donatukas/Volf-TRX/Schematic/Wolf/Addons/AD8307_Add_on_v3/AD8307_Add_on_v3.PcbDoc.htm

Altium Reporting Options

# File in Newer Format

Date | : | 04-Dec-20
Time | : | 18:56:06
Filename | : | C:\Tisho\MyProjects\SDR_Transciever\UA3REO-DDC\Tisho_Files\Boards\AD8307_Add_on_v2\AD8307_Add_on_v2.PcbDoc

Version | Warning
Release 10 | CAUTION - New Custom Grids and Guides were introduced. Be aware that your design might contain Custom Grids and Guides that cannot be read in previous versions.
Release 10 | CAUTION - New Structured Clusters were introduced. Be aware that your design might contain Structured Clusters that cannot be read in previous versions.
Release 10 | CAUTION - New PCB 3D Movie Manager was introduced. Be aware that your design might contain 3D PCB movie that cannot be read in previous versions.
Release 10 update 1 | CAUTION - New Clearance Rule subscopes targeting differential pairs were introduced. Be aware that your design might contain Clearance Rules using those subscopes that cannot be read in previous versions.
Release 10 update 15 | CAUTION - Support of Solder Mask and Paste Mask expansions for Tracks, Arcs, Fills and Regions was introduced. Be aware that your design might contain Solder Mask and Paste Mask expansions for these types of primitives that cannot be read in the version of Altium Designer you are currently using.
Release 12 | CAUTION - Air Gap Width previously controlled by Clearance rule is now controlled by Polygon Connect Style rule's newly introduced Air Gap Width (set to default value). Suggest reviewing each Polygon Connect Style rule's Air Gap Width attribute for correctness.
Release 13 | CAUTION - Silk To Solder Mask Clearance Rules are converted to Silkscreen Over Component Pads Rules.
Release 14 | CAUTION - The Differential Pairs Routing rule added support for control of the width. Be aware that these widths must be manually entered as Width rules in this version.
Release 15 | CAUTION - Support of separate solder masks for top & bottom of pads added.
Release 15.1 | CAUTION - Support Multi-line PCB Text added.
Release 16.0 | CAUTION - Pad/Via hole size tolerance value added.
Release 17.0 | CAUTION - Component parameters added.
Release 17.0 | CAUTION - Support of backdrilling
Release 17.1 | CAUTION - Support of waived violations
Release 17.1 | CAUTION - Support of object specific keepouts

This file was generated by a later version of the software
