donatukas/Volf-TRX/Schematic/Wolf/Altium_Designer/RF-UNIT-QRP_20W/!AdditionalInfo/Heatsink_QRP++.pptx

Used 2 heatsinks:
SK 81/100/SA (https://www.reichelt.de/kuehlkoerper-100-mm-alu-2-2-k-w-sk-81-100-sa-p227984.html?trstct=pos_0&nbc=1) – 100 x 100 mm, Alu, 2,2 K/W
SK 81/75/SA (https://www.reichelt.de/kuehlkoerper-75-mm-alu-2-5-k-w-sk-81-75-sa-p227987.html?&trstct=pos_0&nbc=1) – 100 x 75 mm, Alu, 2,5 K/W

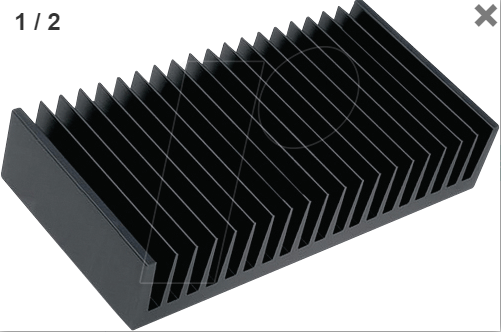
[picture p3: figure]
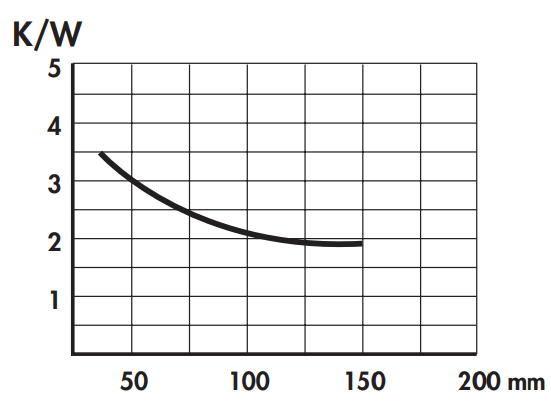
[picture p4: figure]

SK 81/100/SA drill dimensions

100

100

7x M3

9,5

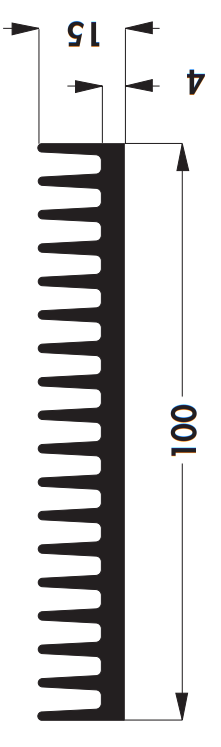
[picture p5: figure]

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
26,5

Dimensions 1

Dimensions 2

## Slide 2

SK 81/75/SA drill dimensions

75

9,5

10

10

100

9,5

## Slide 3

Bottom cover
(Dimensions 1)

11,1

17,6

17,6

103,2

11,1

97,6

117,6

190,2

## Slide 4

Bottom cover
(Dimensions 2)

115

103,2

9,5

62

190,2

## Slide 5

Copper block 1 (TIM)
- Size 39x30x10

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
2 x Ф 3,5

15,4

35

6,1

12

7

## Slide 6

Copper block 1 (TIM)
- Size 39x20x8

8

39

15,4

2 x Ф 3,5

35

6,1

20

12

7
