donatukas/Volf-TRX/Schematic/Wolf-2/Altium_Designer/W2-FRONT/FRONT LABEL.png

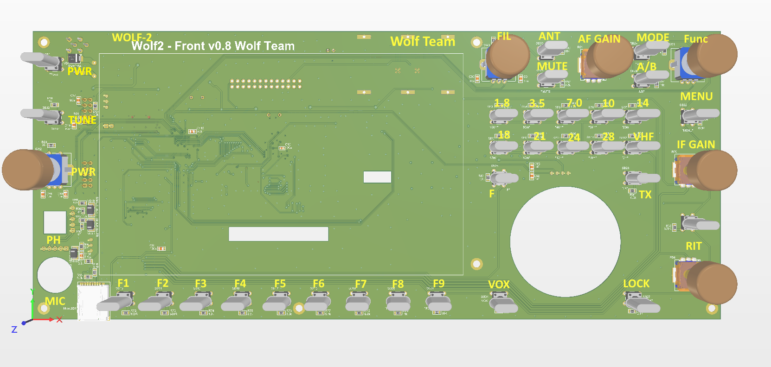
Schematic/Wolf-2/Altium_Designer/W2-FRONT/FRONT LABEL.png
