donatukas/Volf-TRX/Schematic/Wolf-2/Altium_Designer/W2-HF_AMP/HFAmp_DN_v01.png

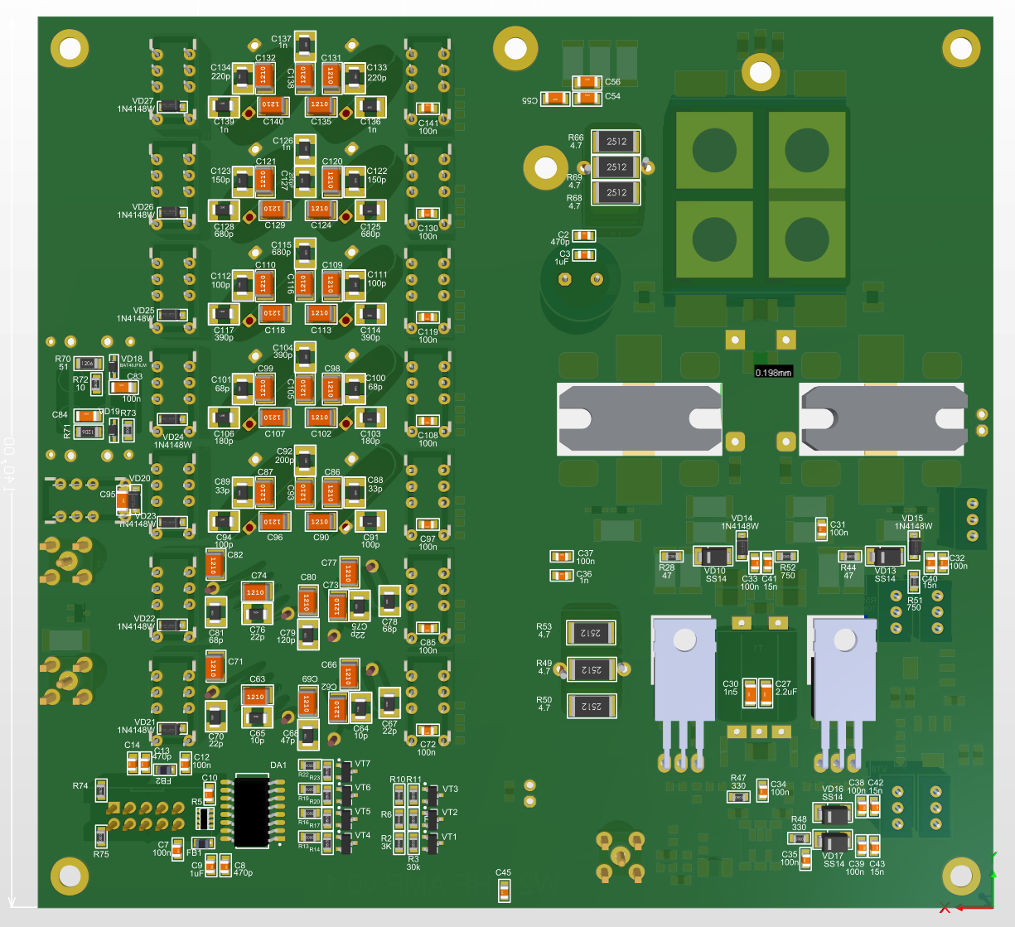
Schematic/Wolf-2/Altium_Designer/W2-HF_AMP/HFAmp_DN_v01.png
