donatukas/Volf-TRX/Schematic/Wolf-2/Altium_Designer/W2-Tuner_7x7/Tuner_DN_v01.png

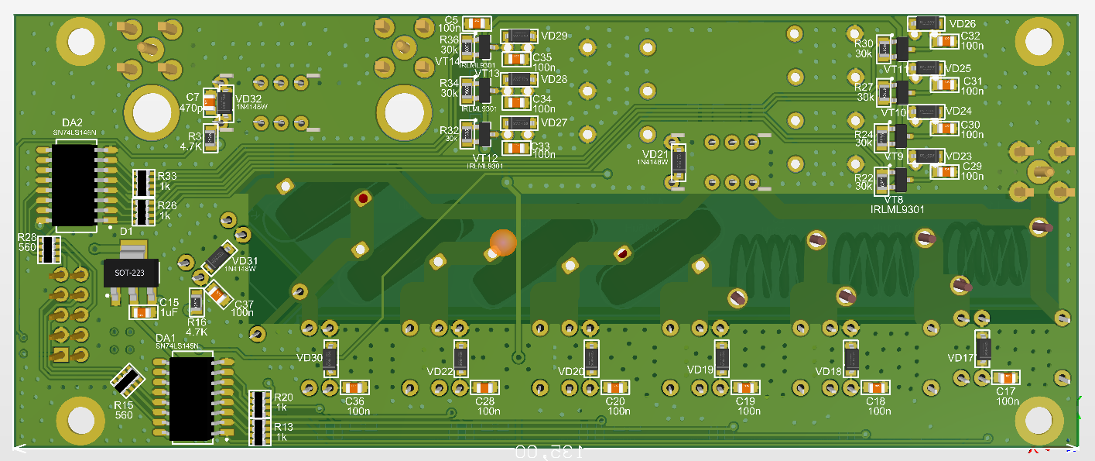
Schematic/Wolf-2/Altium_Designer/W2-Tuner_7x7/Tuner_DN_v01.png
