donatukas/Volf-TRX/Schematic/Wolf-X1/Addons/20mm_Sec_Encoder.stl

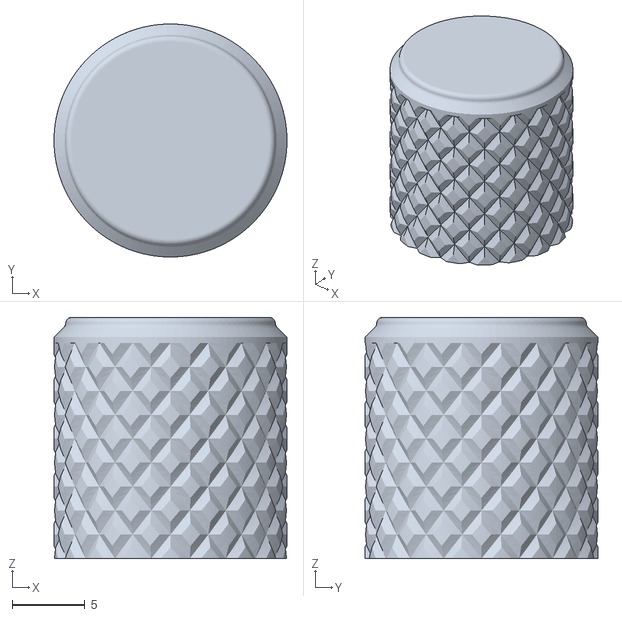
[picture p29: CAD file, 2024-02-05]
Schematic/Wolf-X1/Addons/20mm_Sec_Encoder.stl
16.0 x 16.0 x 16.6
