donatukas/Volf-TRX/Schematic/Wolf/CASE/3'2/3DPrinter/RotaryPotencimetr.SLDPRT

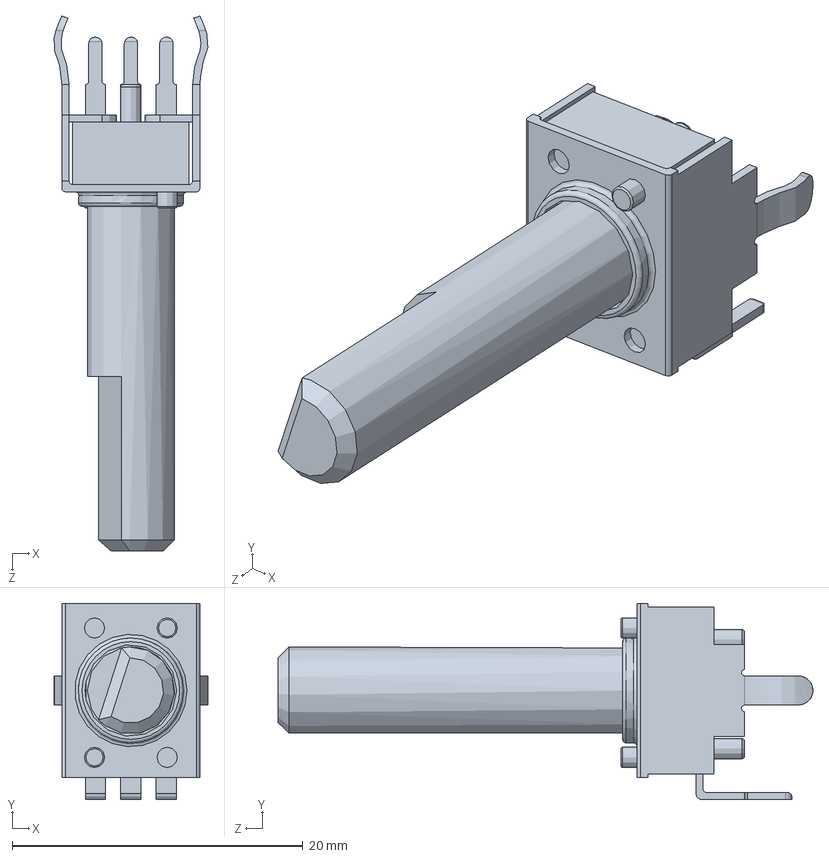
[picture p30: CAD file, 2024-02-05]
Schematic/Wolf/CASE/3'2/3DPrinter/RotaryPotencimetr.SLDPRT
10.6 x 13.5 x 36.8 mm
