donatukas/Volf-TRX/Schematic/Wolf/CASE/VFO/ExtEncoder.stl

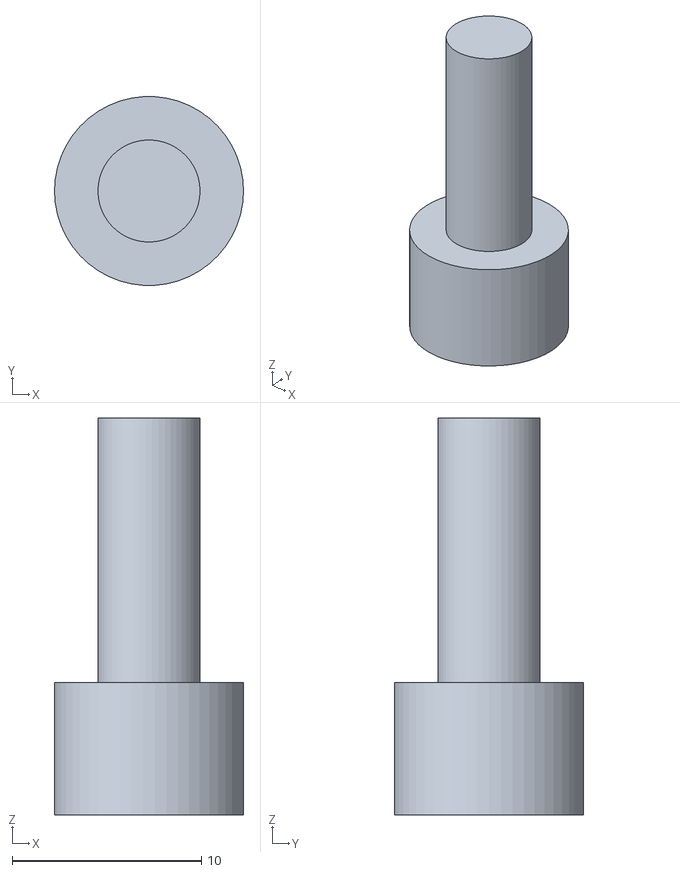
[picture p32: CAD file, 2024-02-05]
Schematic/Wolf/CASE/VFO/ExtEncoder.stl
10.0 x 9.98 x 21.0
