donatukas/Volf-TRX/Schematic/Wolf/CASE/3'2/3DPrinter/case/encoder_mount_front.SLDPRT

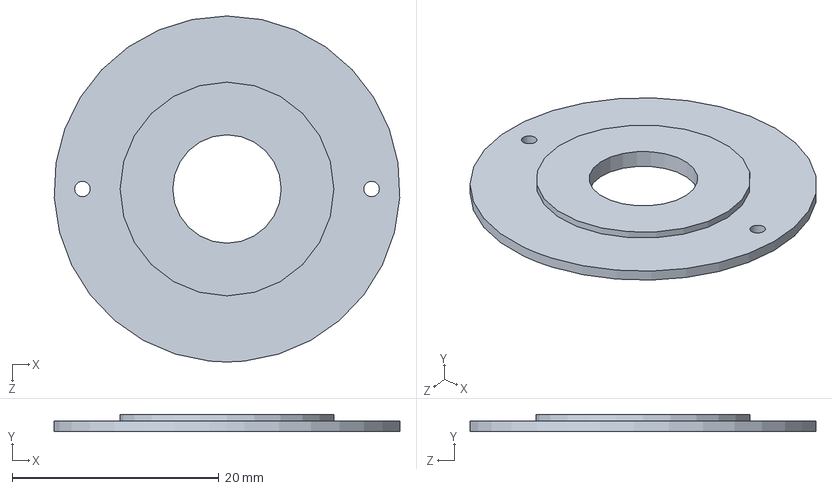
[picture p33: CAD file, 2024-02-05]
Schematic/Wolf/CASE/3'2/3DPrinter/case/encoder_mount_front.SLDPRT
33.5 x 1.65 x 33.5 mm
