donatukas/Volf-TRX/Schematic/Wolf/CASE/3'2/3DPrinter/Rotary Encoder.SLDPRT

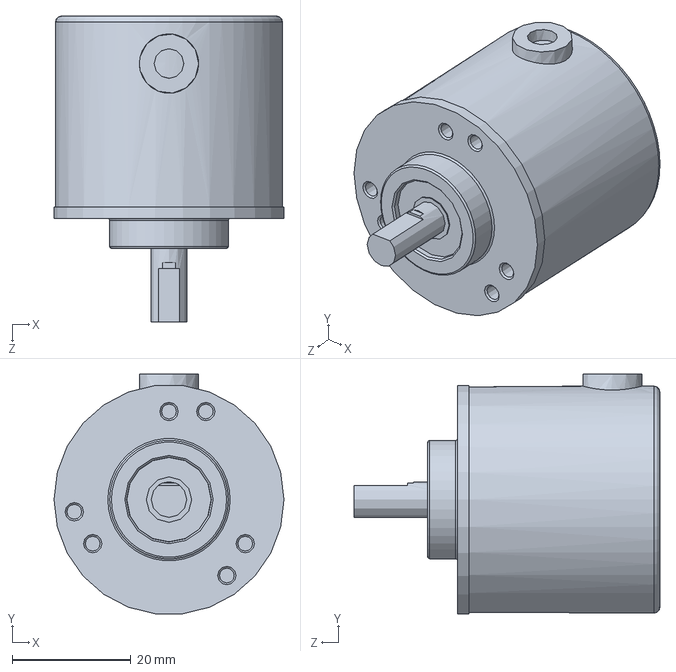
[picture p34: CAD file, 2024-02-05]
Schematic/Wolf/CASE/3'2/3DPrinter/Rotary Encoder.SLDPRT
38.7 x 40.3 x 51.5 mm
