donatukas/Volf-TRX/Schematic/Wolf/CASE/3'2/3DPrinter/case/shuttle_knob_cap.SLDPRT

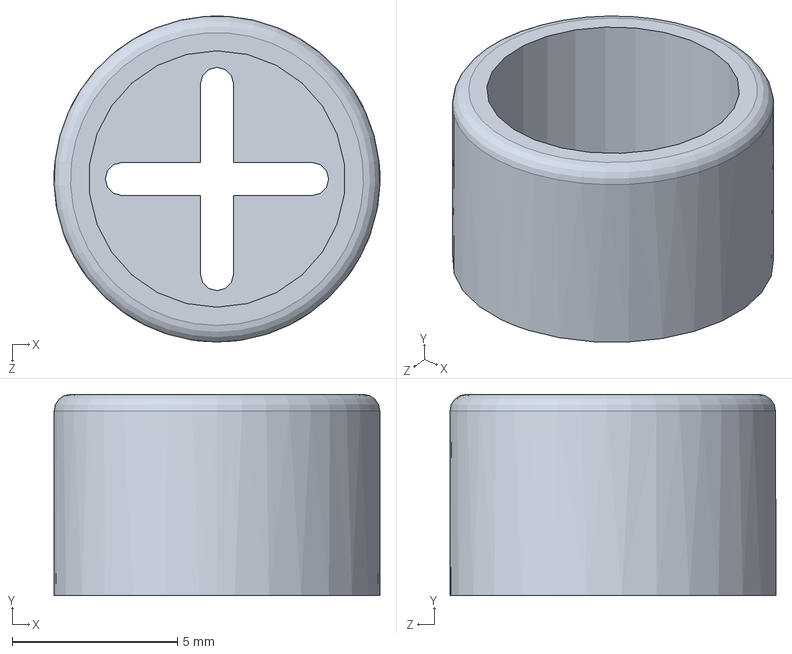
[picture p36: CAD file, 2024-02-05]
Schematic/Wolf/CASE/3'2/3DPrinter/case/shuttle_knob_cap.SLDPRT
9.84 x 6.08 x 9.85 mm
