donatukas/Volf-TRX/Schematic/Wolf/CASE/7/Panel/кнопка_power_7.stl

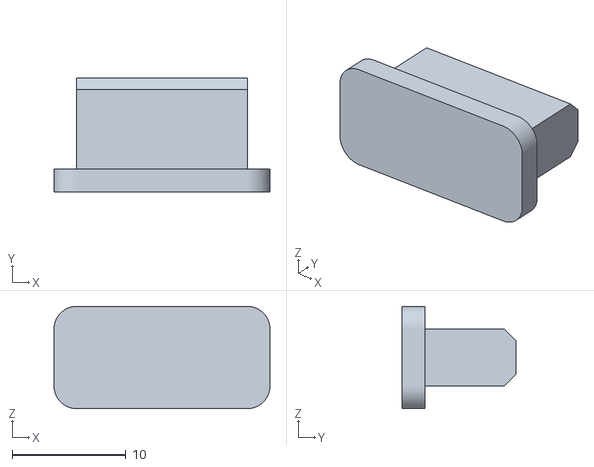
[picture p41: CAD file, 2024-02-05]
Schematic/Wolf/CASE/7/Panel/кнопка_power_7.stl
19.0 x 10.0 x 9.00
