donatukas/Volf-TRX/Schematic/Wolf/CASE/7/Panel/кнопка_низ_7_новая.stl

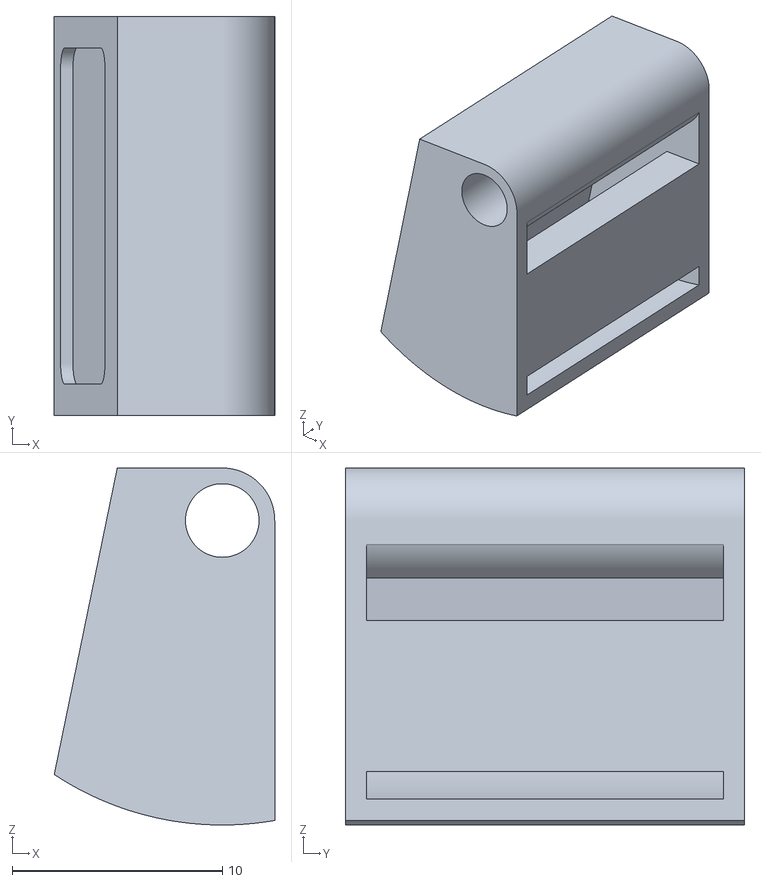
[picture p42: CAD file, 2024-02-05]
Schematic/Wolf/CASE/7/Panel/кнопка_низ_7_новая.stl
10.5 x 19.0 x 17.0
