donatukas/Volf-TRX/Schematic/Wolf/CASE/3'2/3DPrinter/case/case_back.SLDPRT

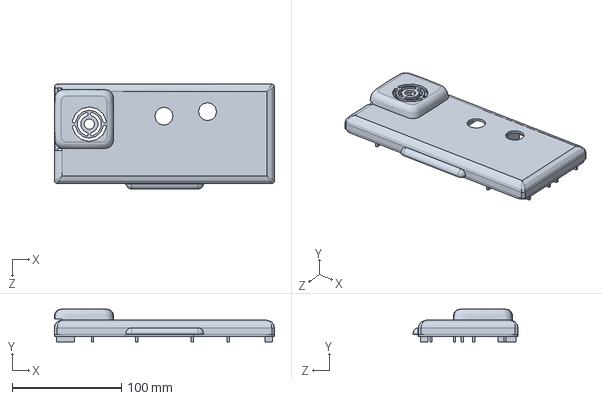
[picture p44: CAD file, 2024-02-05]
Schematic/Wolf/CASE/3'2/3DPrinter/case/case_back.SLDPRT
201.0 x 29.7 x 95.9 mm
