donatukas/Volf-TRX/Schematic/Wolf/CASE/7/Panel/кнопка верх_7.stl

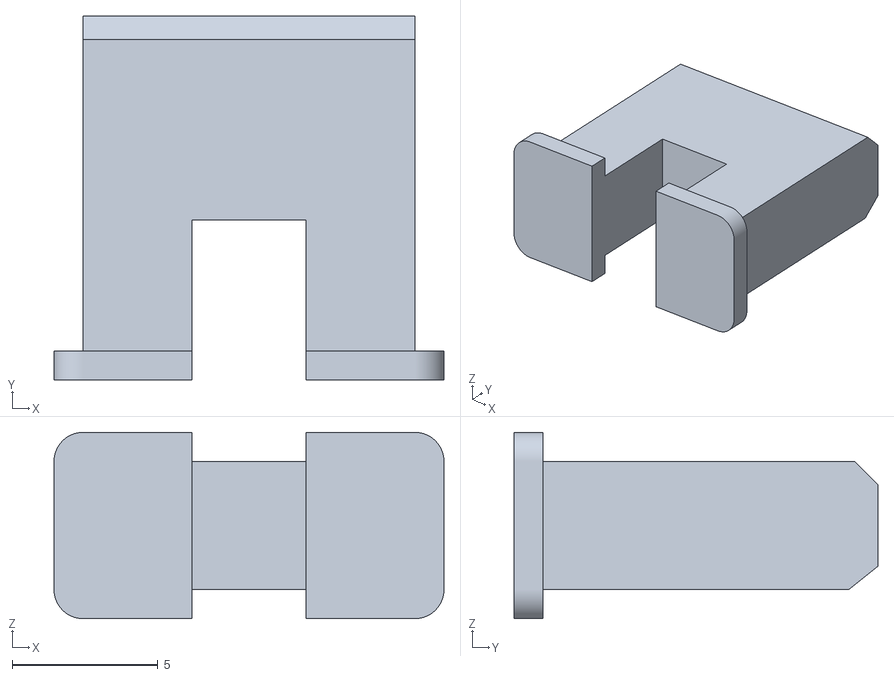
[picture p46: CAD file, 2024-02-05]
Schematic/Wolf/CASE/7/Panel/кнопка верх_7.stl
13.4 x 12.5 x 6.40
