donatukas/Volf-TRX/Schematic/Wolf/CASE/3'2/3DPrinter/case/case_connector_cap.SLDPRT

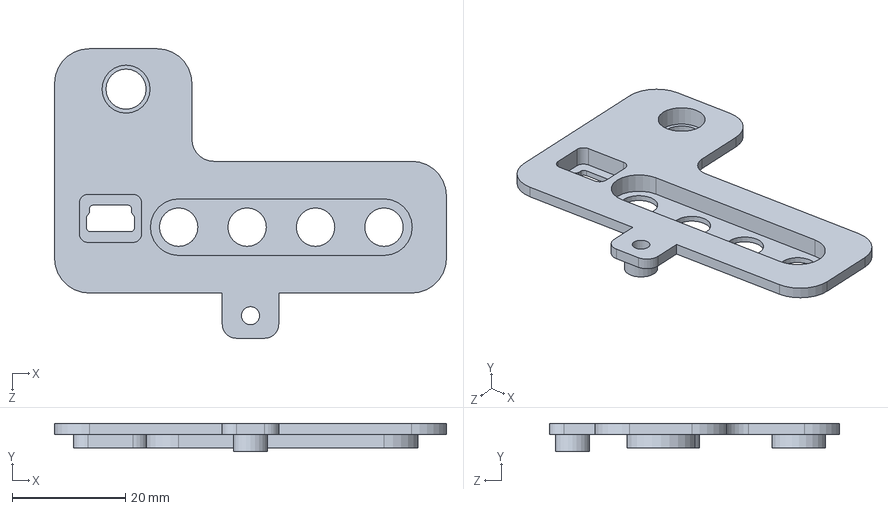
[picture p47: CAD file, 2024-02-05]
Schematic/Wolf/CASE/3'2/3DPrinter/case/case_connector_cap.SLDPRT
69.3 x 5.00 x 51.2 mm
