donatukas/Volf-TRX/Schematic/Wolf/CASE/7/Panel/кнопка_низ_7.stl

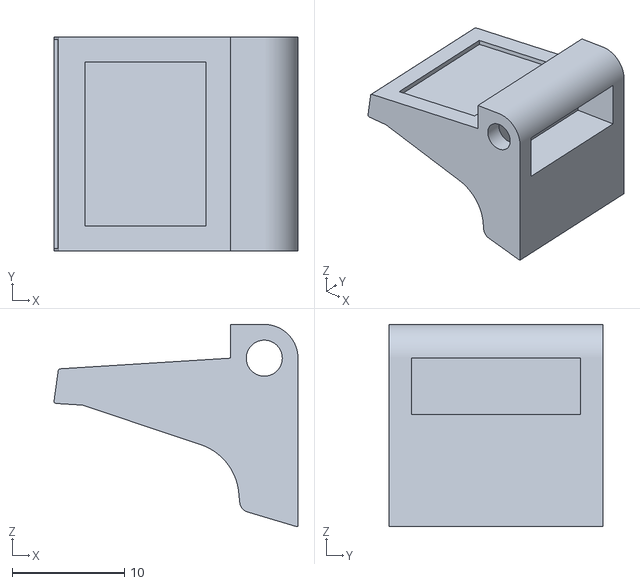
[picture p48: CAD file, 2024-02-05]
Schematic/Wolf/CASE/7/Panel/кнопка_низ_7.stl
21.7 x 19.0 x 18.0
