donatukas/Volf-TRX/Schematic/Wolf/CASE/3'2/3DPrinter/GX12-6P v2.step

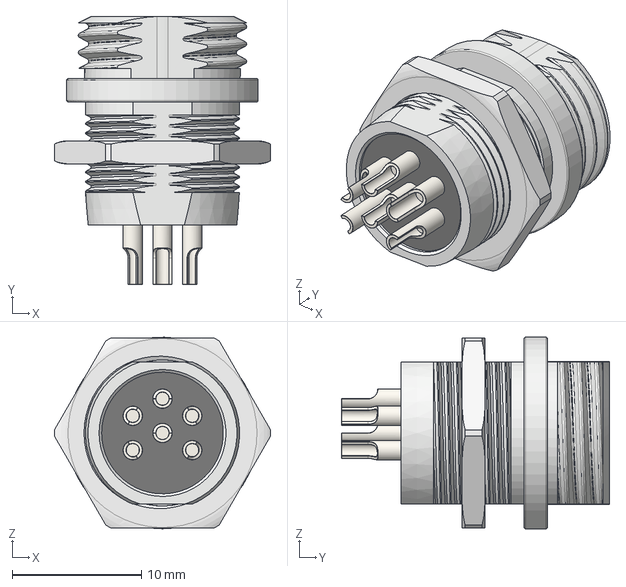
[picture p50: CAD file, 2024-02-05]
Schematic/Wolf/CASE/3'2/3DPrinter/GX12-6P v2.step
16.7 x 20.7 x 14.8 mm
