donatukas/Volf-TRX/Schematic/Wolf/CASE/3'2/3DPrinter/case/case_speaker_cap.SLDPRT

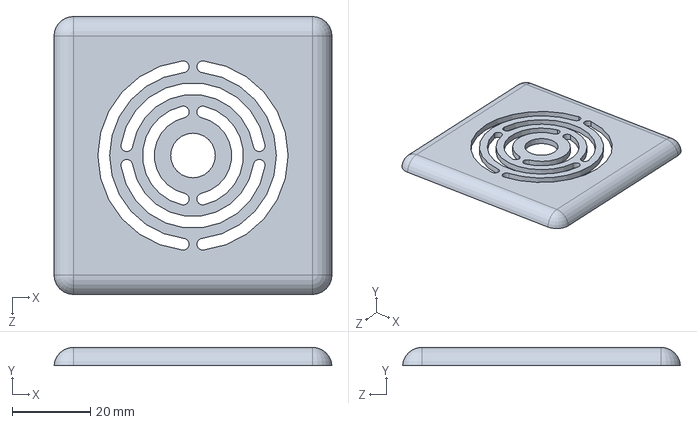
[picture p51: CAD file, 2024-02-05]
Schematic/Wolf/CASE/3'2/3DPrinter/case/case_speaker_cap.SLDPRT
71.0 x 4.70 x 71.0 mm
