donatukas/Volf-TRX/Schematic/Wolf/CASE/3'2/3DPrinter/encoder_knob.SLDPRT

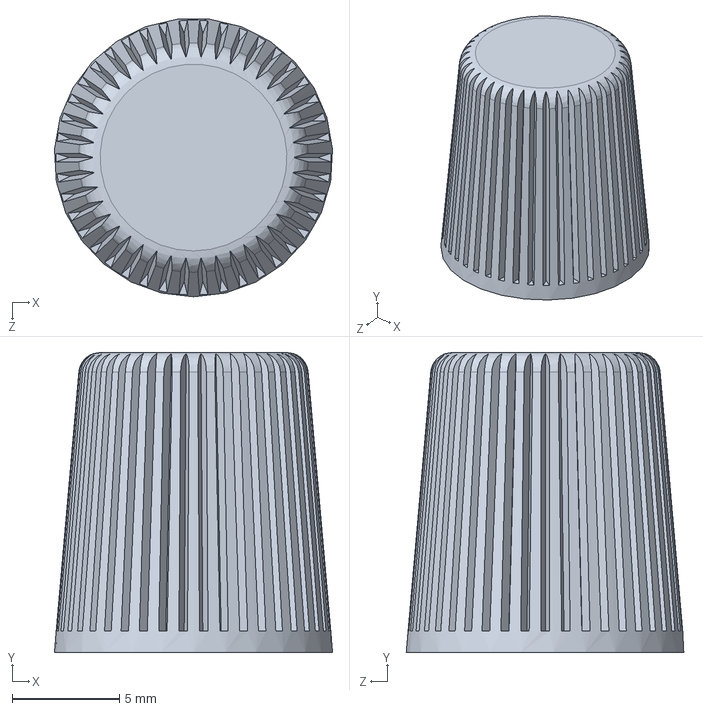
[picture p58: CAD file, 2024-02-05]
Schematic/Wolf/CASE/3'2/3DPrinter/encoder_knob.SLDPRT
13.0 x 14.0 x 13.0 mm
