donatukas/Volf-TRX/Schematic/Wolf/CASE/3'2/3DPrinter/pl-259_jack.stp

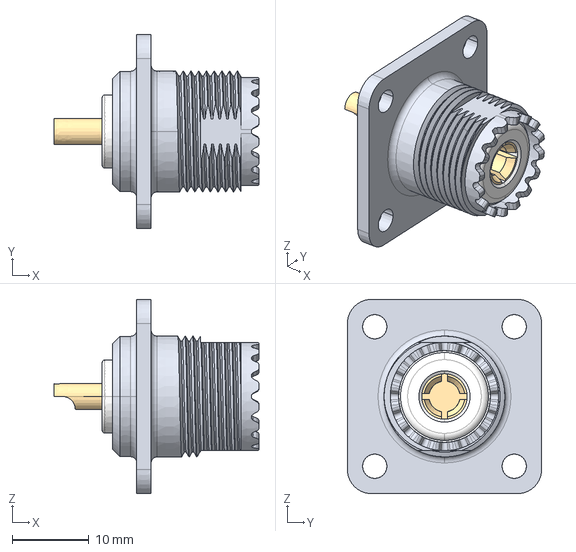
[picture p59: CAD file, 2024-02-05]
Schematic/Wolf/CASE/3'2/3DPrinter/pl-259_jack.stp
26.8 x 25.4 x 25.4 mm
