donatukas/Volf-TRX/Schematic/Wolf/CASE/3'2/3DPrinter/Mini USB.SLDPRT

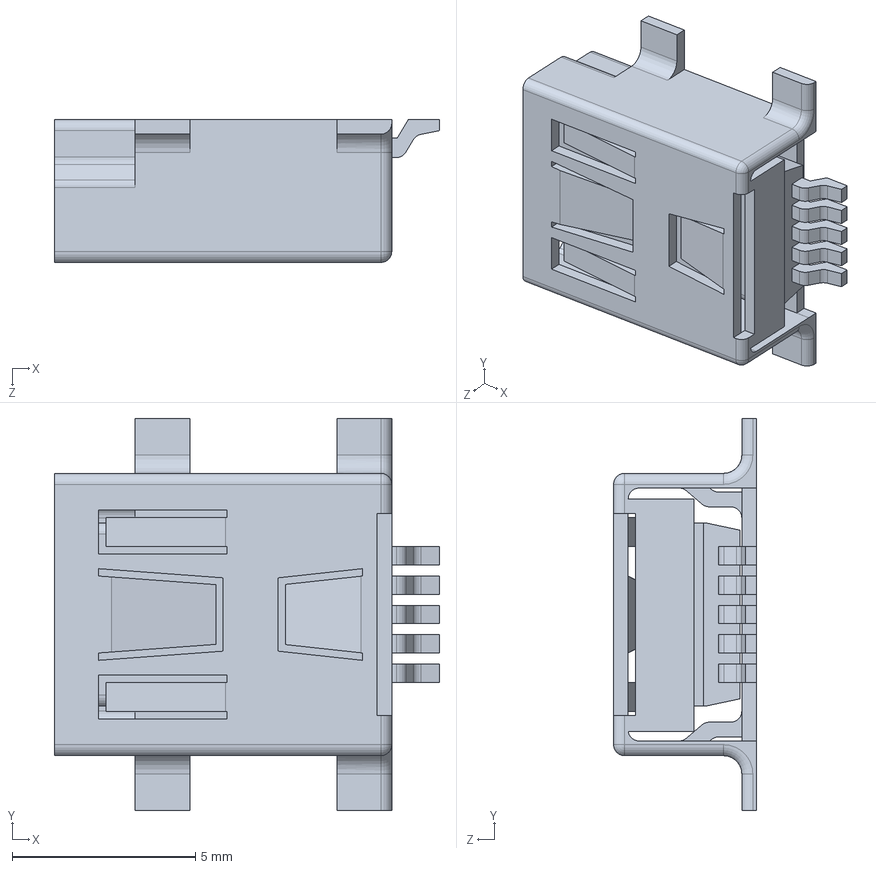
[picture p60: CAD file, 2024-02-05]
Schematic/Wolf/CASE/3'2/3DPrinter/Mini USB.SLDPRT
10.5 x 10.7 x 3.90 mm
