donatukas/Volf-TRX/Schematic/Wolf/CASE/3'2/3DPrinter/Encoder_Axis.SLDPRT

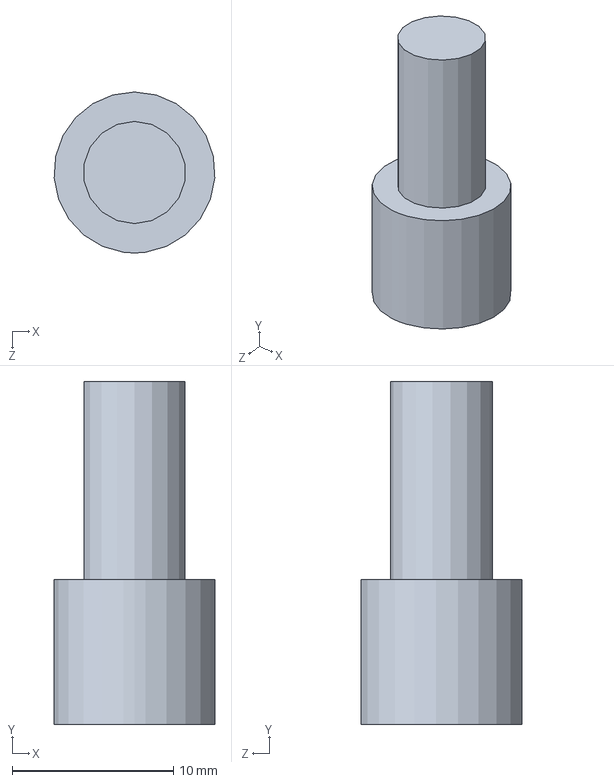
[picture p62: CAD file, 2024-02-05]
Schematic/Wolf/CASE/3'2/3DPrinter/Encoder_Axis.SLDPRT
9.98 x 21.3 x 10.0 mm
