donatukas/Volf-TRX/Schematic/Wolf/Scheme/SCHEMATIC-MOTHERBOARD-rev34.pdf

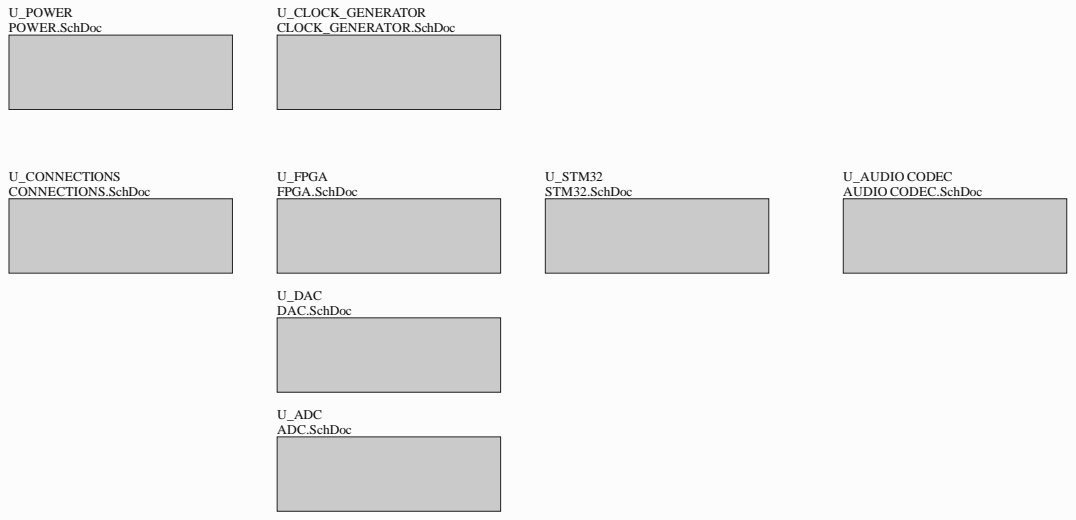
[picture p171: page 1]

C:\Dropbox\Develop\Projects\WOLF\Schematic\Wolf\Altium_Designer\MOTHERBOARD\MOTHERBOARD.SCHDOC

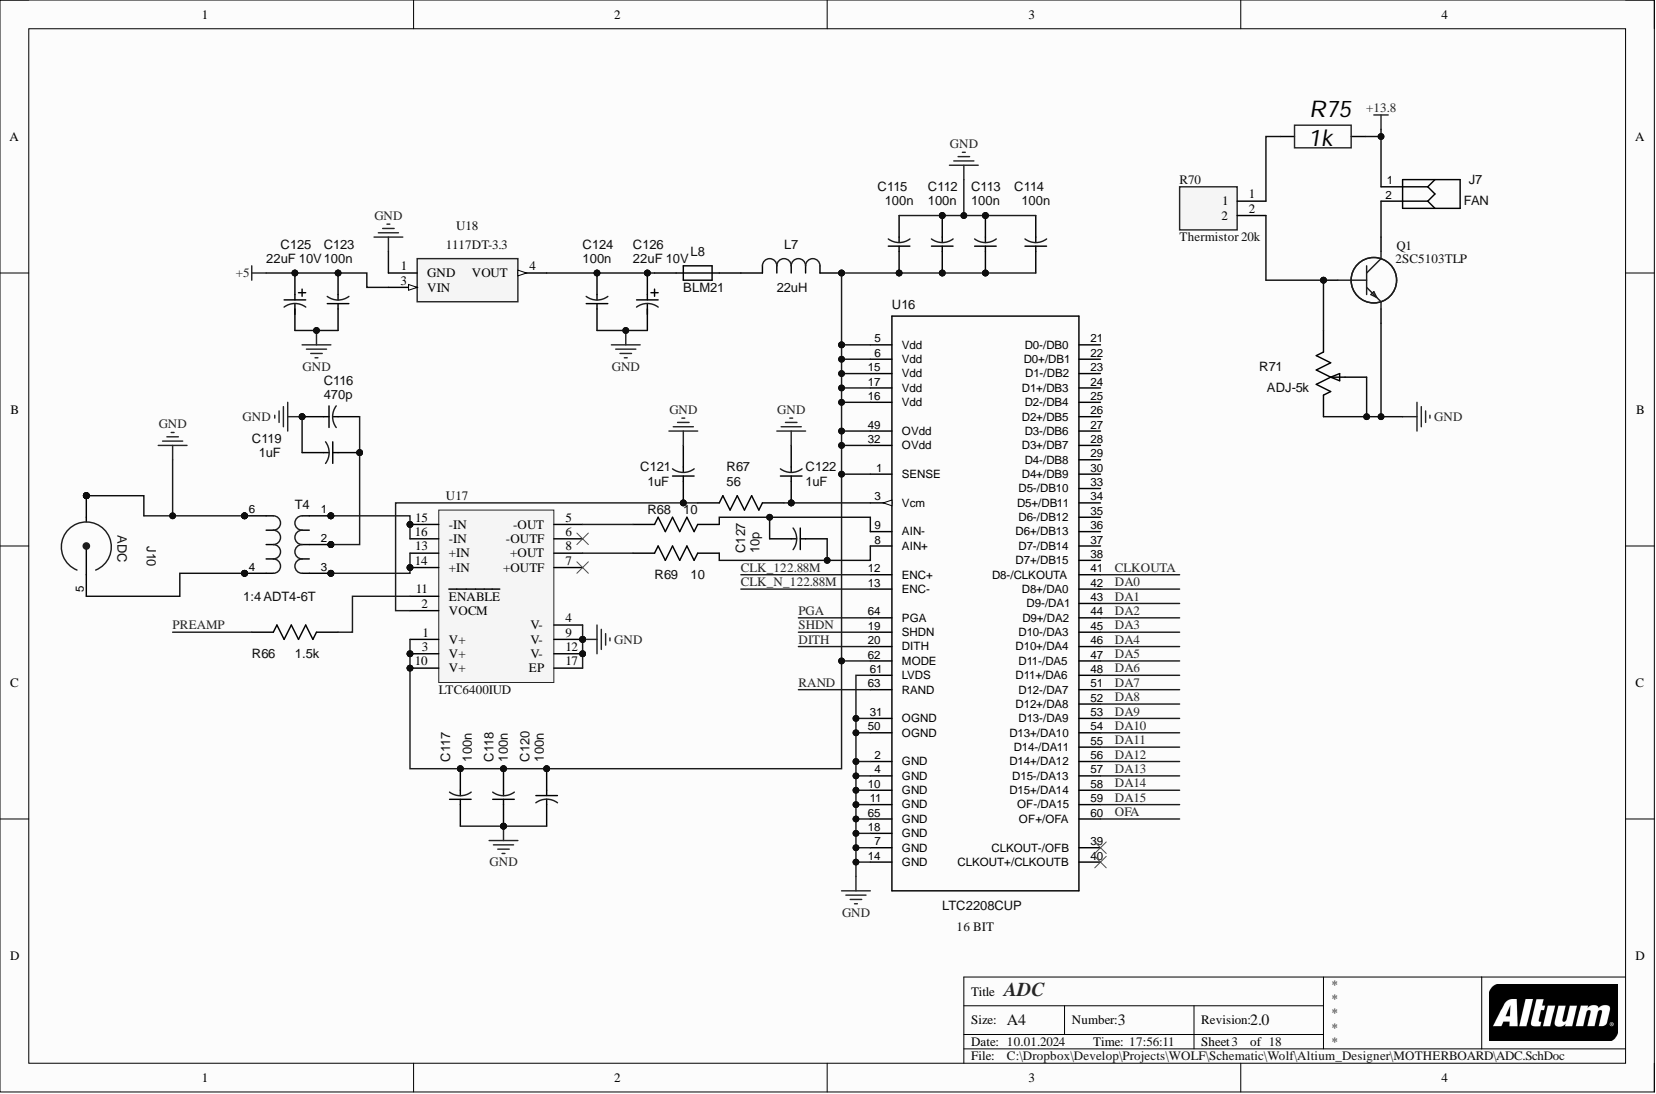
[picture p172: page 2]

V-V + V + V-V + E P | 4

3 | 1 2
1 0 | 1 7

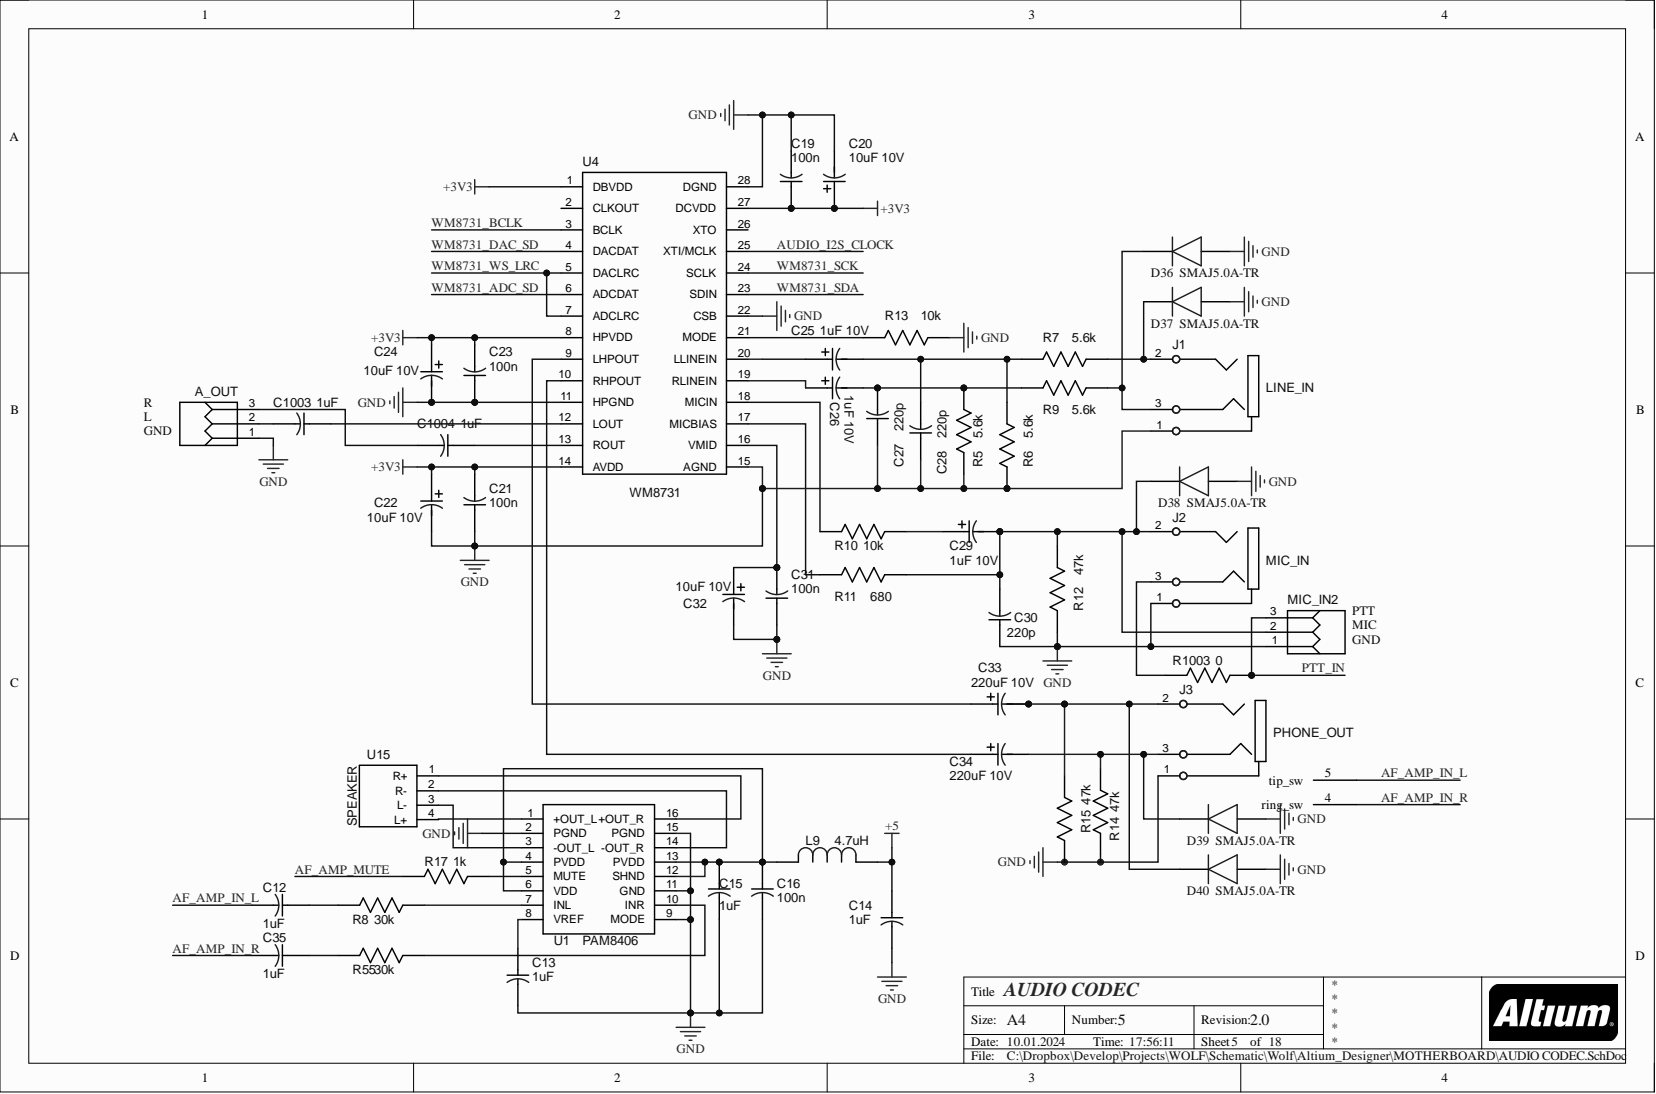
[picture p173: page 3]

ADCLRC 7

LHPOUT 9

RHPOUT 10

HPGND 11 MICBIAS VMID AGND | 15 AVDD 14

LOUT 12 | 17

ROUT 13 | 16

MODE PGND -OUT_R | 9 VREF 8 15

INL 7 VDD 6 MUTE 5 PVDD 4 -OUT_L 3 PGND 2 +OUT_L 1 | 14

PVDD SHND | 13 12

C:\Dropbox\Develop\Projects\WOLF\Schematic\Wolf\Altium_Designer\MOTHERBOARD\AUDIO CODEC.SchDoc

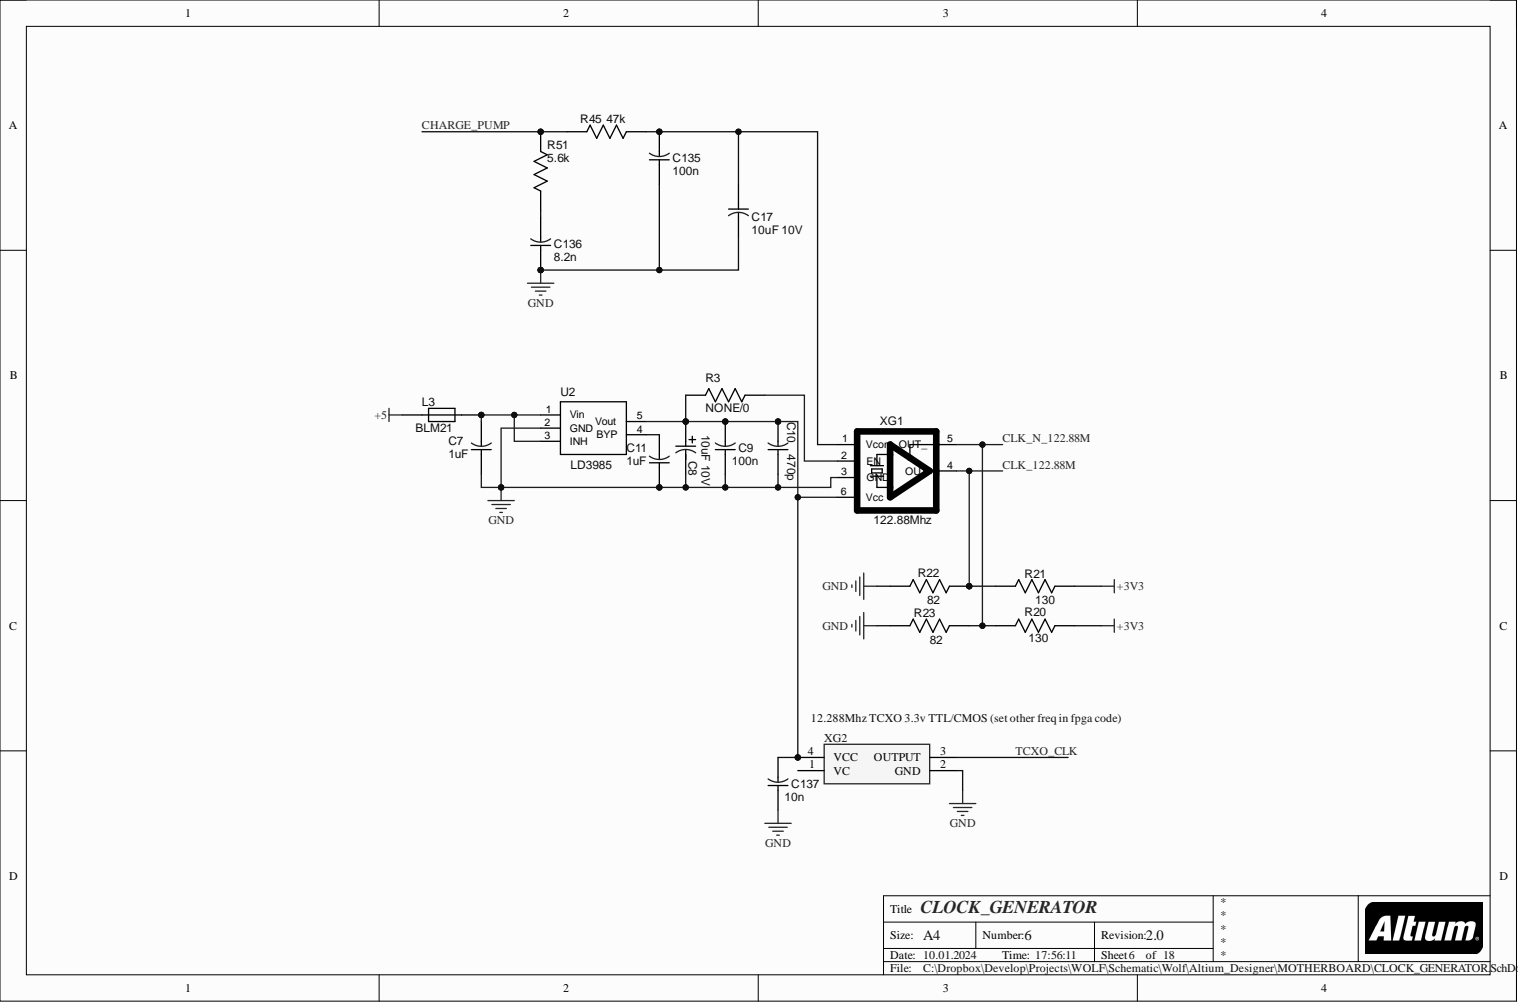
[picture p174: page 4]

Vcont 1
GND 3 EN 2

12.288Mhz TCXO 3.3v TTL/CMOS (set other freq in fpga code)

C:\Dropbox\Develop\Projects\WOLF\Schematic\Wolf\Altium_Designer\MOTHERBOARD\CLOCK_GENERATOR.SchDoc

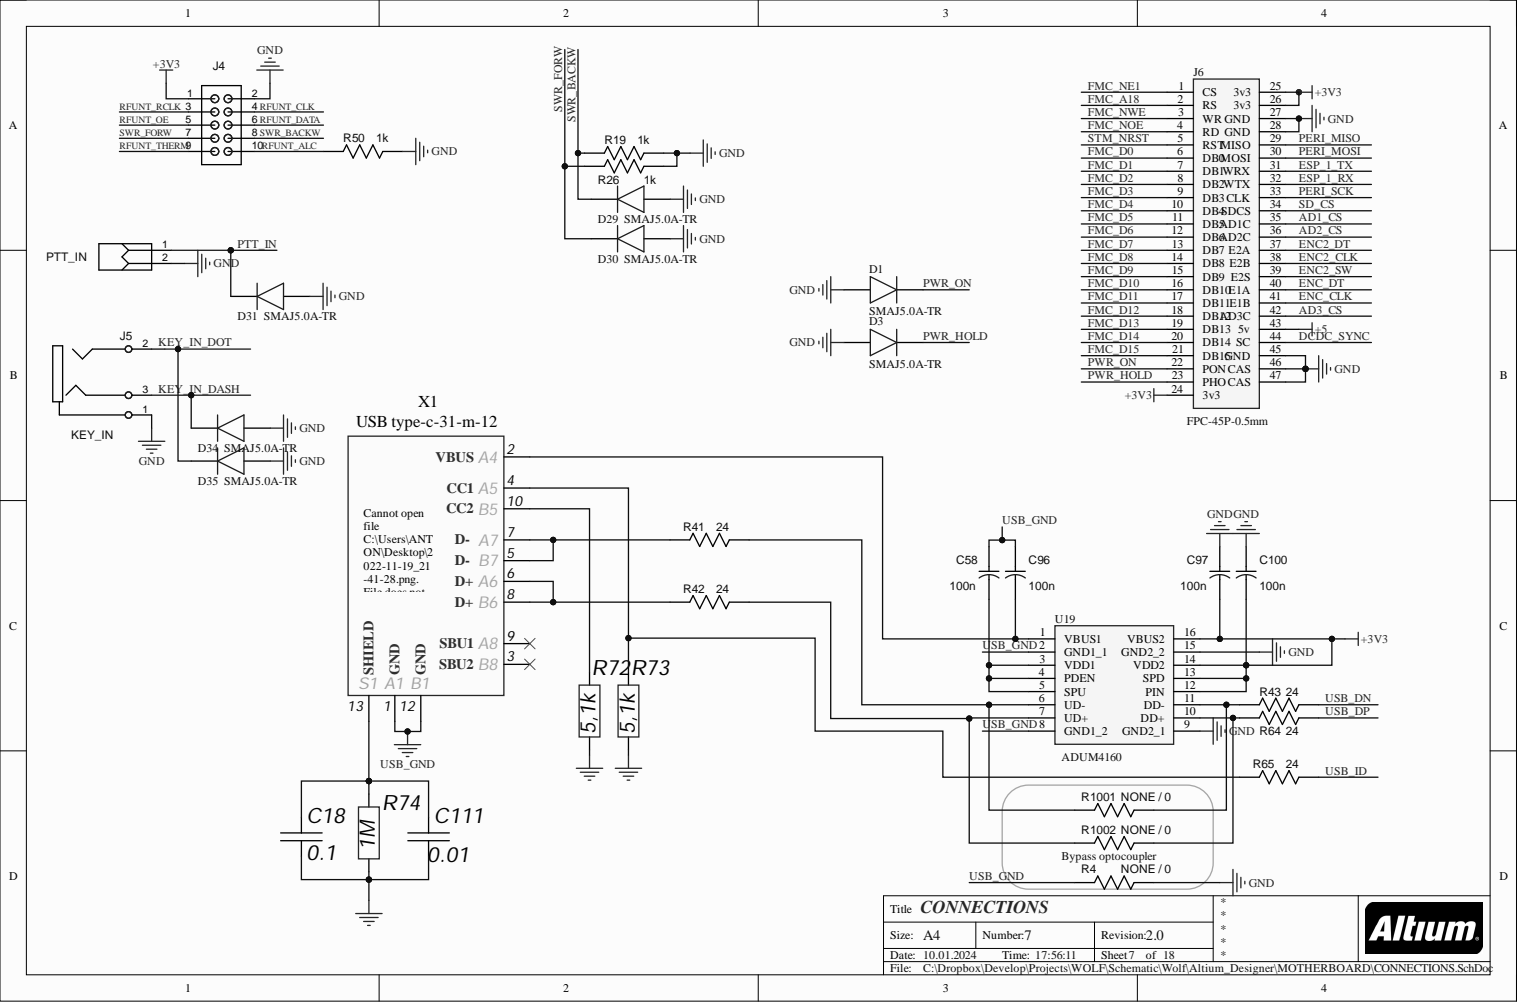
[picture p175: page 5]

C:\Dropbox\Develop\Projects\WOLF\Schematic\Wolf\Altium_Designer\MOTHERBOARD\CONNECTIONS.SchDoc

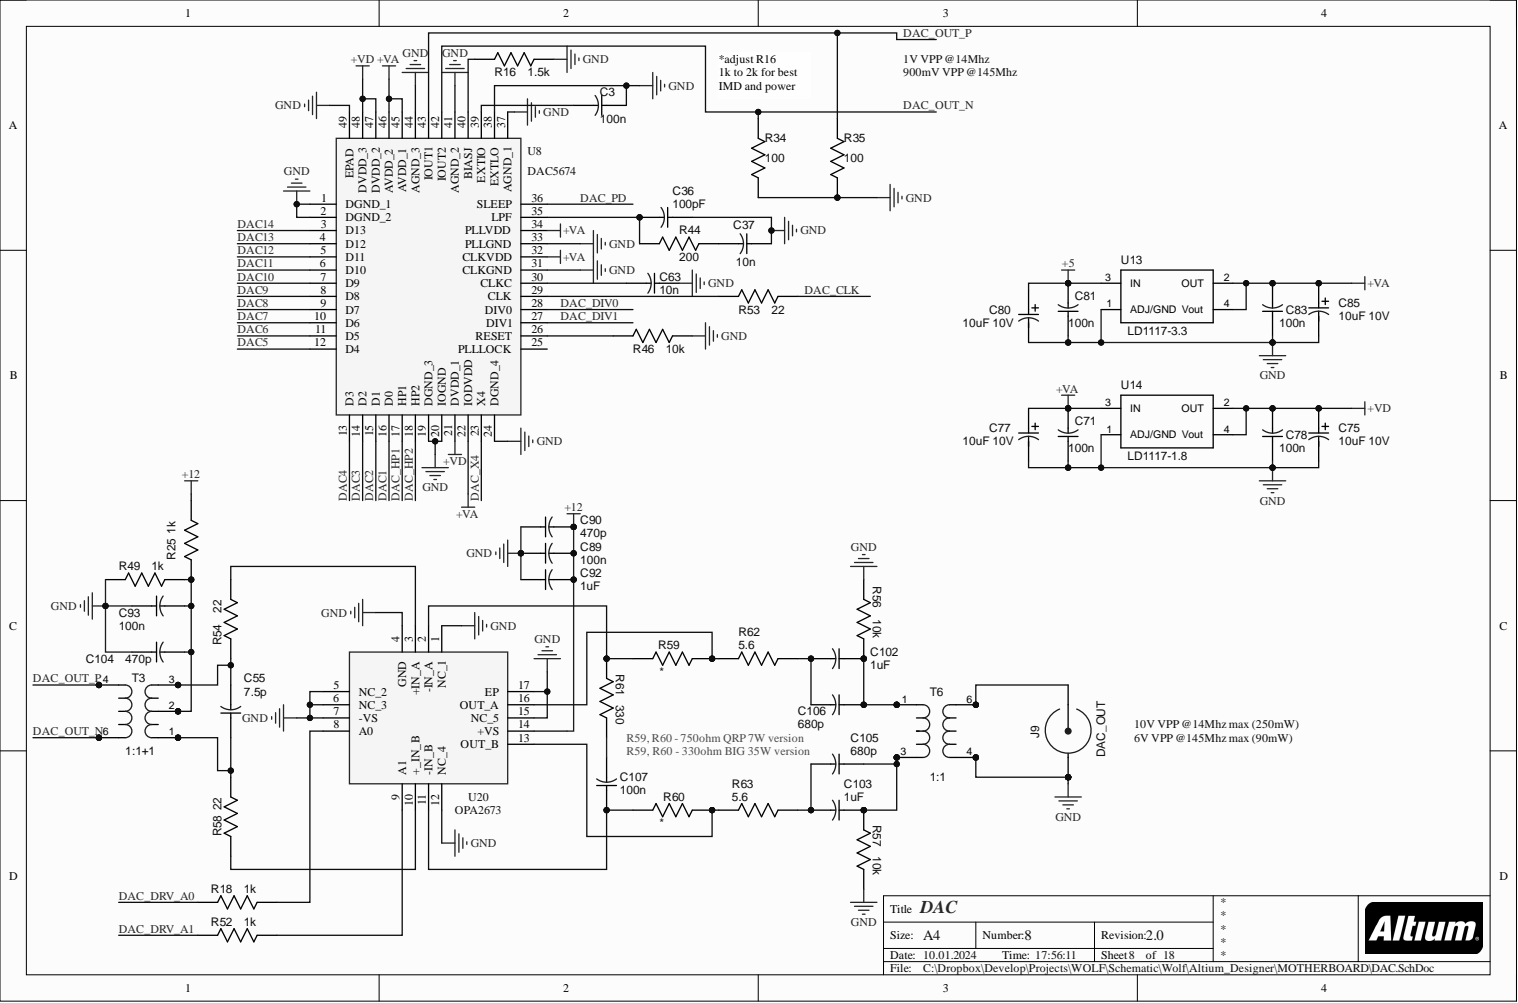
[picture p176: page 6]

C:\Dropbox\Develop\Projects\WOLF\Schematic\Wolf\Altium_Designer\MOTHERBOARD\DAC.SchDoc

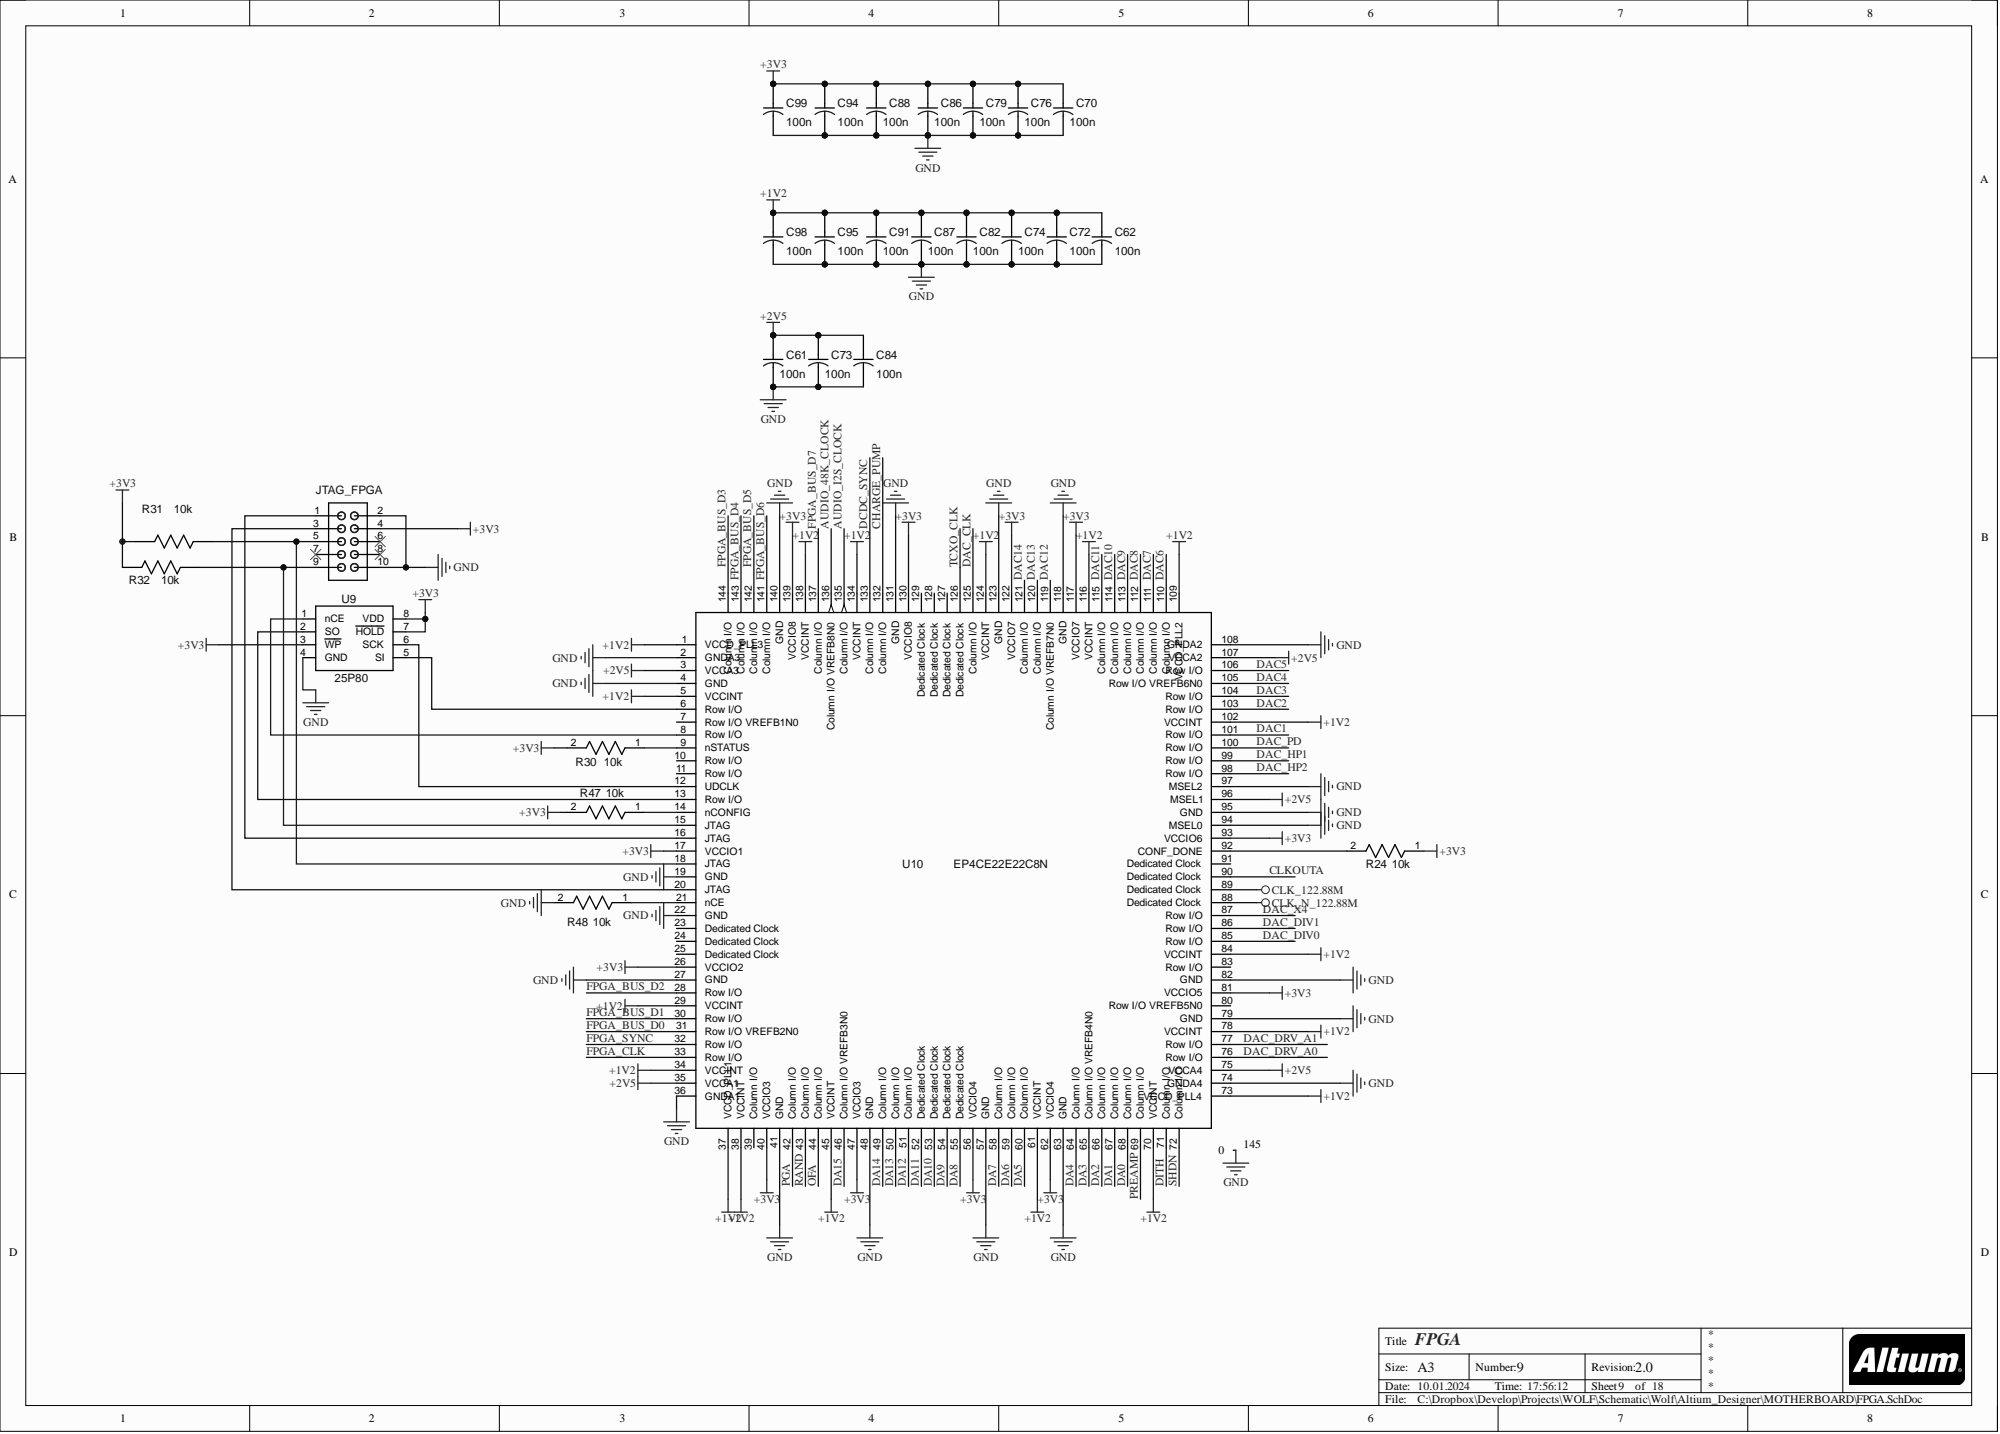
[picture p177: page 7]

Column I/O 72 Column I/O 71 VCCINT 70 Column I/O 69 Column I/O 68 Column I/O 67 Column I/O 66 Column I/O VREFB4N0 65 Column I/O 64 GND 63 VCCIO4 62 VCCINT 61 Column I/O 60 Column I/O 59 Column I/O 58 GND 57 VCCIO4 56 Dedicated Clock 55 Dedicated Clock 54 Dedicated Clock 53 Dedicated Clock 52 Column I/O 51 Column I/O 50 Column I/O 49 GND 48 VCCIO3 47 Column I/O VREFB3N0 46 VCCINT 45 Column I/O 44 Column I/O 43 Column I/O 42 GND 41 VCCIO3 40 Column I/O 39 VCCINT 38 VCCD_PLL1 37

C:\Dropbox\Develop\Projects\WOLF\Schematic\Wolf\Altium_Designer\MOTHERBOARD\FPGA.SchDoc

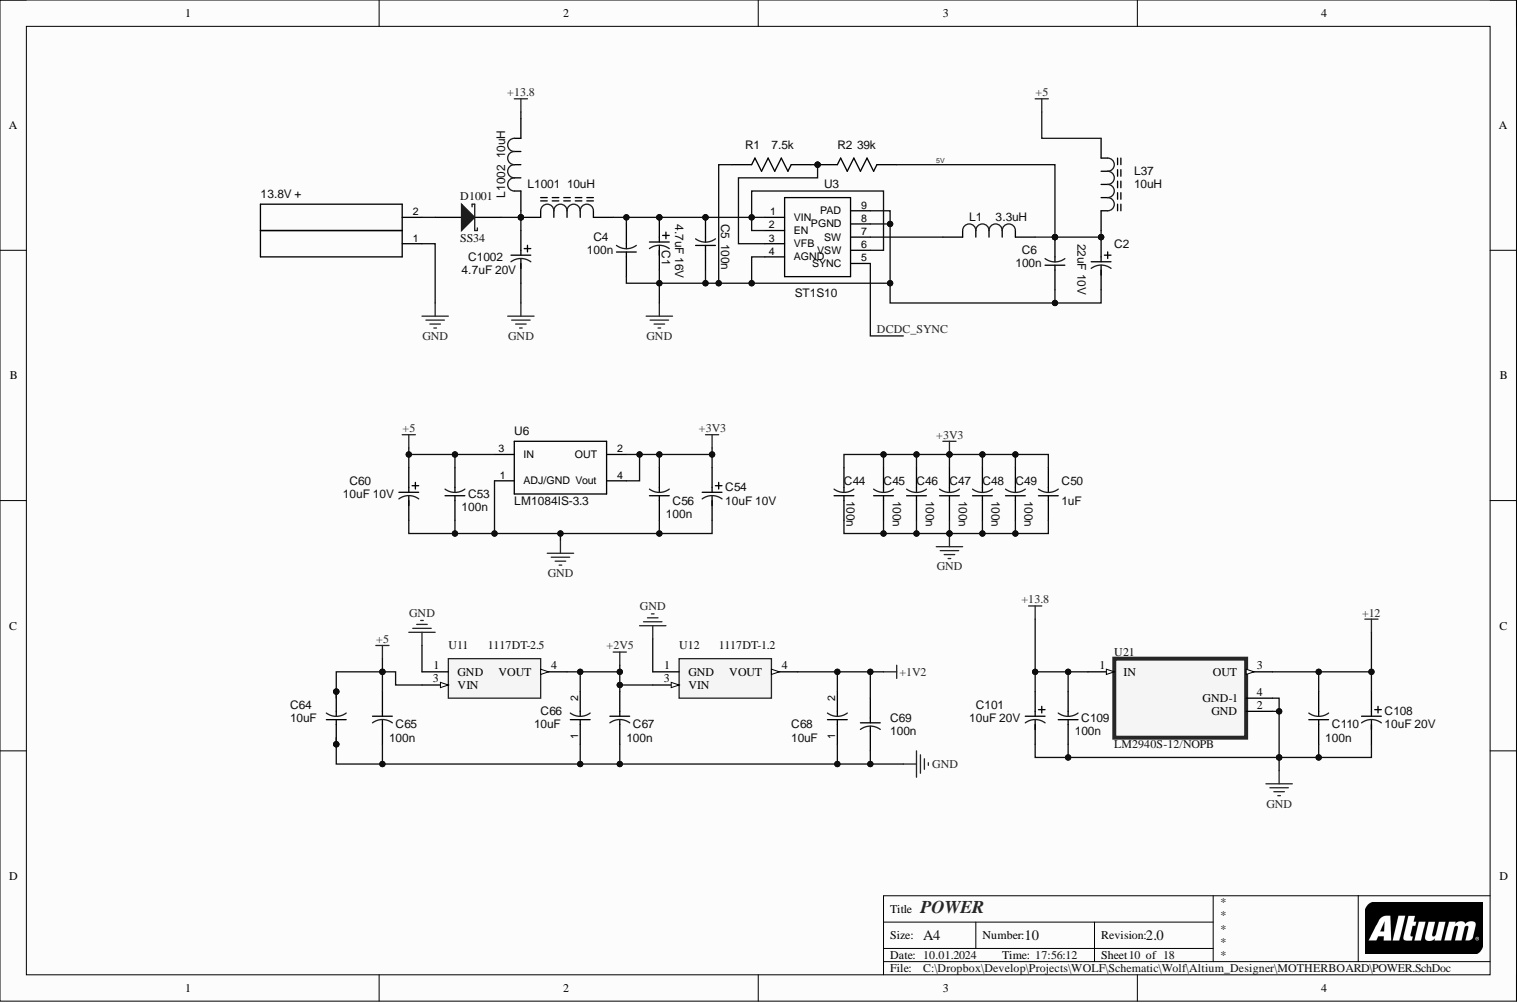
[picture p178: page 8]

C:\Dropbox\Develop\Projects\WOLF\Schematic\Wolf\Altium_Designer\MOTHERBOARD\POWER.SchDoc

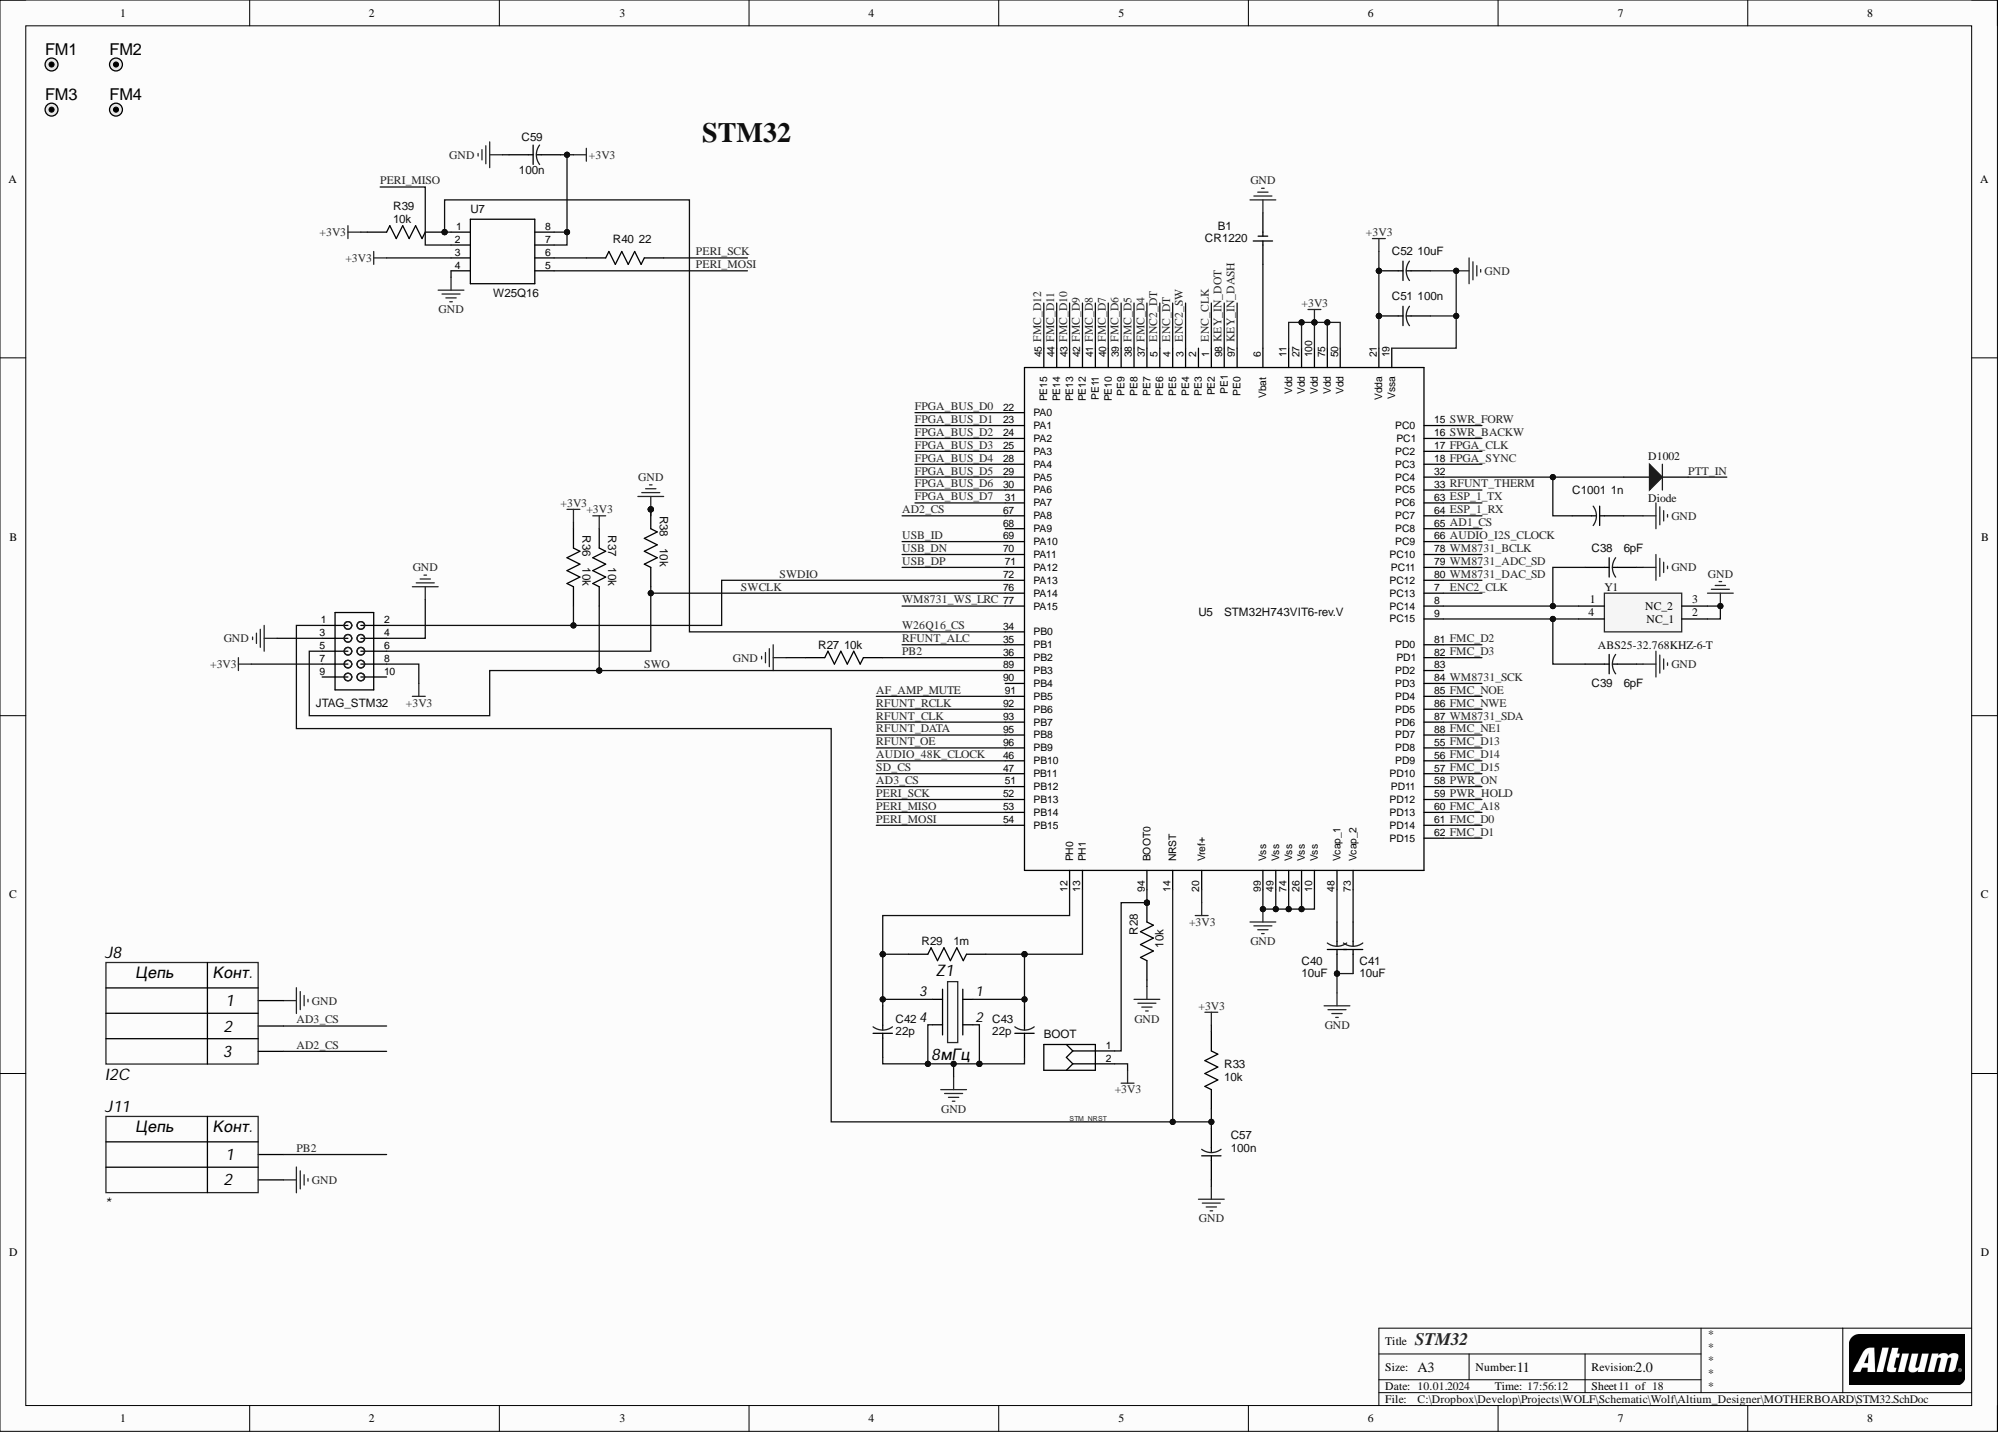
[picture p179: page 9]

Цепь | Конт.

C:\Dropbox\Develop\Projects\WOLF\Schematic\Wolf\Altium_Designer\MOTHERBOARD\STM32.SchDoc
