donatukas/Volf-TRX/Schematic/Wolf/Scheme/SCHEMATIC-RF-UNIT-QRP-rev22.pdf

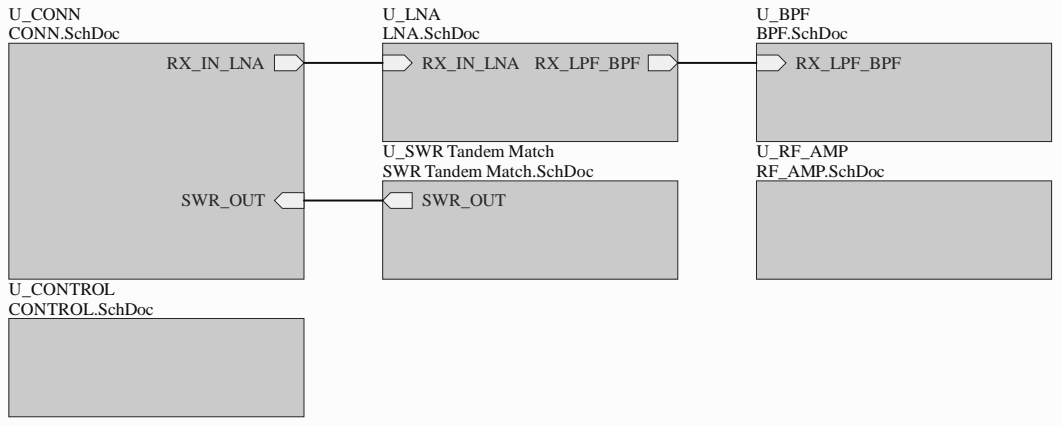
[picture p180: page 1]

U_SWR Tandem Match
SWR Tandem Match.SchDoc
SWR_OUT

C:\Dropbox\Develop\Projects\WOLF\Schematic\Wolf\Altium_Designer\RF-UNIT-QRP\RF-UNIT-QRP.SCHDOC

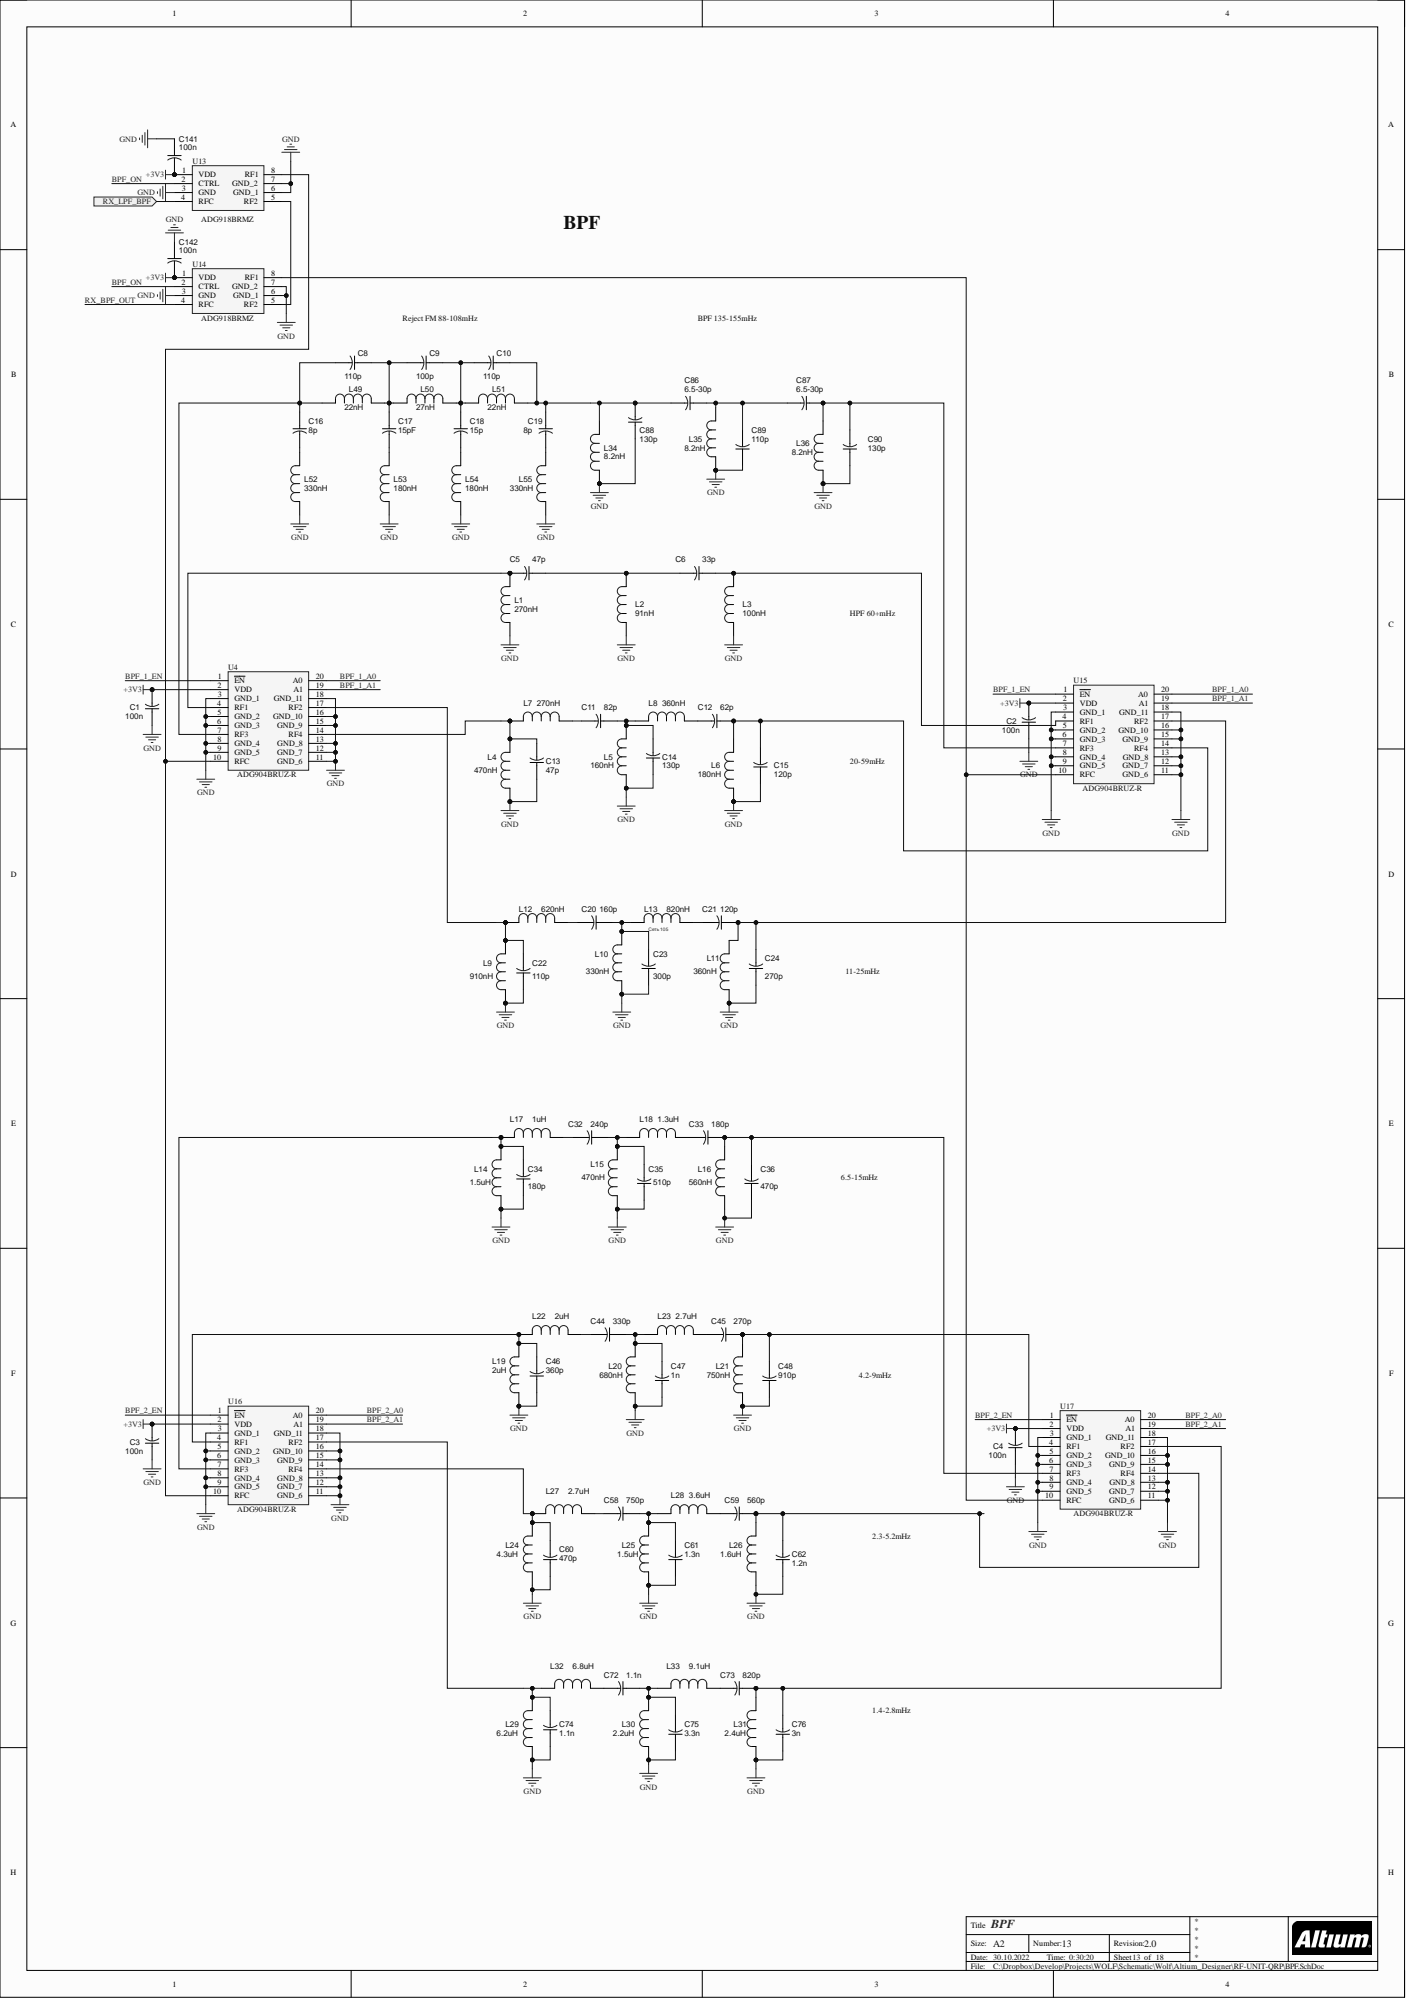
[picture p181: page 2]

EN 1 VDD 2 | RF2

GND_1 3
RF1 4 | 17
GND_2 5 GND_10 GND_9 | 16
GND_3 6 | 15

C15 | | GND_2 5 GND_10 GND_9 RF4 GND_8 GND_7 | 16

RF3 7 | 14
GND_4 8 | 13
GND_5 9 | 12

GND_4 8 GND_8 GND_7 | 13

GND | C20 160p L18 1.3uH C33 180p

C:\Dropbox\Develop\Projects\WOLF\Schematic\Wolf\Altium_Designer\RF-UNIT-QRP\BPF.SchDoc

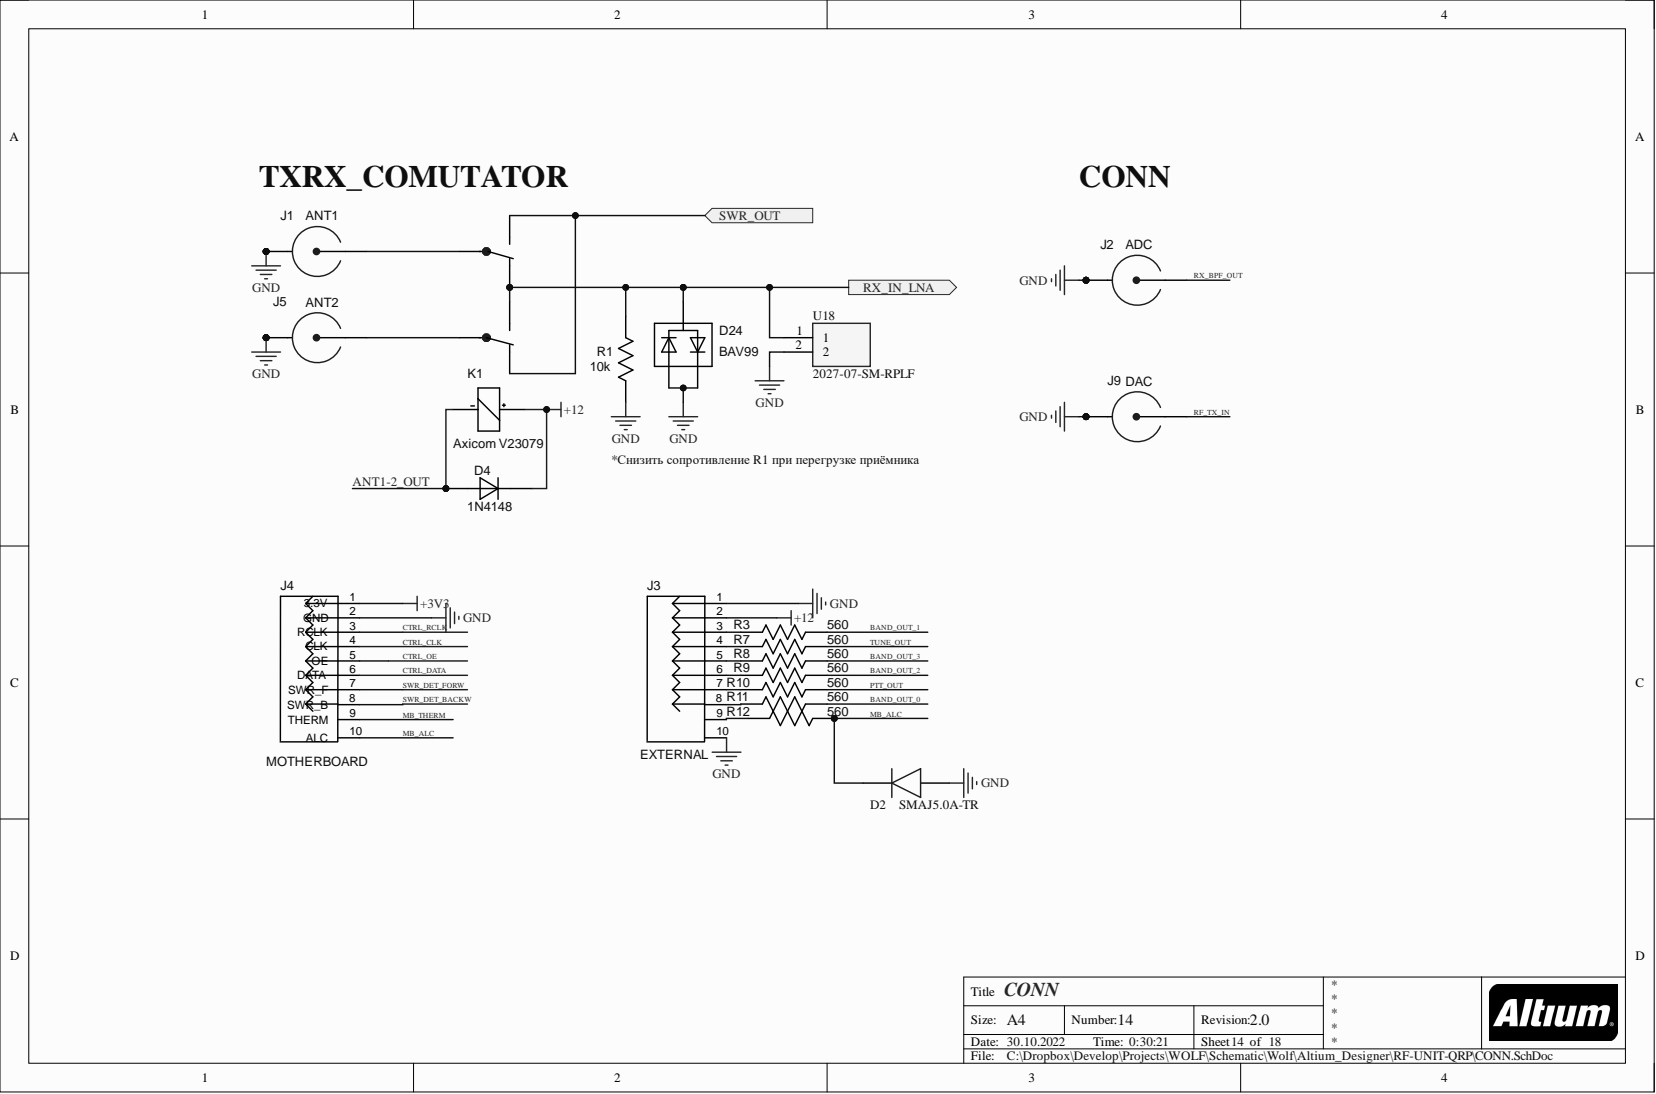
[picture p182: page 3]

GND
*Снизить сопротивление R1 при перегрузке приёмника

C:\Dropbox\Develop\Projects\WOLF\Schematic\Wolf\Altium_Designer\RF-UNIT-QRP\CONN.SchDoc

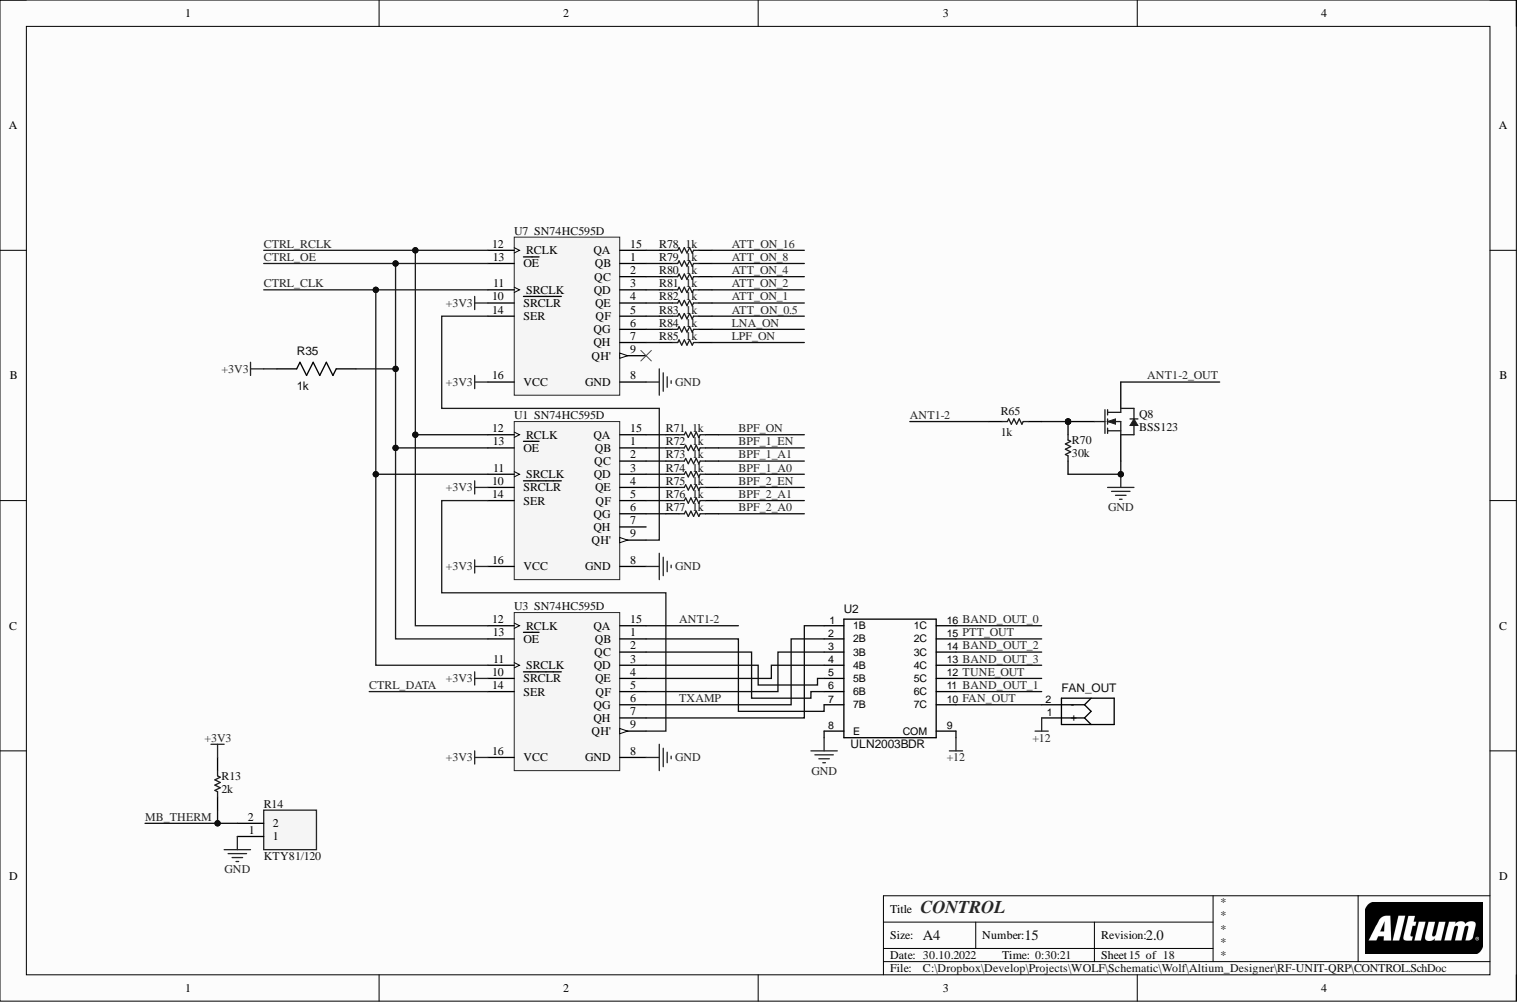
[picture p183: page 4]

1 3 | 1 | | 2
1 1 | 2 | | 3

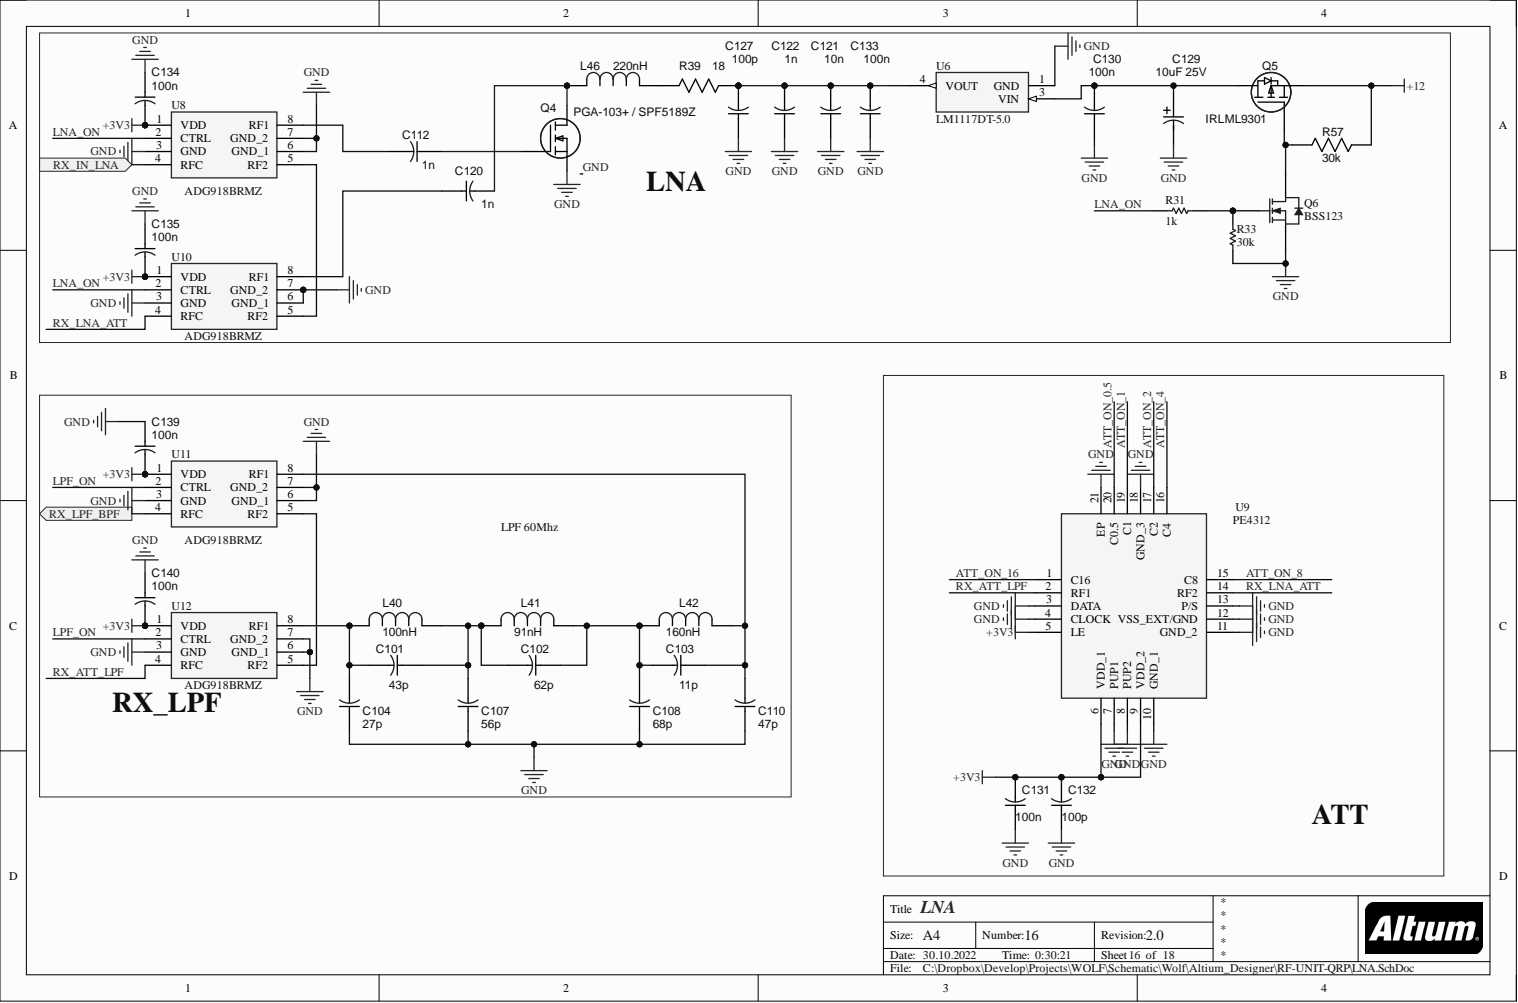
[picture p184: page 5]

C:\Dropbox\Develop\Projects\WOLF\Schematic\Wolf\Altium_Designer\RF-UNIT-QRP\LNA.SchDoc

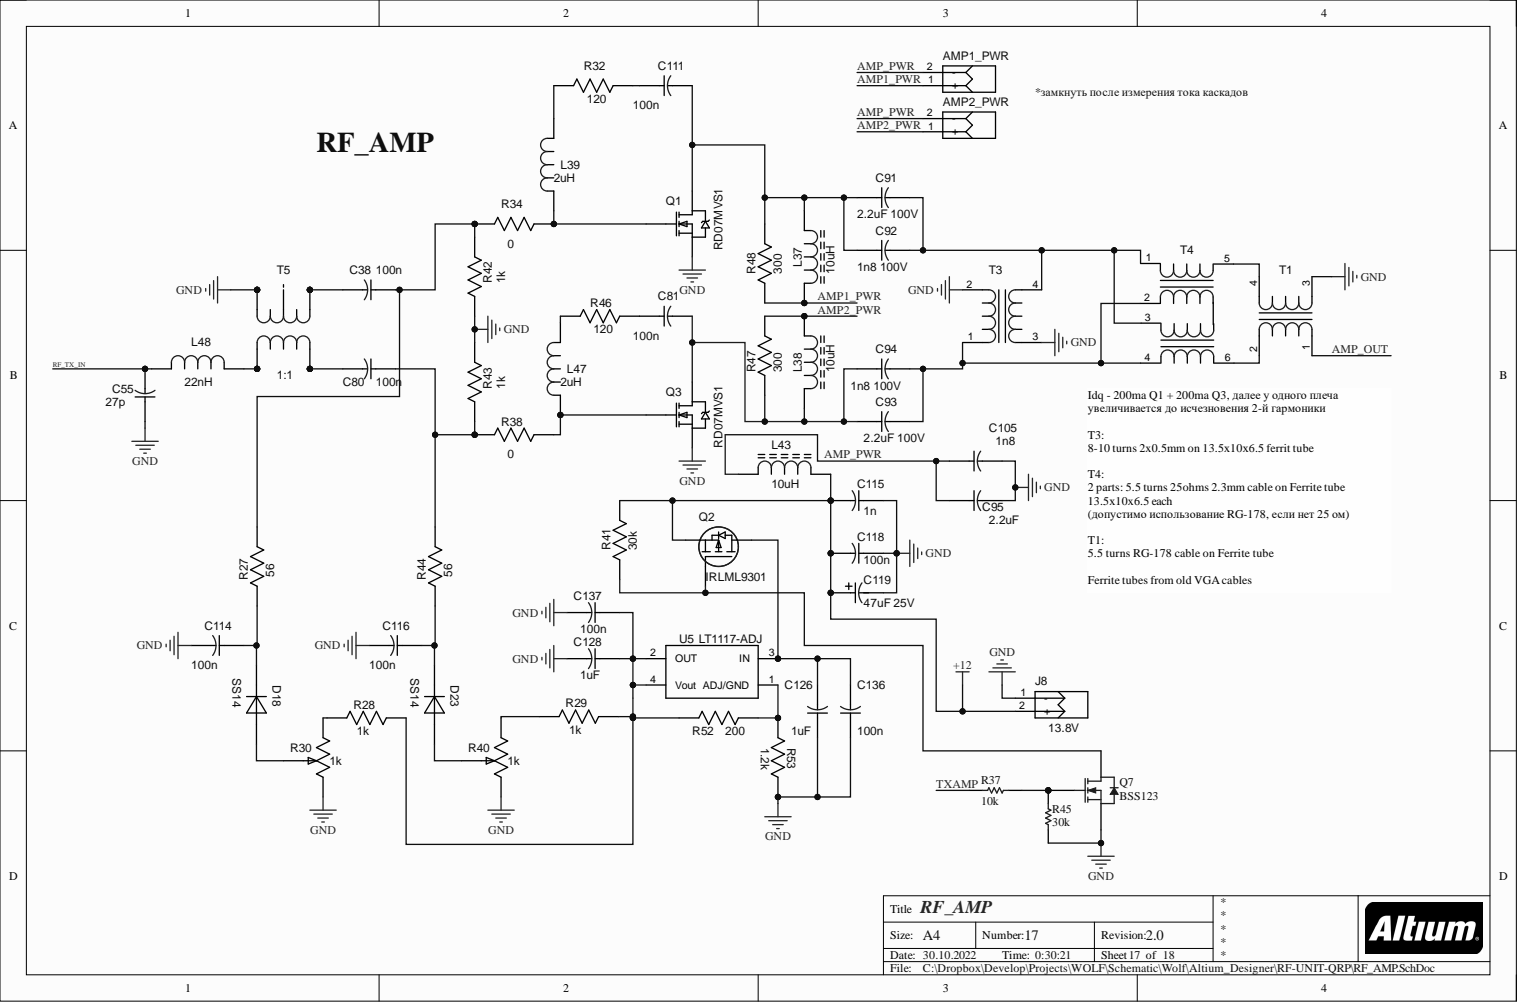
[picture p185: page 6]

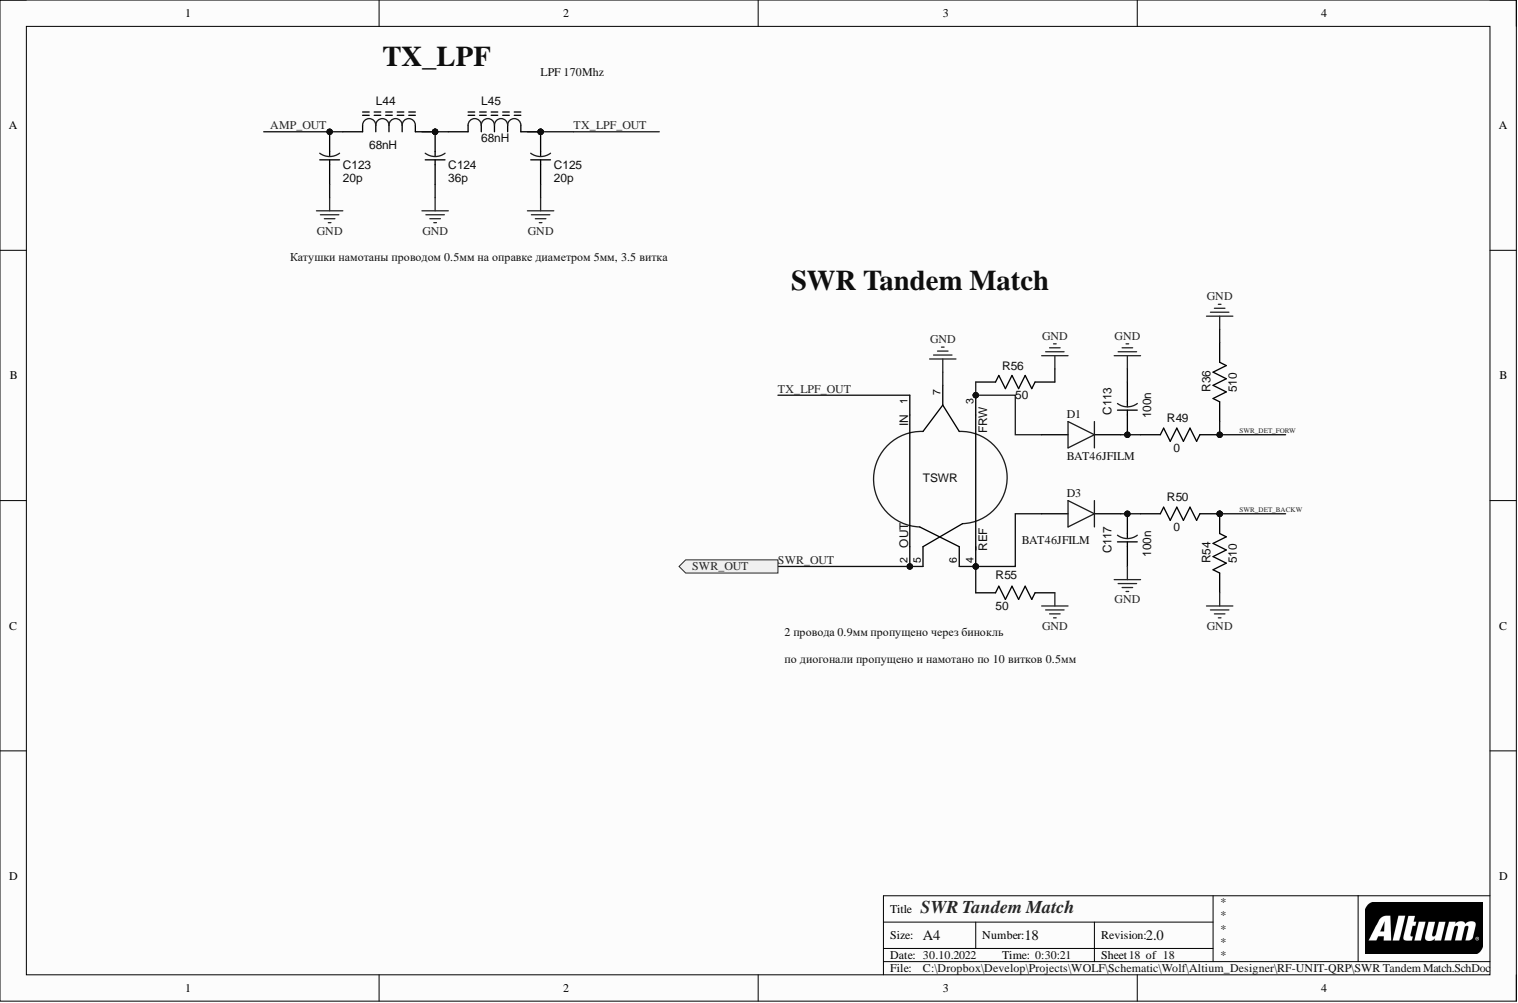
[picture p186: page 7]

Катушки намотаны проводом 0.5мм на оправке диаметром 5мм, 3.5 витка

2 провода 0.9мм пропущено через бинокль

по диогонали пропущено и намотано по 10 витков 0.5мм

C:\Dropbox\Develop\Projects\WOLF\Schematic\Wolf\Altium_Designer\RF-UNIT-QRP\SWR Tandem Match.SchDoc
