donatukas/Volf-TRX/Schematic/Wolf/Addons/PLL_DL2FW/Schematic_WOLF_PLL.pdf

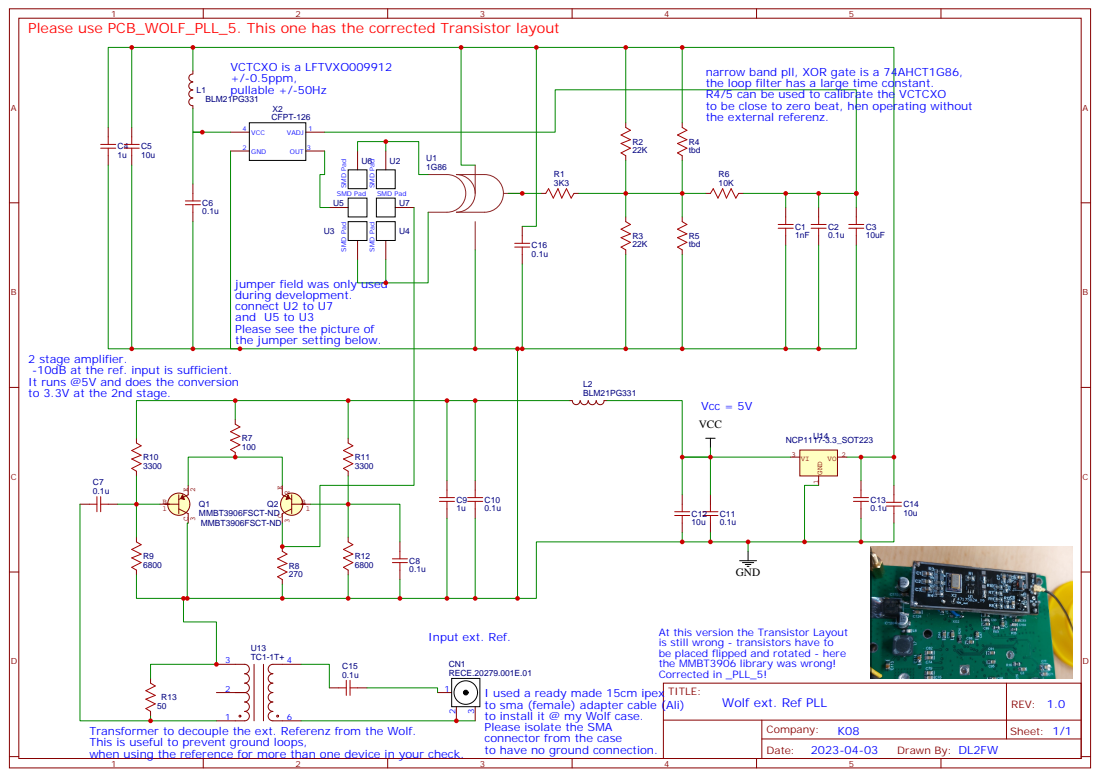
[picture p193: page 1]

Please use PCB_WOLF_PLL_5. This one has the corrected Transistor layout

narrow band pll, XOR gate is a 74AHCT1G86,
the loop filter has a large time constant.
R4/5 can be used to calibrate the VCTCXO
to be close to zero beat, hen operating without
the external referenz.

jumper field was only used
during development.
connect U2 to U7
and U5 to U3
Please see the picture of
the jumper setting below.

2 stage amplifier.
-10dB at the ref. input is sufficient.
It runs @5V and does the conversion
to 3.3V at the 2nd stage.

At this version the Transistor Layout
is still wrong - transistors have to
be placed flipped and rotated - here
the MMBT3906 library was wrong!
Corrected in _PLL_5!
TITLE:

RECE.20279.001E.01
I used a ready made 15cm ipex
to sma (female) adapter cable (Ali)
to install it @ my Wolf case.
Please isolate the SMA
connector from the case
to have no ground connection.

Transformer to decouple the ext. Referenz from the Wolf.
This is useful to prevent ground loops,
when using the reference for more than one device in your check.
