donatukas/Volf-TRX/Schematic/Wolf/Altium_Designer/RF-UNIT-QRP_20W/!AdditionalInfo/Heatsink_QRP++.pdf

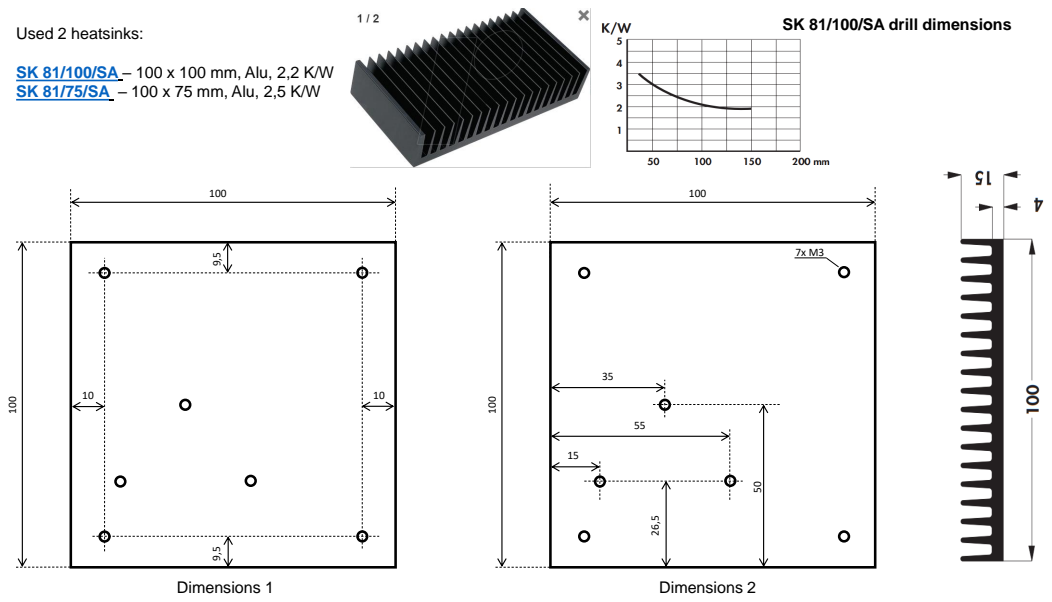
[picture p196: page 1]
Used 2 heatsinks:; Dimensions 1; Dimensions 2

SK 81/100/SA drill dimensions

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

SK 81/75/SA drill dimensions

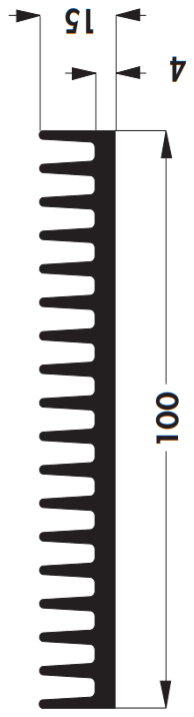
[picture p197: figure]
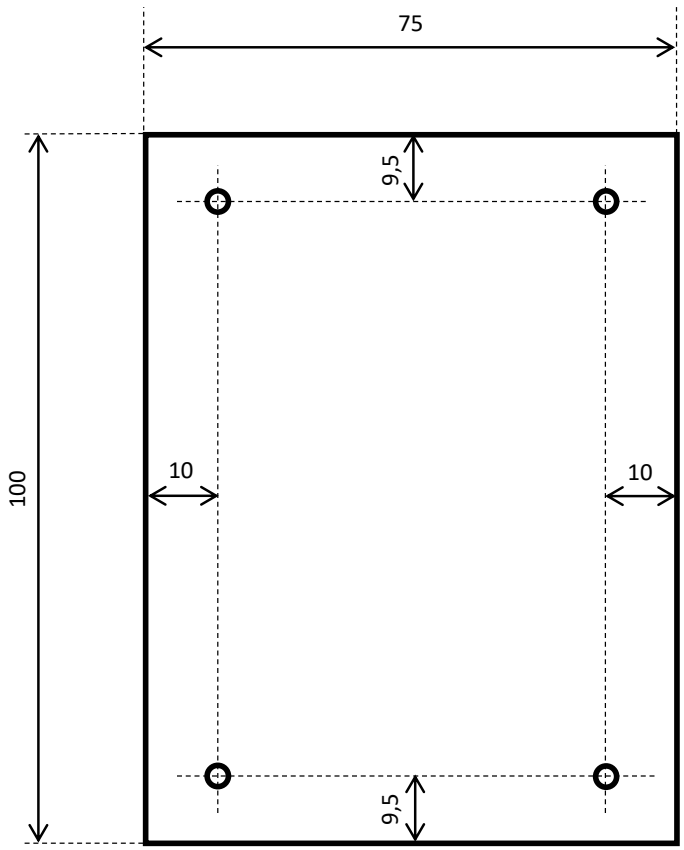
[picture p198: figure]
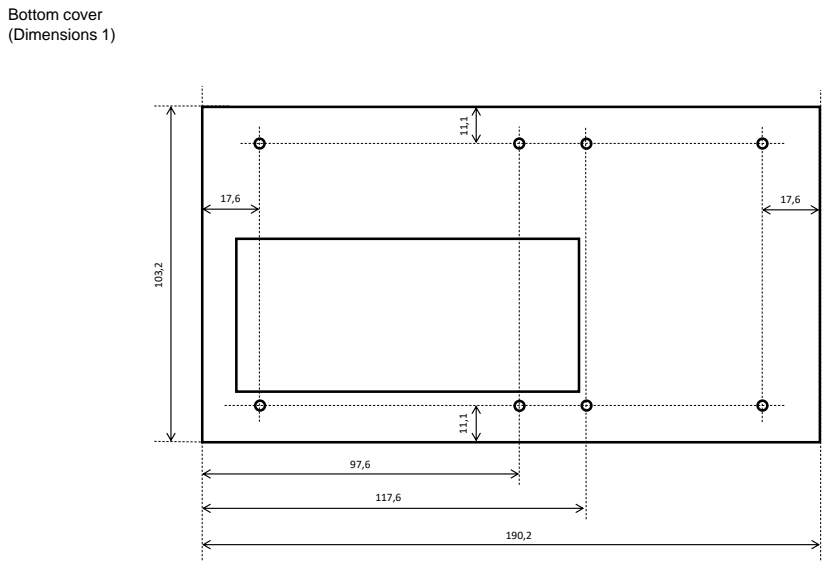
[picture p199: page 3]
Bottom cover (Dimensions 1)

Bottom cover
(Dimensions 2)

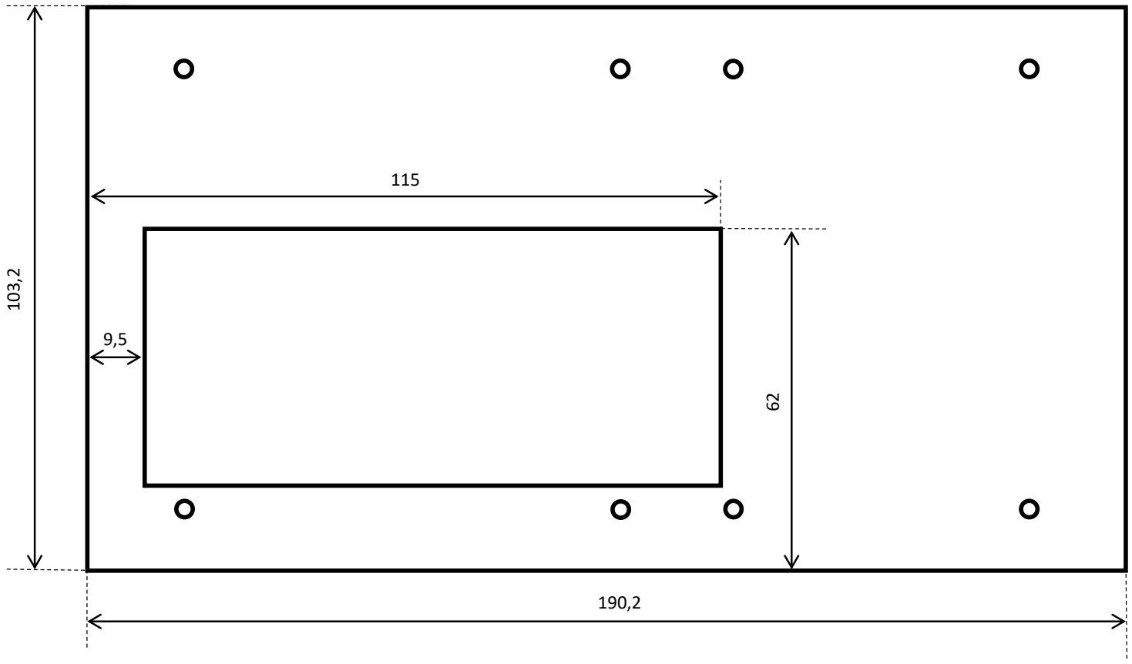
[picture p200: figure]
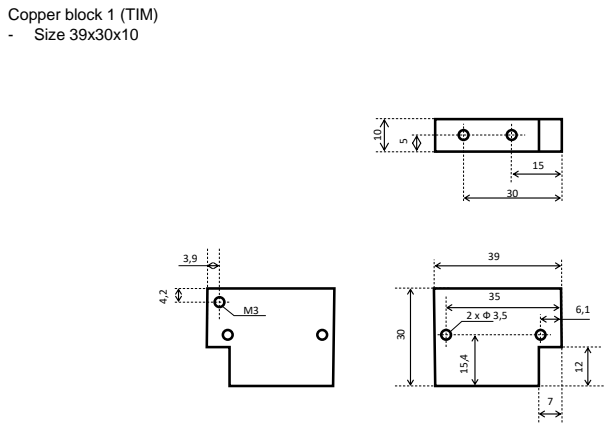
[picture p201: page 5]

Copper block 1 (TIM)
- Size 39x30x10

Copper block 1 (TIM)
- Size 39x20x8

8

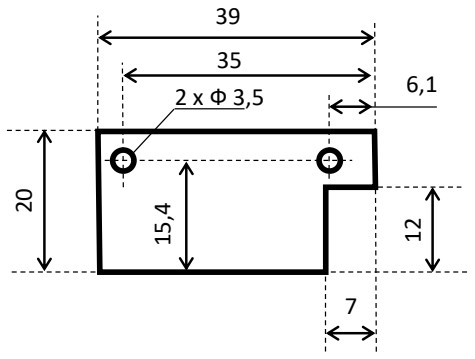
[picture p202: figure]
