donatukas/Volf-TRX/Schematic/Wolf-Lite/Scheme/Main-Unit-v2.pdf

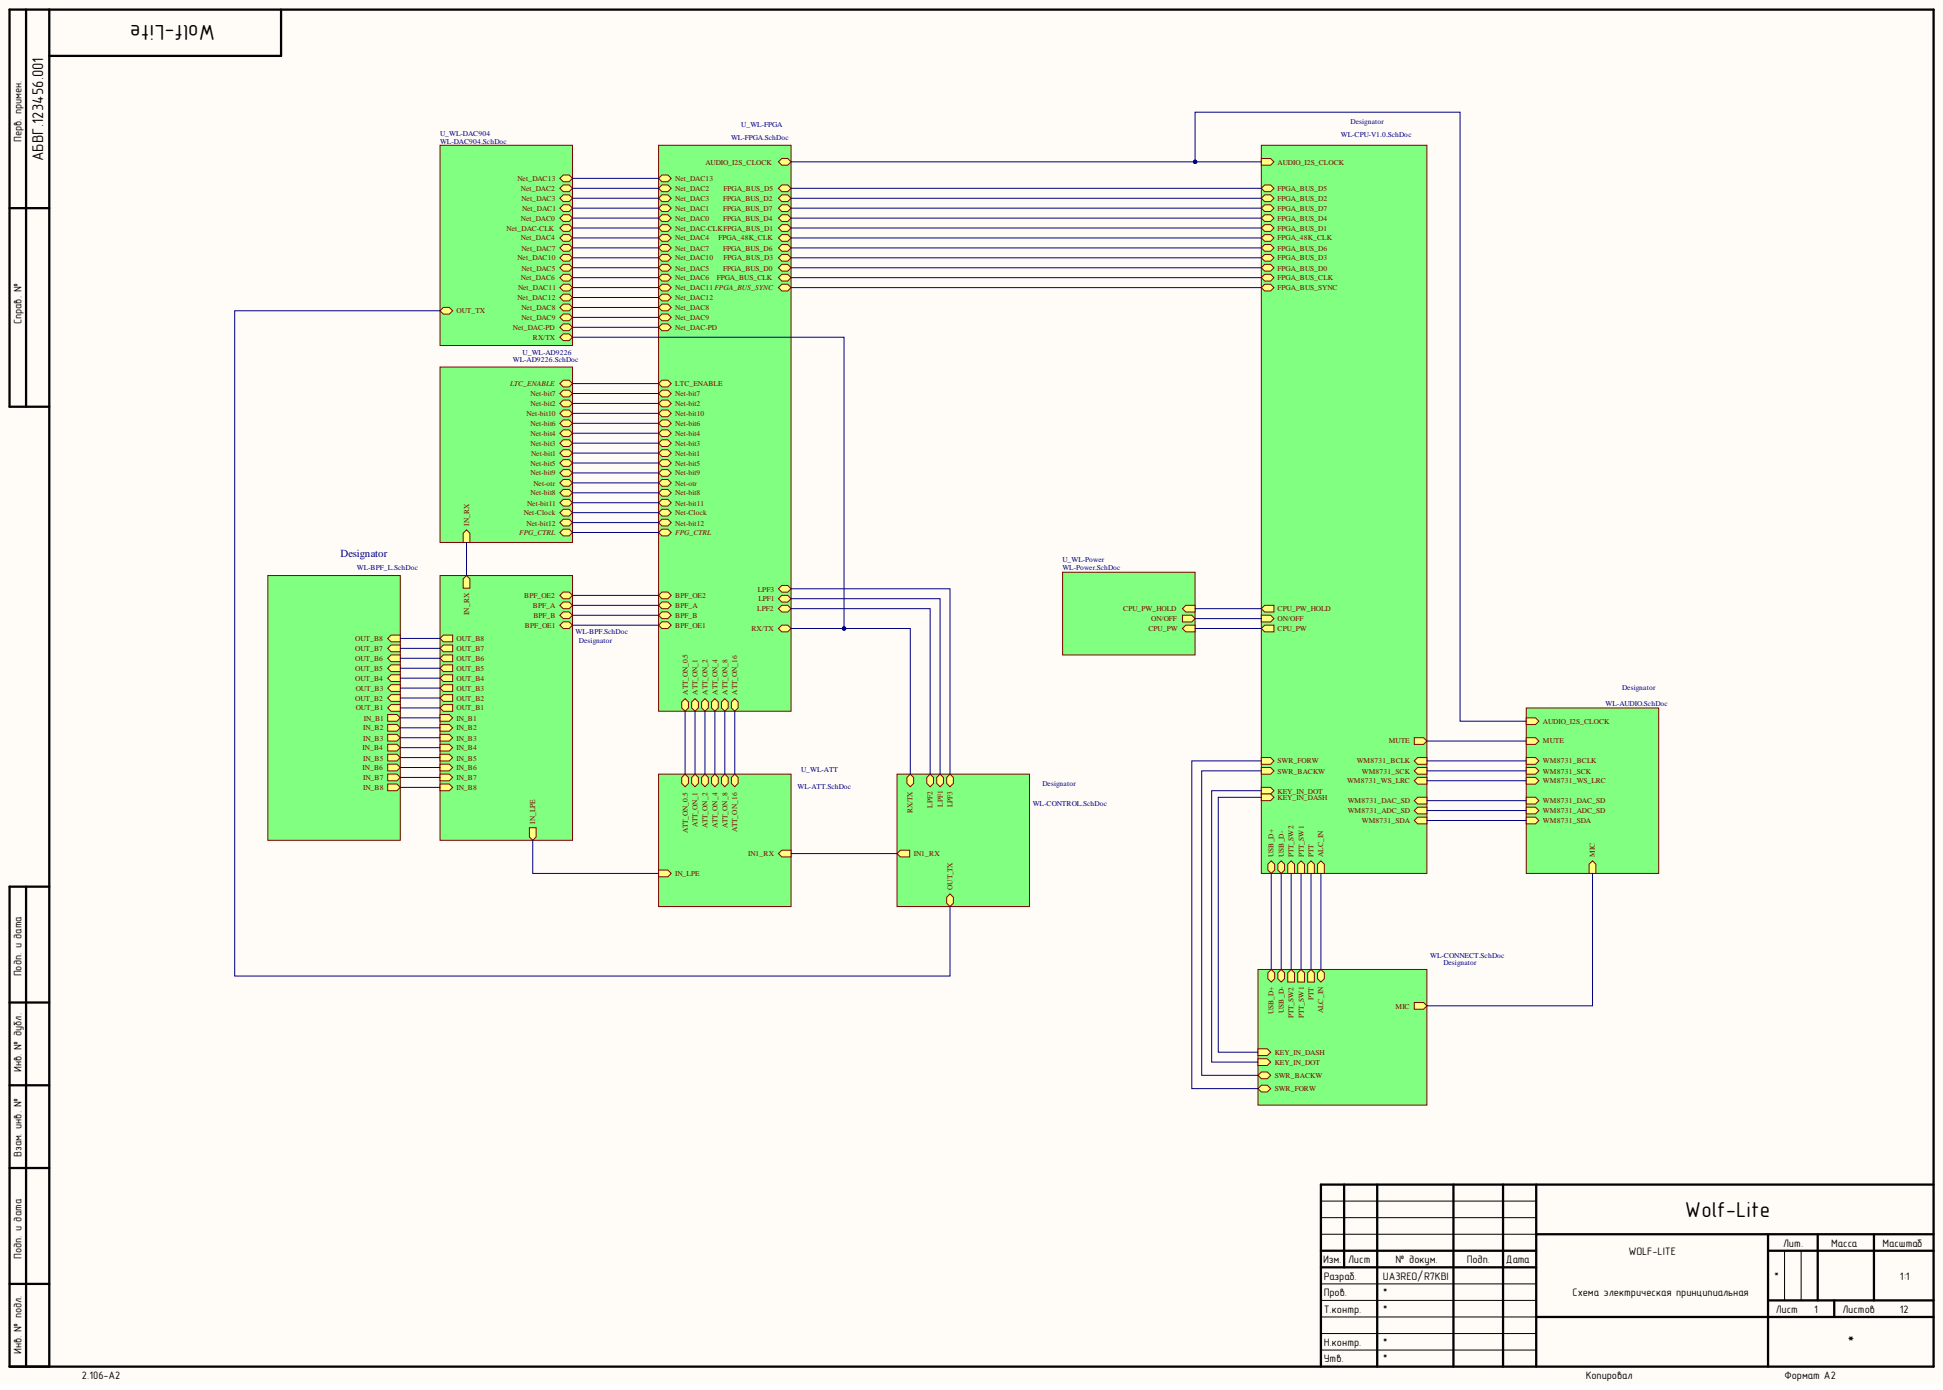
[picture p203: page 1]

Инв. № подл. Инв. № дубл. Подп. и дата Взам. инв. № Подп. и дата Перв. примен. Справ. №

Net_DAC9 OUT_TX Net_DAC-PD RX/TX | | Net_DAC9 Net_DAC-PD

LTC_ENABLE Net-bit7 Net-bit2 Net-bit10 Net-bit6 Net-bit4 Net-bit3 Net-bit1 Net-bit5 Net-bit9 Net-otr Net-bit8 Net-bit11 Net-Clock Net-bit12 FPG_CTRL LPF3 BPF_OE2 LPF1 BPF_A BPF_B LPF2 BPF_OE1

RX/TX | U_WL-ATT

MUTE SWR_FORW WM8731_BCLK SWR_BACKW WM8731_SCK WM8731_WS_LRC KEY_IN_DOT KEY_IN_DASH WM8731_DAC_SD WM8731_ADC_SD WM8731_SDA

Designator WL-CONNECT.SchDoc

Wolf-Lite

WOLF-LITE Схема электрическая принципиальная | Лит. | Масса | Масштаб

Изм. | Лист | № докум. | Подп. | Дата | | * | | | 1:1
Разраб. | | UA3REO/R7KBI

Пров. | | *
Т.контр. | * | | | | Лист | Листов 12

Н.контр. | *
Утв. | *

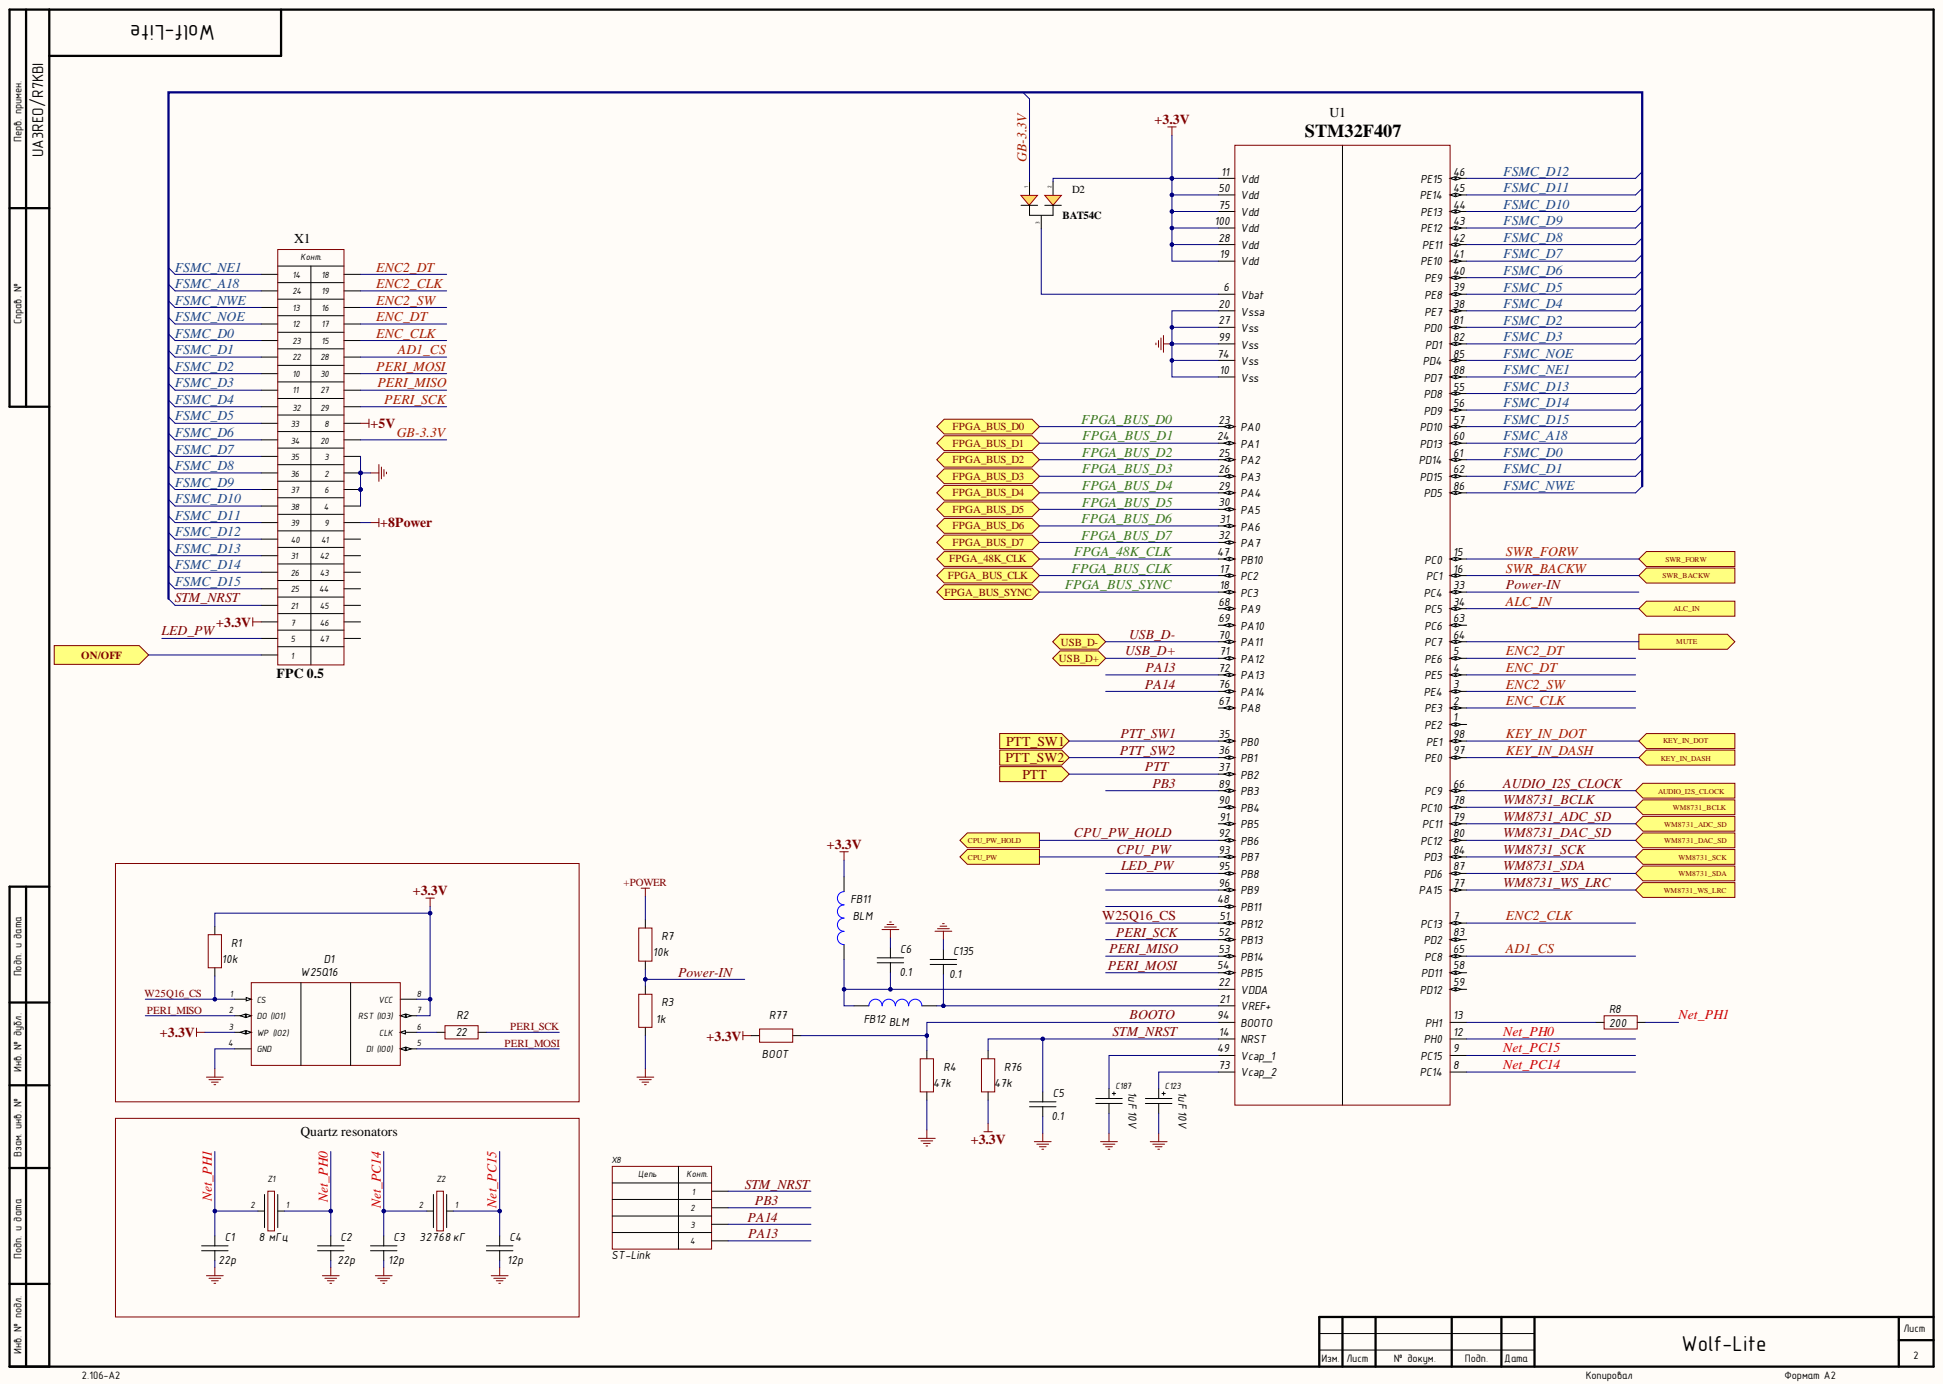
[picture p204: page 2]

Инв. № подл. Инв. № дубл. Подп. и дата Взам. инв. № Подп. и дата Перв. примен. Справ. №

Quart | z re sona tors

X8 ST-Link | 12

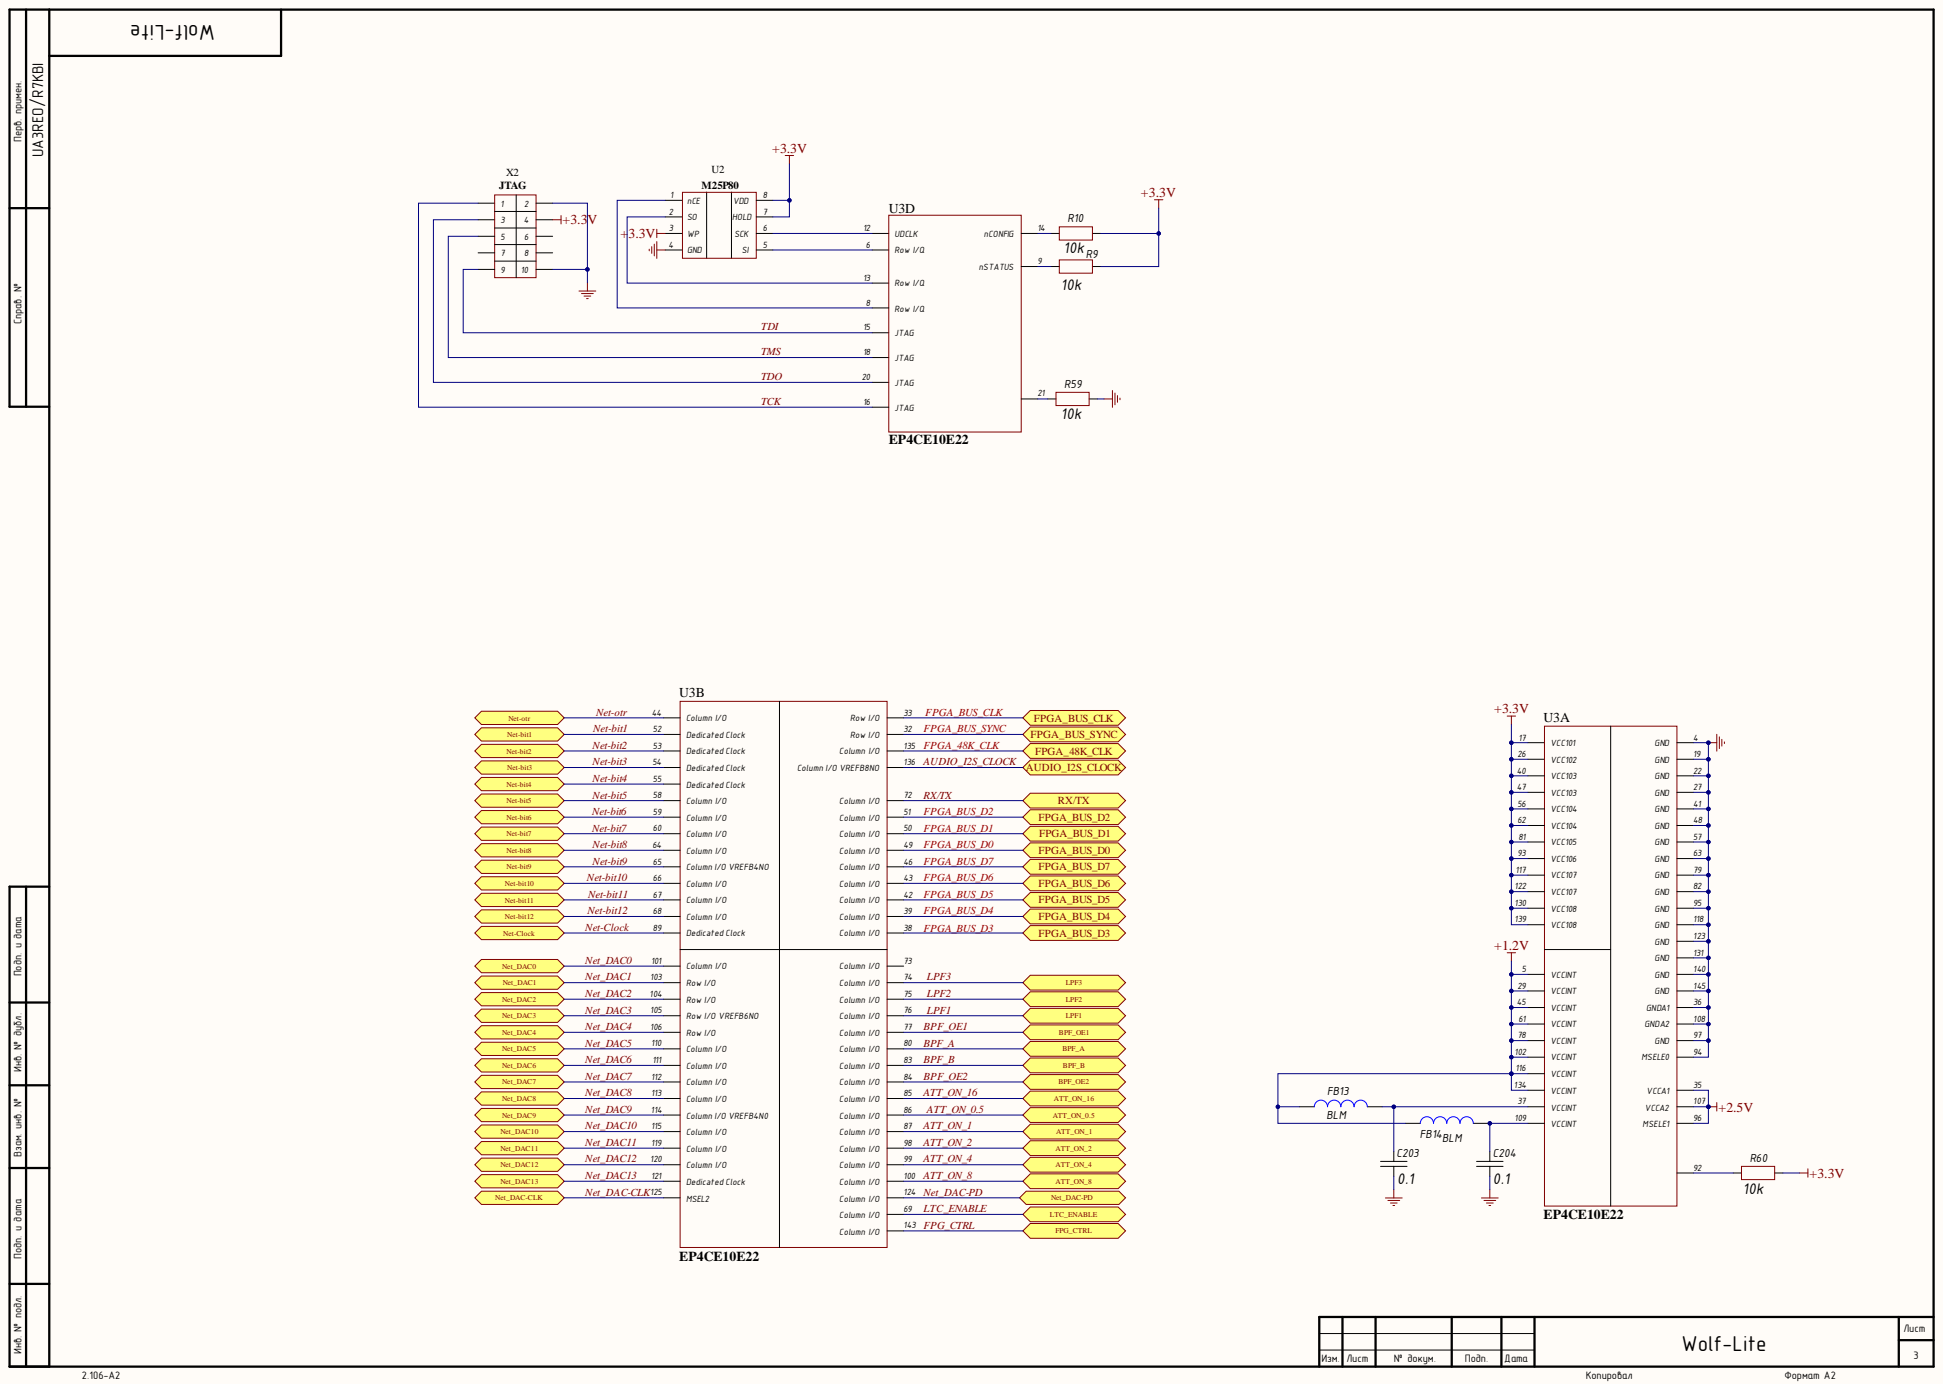
[picture p205: page 3]

Инв. № подл. Инв. № дубл. Подп. и дата Взам. инв. № Подп. и дата Перв. примен. Справ. №

TDI TMS TDO TCK

C o l umn I / O D e d i c a t e d C l o c k D e d i c a t e d C l o c k D e d i c a t e d C l o c k D e d i c a t e d C l o c k C o l umn I / O C o l umn I / O C o l umn I / O C o l umn I / O C o l umn I / O VR E F B 4 N O C o l umn I / O C o l umn I / O C o l umn I / O D e d i c a t e d C l o c k | R ow I / O R ow I / O C o l umn I / O C o l umn I / O VR E F B 8 N O C o l umn I / O C o l umn I / O C o l umn I / O C o l umn I / O C o l umn I / O C o l umn I / O C o l umn I / O C o l umn I / O C o l umn I / O

FB13 BLM | 1 34

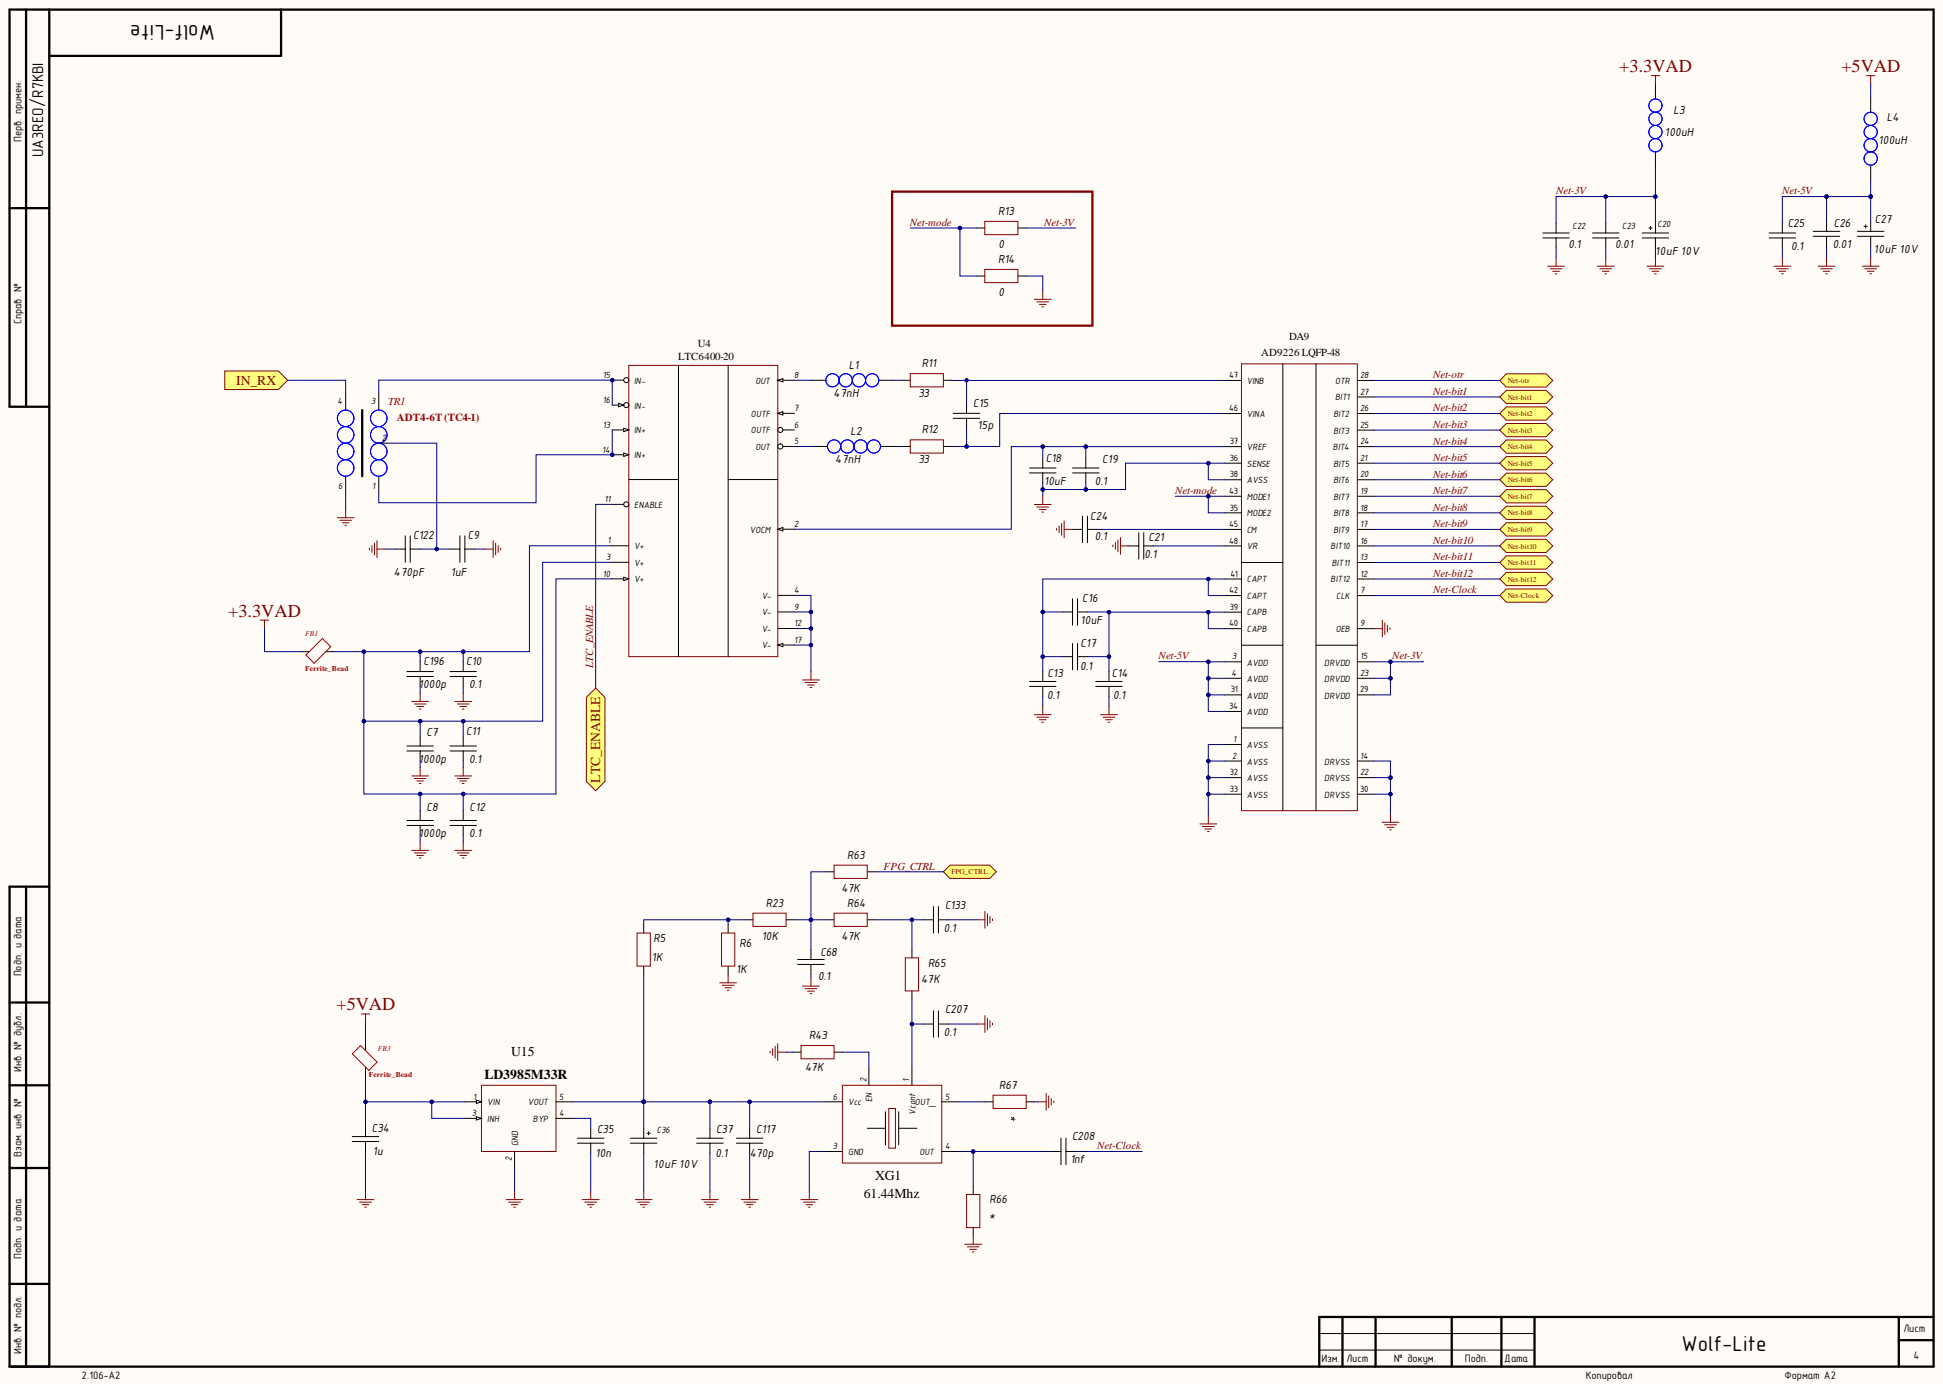
[picture p206: page 4]

Инв. № подл. Инв. № дубл. Подп. и дата Взам. инв. № Подп. и дата Перв. примен. Справ. №

E NAB LE V+ V+ V+ | | VO CM V -V -V -V - | | | | 19 Ne t -b i t7

AVD D AVD D | D RVD D D RVD D D RVD D D RVS S D RVS S D RVS S

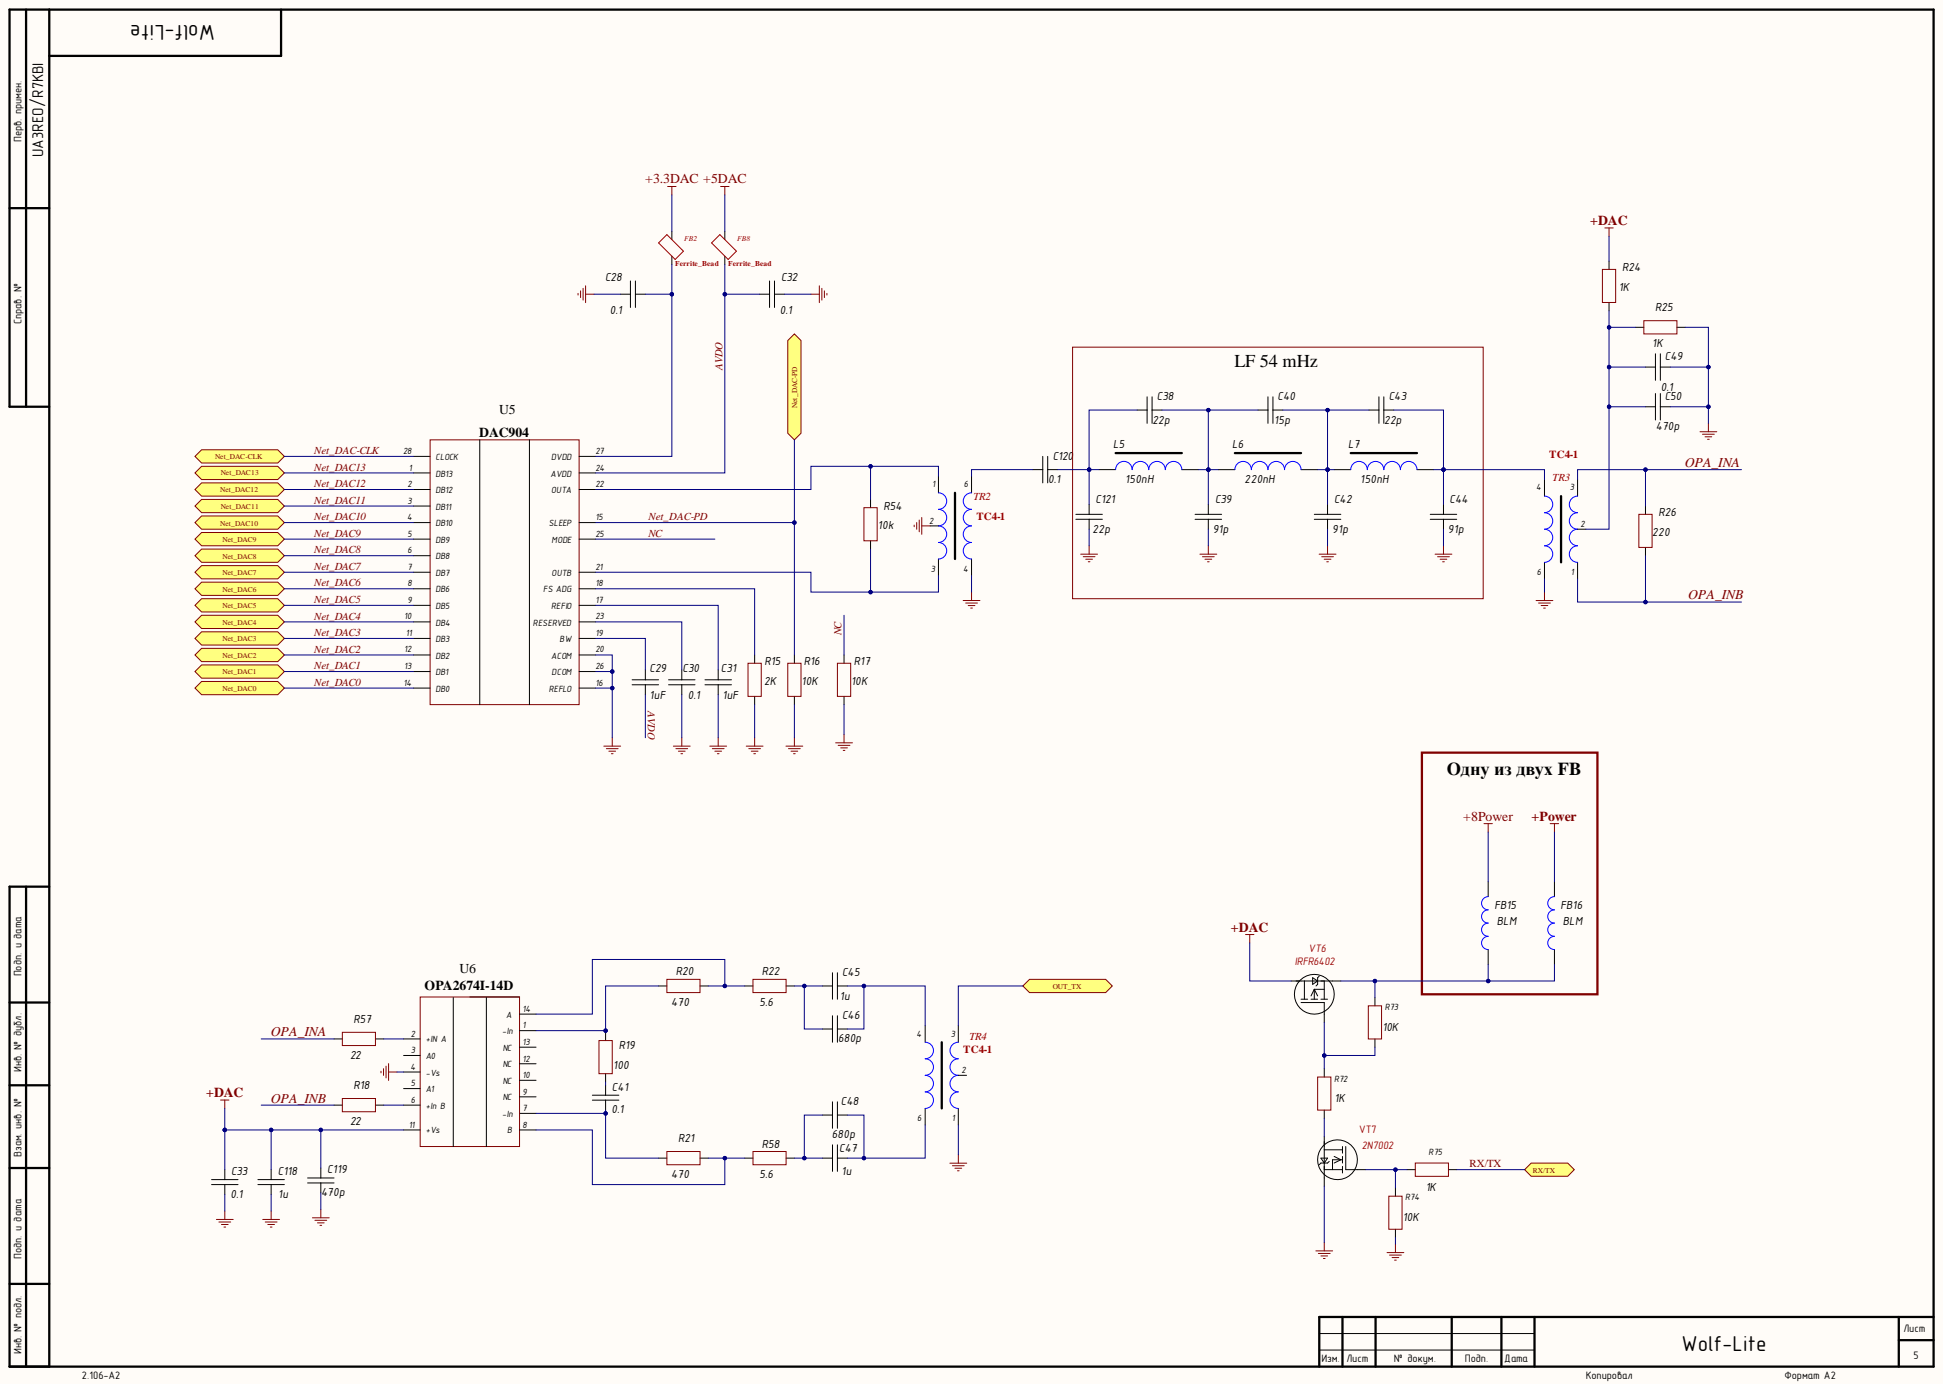
[picture p207: page 5]

Инв. № подл. Инв. № дубл. Подп. и дата Взам. инв. № Подп. и дата Перв. примен. Справ. №

Одну из двух FB

Лист | № докум. | Подп. | Дата | Wolf-Lite Изм.

Лист

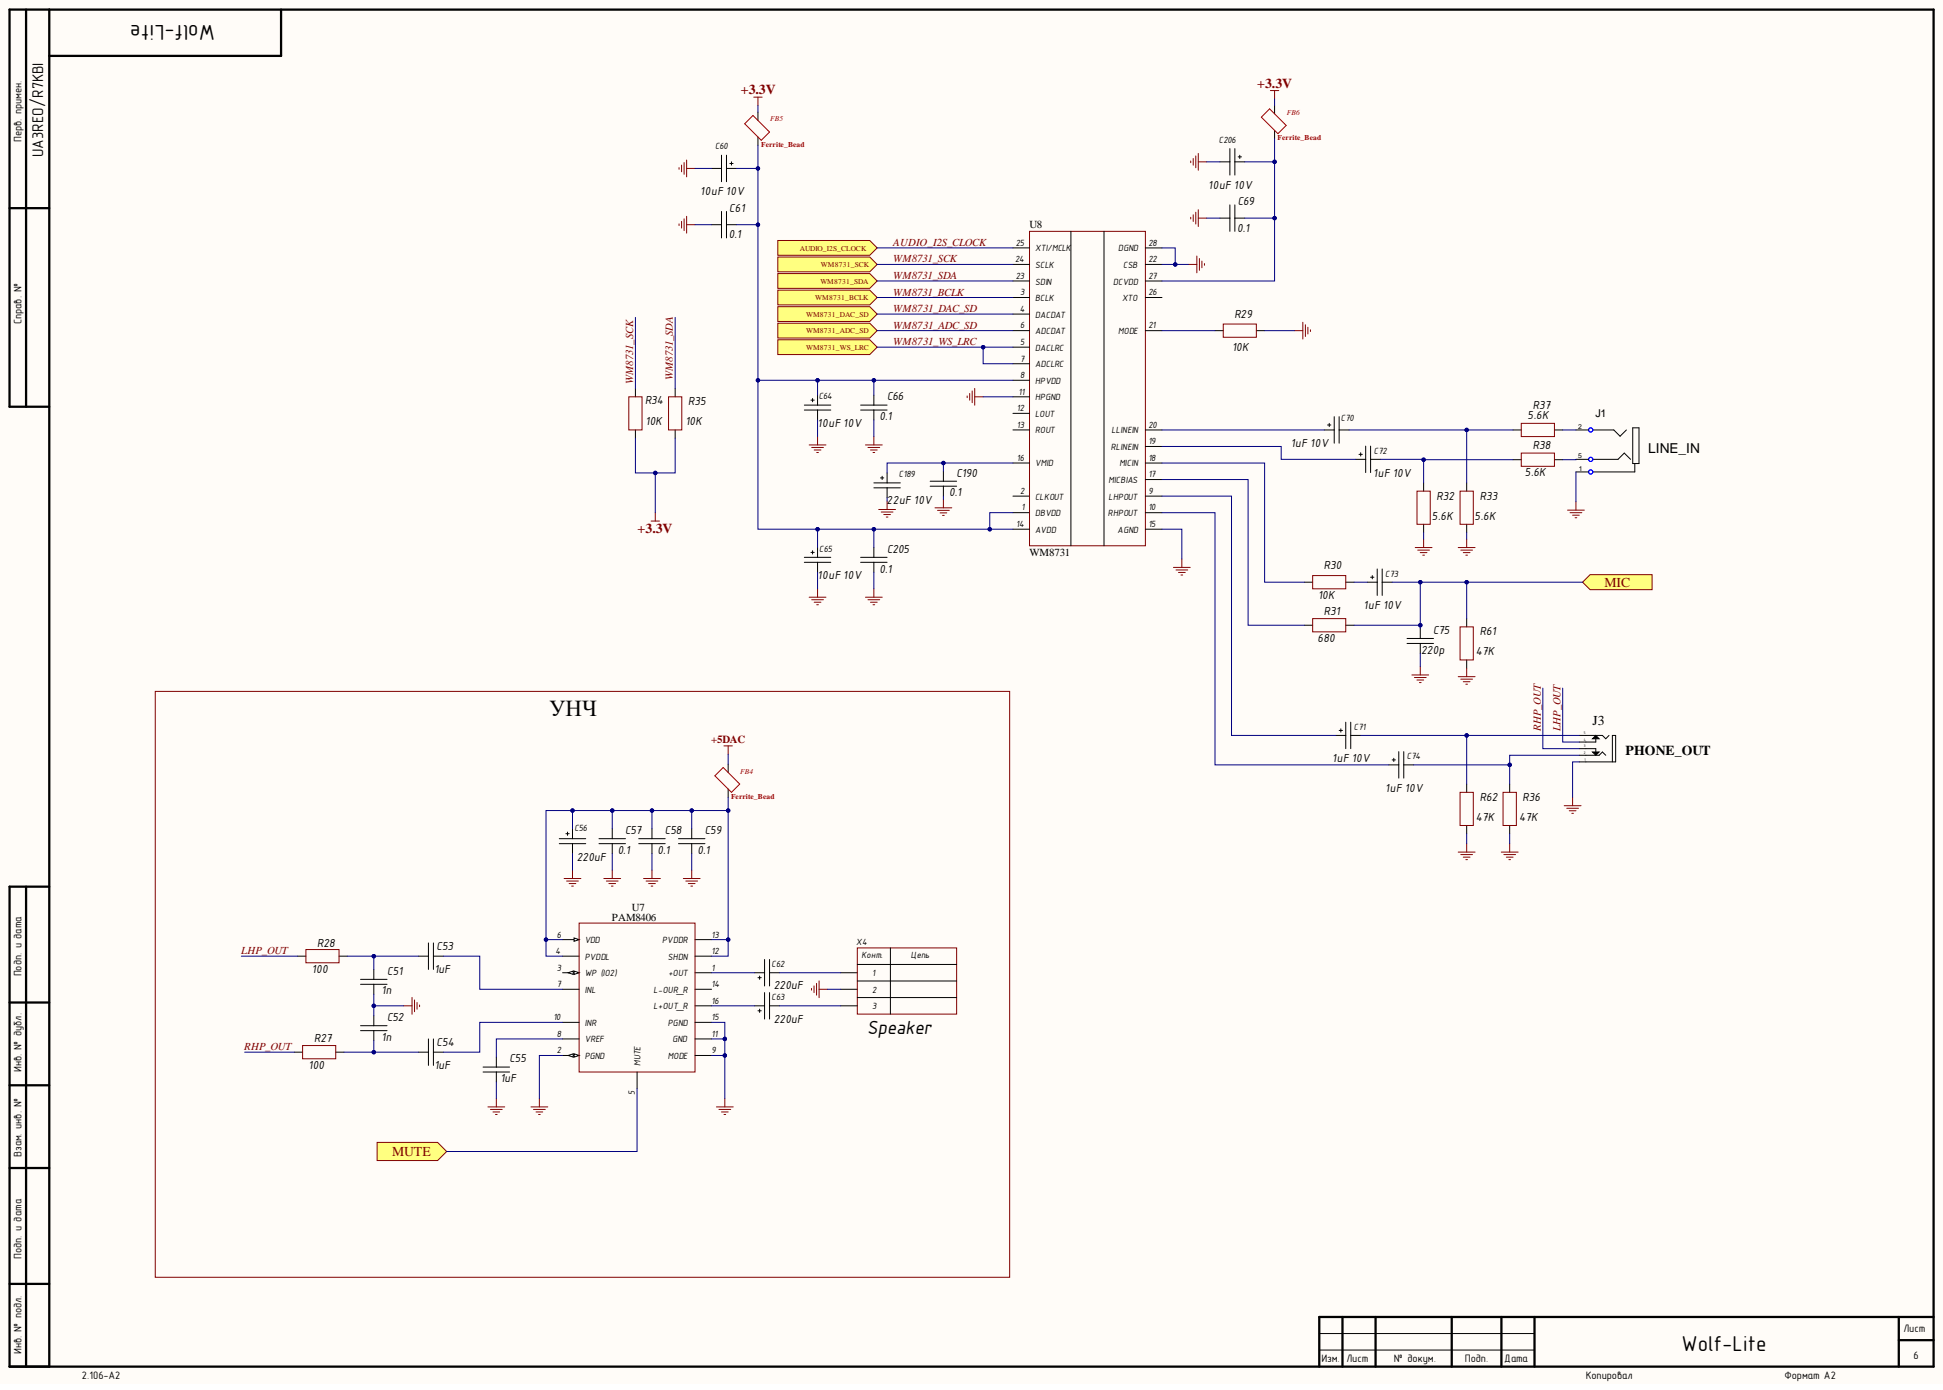
[picture p208: page 6]

Инв. № подл. Инв. № дубл. Подп. и дата Взам. инв. № Подп. и дата Перв. примен. Справ. №

Конт. | Цепь

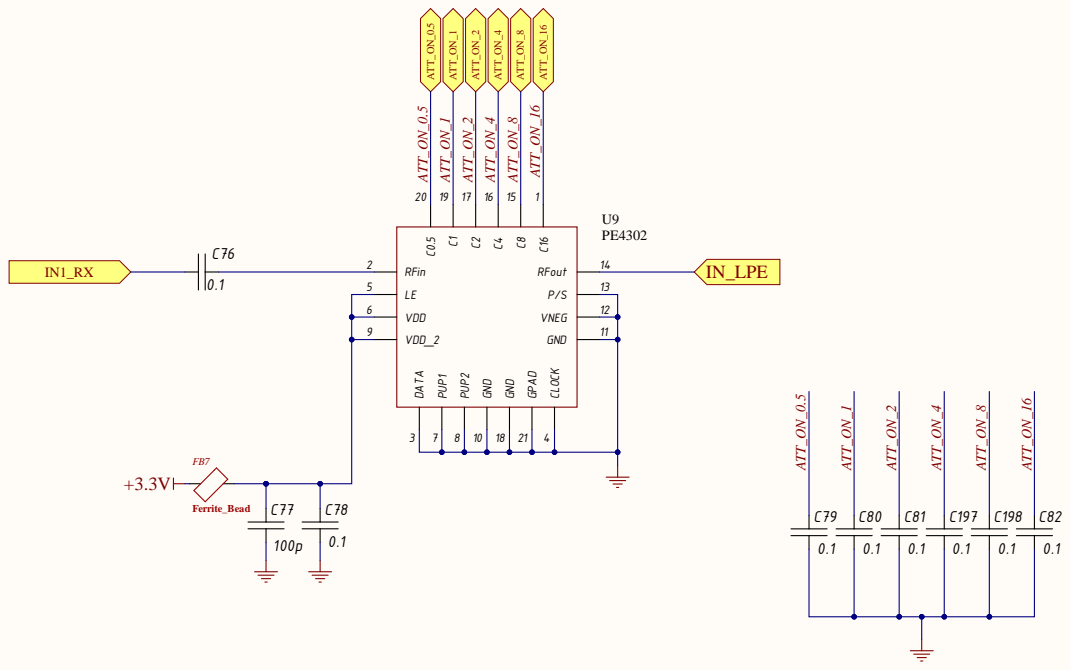
[picture p209: page 7]

Инв. № подл. Инв. № дубл. Подп. и дата Взам. инв. № Подп. и дата

Wolf-Lite

Изм. | Лист | № докум. | Подп. | Дата

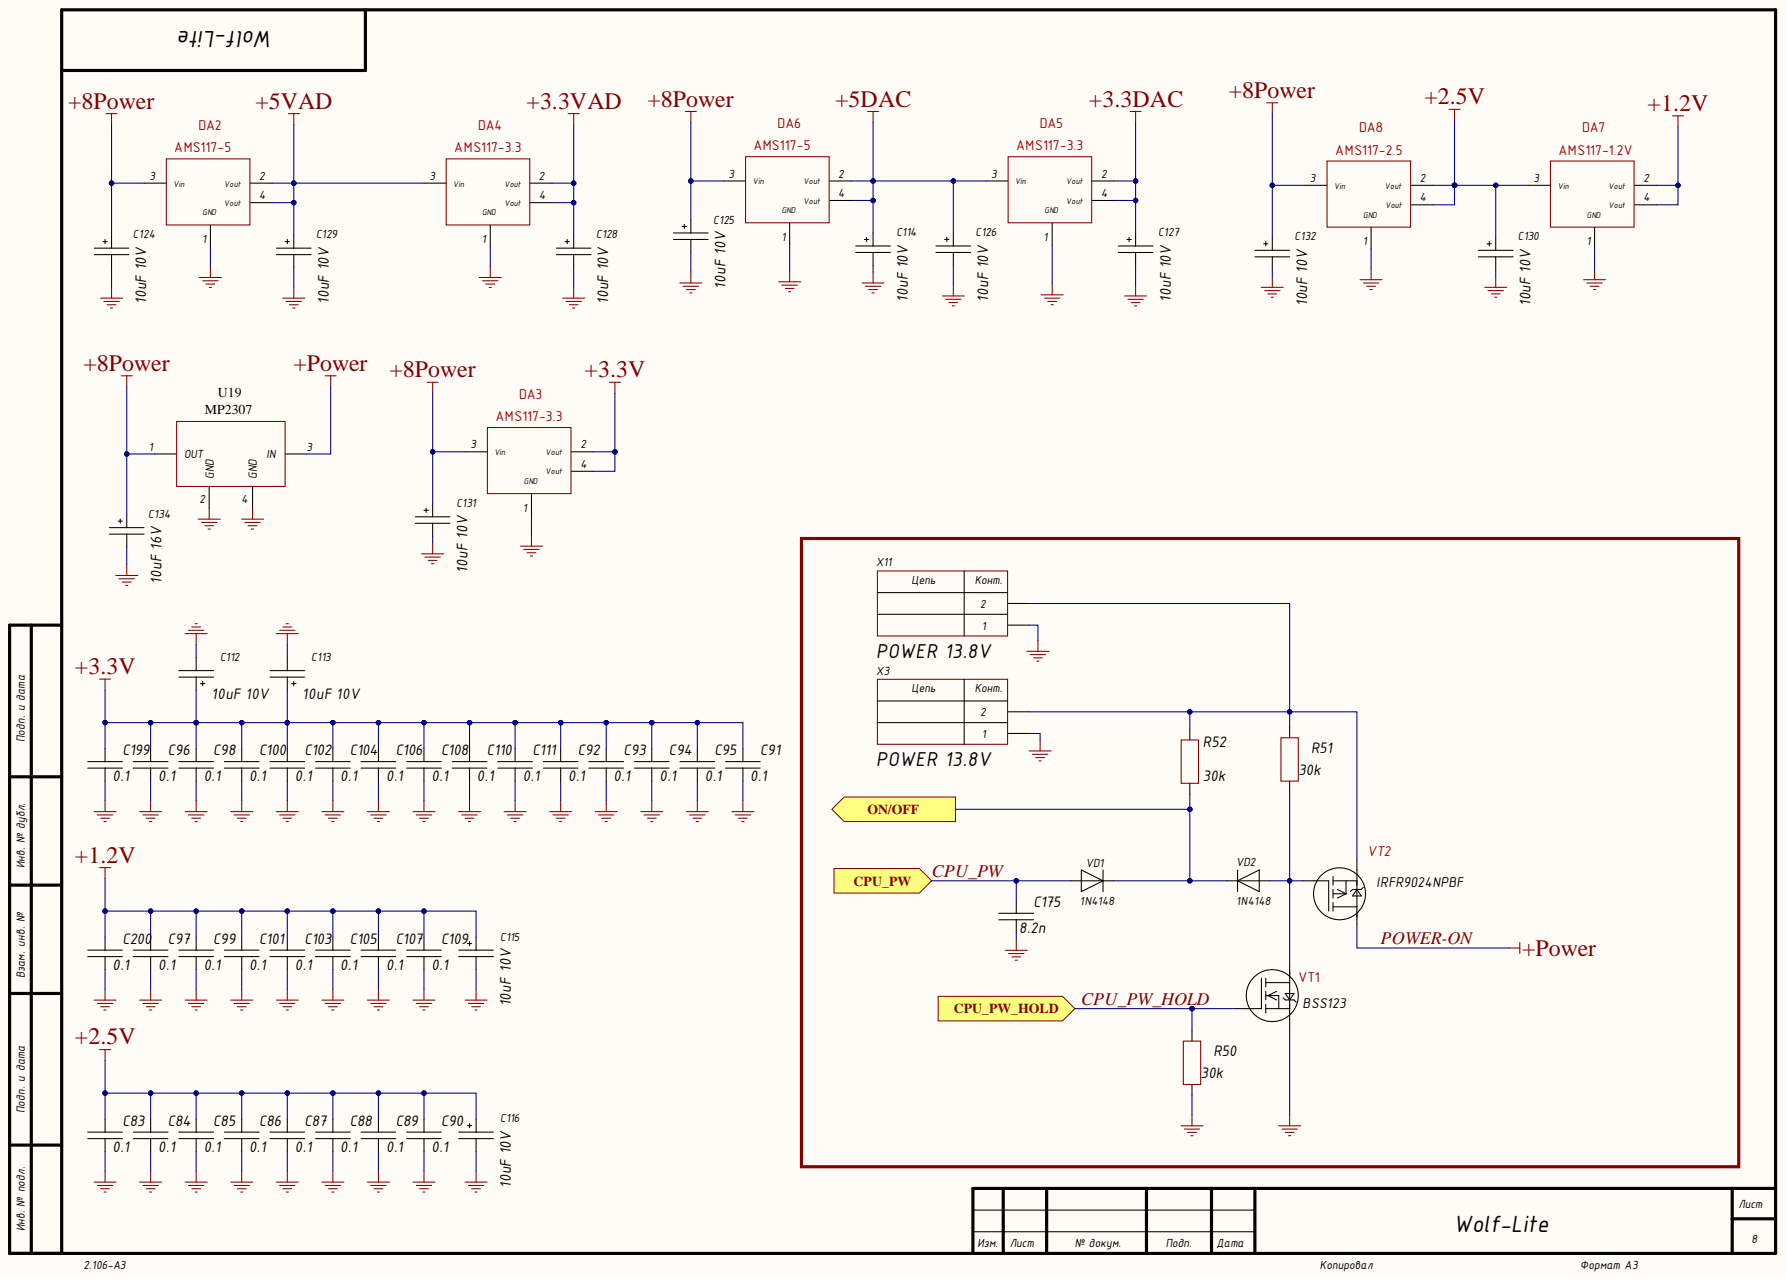
[picture p210: page 8]

Цепь | Конт.

Инв. № подл. Инв. № дубл. Подп. и дата Взам. инв. № Подп. и дата

Wolf-Lite

Изм. | Лист | № докум. | Подп. | Дата

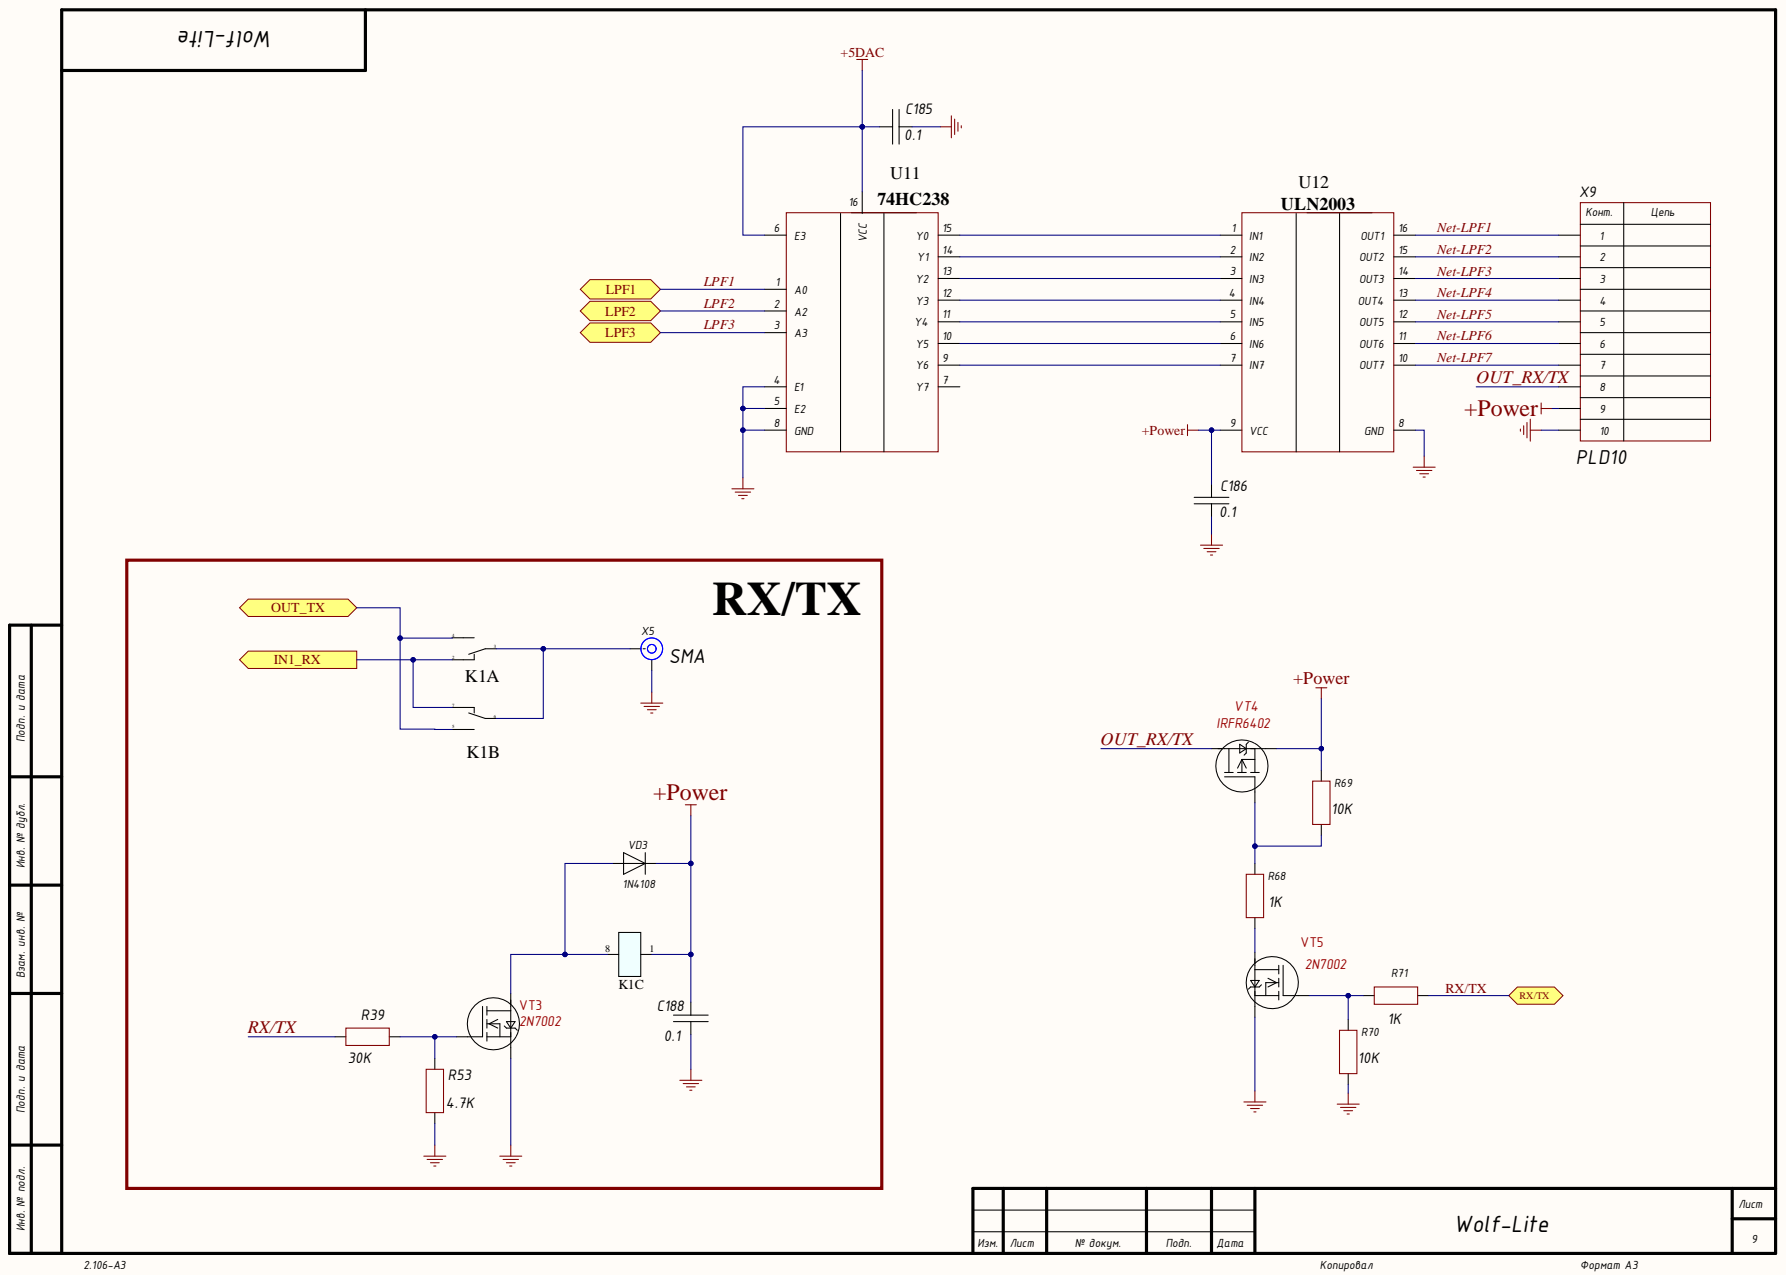
[picture p211: page 9]

Конт. | Цепь

GND 8

Инв. № подл. Инв. № дубл. Подп. и дата Взам. инв. № Подп. и дата

Wolf-Lite

Изм. | Лист | № докум. | Подп. | Дата

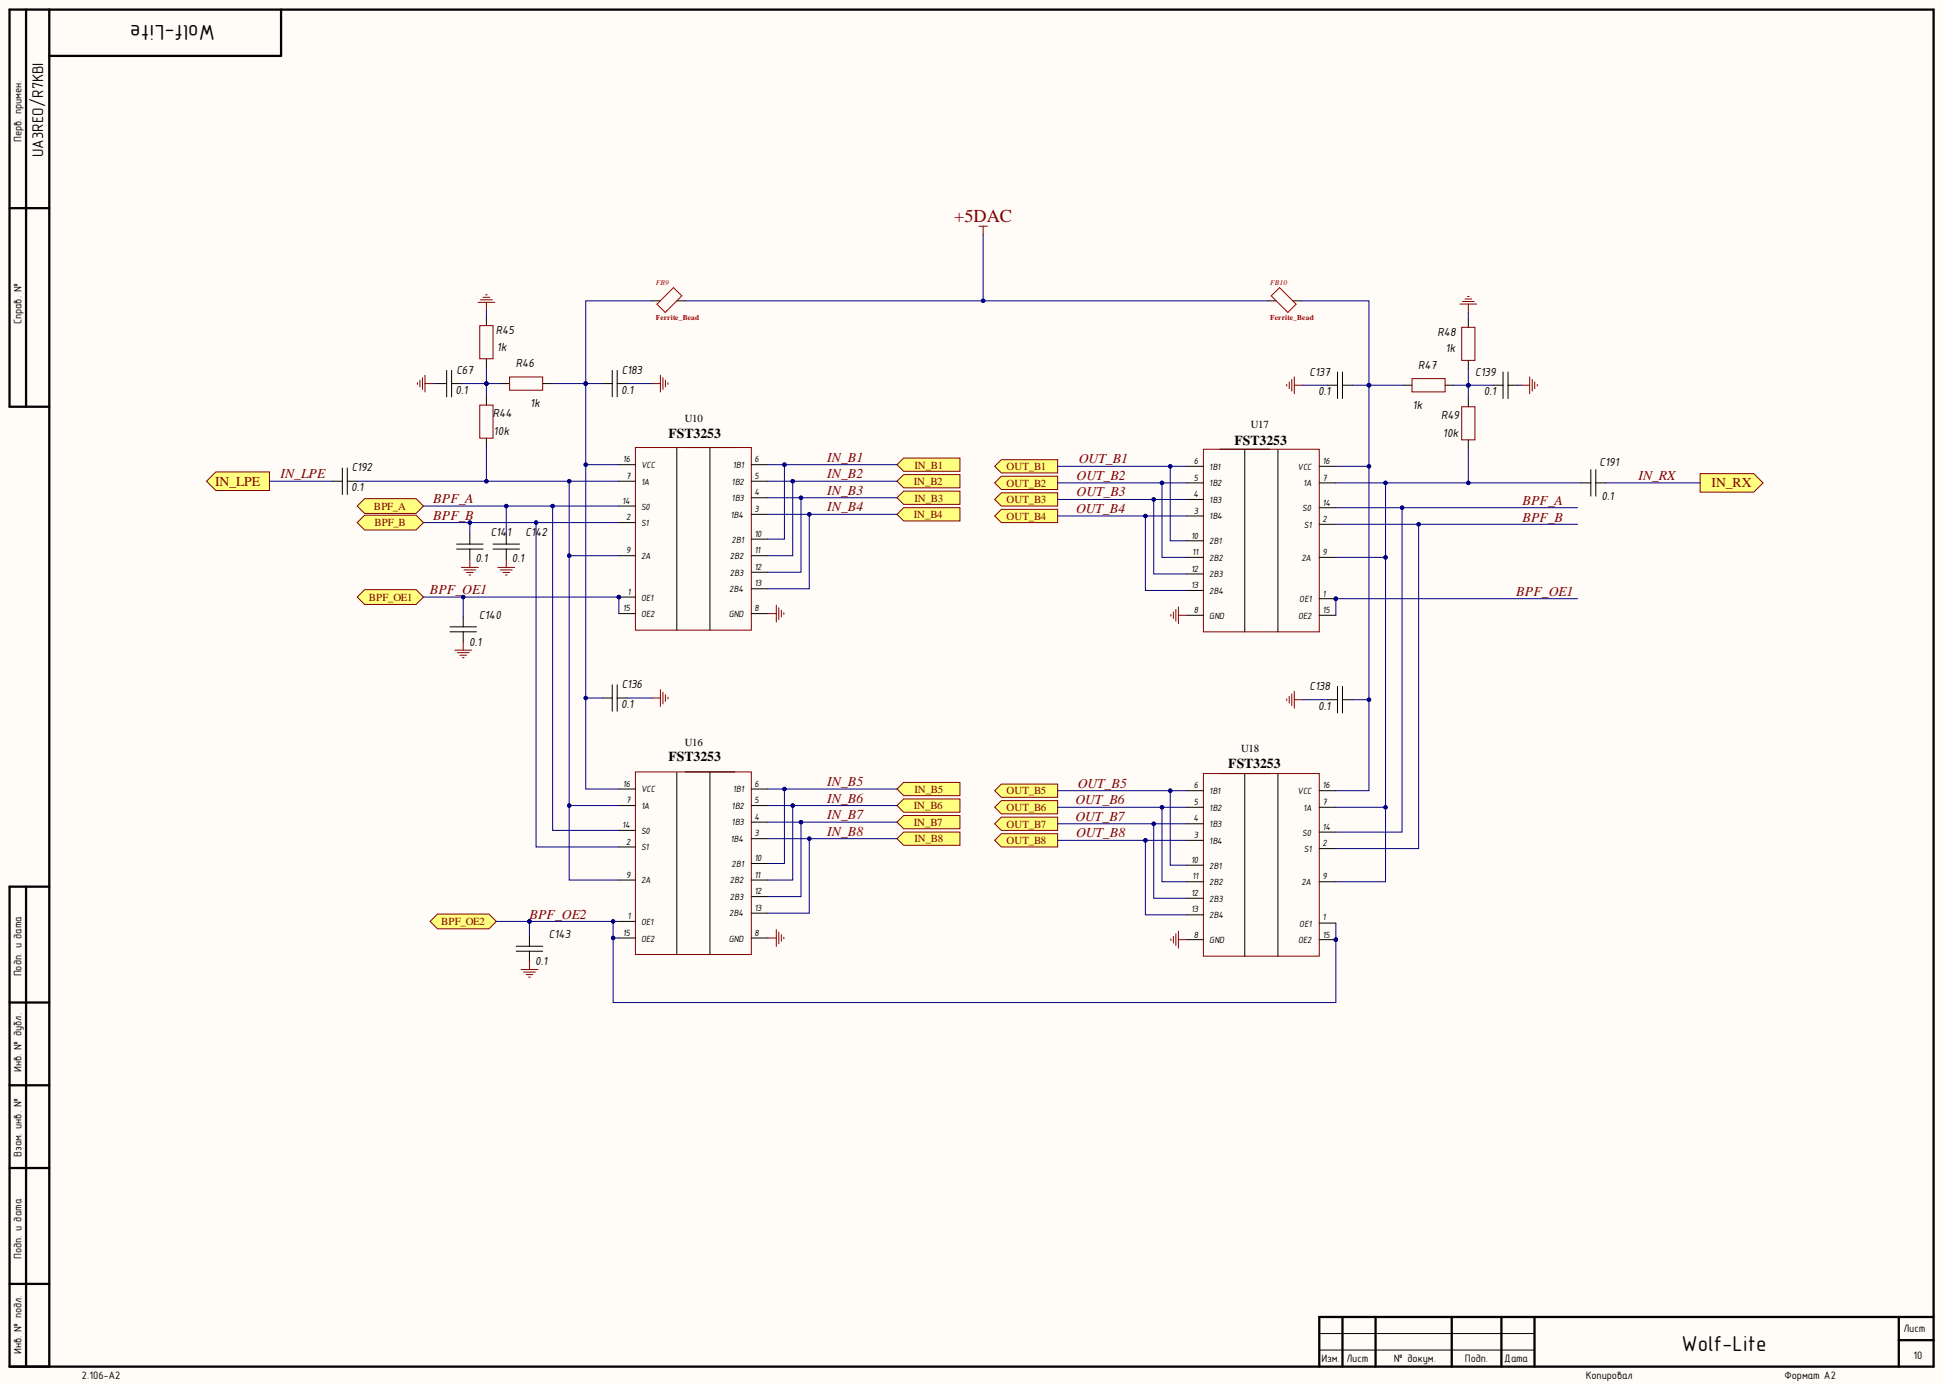
[picture p212: page 10]

Инв. № подл. Инв. № дубл. Подп. и дата Взам. инв. № Подп. и дата Перв. примен. Справ. №

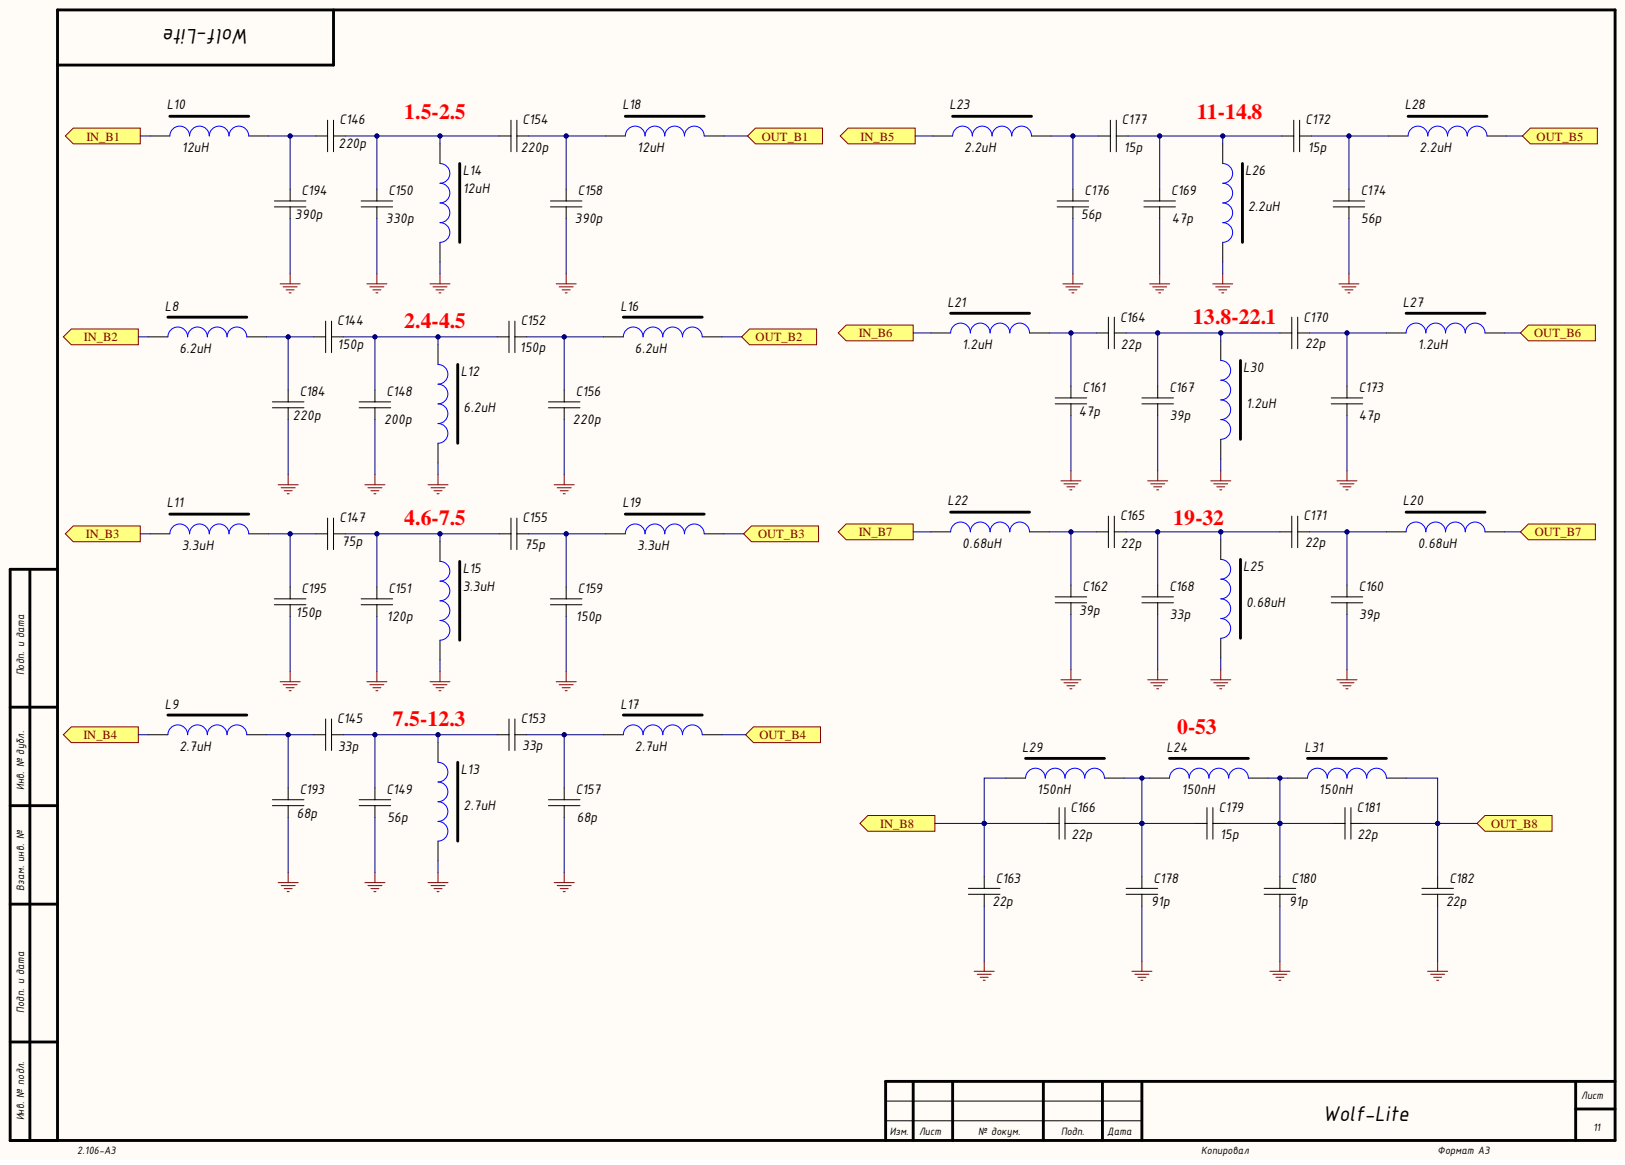
[picture p213: page 11]

Инв. № подл. Инв. № дубл. Подп. и дата Взам. инв. № Подп. и дата

Wolf-Lite

Изм. | Лист | № докум. | Подп. | Дата

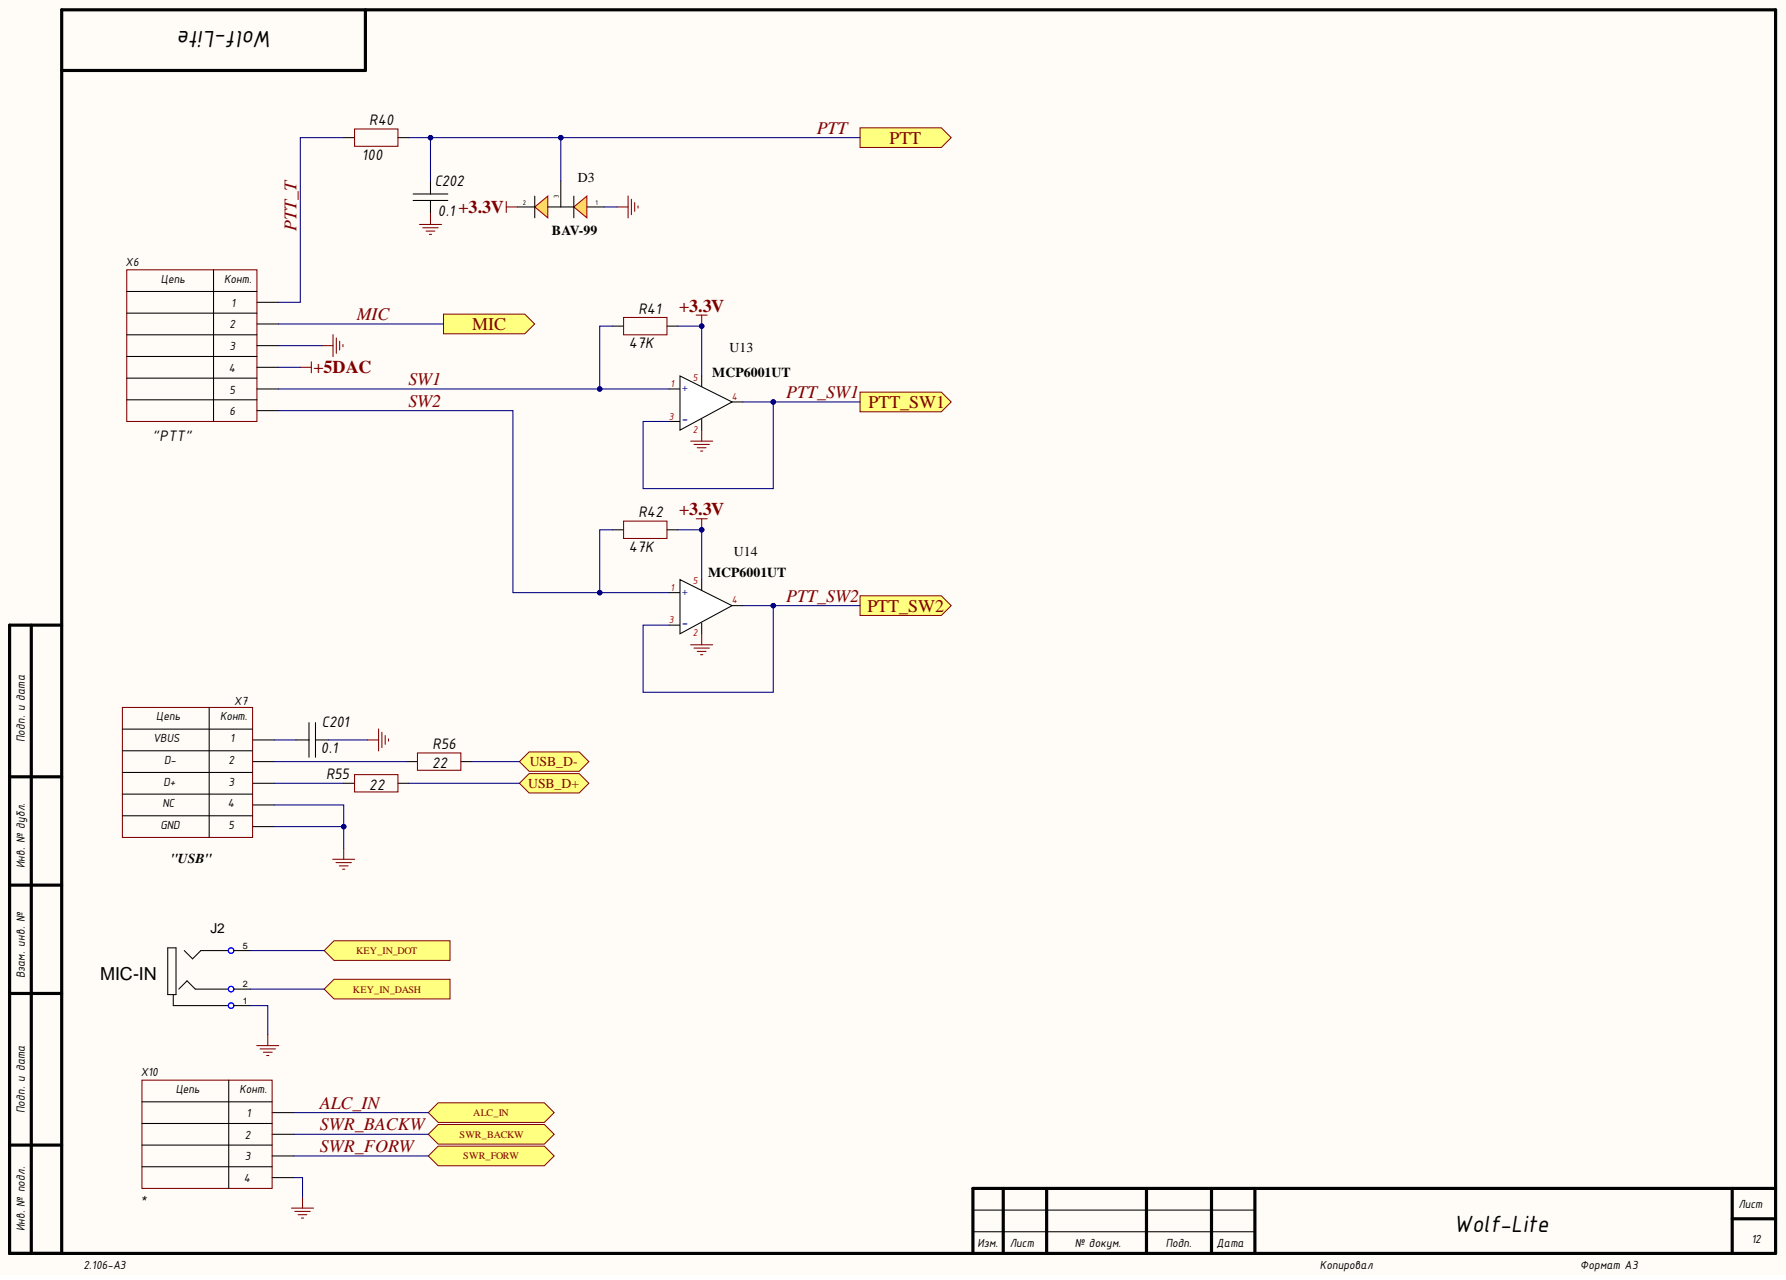
[picture p214: page 12]

Цепь | Конт.

Инв. № подл. Инв. № дубл. Подп. и дата Взам. инв. № Подп. и дата

VBUS | 1

GND | 5

Wolf-Lite

Изм. | Лист | № докум. | Подп. | Дата
