donatukas/Volf-TRX/Schematic/Wolf-X1/Scheme/X1_PA_V0.3.pdf

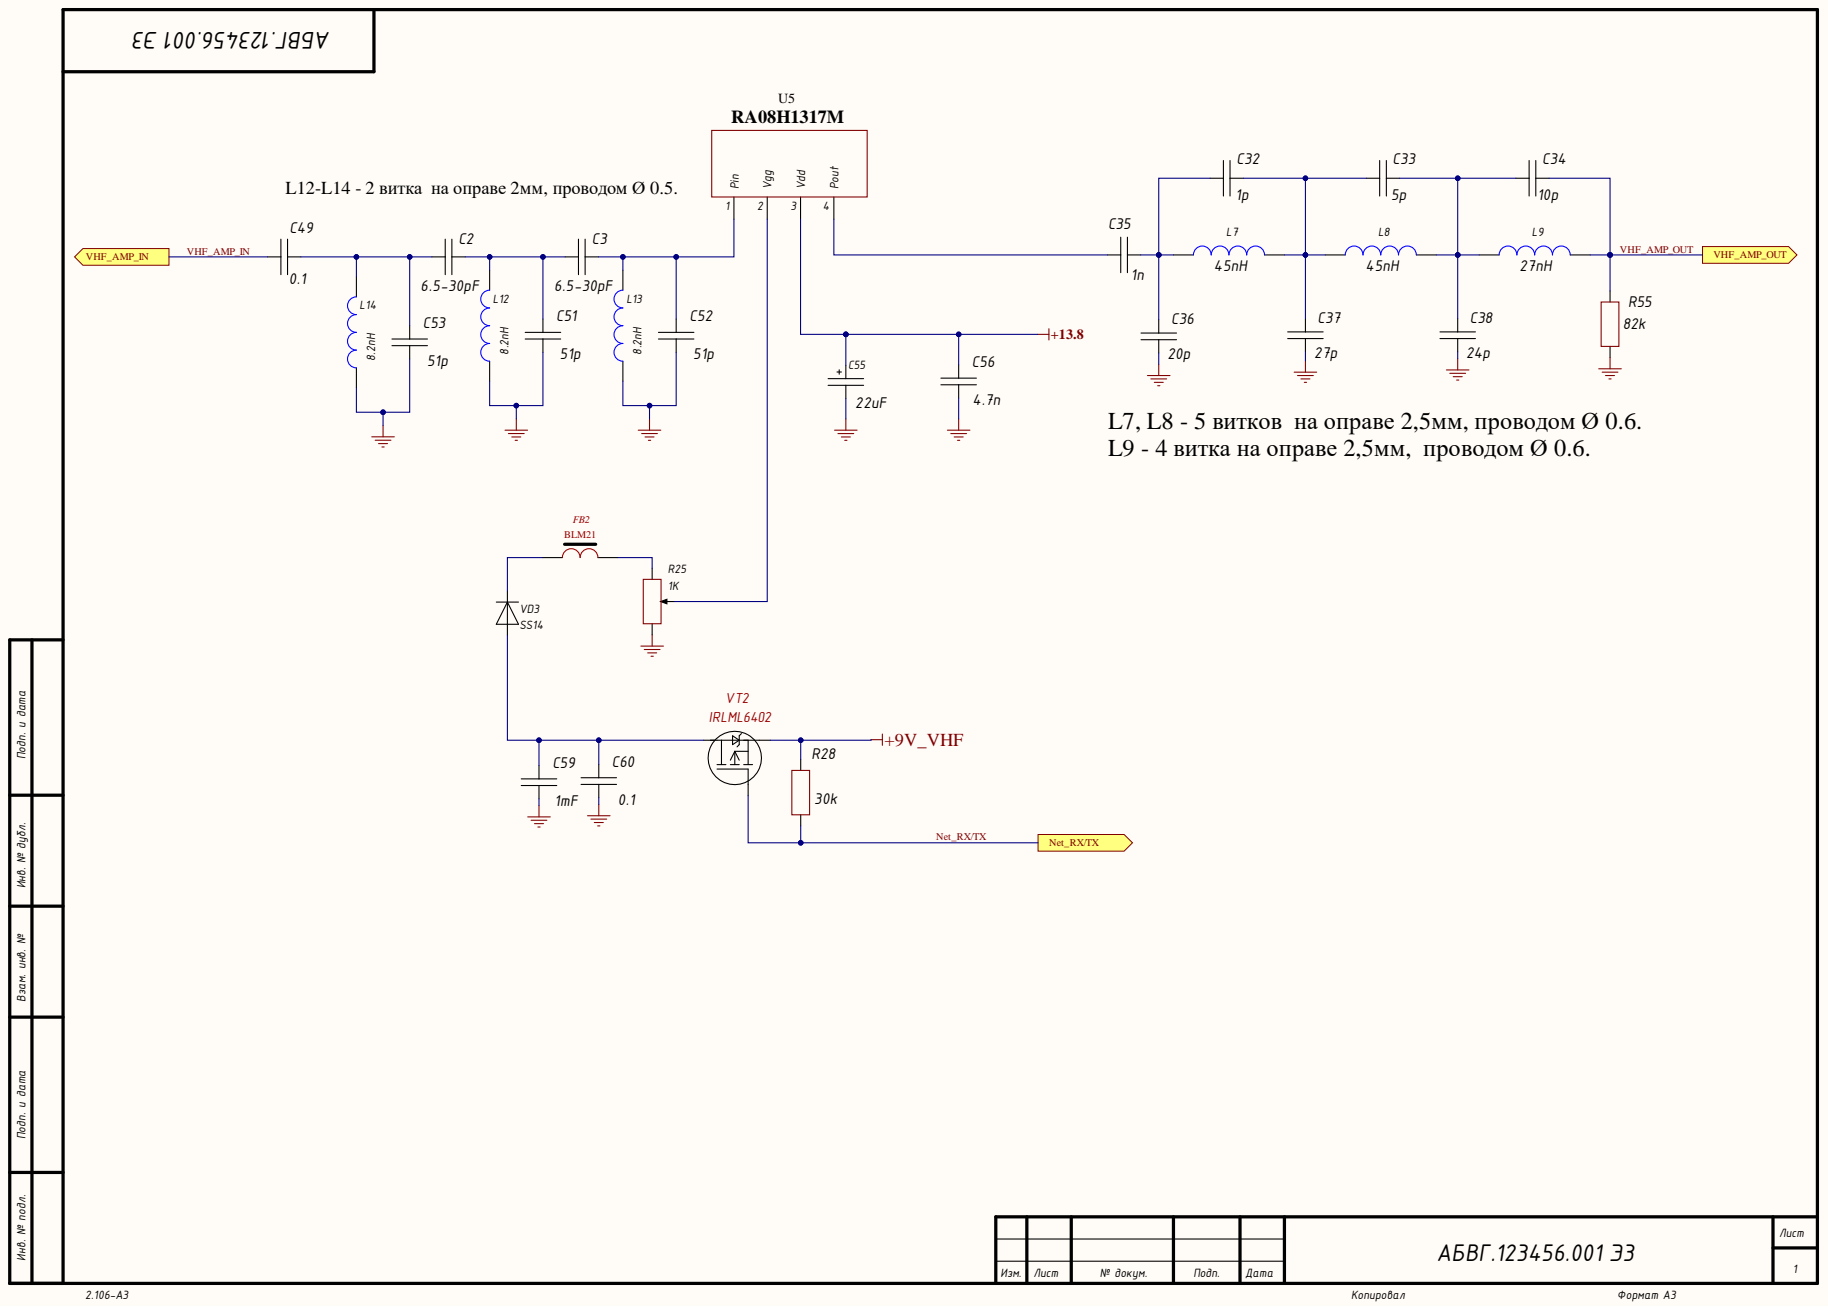
[picture p231: page 1]

L12-L14 - 2 витка на оправе 2мм, проводом Ø 0.5.

L7, L8 - 5 витков на оправе 2,5мм, проводом Ø 0.6.
L9 - 4 витка на оправе 2,5мм, проводом Ø 0.6.

Инв. № подл. Инв. № дубл. Подп. и дата Взам. инв. № Подп. и дата

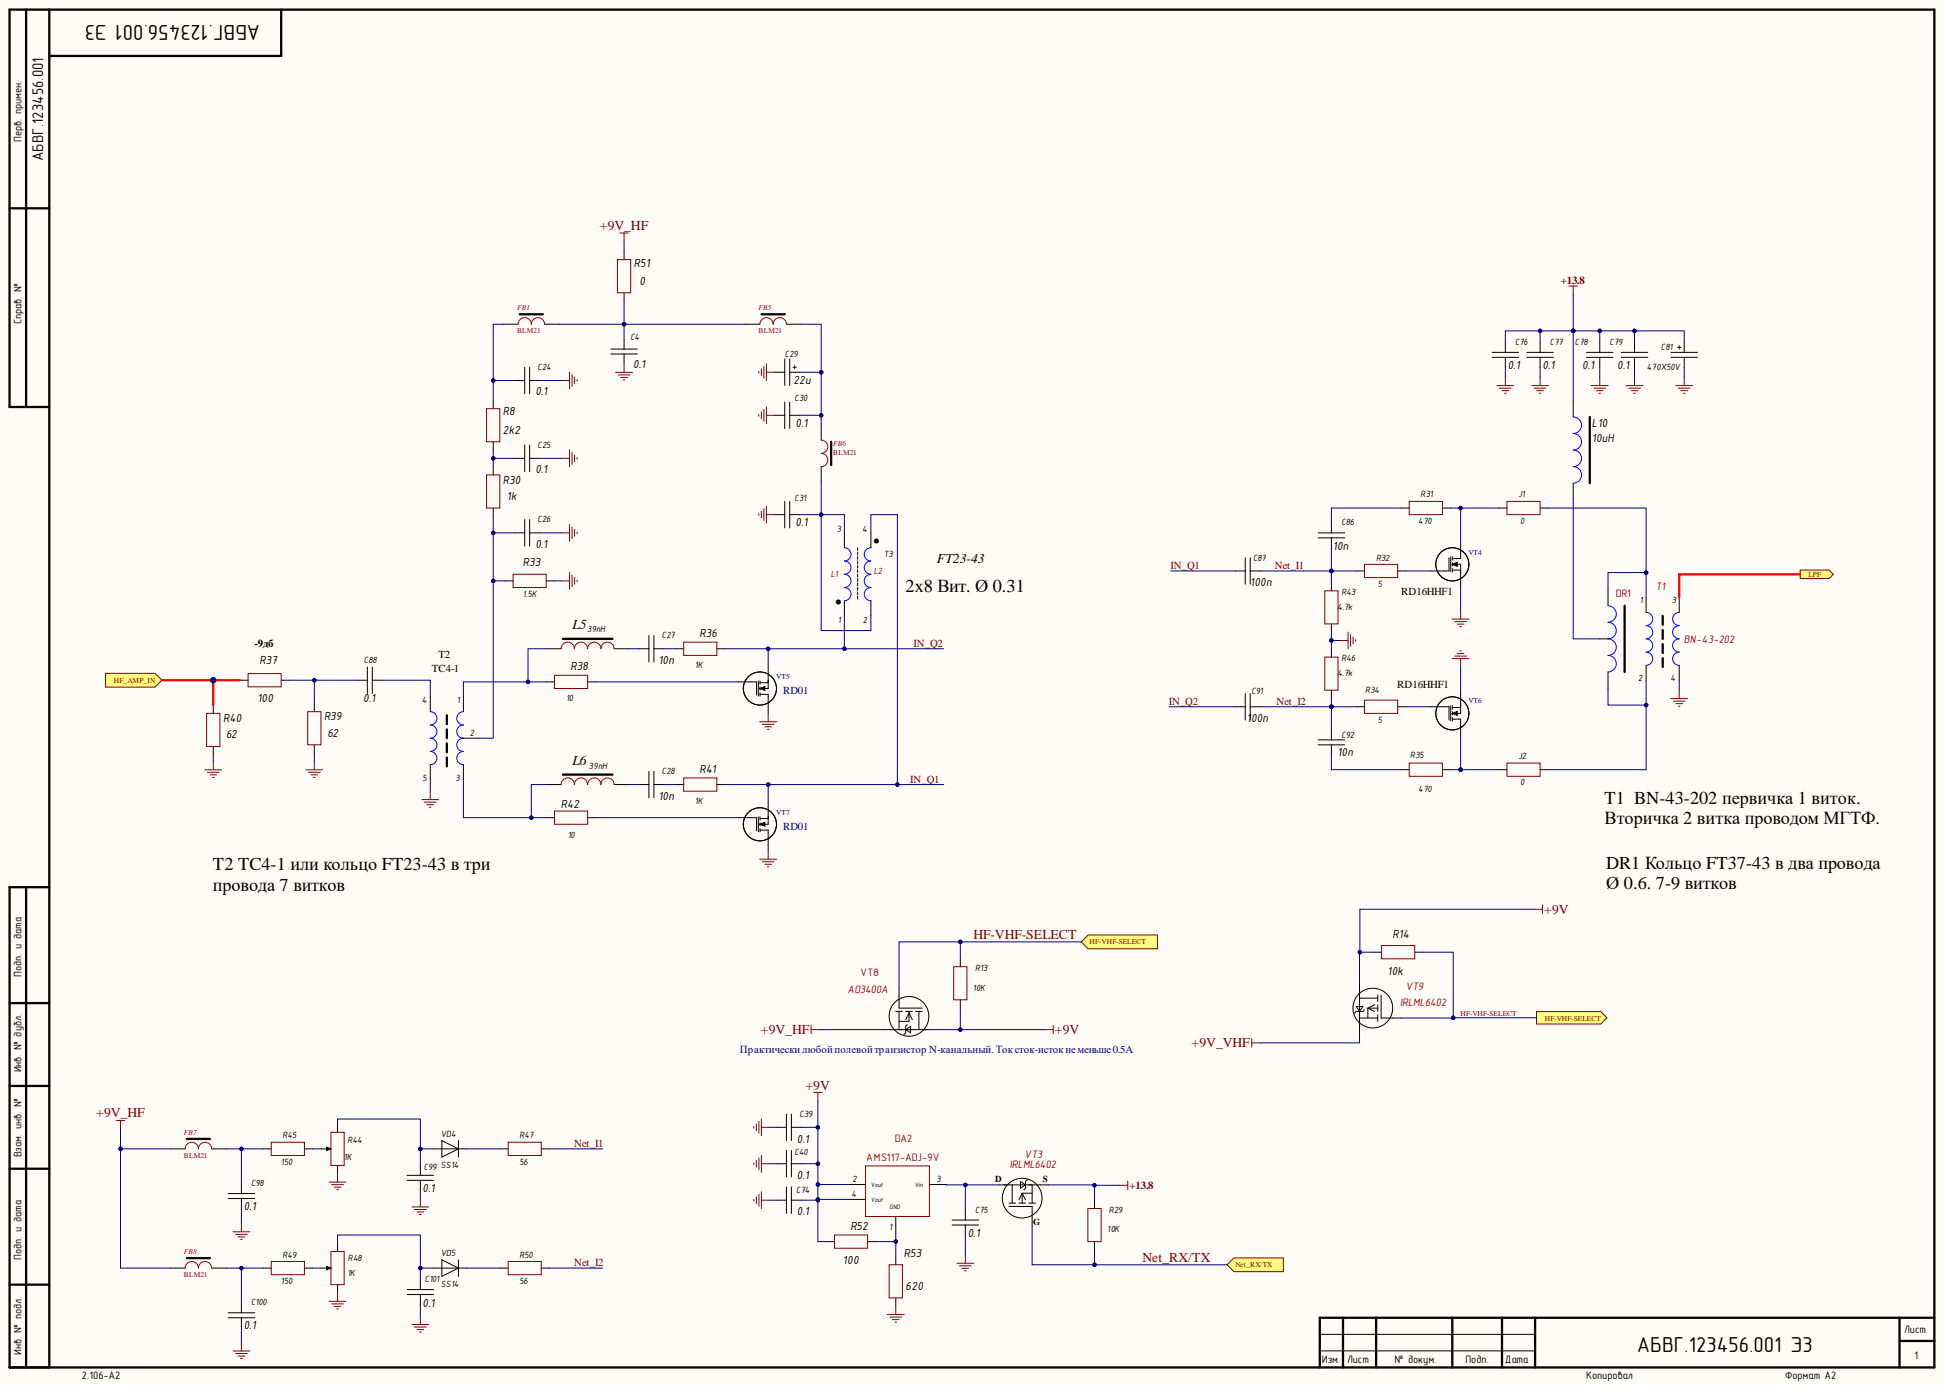
[picture p232: page 2]

Инв. № подл. Инв. № дубл. Подп. и дата Взам. инв. № Подп. и дата Перв. примен. Справ. №

T1 BN-43-202 первичка 1 виток.
Вторичка 2 витка проводом МГТФ.

HF-VHF-SELECT

Практически любой полевой транзистор N-канальный. Ток сток-исток неменьше 0.5А

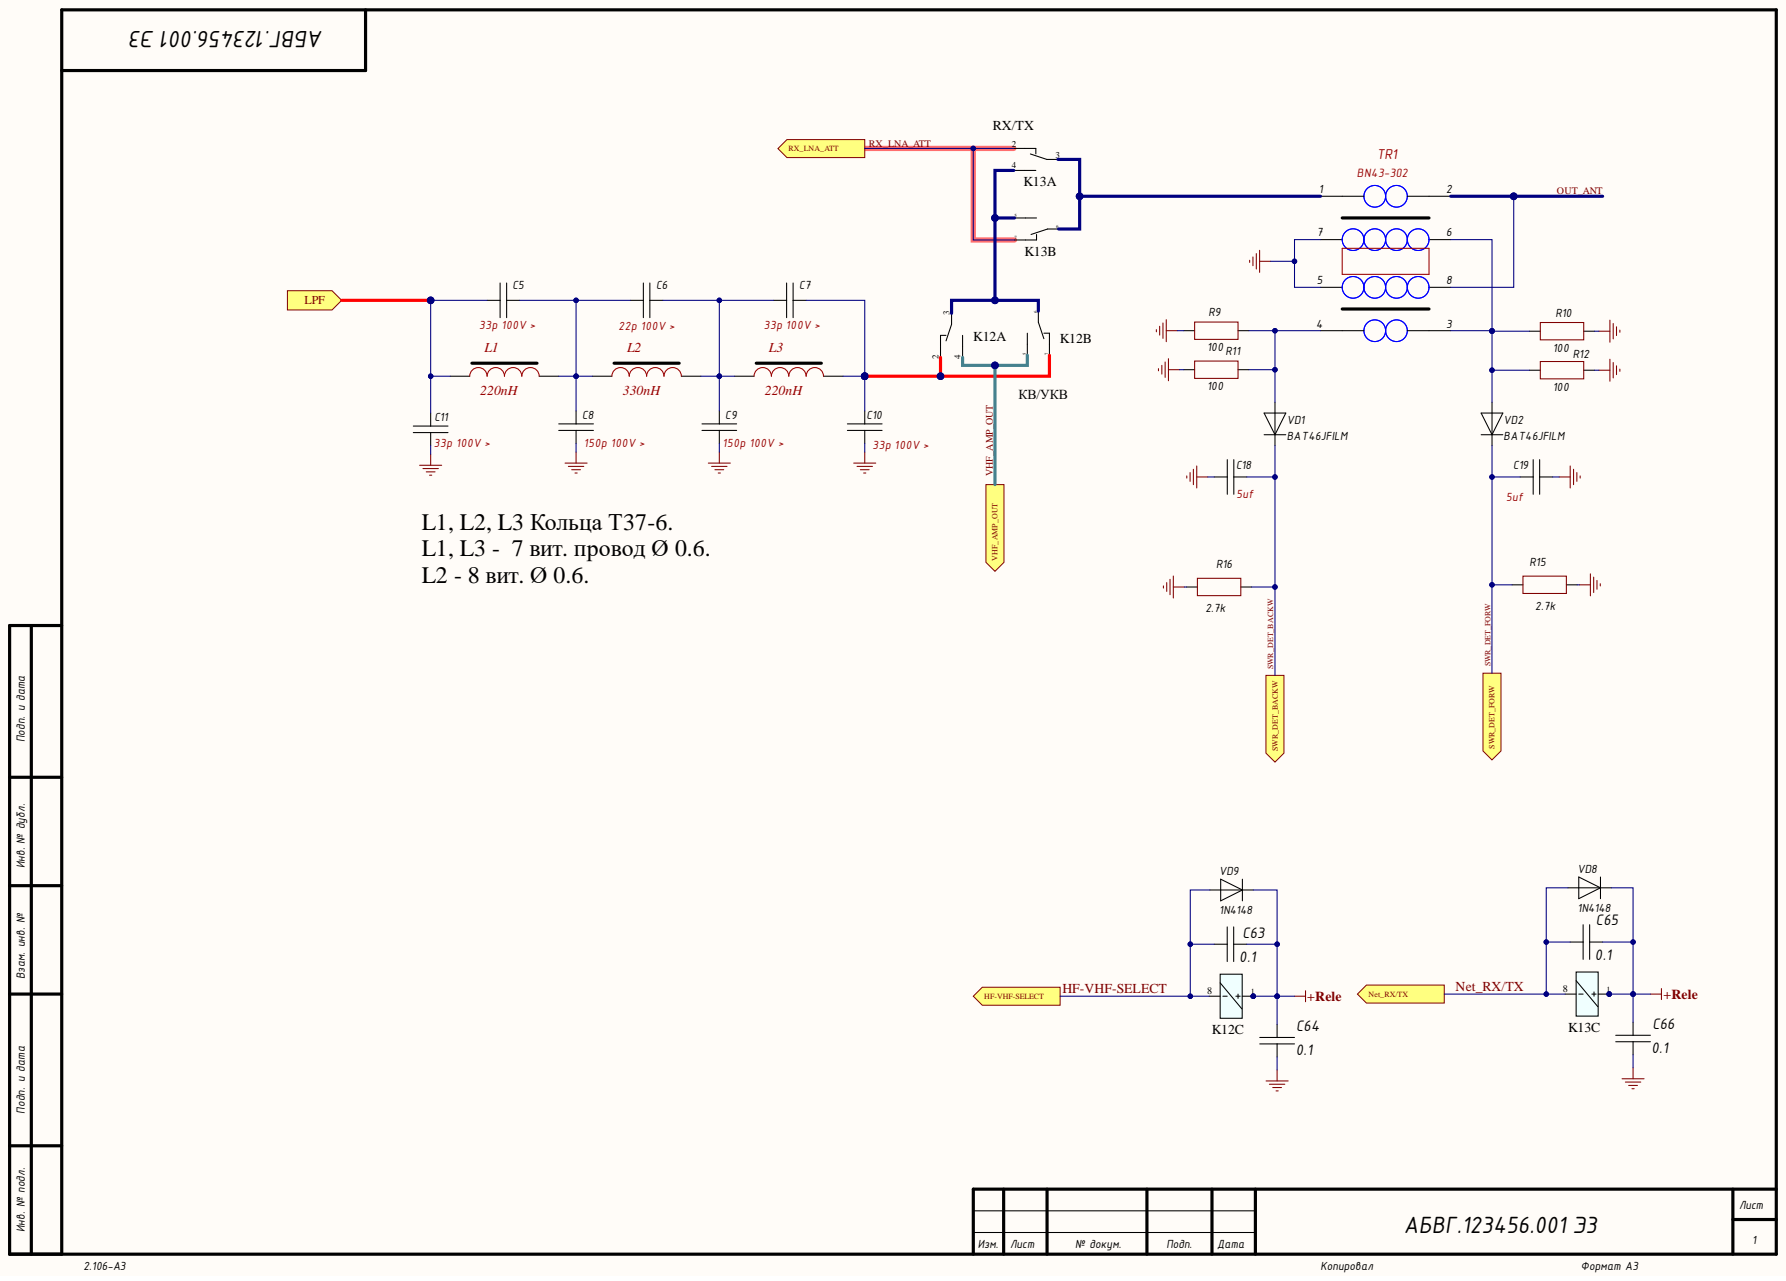
[picture p233: page 3]

Инв. № подл. Инв. № дубл. Подп. и дата Взам. инв. № Подп. и дата

+Rele HF-VHF-SELECT

АБВГ.123456.001 Э3

Изм. | Лист | № докум. | Подп. | Дата

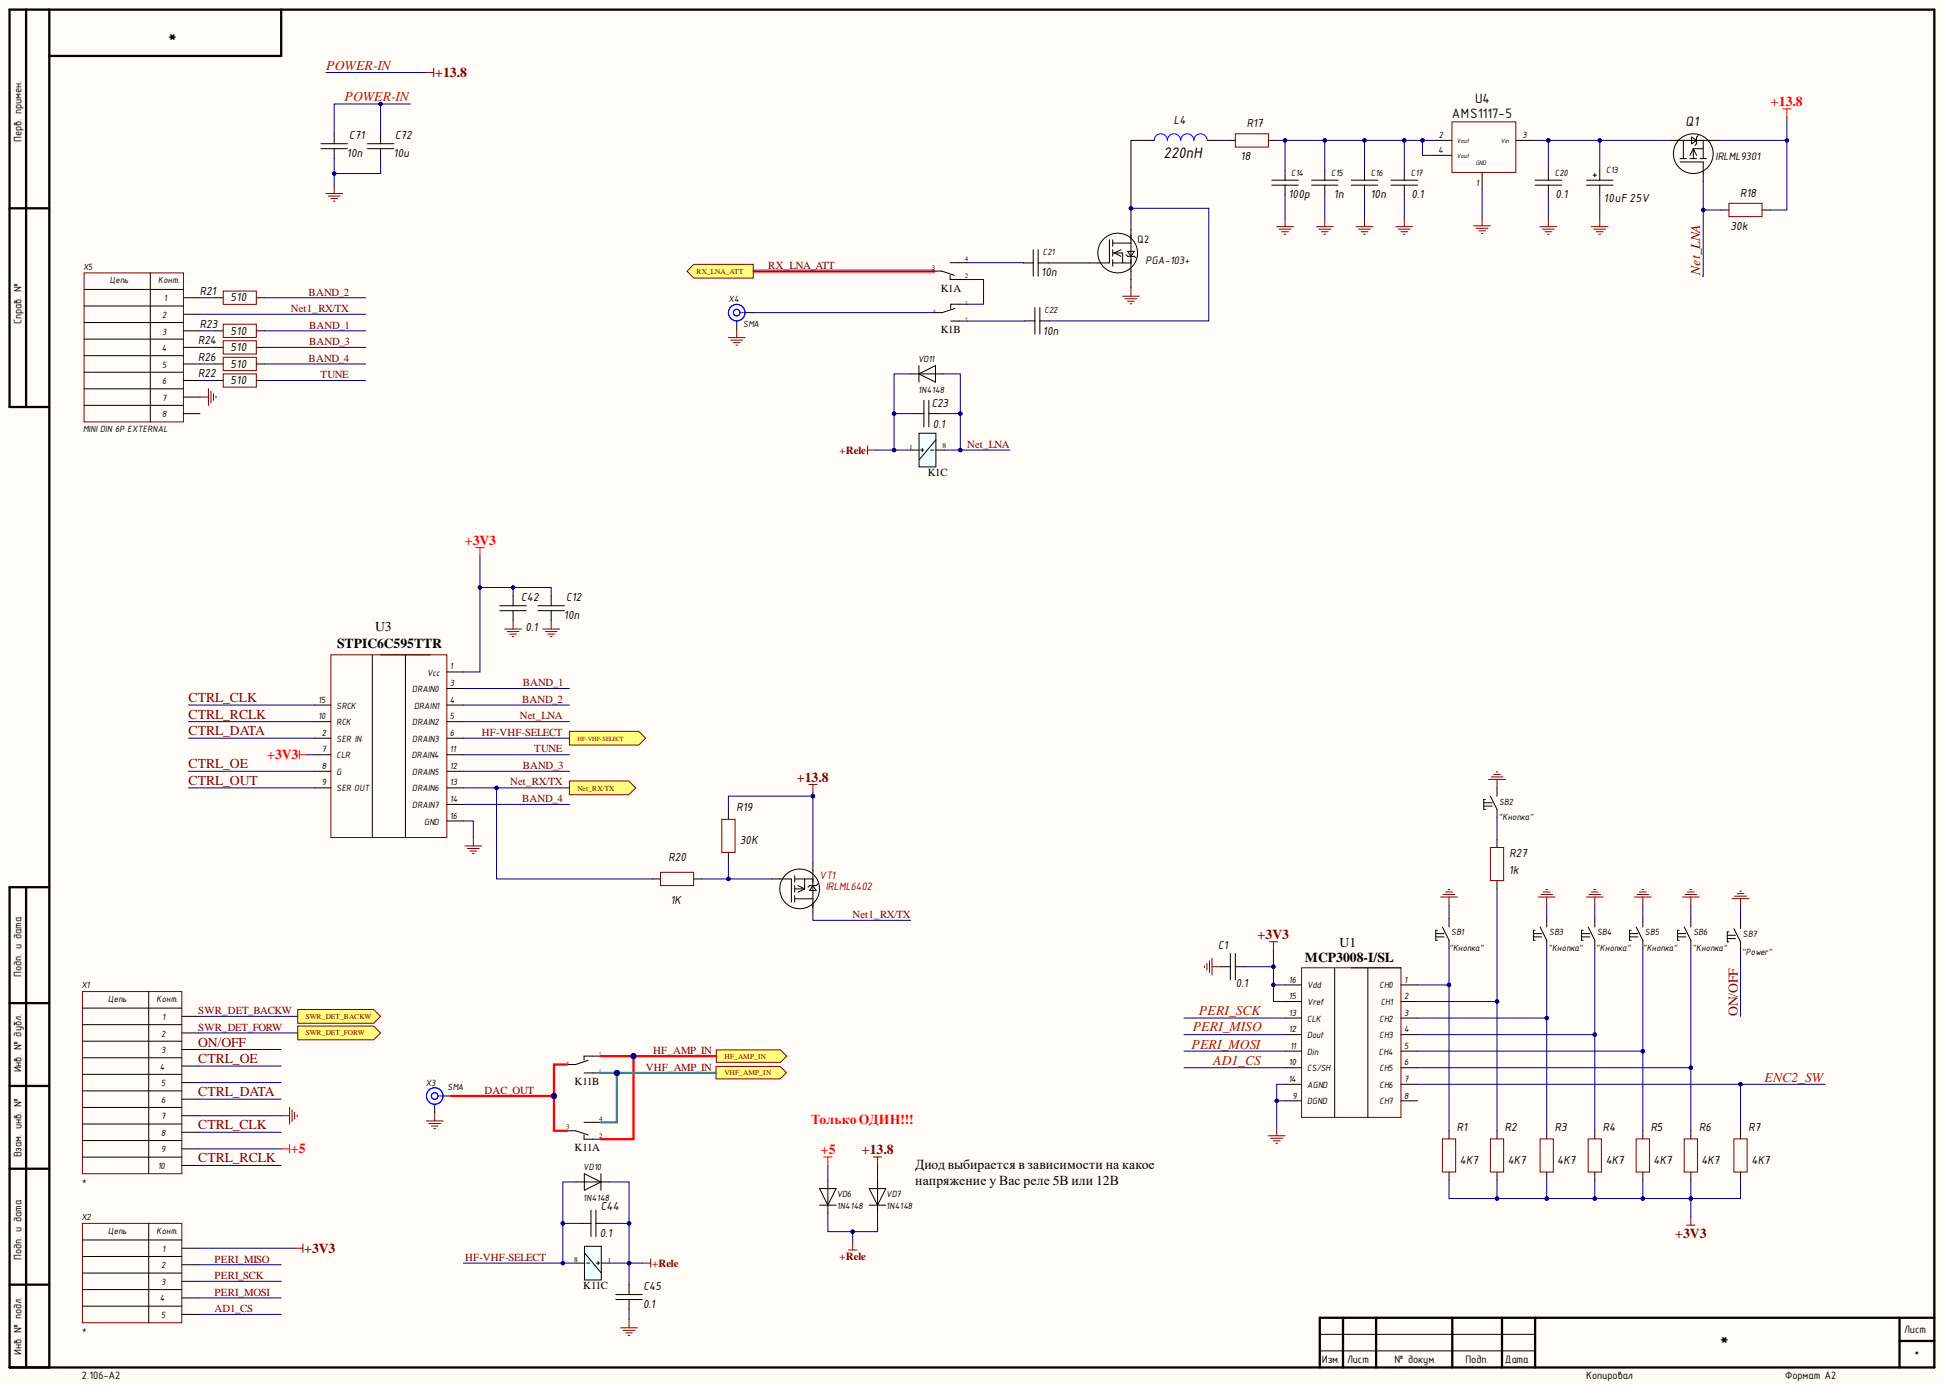
[picture p234: page 4]

Инв. № подл. Инв. № дубл. Подп. и дата Взам. инв. № Подп. и дата Перв. примен. Справ. №

Цепь | Конт.

Диод выбирается в зависимости на какое
напряжение у Вас реле 5В или 12В
