donatukas/Volf-TRX/STM32/Src/lcd_driver_ST7789.h

#ifndef _LCDDRIVER_ST7789_H_
#include "settings.h"
#if defined(LCD_ST7789)
#define _LCDDRIVER_ST7789_H_

#define ST7789_SPI_PORT hspi4
extern SPI_HandleTypeDef ST7789_SPI_PORT;

/* Pin connection*/
#define ST7789_RST_PORT LCD_RST_GPIO_Port
#define ST7789_RST_PIN LCD_RST_Pin
#define ST7789_DC_PORT LCD_DC_GPIO_Port
#define ST7789_DC_PIN LCD_DC_Pin
#define ST7789_CS_PORT LCD_CS_GPIO_Port
#define ST7789_CS_PIN LCD_CS_Pin

/* Basic operations */
#define ST7789_RST_Clr() HAL_GPIO_WritePin(ST7789_RST_PORT, ST7789_RST_PIN, GPIO_PIN_RESET)
#define ST7789_RST_Set() HAL_GPIO_WritePin(ST7789_RST_PORT, ST7789_RST_PIN, GPIO_PIN_SET)

#define ST7789_DC_Clr() HAL_GPIO_WritePin(ST7789_DC_PORT, ST7789_DC_PIN, GPIO_PIN_RESET)
#define ST7789_DC_Set() HAL_GPIO_WritePin(ST7789_DC_PORT, ST7789_DC_PIN, GPIO_PIN_SET)

#define ST7789_Select() HAL_GPIO_WritePin(ST7789_CS_PORT, ST7789_CS_PIN, GPIO_PIN_RESET)
#define ST7789_UnSelect() HAL_GPIO_WritePin(ST7789_CS_PORT, ST7789_CS_PIN, GPIO_PIN_SET)

// LCD dimensions defines
#define LCD_WIDTH 320
#define LCD_HEIGHT 240
#define LCD_TYPE_SPI true
#define LCD_SMALL_INTERFACE true

// ST7735S LCD commands
#define LCD_COMMAND_COLUMN_ADDR 0x2A
#define LCD_COMMAND_PAGE_ADDR 0x2B
#define LCD_COMMAND_GRAM 0x2C

#define WHITE 0xFFFF
#define BLACK 0x0000
#define BLUE 0x001F
#define RED 0xF800
#define MAGENTA 0xF81F
#define GREEN 0x07E0
#define CYAN 0x7FFF
#define YELLOW 0xFFE0
#define GRAY 0X8430
#define BRED 0XF81F
#define GRED 0XFFE0
#define GBLUE 0X07FF
#define BROWN 0XBC40
#define BRRED 0XFC07
#define DARKBLUE 0X01CF
#define LIGHTBLUE 0X7D7C
#define GRAYBLUE 0X5458

#define LIGHTGREEN 0X841F
#define LGRAY 0XC618
#define LGRAYBLUE 0XA651
#define LBBLUE 0X2B12

/* Control Registers and constant codes */
#define ST7789_NOP 0x00
#define ST7789_SWRESET 0x01
#define ST7789_RDDID 0x04
#define ST7789_RDDST 0x09

#define ST7789_SLPIN 0x10
#define ST7789_SLPOUT 0x11
#define ST7789_PTLON 0x12
#define ST7789_NORON 0x13

#define ST7789_INVOFF 0x20
#define ST7789_INVON 0x21
#define ST7789_DISPOFF 0x28
#define ST7789_DISPON 0x29
#define ST7789_CASET 0x2A
#define ST7789_RASET 0x2B
#define ST7789_RAMWR 0x2C
#define ST7789_RAMRD 0x2E

#define ST7789_PTLAR 0x30
#define ST7789_COLMOD 0x3A
#define ST7789_MADCTL 0x36

/**
 * Memory Data Access Control Register (0x36H)
 * MAP:     D7  D6  D5  D4  D3  D2  D1  D0
 * param:   MY  MX  MV  ML  RGB MH  -   -
 *
 */

/* Page Address Order ('0': Top to Bottom, '1': the opposite) */
#define ST7789_MADCTL_MY 0x80
/* Column Address Order ('0': Left to Right, '1': the opposite) */
#define ST7789_MADCTL_MX 0x40
/* Page/Column Order ('0' = Normal Mode, '1' = Reverse Mode) */
#define ST7789_MADCTL_MV 0x20
/* Line Address Order ('0' = LCD Refresh Top to Bottom, '1' = the opposite) */
#define ST7789_MADCTL_ML 0x10
/* RGB/BGR Order ('0' = RGB, '1' = BGR) */
#define ST7789_MADCTL_RGB 0x00

#define ST7789_RDID1 0xDA
#define ST7789_RDID2 0xDB
#define ST7789_RDID3 0xDC
#define ST7789_RDID4 0xDD

#define ST7789_COLOR_MODE_16bit 0x55 //  RGB565 (16bit)
#define ST7789_COLOR_MODE_18bit 0x66 //  RGB666 (18bit)

#ifndef _swap_int16_t
#define _swap_int16_t(a, b) \
	{                         \
		int16_t t = a;          \
		a = b;                  \
		b = t;                  \
	}
#endif

#endif
#endif
