donatukas/Volf-TRX/STM32/WOLF-2/Inc/hardware.h

#ifndef __HARDWARE_H
#define __HARDWARE_H

#include "arm_math_types.h"
#include "main.h"
#include "stm32h7xx.h"
#include <stdbool.h>

// features
#define HRDW_HAS_MDMA true
#define HRDW_HAS_SD true
#define HRDW_HAS_DMA2D true
#define HRDW_HAS_JPEG true
#define HRDW_HAS_WIFI true
#define HRDW_HAS_USB_DEBUG true
#define HRDW_HAS_USB_CAT true
#define HRDW_HAS_USB_IQ true
#define HRDW_HAS_DUAL_RX true
#define HRDW_HAS_FULL_FFT_BUFFER true
#define HRDW_USB_AUDIO_BITS 24
#define HRDW_AUDIO_CODEC_WM8731 true
#define HRDW_HAS_ENC3 true
#define HRDW_HAS_ENC4 true
#define HRDW_HAS_LNA_HF false
#define HRDW_HAS_LNA_VHF true
#define HRDW_HAS_RFFC2071_MIXER false
#define HRDW_HAS_VHF_MIXER HRDW_HAS_RFFC2071_MIXER

#define HRDW_DEBUG_ON_CAT_PORT false

// hardware includes
#include "RFFC2071.h"

// settings
#define ADC_CLOCK (122880000LL + CALIBRATE.VCXO_correction)                 // ADC generator frequency
#define DAC_CLOCK (HRDW_DAC_PLL_selected ? DAC_CLOCK_PLL2 : DAC_CLOCK_PLL1) // DAC generator frequency
#define DAC_CLOCK_PLL1 (ADC_CLOCK * 5LL / 8LL)                              // DAC generator frequency PLL 1 (76.800.000)
#define DAC_CLOCK_PLL2 (ADC_CLOCK * 7LL / 8LL)                              // DAC generator frequency PLL 2 (107.520.000)
#define MAX_TX_FREQ_HZ (DAC_CLOCK_PLL2 * 2)                                 // Maximum transmission frequency
#define ADC_FULL_SCALE 65536                                                // maximum signal amplitude in the ADC // powf (2, ADC_BITS)
#define FLOAT_FULL_SCALE_POW 4
#define DCDC_FREQ_0 960000
#define DCDC_FREQ_1 1200000
#define ADC_INPUT_IMPEDANCE 200.0f // 50ohm -> 1:4 trans
#define ADC_RANGE 2.25f
#define ADC_RANGE_PGA 1.5f
#define ADC_LNA_GAIN_DB 25.0f
#define ADC_DRIVER_GAIN_DB 25.5f
#define ADC_PGA_GAIN_DB 3.522f

// instances
#define HRDW_AUDIO_CODEC_I2S hi2s3
#define HRDW_WSPR_TIMER htim2
#define HRDW_WIFI_UART huart6
#define HRDW_FSMC_LCD hsram1
#define HRDW_CRC_HANDLE hcrc
#define HRDW_JPEG_HANDLE hjpeg
// #define HRDW_LCD_SPI
#define HRDW_IWDG hiwdg1
#define HRDW_LCD_FSMC_COPY_DMA hdma_memtomem_dma2_stream5
#define HRDW_LCD_WTF_DOWN_MDMA hmdma_mdma_channel3_sw_0
#define HRDW_MEMCPY_MDMA hmdma_mdma_channel0_sw_0
#define HRDW_MEMSET_MDMA hmdma_mdma_channel4_sw_0
#define HRDW_AUDIO_COPY_MDMA hmdma_mdma_channel1_sw_0
#define HRDW_AUDIO_COPY2_MDMA hmdma_mdma_channel2_sw_0

// SPI Speed
#define SPI_FRONT_UNIT_PRESCALER (!HRDW_SPI_Internal_STM32_Clock ? SPI_BAUDRATEPRESCALER_4 : SPI_BAUDRATEPRESCALER_32)
#define SPI_SD_PRESCALER (!HRDW_SPI_Internal_STM32_Clock ? SPI_BAUDRATEPRESCALER_2 : SPI_BAUDRATEPRESCALER_16)
#define SPI_EEPROM_PRESCALER (!HRDW_SPI_Internal_STM32_Clock ? SPI_BAUDRATEPRESCALER_4 : SPI_BAUDRATEPRESCALER_32)

// buffers
#define CODEC_AUDIO_BUFFER_SIZE (AUDIO_BUFFER_SIZE * 2)          // the size of the circular buffer is 2 times larger than the FPGA buffer, we work in the first half, then on the other
#define CODEC_AUDIO_BUFFER_HALF_SIZE AUDIO_BUFFER_SIZE           // half buffer
#define AUDIO_BUFFER_SIZE (192 * 2)                              // the size of the buffer for working with sound 48kHz
#define AUDIO_BUFFER_HALF_SIZE (AUDIO_BUFFER_SIZE / 2)           // buffer size for working with sound 48kHz
#define FPGA_TX_IQ_BUFFER_SIZE AUDIO_BUFFER_SIZE                 // size of TX data buffer for FPGA
#define FPGA_TX_IQ_BUFFER_HALF_SIZE (FPGA_TX_IQ_BUFFER_SIZE / 2) // half the size of the TX data buffer for FPGA
#define FPGA_RX_IQ_BUFFER_SIZE FPGA_TX_IQ_BUFFER_SIZE            // size of the RX data buffer from the PGA
#define FPGA_RX_IQ_BUFFER_HALF_SIZE (FPGA_RX_IQ_BUFFER_SIZE / 2) // half the size of the RX data buffer from the PGA

// macros
#define FPGA_setGPIOBusInput GPIOA->MODER = 2861629440
#define FPGA_setGPIOBusOutput GPIOA->MODER = 2861651285

// types
typedef struct {
	float32_t Load; /*!< CPU load percentage */
	uint32_t WCNT;  /*!< Number of working cycles in one period. Meant for private use */
	uint32_t SCNT;  /*!< Number of sleeping cycles in one period. Meant for private use */
	uint32_t SINC;
} CPULOAD_t;

// variables
extern bool HRDW_SPI_Internal_STM32_Clock;
extern bool HRDW_SPI_Periph_busy;
extern volatile bool HRDW_SPI_Locked;
extern bool dma_memset32_busy;
extern bool dma_memcpy32_busy;
extern CPULOAD_t CPU_LOAD;
extern bool HRDW_DAC_PLL_selected;

// methods
extern void CPULOAD_Init(void);
extern void CPULOAD_GoToSleepMode(void);
extern void CPULOAD_WakeUp(void);
extern void CPULOAD_Calc(void);
extern void HRDW_Init(void);
extern float32_t HRDW_getCPUTemperature(void);
extern float32_t HRDW_getCPUVref(void);
extern uint32_t HRDW_getAudioCodecTX_DMAIndex(void);
extern uint32_t HRDW_getAudioCodecRX_DMAIndex(void);
extern bool HRDW_FrontUnit_SPI(uint8_t *out_data, uint8_t *in_data, uint32_t count, bool hold_cs);
extern bool HRDW_FrontUnit2_SPI(uint8_t *out_data, uint8_t *in_data, uint32_t count, bool hold_cs);
extern bool HRDW_FrontUnit3_SPI(uint8_t *out_data, uint8_t *in_data, uint32_t count, bool hold_cs);
extern bool HRDW_EEPROM_SPI(uint8_t *out_data, uint8_t *in_data, uint32_t count, bool hold_cs);
extern bool HRDW_SD_SPI(uint8_t *out_data, uint8_t *in_data, uint32_t count, bool hold_cs);
extern void HRDW_GoToInternalSPIClock(void);
extern uint8_t HARDW_GetAntCount(void);

#endif
