donatukas/Volf-TRX/FPGA/FPGA-Wolf-10-15k/TX_CLK_CTRL/TX_CLK_CTRL_inst.v

	TX_CLK_CTRL u0 (
		.inclk1x   (<connected-to-inclk1x>),   //  altclkctrl_input.inclk1x
		.inclk0x   (<connected-to-inclk0x>),   //                  .inclk0x
		.clkselect (<connected-to-clkselect>), //                  .clkselect
		.outclk    (<connected-to-outclk>)     // altclkctrl_output.outclk
	);
