donatukas/Volf-TRX/STM32/Src/agc.c

#include "agc.h"
#include "audio_filters.h"
#include "settings.h"
#include "trx_manager.h"
#include "vad.h"

// Private variables
static IRAM2 AGC_RX_Instance AGC_RX1 = {0};
#if HRDW_HAS_DUAL_RX
static IRAM2 AGC_RX_Instance AGC_RX2 = {0};
#endif
static IRAM2 AGC_TX_Instance AGC_TX = {0};

float32_t AGC_SCREEN_maxGain = 1.0f;
float32_t AGC_SCREEN_currentGain = 0.0f;

// Run AGC on data block
void DoRxAGC(float32_t *agcBuffer_i, float32_t *agcBuffer_q, uint_fast16_t blockSize, AUDIO_PROC_RX_NUM rx_id, uint8_t nr_type, TRX_MODE mode, bool stereo) {
	// RX1 or RX2
	AGC_RX_Instance *AGC = &AGC_RX1;
	bool VAD_Muting = VAD_RX1_Muting;

#if HRDW_HAS_DUAL_RX
	if (rx_id == AUDIO_RX2) {
		AGC = &AGC_RX2;
		VAD_Muting = VAD_RX2_Muting;
	}
#endif

	// higher speed in settings - higher speed of AGC processing
	float32_t RX_AGC_STEPSIZE_UP = 0.0f;
	float32_t RX_AGC_STEPSIZE_DOWN = 0.0f;
	if (mode == TRX_MODE_CW) {
		RX_AGC_STEPSIZE_UP = 200.0f / (float32_t)TRX.RX_AGC_CW_speed;
		RX_AGC_STEPSIZE_DOWN = 20.0f / (float32_t)TRX.RX_AGC_CW_speed;
	} else {
		RX_AGC_STEPSIZE_UP = 1000.0f / (float32_t)TRX.RX_AGC_SSB_speed;
		RX_AGC_STEPSIZE_DOWN = 20.0f / (float32_t)TRX.RX_AGC_SSB_speed;
	}

	// do k-weighting (for LKFS)
	if (rx_id == AUDIO_RX1) {
#ifndef STM32F407xx
		arm_biquad_cascade_df2T_f32_single(&AGC_RX1_KW_HSHELF_FILTER, agcBuffer_i, AGC->agcBuffer_kw, blockSize);
		arm_biquad_cascade_df2T_f32_single(&AGC_RX1_KW_HPASS_FILTER, agcBuffer_i, AGC->agcBuffer_kw, blockSize);
#endif
	}
#if HRDW_HAS_DUAL_RX
	else {
		arm_biquad_cascade_df2T_f32_single(&AGC_RX2_KW_HSHELF_FILTER, agcBuffer_i, AGC->agcBuffer_kw, blockSize);
		arm_biquad_cascade_df2T_f32_single(&AGC_RX2_KW_HPASS_FILTER, agcBuffer_i, AGC->agcBuffer_kw, blockSize);
	}
#endif

	// do ring buffer
	static uint32_t ring_position = 0;
	// save new data to ring buffer
	dma_memcpy(&(AGC->ringbuffer[ring_position * blockSize]), agcBuffer_i, sizeof(float32_t) * blockSize);
	// move ring buffer index
	ring_position++;
	if (ring_position >= AGC_RINGBUFFER_TAPS_SIZE) {
		ring_position = 0;
	}
	// get old data to process
	if (!stereo) {
		dma_memcpy(agcBuffer_i, &(AGC->ringbuffer[ring_position * blockSize]), sizeof(float32_t) * blockSize);
	}

	// calculate the magnitude in dBFS
	float32_t AGC_RX_magnitude = 0;

#ifndef STM32F407xx
	arm_rms_f32(AGC->agcBuffer_kw, blockSize, &AGC_RX_magnitude);
#else
	arm_rms_f32(agcBuffer_i, blockSize, &AGC_RX_magnitude);
#endif

	if (AGC_RX_magnitude == 0.0f) {
		AGC_RX_magnitude = 0.001f;
	}
	float32_t full_scale_rate = AGC_RX_magnitude / FLOAT_FULL_SCALE_POW;
	float32_t AGC_RX_dBFS = rate2dbV(full_scale_rate);
	if (AGC->AGC_RX_dBFS_old > AGC_RX_dBFS) {
		AGC_RX_dBFS = AGC->AGC_RX_dBFS_old;
	}
	AGC->AGC_RX_dBFS_old = rate2dbV(full_scale_rate);

	// gain target
	float32_t gain_target = (float32_t)TRX.AGC_Gain_target_SSB;
	if (mode == TRX_MODE_CW) {
		gain_target = (float32_t)TRX.AGC_Gain_target_CW;
	}

	// move the gain one step
	if (!CODEC_Muting && !VAD_Muting) {
		float32_t diff = (gain_target - (AGC_RX_dBFS + AGC->need_gain_dB));

		// hold time limiter
		if (fabsf(diff) < (float32_t)TRX.RX_AGC_Hold_Limiter && AGC->hold_time < TRX.RX_AGC_Hold_Time) {
			AGC->hold_time += TRX.RX_AGC_Hold_Step_Up;
			if (AGC->hold_time > TRX.RX_AGC_Hold_Time) {
				AGC->hold_time = TRX.RX_AGC_Hold_Time;
			}
		}

		// move
		if (diff > 0) {
			if ((HAL_GetTick() - AGC->last_agc_peak_time) > AGC->hold_time) {
				AGC->need_gain_dB += diff / RX_AGC_STEPSIZE_UP;

				if (diff > (float32_t)TRX.RX_AGC_Hold_Limiter && AGC->hold_time > 0) {
					if (AGC->hold_time >= TRX.RX_AGC_Hold_Step_Down) {
						AGC->hold_time -= TRX.RX_AGC_Hold_Step_Down;
					} else {
						AGC->hold_time = 0;
					}
				}
			}
		} else {
			AGC->need_gain_dB += diff / RX_AGC_STEPSIZE_DOWN;
			AGC->last_agc_peak_time = HAL_GetTick();
		}

		// overload (clipping), sharply reduce the gain
		if ((AGC_RX_dBFS + AGC->need_gain_dB) > (gain_target + AGC_CLIPPING)) {
			AGC->need_gain_dB = gain_target - AGC_RX_dBFS;
			println("AGC overload ", (double)diff);
		}
	}

	// AGC off, not adjustable
	if (rx_id == AUDIO_RX1 && !CurrentVFO->AGC) {
		AGC->need_gain_dB = 1.0f;
	}

#if HRDW_HAS_DUAL_RX
	if (rx_id == AUDIO_RX2 && !SecondaryVFO->AGC) {
		AGC->need_gain_dB = 1.0f;
	}
#endif

	// gain limitation
	float32_t current_need_gain = AGC->need_gain_dB;
	if (AGC->need_gain_dB > (float32_t)TRX.RX_AGC_Max_gain) {
		if (!TRX.AGC_Threshold || mode == TRX_MODE_DIGI_L || mode == TRX_MODE_DIGI_U || mode == TRX_MODE_RTTY || nr_type != 0) {
			current_need_gain = (float32_t)TRX.RX_AGC_Max_gain;
		} else {
			const float32_t max_threshold_diff = 10.0f;
			float32_t threshold_diff = AGC->need_gain_dB - (float32_t)TRX.RX_AGC_Max_gain;
			if (threshold_diff > max_threshold_diff) {
				threshold_diff = max_threshold_diff;
			}
			float32_t threshold_rise_level = (max_threshold_diff - threshold_diff) / max_threshold_diff;
			current_need_gain = (float32_t)TRX.RX_AGC_Max_gain * threshold_rise_level;
		}
	}

	// println("HOLD: ", AGC->hold_time, " GAIN: ", AGC->need_gain_dB, " DIFF: ", diff);
	AGC_SCREEN_maxGain = (float32_t)TRX.RX_AGC_Max_gain;
	AGC_SCREEN_currentGain = AGC->need_gain_dB > AGC_SCREEN_maxGain ? AGC_SCREEN_maxGain : current_need_gain;

	// Muting if need
	if (CODEC_Muting || VAD_Muting) {
		current_need_gain = -200.0f;
	}

	// apply gain
	// println("cur agc: ", AGC_RX_dBFS, " need: ", AGC->need_gain_dB, " cur: ", current_need_gain, " old: ", AGC->need_gain_dB_old);
	if (fabsf(AGC->need_gain_dB_old - current_need_gain) >= 1.0f) // gain changed
	{
		float32_t gainApplyStep = 0;
		if (AGC->need_gain_dB_old > current_need_gain) {
			gainApplyStep = -(AGC->need_gain_dB_old - current_need_gain) / (float32_t)blockSize;
		}
		if (AGC->need_gain_dB_old < current_need_gain) {
			gainApplyStep = (current_need_gain - AGC->need_gain_dB_old) / (float32_t)blockSize;
		}
		float32_t val_prev = 0.0f;
		bool zero_cross = false;
		for (uint_fast16_t i = 0; i < blockSize; i++) {
			if (val_prev <= 0.0f && agcBuffer_i[i] >= 0.0f) {
				zero_cross = true;
			} else if (val_prev >= 0.0f && agcBuffer_i[i] <= 0.0f) {
				zero_cross = true;
			}
			if (zero_cross) {
				AGC->need_gain_dB_old += gainApplyStep;
			}

			agcBuffer_i[i] = agcBuffer_i[i] * db2rateV(AGC->need_gain_dB_old);
			if (stereo) {
				agcBuffer_q[i] = agcBuffer_q[i] * db2rateV(AGC->need_gain_dB_old);
			}
			val_prev = agcBuffer_i[i];
		}
	} else // gain did not change, apply gain across all samples
	{
		arm_scale_f32(agcBuffer_i, db2rateV(AGC->need_gain_dB_old), agcBuffer_i, blockSize);
		if (stereo) {
			arm_scale_f32(agcBuffer_q, db2rateV(AGC->need_gain_dB_old), agcBuffer_q, blockSize);
		}
	}
}

// Run TX AGC on data block
void DoTxAGC(float32_t *agcBuffer_i, uint_fast16_t blockSize, float32_t target_rate, TRX_MODE mode) {
	// higher speed in settings - higher speed of AGC processing
	float32_t TX_AGC_STEPSIZE_UP = 0.0f;
	float32_t TX_AGC_STEPSIZE_DOWN = 0.0f;
	switch (mode) {
	case TRX_MODE_NFM:
	case TRX_MODE_WFM:
	case TRX_MODE_AM:
	case TRX_MODE_SAM_STEREO:
	case TRX_MODE_SAM_LSB:
	case TRX_MODE_SAM_USB:
		TX_AGC_STEPSIZE_UP = 200.0f / (float32_t)TRX.TX_Compressor_speed_AMFM;
		TX_AGC_STEPSIZE_DOWN = 20.0f / (float32_t)TRX.TX_Compressor_speed_AMFM;
		break;

	case TRX_MODE_LSB:
	case TRX_MODE_USB:
	case TRX_MODE_LOOPBACK:
	default:
		TX_AGC_STEPSIZE_UP = 200.0f / (float32_t)TRX.TX_Compressor_speed_SSB;
		TX_AGC_STEPSIZE_DOWN = 20.0f / (float32_t)TRX.TX_Compressor_speed_SSB;
		break;
	}

	// do ring buffer
	// static uint32_t ring_position = 0;
	// save new data to ring buffer
	// dma_memcpy(&agc_ringbuffer_i[ring_position * blockSize], agcBuffer_i, sizeof(float32_t) * blockSize);
	// move ring buffer index
	// ring_position++;
	// if (ring_position >= AGC_RINGBUFFER_TAPS_SIZE)
	// ring_position = 0;
	// get old data to process
	// dma_memcpy(agcBuffer_i, &agc_ringbuffer_i[ring_position * blockSize], sizeof(float32_t) * blockSize);

	// calculate the magnitude
	float32_t AGC_TX_I_magnitude = 0;
	float32_t ampl_max_i = 0.0f;
	float32_t ampl_min_i = 0.0f;
	arm_max_no_idx_f32(agcBuffer_i, blockSize, &ampl_max_i);
	arm_min_no_idx_f32(agcBuffer_i, blockSize, &ampl_min_i);
	if (ampl_max_i > -ampl_min_i) {
		AGC_TX_I_magnitude = ampl_max_i;
	} else {
		AGC_TX_I_magnitude = -ampl_min_i;
	}
	if (AGC_TX_I_magnitude == 0.0f) {
		AGC_TX_I_magnitude = 0.000001f;
	}

	float32_t AGC_TX_dBFS = rate2dbV(AGC_TX_I_magnitude);
	float32_t target_dB = rate2dbV(target_rate);

	// CESSB AGC from power
	if (TRX.TX_CESSB && (mode == TRX_MODE_LSB || mode == TRX_MODE_USB || mode == TRX_MODE_LOOPBACK)) {
		target_dB = rate2dbP(target_rate);

		arm_rms_f32(agcBuffer_i, blockSize, &AGC_TX_I_magnitude);

		if (AGC_TX_I_magnitude == 0.0f) {
			AGC_TX_I_magnitude = 0.001f;
		}
		float32_t full_scale_rate = AGC_TX_I_magnitude / FLOAT_FULL_SCALE_POW;
		AGC_TX_dBFS = rate2dbP(full_scale_rate);
	}

	if (AGC_TX_dBFS < -100.0f) {
		AGC_TX_dBFS = -100.0f;
	}

	// mic noise threshold (gate), below it - mute
	if (AGC_TX_dBFS < TRX.MIC_NOISE_GATE && TRX.MIC_NOISE_GATE > -120) { //-120dB - disabled
		target_rate = 0.0f;
		TRX_MIC_BELOW_NOISEGATE = true;
	} else {
		TRX_MIC_BELOW_NOISEGATE = false;
	}

	// move the gain one step
	if (target_rate > 0.0f) {
		float32_t diff = (target_dB - (AGC_TX_dBFS + AGC_TX.need_gain_dB));
		if (diff > 0) {
			AGC_TX.need_gain_dB += diff / TX_AGC_STEPSIZE_UP;
		} else {
			AGC_TX.need_gain_dB += diff / TX_AGC_STEPSIZE_DOWN;
		}

		// overload (clipping), sharply reduce the gain
		if ((AGC_TX_dBFS + AGC_TX.need_gain_dB) > target_dB) {
			AGC_TX.need_gain_dB = target_dB - AGC_TX_dBFS;
			// sendToDebug_float32(diff,false);
		}
	}

	// gain limitation
	switch (mode) {
	case TRX_MODE_NFM:
	case TRX_MODE_WFM:
	case TRX_MODE_AM:
	case TRX_MODE_SAM_STEREO:
	case TRX_MODE_SAM_LSB:
	case TRX_MODE_SAM_USB:
		if (AGC_TX.need_gain_dB > TRX.TX_Compressor_maxgain_AMFM) {
			AGC_TX.need_gain_dB = TRX.TX_Compressor_maxgain_AMFM;
		}
		break;

	case TRX_MODE_LSB:
	case TRX_MODE_USB:
	case TRX_MODE_LOOPBACK:
	default:
		if (AGC_TX.need_gain_dB > TRX.TX_Compressor_maxgain_SSB) {
			AGC_TX.need_gain_dB = TRX.TX_Compressor_maxgain_SSB;
		}
		break;
	}

	// apply gain
	// println(AGC_TX_I_magnitude, " ", AGC_TX_dBFS, " ", AGC_TX.need_gain_dB, " ", target_dB);
	if (target_rate == 0.0f) // zero gain (mute)
	{
#define zero_gain 200.0f
		float32_t gainApplyStep = 0;
		if (AGC_TX.need_gain_dB_old > zero_gain) {
			gainApplyStep = -(AGC_TX.need_gain_dB_old - zero_gain) / (float32_t)blockSize;
		}
		if (AGC_TX.need_gain_dB_old < zero_gain) {
			gainApplyStep = (zero_gain - AGC_TX.need_gain_dB_old) / (float32_t)blockSize;
		}
		float32_t val_prev = 0.0f;
		bool zero_cross = false;
		for (uint_fast16_t i = 0; i < blockSize; i++) {
			if (val_prev < 0.0f && agcBuffer_i[i] > 0.0f) {
				zero_cross = true;
			} else if (val_prev > 0.0f && agcBuffer_i[i] < 0.0f) {
				zero_cross = true;
			}
			if (zero_cross) {
				AGC_TX.need_gain_dB_old += gainApplyStep;
			}

			if (AGC_TX.need_gain_dB_old >= zero_gain) {
				agcBuffer_i[i] = agcBuffer_i[i] * db2rateV(AGC_TX.need_gain_dB_old);
			} else {
				agcBuffer_i[i] = 0.0f;
			}

			val_prev = agcBuffer_i[i];
		}
	} else if (fabsf(AGC_TX.need_gain_dB_old - AGC_TX.need_gain_dB) > 0.0f) // gain changed
	{
		float32_t gainApplyStep = 0;
		if (AGC_TX.need_gain_dB_old > AGC_TX.need_gain_dB) {
			gainApplyStep = -(AGC_TX.need_gain_dB_old - AGC_TX.need_gain_dB) / (float32_t)blockSize;
		}
		if (AGC_TX.need_gain_dB_old < AGC_TX.need_gain_dB) {
			gainApplyStep = (AGC_TX.need_gain_dB - AGC_TX.need_gain_dB_old) / (float32_t)blockSize;
		}
		float32_t val_prev = 0.0f;
		bool zero_cross = false;
		for (uint_fast16_t i = 0; i < blockSize; i++) {
			if (val_prev < 0.0f && agcBuffer_i[i] > 0.0f) {
				zero_cross = true;
			} else if (val_prev > 0.0f && agcBuffer_i[i] < 0.0f) {
				zero_cross = true;
			}
			if (zero_cross) {
				AGC_TX.need_gain_dB_old += gainApplyStep;
			}

			agcBuffer_i[i] = agcBuffer_i[i] * db2rateV(AGC_TX.need_gain_dB_old);
			val_prev = agcBuffer_i[i];
		}
	} else // gain did not change, apply gain across all samples
	{
		arm_scale_f32(agcBuffer_i, db2rateV(AGC_TX.need_gain_dB), agcBuffer_i, blockSize);
	}
}

void ResetAGC(void) {
	// AGC_RX1.need_gain_dB = 0.0f;
	// AGC_RX2.need_gain_dB = 0.0f;
	dma_memset(AGC_RX1.ringbuffer, 0x00, sizeof(AGC_RX1.ringbuffer));

#if HRDW_HAS_DUAL_RX
	dma_memset(AGC_RX2.ringbuffer, 0x00, sizeof(AGC_RX2.ringbuffer));
#endif
}
