donatukas/Volf-TRX/STM32/Src/audio_processor.c

#include "audio_processor.h"
#include "FT8/FT8_main.h"
#include "FT8/decode_ft8.h"
#include "agc.h"
#include "atu.h"
#include "audio_filters.h"
#include "auto_calibration.h"
#include "auto_notch.h"
#include "codec.h"
#include "cw.h"
#include "decoder.h"
#include "noise_blanker.h"
#include "noise_reduction.h"
#include "pre_distortion.h"
#include "rf_unit.h"
#include "sd.h"
#include "settings.h"
#include "system_menu.h"
#include "trx_manager.h"
#include "usbd_audio_if.h"
#include "usbd_iq_if.h"
#include "vad.h"
#include "vocoder.h"
#include "wifi.h"

// Public variables
volatile uint32_t AUDIOPROC_samples = 0;      // audio samples processed in the processor
volatile bool Processor_NeedRXBuffer = false; // codec needs data from processor for RX
volatile bool Processor_NeedTXBuffer = false; // codec needs data from processor for TX

float32_t APROC_Audio_Buffer_RX1_accum_Q[FPGA_RX_IQ_BUFFER_HALF_SIZE] = {0}; // copy of the working part of the FPGA buffers for processing
float32_t APROC_Audio_Buffer_RX1_accum_I[FPGA_RX_IQ_BUFFER_HALF_SIZE] = {0};
float32_t APROC_Audio_Buffer_RX1_Q[FPGA_RX_IQ_BUFFER_HALF_SIZE] = {0}; // decimated and ready to demod buffer
float32_t APROC_Audio_Buffer_RX1_I[FPGA_RX_IQ_BUFFER_HALF_SIZE] = {0};

#if HRDW_HAS_DUAL_RX
float32_t APROC_Audio_Buffer_RX2_accum_Q[FPGA_RX_IQ_BUFFER_HALF_SIZE] = {0};
float32_t APROC_Audio_Buffer_RX2_accum_I[FPGA_RX_IQ_BUFFER_HALF_SIZE] = {0};
float32_t APROC_Audio_Buffer_RX2_Q[FPGA_RX_IQ_BUFFER_HALF_SIZE] = {0};
float32_t APROC_Audio_Buffer_RX2_I[FPGA_RX_IQ_BUFFER_HALF_SIZE] = {0};
#endif

SRAM_ON_F407 float32_t APROC_Audio_Buffer_TX_Q[FPGA_TX_IQ_BUFFER_HALF_SIZE] = {0};
SRAM_ON_F407 float32_t APROC_Audio_Buffer_TX_I[FPGA_TX_IQ_BUFFER_HALF_SIZE] = {0};
volatile float32_t Processor_RX1_Power_value;      // RX signal magnitude
volatile float32_t Processor_RX2_Power_value;      // RX signal magnitude
volatile float32_t Processor_TX_MAX_amplitude_OUT; // TX uplift after ALC

bool NeedReinitReverber = false;
bool APROC_IFGain_Overflow = false;
float32_t APROC_TX_clip_gain = 1.0f;
float32_t APROC_TX_tune_power = 0.0f;
float32_t SAM_Carrier_offset = 0.0f;
float32_t APROC_TUNE_DigiTone_Freq = 1000.0f;

#if FT8_SUPPORT
static q15_t APROC_AudioBuffer_FT8_out[AUDIO_BUFFER_SIZE / 2] = {0};
#endif
// static uint8_t APROC_AudioBuffer_WIFI_out[2050] = {0};

SRAM_ON_F407 static int32_t APROC_AudioBuffer_out[AUDIO_BUFFER_SIZE] = {0}; // output buffer of the audio processor

demod_fm_instance DFM_RX1 = {.squelchRate = 1.0f};
#if HRDW_HAS_DUAL_RX
demod_fm_instance DFM_RX2 = {.squelchRate = 1.0f};
#endif
static float32_t current_if_gain = 0.0f;
static float32_t volume_gain = 0.0f;
static bool preprocessor_buffer_ready = false;
static uint32_t audio_buffer_in_index = 0;

#ifndef STM32F407xx
IRAM2 static float32_t Processor_Reverber_Buffer[AUDIO_BUFFER_HALF_SIZE * AUDIO_MAX_REVERBER_TAPS] = {0};
#endif

static demod_sam_data_t sam_data_rx1;
#if HRDW_HAS_DUAL_RX
SRAM static demod_sam_data_t sam_data_rx2;
#endif

// Prototypes
static void doRX_HILBERT(AUDIO_PROC_RX_NUM rx_id, uint16_t size);                                 // Hilbert filter for phase shift of signals
static void doRX_LPF_IQ(AUDIO_PROC_RX_NUM rx_id, uint16_t size);                                  // Low-pass filter for I and Q
static void doRX_LPF2_IQ(AUDIO_PROC_RX_NUM rx_id, uint16_t size);                                 // Low-pass filter for I and Q (second stage)
static void doRX_LPF_I(AUDIO_PROC_RX_NUM rx_id, uint16_t size);                                   // LPF filter for I
static void doRX_LPF2_I(AUDIO_PROC_RX_NUM rx_id, uint16_t size);                                  // LPF filter for I (second stage)
static void doRX_GAUSS_IQ(AUDIO_PROC_RX_NUM rx_id, uint16_t size);                                // Gauss filter for I
static void doRX_HPF_I(AUDIO_PROC_RX_NUM rx_id, uint16_t size);                                   // HPF filter for I
static void doRX_HPF_IQ(AUDIO_PROC_RX_NUM rx_id, uint16_t size);                                  // HPF filter for I and Q
static void doRX_DNR(AUDIO_PROC_RX_NUM rx_id, uint16_t size, uint_fast8_t mode, bool stereo);     // Digital Noise Reduction
static void doRX_AGC(AUDIO_PROC_RX_NUM rx_id, uint16_t size, uint_fast8_t mode, bool stereo);     // automatic gain control
static void doRX_NOTCH(AUDIO_PROC_RX_NUM rx_id, uint16_t size);                                   // notch filter
static void doRX_NoiseBlanker(AUDIO_PROC_RX_NUM rx_id, uint16_t size);                            // impulse noise suppressor
static void doRX_SMETER(AUDIO_PROC_RX_NUM rx_id, float32_t *buff, uint16_t size, bool if_gained); // s-meter
static void doRX_COPYCHANNEL(AUDIO_PROC_RX_NUM rx_id, uint16_t size);                             // copy I to Q channel
static void DemodulateFM(float32_t *data_i, float32_t *data_q, AUDIO_PROC_RX_NUM rx_id, uint16_t size, bool wfm,
                         float32_t dBm);                         // FM demodulator
static void ModulateFM(uint16_t size, float32_t amplitude);      // FM modulator
static void doRX_EQ(uint16_t size, uint8_t mode);                // receiver equalizer
static void doMIC_EQ(uint16_t size, uint8_t mode);               // microphone equalizer
static void doVAD(AUDIO_PROC_RX_NUM rx_id, uint16_t size);       // voice activity detector
static void doRX_IFGain(AUDIO_PROC_RX_NUM rx_id, uint16_t size); // IF gain
static void doRX_DecimateInput(AUDIO_PROC_RX_NUM rx_id, float32_t *in_i, float32_t *in_q, float32_t *out_i, float32_t *out_q, uint16_t size,
                               uint8_t factor); // decimate RX samplerate input stream
static void doRX_RXFreqTransition(float32_t *in_i, float32_t *in_q, uint16_t size, int32_t freq_diff);
static void doRX_CWFreqTransition(AUDIO_PROC_RX_NUM rx_id, uint16_t size, float32_t freq_diff);
static void APROC_SD_Play(void);
static bool APROC_SD_PlayTX(void);
static void doRX_DemodSAM(AUDIO_PROC_RX_NUM rx_id, float32_t *i_buffer, float32_t *q_buffer, float32_t *out_buffer_l, float32_t *out_buffer_r, int16_t blockSize, TRX_MODE mode);
static void doTX_HILBERT(bool swap_iq, uint16_t size);
static void doTX_CESSB(uint16_t size, TRX_MODE mode);
static void APROC_ProcessCodecMuting(void);

// initialize audio processor
void initAudioProcessor(void) {
	memset(&DFM_RX1, 0x00, sizeof(DFM_RX1));
	DFM_RX1.squelchRate = 1.0f;
#if HRDW_HAS_DUAL_RX
	memset(&DFM_RX2, 0x00, sizeof(DFM_RX2));
	DFM_RX2.squelchRate = 1.0f;
#endif

	InitAudioFilters();
	NB_Init();
	DPD_Init();
	DECODER_Init();
	NeedReinitReverber = true;
#if HRDW_HAS_SD
	ADPCM_Init();
#endif
}

// RX decimator and preprocessor
void preProcessRxAudio(void) {
	if (!FPGA_RX_buffer_ready) {
		return;
	}
	if (preprocessor_buffer_ready) {
		return;
	}

	AUDIOPROC_samples++;

	// copy buffer from FPGA
	float32_t *FPGA_Audio_Buffer_RX1_I_current = !FPGA_RX_Buffer_Current ? (float32_t *)&FPGA_Audio_Buffer_RX1_I_A : (float32_t *)&FPGA_Audio_Buffer_RX1_I_B;
	float32_t *FPGA_Audio_Buffer_RX1_Q_current = !FPGA_RX_Buffer_Current ? (float32_t *)&FPGA_Audio_Buffer_RX1_Q_A : (float32_t *)&FPGA_Audio_Buffer_RX1_Q_B;
#if HRDW_HAS_DUAL_RX
	float32_t *FPGA_Audio_Buffer_RX2_I_current = !FPGA_RX_Buffer_Current ? (float32_t *)&FPGA_Audio_Buffer_RX2_I_A : (float32_t *)&FPGA_Audio_Buffer_RX2_I_B;
	float32_t *FPGA_Audio_Buffer_RX2_Q_current = !FPGA_RX_Buffer_Current ? (float32_t *)&FPGA_Audio_Buffer_RX2_Q_A : (float32_t *)&FPGA_Audio_Buffer_RX2_Q_B;
#endif

	// Get and decimate input
	uint32_t need_decimate_rate = TRX_GetRXSampleRate / TRX_SAMPLERATE;
	if ((audio_buffer_in_index + (FPGA_RX_IQ_BUFFER_HALF_SIZE / need_decimate_rate)) > FPGA_RX_IQ_BUFFER_HALF_SIZE || DECIMATE_FIR_RX1_AUDIO_I.M != need_decimate_rate) {
		audio_buffer_in_index = 0;
	}

	// Free Tune frequency transition
	if (TRX.FREE_Tune && CurrentVFO->Mode != TRX_MODE_WFM && CurrentVFO->SpectrumAndRXDiff != 0) {
		doRX_RXFreqTransition(FPGA_Audio_Buffer_RX1_I_current, FPGA_Audio_Buffer_RX1_Q_current, FPGA_RX_IQ_BUFFER_HALF_SIZE, CurrentVFO->SpectrumAndRXDiff);
	}

	// Decimation to 48kHz
	if (CurrentVFO->Mode == TRX_MODE_WFM) {
		// calc s-meter
		doRX_SMETER(AUDIO_RX1, FPGA_Audio_Buffer_RX1_I_current, FPGA_RX_IQ_BUFFER_HALF_SIZE, false);
		// demodulate wfm before decimation
		DemodulateFM(FPGA_Audio_Buffer_RX1_I_current, FPGA_Audio_Buffer_RX1_Q_current, AUDIO_RX1, FPGA_RX_IQ_BUFFER_HALF_SIZE, true, TRX_RX1_dBm);
	}
	doRX_DecimateInput(AUDIO_RX1, FPGA_Audio_Buffer_RX1_I_current, FPGA_Audio_Buffer_RX1_Q_current, &APROC_Audio_Buffer_RX1_accum_I[audio_buffer_in_index],
	                   &APROC_Audio_Buffer_RX1_accum_Q[audio_buffer_in_index], FPGA_RX_IQ_BUFFER_HALF_SIZE, need_decimate_rate);

#if HRDW_HAS_DUAL_RX
	if (TRX.Dual_RX) {
		if (SecondaryVFO->Mode == TRX_MODE_WFM) {
			// calc s-meter
			doRX_SMETER(AUDIO_RX2, FPGA_Audio_Buffer_RX2_I_current, FPGA_RX_IQ_BUFFER_HALF_SIZE, false);
			// demodulate wfm before decimation
			DemodulateFM(FPGA_Audio_Buffer_RX2_I_current, FPGA_Audio_Buffer_RX2_Q_current, AUDIO_RX2, FPGA_RX_IQ_BUFFER_HALF_SIZE, true, TRX_RX2_dBm);
		}
		doRX_DecimateInput(AUDIO_RX2, FPGA_Audio_Buffer_RX2_I_current, FPGA_Audio_Buffer_RX2_Q_current, &APROC_Audio_Buffer_RX2_accum_I[audio_buffer_in_index],
		                   &APROC_Audio_Buffer_RX2_accum_Q[audio_buffer_in_index], FPGA_RX_IQ_BUFFER_HALF_SIZE, need_decimate_rate);
	}
#endif

	FPGA_RX_buffer_ready = false; // start processing of new buffer

	audio_buffer_in_index += FPGA_RX_IQ_BUFFER_HALF_SIZE / need_decimate_rate;
	if (audio_buffer_in_index >= FPGA_RX_IQ_BUFFER_HALF_SIZE) {
		audio_buffer_in_index = 0;
	} else {
		return;
	}

	preprocessor_buffer_ready = true;
}

// start audio processor for RX
void processRxAudio(void) {
	if (!Processor_NeedRXBuffer) {
		return;
	}
	if (!preprocessor_buffer_ready) {
		return;
	}

#if HRDW_HAS_SD
	if (SD_PlayInProcess) {
		APROC_SD_Play();
		return;
	}
#endif

	// get data from preprocessor
	dma_memcpy(APROC_Audio_Buffer_RX1_I, APROC_Audio_Buffer_RX1_accum_I, sizeof(APROC_Audio_Buffer_RX1_I));
	dma_memcpy(APROC_Audio_Buffer_RX1_Q, APROC_Audio_Buffer_RX1_accum_Q, sizeof(APROC_Audio_Buffer_RX1_Q));
#if HRDW_HAS_DUAL_RX
	dma_memcpy(APROC_Audio_Buffer_RX2_I, APROC_Audio_Buffer_RX2_accum_I, sizeof(APROC_Audio_Buffer_RX2_I));
	dma_memcpy(APROC_Audio_Buffer_RX2_Q, APROC_Audio_Buffer_RX2_accum_Q, sizeof(APROC_Audio_Buffer_RX2_Q));
#endif
	preprocessor_buffer_ready = false;

	// IQ Phase corrector https://github.com/df8oe/UHSDR/wiki/IQ---correction-and-mirror-frequencies
	float32_t teta1_new = 0;
	float32_t teta3_new = 0;
	static float32_t teta1 = 0;
	static float32_t teta3 = 0;
	for (uint16_t i = 0; i < FPGA_RX_IQ_BUFFER_HALF_SIZE; i++) {
		teta1_new += APROC_Audio_Buffer_RX1_Q[i] * (APROC_Audio_Buffer_RX1_I[i] < 0.0f ? -1.0f : 1.0f);
		teta3_new += APROC_Audio_Buffer_RX1_Q[i] * (APROC_Audio_Buffer_RX1_Q[i] < 0.0f ? -1.0f : 1.0f);
	}
	teta1_new = teta1_new / (float32_t)FPGA_RX_IQ_BUFFER_HALF_SIZE;
	teta3_new = teta3_new / (float32_t)FPGA_RX_IQ_BUFFER_HALF_SIZE;
	teta1 = 0.003f * teta1_new + 0.997f * teta1;
	teta3 = 0.003f * teta3_new + 0.997f * teta3;
	if (teta3 > 0.0f) {
		TRX_IQ_phase_error = asinf(teta1 / teta3);
	}

	VAD_RX1_Muting = false;
	VAD_RX2_Muting = false;
	if (CurrentVFO->Mode != TRX_MODE_IQ) {
		doRX_IFGain(AUDIO_RX1, FPGA_RX_IQ_BUFFER_HALF_SIZE);
	}

#if HRDW_HAS_USB_IQ
	// Send to USB IQ
	if (USB_IQ_need_rx_buffer && TRX_Inited) {
		uint8_t *USB_IQ_rx_buffer_current = USB_IQ_rx_buffer_b;
		if (!USB_IQ_current_rx_buffer) {
			USB_IQ_rx_buffer_current = USB_IQ_rx_buffer_a;
		}

		// drop LSB 32b->24b
		int32_t iq_i, iq_q;
		for (uint_fast16_t i = 0; i < (USB_AUDIO_RX_BUFFER_SIZE / BYTES_IN_SAMPLE_AUDIO_OUT_PACKET / 2); i++) {
			if (CALIBRATE.Swap_USB_IQ) {
				iq_i = APROC_Audio_Buffer_RX1_Q[i] * 2147483648;
				iq_q = APROC_Audio_Buffer_RX1_I[i] * 2147483648;
			} else {
				iq_i = APROC_Audio_Buffer_RX1_I[i] * 2147483648;
				iq_q = APROC_Audio_Buffer_RX1_Q[i] * 2147483648;
			}

			USB_IQ_rx_buffer_current[i * BYTES_IN_SAMPLE_AUDIO_OUT_PACKET * 2 + 0] = (iq_i >> 8) & 0xFF;
			USB_IQ_rx_buffer_current[i * BYTES_IN_SAMPLE_AUDIO_OUT_PACKET * 2 + 1] = (iq_i >> 16) & 0xFF;
			USB_IQ_rx_buffer_current[i * BYTES_IN_SAMPLE_AUDIO_OUT_PACKET * 2 + 2] = (iq_i >> 24) & 0xFF;

			USB_IQ_rx_buffer_current[i * BYTES_IN_SAMPLE_AUDIO_OUT_PACKET * 2 + 3] = (iq_q >> 8) & 0xFF;
			USB_IQ_rx_buffer_current[i * BYTES_IN_SAMPLE_AUDIO_OUT_PACKET * 2 + 4] = (iq_q >> 16) & 0xFF;
			USB_IQ_rx_buffer_current[i * BYTES_IN_SAMPLE_AUDIO_OUT_PACKET * 2 + 5] = (iq_q >> 24) & 0xFF;
		}
		USB_IQ_need_rx_buffer = false;
	}
#endif

	switch (CurrentVFO->Mode) // first receiver
	{
	case TRX_MODE_CW:
		doRX_LPF_IQ(AUDIO_RX1, FPGA_RX_IQ_BUFFER_HALF_SIZE);
		doRX_CWFreqTransition(AUDIO_RX1, FPGA_RX_IQ_BUFFER_HALF_SIZE, TRX.CW_Pitch);
		// difference of I and Q - LSB
		arm_sub_f32(APROC_Audio_Buffer_RX1_I, APROC_Audio_Buffer_RX1_Q, APROC_Audio_Buffer_RX1_I, FPGA_RX_IQ_BUFFER_HALF_SIZE);
		DECODER_PutSamples(APROC_Audio_Buffer_RX1_I, FPGA_RX_IQ_BUFFER_HALF_SIZE);
		doRX_NoiseBlanker(AUDIO_RX1, FPGA_RX_IQ_BUFFER_HALF_SIZE);
		if (TRX.NOISE_BLANKER1 || TRX.NOISE_BLANKER2) {
			doRX_LPF2_I(AUDIO_RX1, FPGA_RX_IQ_BUFFER_HALF_SIZE);
		}
		doRX_GAUSS_IQ(AUDIO_RX1, FPGA_RX_IQ_BUFFER_HALF_SIZE);
		doRX_NOTCH(AUDIO_RX1, FPGA_RX_IQ_BUFFER_HALF_SIZE);
		doRX_SMETER(AUDIO_RX1, APROC_Audio_Buffer_RX1_I, FPGA_RX_IQ_BUFFER_HALF_SIZE, true);
		doVAD(AUDIO_RX1, FPGA_RX_IQ_BUFFER_HALF_SIZE);
		doRX_DNR(AUDIO_RX1, FPGA_RX_IQ_BUFFER_HALF_SIZE, CurrentVFO->Mode, false);
		doRX_AGC(AUDIO_RX1, FPGA_RX_IQ_BUFFER_HALF_SIZE, CurrentVFO->Mode, false);
		doRX_COPYCHANNEL(AUDIO_RX1, FPGA_RX_IQ_BUFFER_HALF_SIZE);
		break;
	case TRX_MODE_LSB:
		doRX_HILBERT(AUDIO_RX1, FPGA_RX_IQ_BUFFER_HALF_SIZE);
		// difference of I and Q - LSB
		arm_sub_f32(APROC_Audio_Buffer_RX1_I, APROC_Audio_Buffer_RX1_Q, APROC_Audio_Buffer_RX1_I, FPGA_RX_IQ_BUFFER_HALF_SIZE);
		doRX_HPF_I(AUDIO_RX1, FPGA_RX_IQ_BUFFER_HALF_SIZE);
		doRX_LPF_I(AUDIO_RX1, FPGA_RX_IQ_BUFFER_HALF_SIZE);
		doRX_NoiseBlanker(AUDIO_RX1, FPGA_RX_IQ_BUFFER_HALF_SIZE);
		if (TRX.NOISE_BLANKER1 || TRX.NOISE_BLANKER2) {
			doRX_LPF2_I(AUDIO_RX1, FPGA_RX_IQ_BUFFER_HALF_SIZE);
		}
		doRX_NOTCH(AUDIO_RX1, FPGA_RX_IQ_BUFFER_HALF_SIZE);
		doRX_SMETER(AUDIO_RX1, APROC_Audio_Buffer_RX1_I, FPGA_RX_IQ_BUFFER_HALF_SIZE, true);
		DECODER_PutSamples(APROC_Audio_Buffer_RX1_I, FPGA_RX_IQ_BUFFER_HALF_SIZE);
		doVAD(AUDIO_RX1, FPGA_RX_IQ_BUFFER_HALF_SIZE);
		doRX_DNR(AUDIO_RX1, FPGA_RX_IQ_BUFFER_HALF_SIZE, CurrentVFO->Mode, false);
		doRX_AGC(AUDIO_RX1, FPGA_RX_IQ_BUFFER_HALF_SIZE, CurrentVFO->Mode, false);
		doRX_COPYCHANNEL(AUDIO_RX1, FPGA_RX_IQ_BUFFER_HALF_SIZE);
		break;
	case TRX_MODE_DIGI_L:
		doRX_HILBERT(AUDIO_RX1, FPGA_RX_IQ_BUFFER_HALF_SIZE);
		arm_sub_f32(APROC_Audio_Buffer_RX1_I, APROC_Audio_Buffer_RX1_Q, APROC_Audio_Buffer_RX1_I, FPGA_RX_IQ_BUFFER_HALF_SIZE); // difference of I and Q - LSB
		doRX_HPF_I(AUDIO_RX1, FPGA_RX_IQ_BUFFER_HALF_SIZE);
		doRX_LPF_I(AUDIO_RX1, FPGA_RX_IQ_BUFFER_HALF_SIZE);
		doRX_SMETER(AUDIO_RX1, APROC_Audio_Buffer_RX1_I, FPGA_RX_IQ_BUFFER_HALF_SIZE, true);
		DECODER_PutSamples(APROC_Audio_Buffer_RX1_I, FPGA_RX_IQ_BUFFER_HALF_SIZE);
		doRX_DNR(AUDIO_RX1, FPGA_RX_IQ_BUFFER_HALF_SIZE, CurrentVFO->Mode, false);
		doRX_AGC(AUDIO_RX1, FPGA_RX_IQ_BUFFER_HALF_SIZE, CurrentVFO->Mode, false);
		doRX_COPYCHANNEL(AUDIO_RX1, FPGA_RX_IQ_BUFFER_HALF_SIZE);
		break;
	case TRX_MODE_USB:
		doRX_HILBERT(AUDIO_RX1, FPGA_RX_IQ_BUFFER_HALF_SIZE);
		arm_add_f32(APROC_Audio_Buffer_RX1_I, APROC_Audio_Buffer_RX1_Q, APROC_Audio_Buffer_RX1_I, FPGA_RX_IQ_BUFFER_HALF_SIZE); // sum of I and Q - USB
		doRX_HPF_I(AUDIO_RX1, FPGA_RX_IQ_BUFFER_HALF_SIZE);
		doRX_LPF_I(AUDIO_RX1, FPGA_RX_IQ_BUFFER_HALF_SIZE);
		doRX_NoiseBlanker(AUDIO_RX1, FPGA_RX_IQ_BUFFER_HALF_SIZE);
		if (TRX.NOISE_BLANKER1 || TRX.NOISE_BLANKER2) {
			doRX_LPF2_I(AUDIO_RX1, FPGA_RX_IQ_BUFFER_HALF_SIZE);
		}
		doRX_NOTCH(AUDIO_RX1, FPGA_RX_IQ_BUFFER_HALF_SIZE);
		doRX_SMETER(AUDIO_RX1, APROC_Audio_Buffer_RX1_I, FPGA_RX_IQ_BUFFER_HALF_SIZE, true);
		DECODER_PutSamples(APROC_Audio_Buffer_RX1_I, FPGA_RX_IQ_BUFFER_HALF_SIZE);
		doVAD(AUDIO_RX1, FPGA_RX_IQ_BUFFER_HALF_SIZE);
		doRX_DNR(AUDIO_RX1, FPGA_RX_IQ_BUFFER_HALF_SIZE, CurrentVFO->Mode, false);
		doRX_AGC(AUDIO_RX1, FPGA_RX_IQ_BUFFER_HALF_SIZE, CurrentVFO->Mode, false);
		doRX_COPYCHANNEL(AUDIO_RX1, FPGA_RX_IQ_BUFFER_HALF_SIZE);
		break;
	case TRX_MODE_RTTY:
	case TRX_MODE_DIGI_U:
		doRX_HILBERT(AUDIO_RX1, FPGA_RX_IQ_BUFFER_HALF_SIZE);
		arm_add_f32(APROC_Audio_Buffer_RX1_I, APROC_Audio_Buffer_RX1_Q, APROC_Audio_Buffer_RX1_I, FPGA_RX_IQ_BUFFER_HALF_SIZE); // sum of I and Q - USB
		doRX_HPF_I(AUDIO_RX1, FPGA_RX_IQ_BUFFER_HALF_SIZE);
		doRX_LPF_I(AUDIO_RX1, FPGA_RX_IQ_BUFFER_HALF_SIZE);
		doRX_SMETER(AUDIO_RX1, APROC_Audio_Buffer_RX1_I, FPGA_RX_IQ_BUFFER_HALF_SIZE, true);
		DECODER_PutSamples(APROC_Audio_Buffer_RX1_I, FPGA_RX_IQ_BUFFER_HALF_SIZE);
		doRX_DNR(AUDIO_RX1, FPGA_RX_IQ_BUFFER_HALF_SIZE, CurrentVFO->Mode, false);
		doRX_AGC(AUDIO_RX1, FPGA_RX_IQ_BUFFER_HALF_SIZE, CurrentVFO->Mode, false);
		doRX_COPYCHANNEL(AUDIO_RX1, FPGA_RX_IQ_BUFFER_HALF_SIZE);
		break;
	case TRX_MODE_AM:
		doRX_LPF_IQ(AUDIO_RX1, FPGA_RX_IQ_BUFFER_HALF_SIZE);
		arm_mult_f32(APROC_Audio_Buffer_RX1_I, APROC_Audio_Buffer_RX1_I, APROC_Audio_Buffer_RX1_I, FPGA_RX_IQ_BUFFER_HALF_SIZE);
		arm_mult_f32(APROC_Audio_Buffer_RX1_Q, APROC_Audio_Buffer_RX1_Q, APROC_Audio_Buffer_RX1_Q, FPGA_RX_IQ_BUFFER_HALF_SIZE);
		arm_add_f32(APROC_Audio_Buffer_RX1_I, APROC_Audio_Buffer_RX1_Q, APROC_Audio_Buffer_RX1_I, FPGA_RX_IQ_BUFFER_HALF_SIZE);
		for (uint_fast16_t i = 0; i < FPGA_RX_IQ_BUFFER_HALF_SIZE; i++) {
			arm_sqrt_f32(APROC_Audio_Buffer_RX1_I[i], &APROC_Audio_Buffer_RX1_I[i]);
		}
		arm_scale_f32(APROC_Audio_Buffer_RX1_I, 0.5f, APROC_Audio_Buffer_RX1_I, FPGA_RX_IQ_BUFFER_HALF_SIZE);
		doRX_NoiseBlanker(AUDIO_RX1, FPGA_RX_IQ_BUFFER_HALF_SIZE);
		dc_filter(APROC_Audio_Buffer_RX1_I, FPGA_RX_IQ_BUFFER_HALF_SIZE, DC_FILTER_RX1_I);
		doRX_LPF2_I(AUDIO_RX1, FPGA_RX_IQ_BUFFER_HALF_SIZE);
		doRX_NOTCH(AUDIO_RX1, FPGA_RX_IQ_BUFFER_HALF_SIZE);
		doRX_SMETER(AUDIO_RX1, APROC_Audio_Buffer_RX1_I, FPGA_RX_IQ_BUFFER_HALF_SIZE, true);
		doVAD(AUDIO_RX1, FPGA_RX_IQ_BUFFER_HALF_SIZE);
		doRX_DNR(AUDIO_RX1, FPGA_RX_IQ_BUFFER_HALF_SIZE, CurrentVFO->Mode, false);
		doRX_AGC(AUDIO_RX1, FPGA_RX_IQ_BUFFER_HALF_SIZE, CurrentVFO->Mode, false);
		doRX_COPYCHANNEL(AUDIO_RX1, FPGA_RX_IQ_BUFFER_HALF_SIZE);
		break;
	case TRX_MODE_SAM_STEREO:
	case TRX_MODE_SAM_LSB:
	case TRX_MODE_SAM_USB:
		doRX_LPF_IQ(AUDIO_RX1, FPGA_RX_IQ_BUFFER_HALF_SIZE);
		doRX_DemodSAM(AUDIO_RX1, APROC_Audio_Buffer_RX1_I, APROC_Audio_Buffer_RX1_Q, APROC_Audio_Buffer_RX1_I, APROC_Audio_Buffer_RX1_Q, FPGA_RX_IQ_BUFFER_HALF_SIZE, CurrentVFO->Mode);
		doRX_LPF2_IQ(AUDIO_RX1, FPGA_RX_IQ_BUFFER_HALF_SIZE);
		doRX_SMETER(AUDIO_RX1, APROC_Audio_Buffer_RX1_I, FPGA_RX_IQ_BUFFER_HALF_SIZE, true);
		doVAD(AUDIO_RX1, FPGA_RX_IQ_BUFFER_HALF_SIZE);
		doRX_DNR(AUDIO_RX1, FPGA_RX_IQ_BUFFER_HALF_SIZE, CurrentVFO->Mode, true);
		doRX_AGC(AUDIO_RX1, FPGA_RX_IQ_BUFFER_HALF_SIZE, CurrentVFO->Mode, true);
		break;
	case TRX_MODE_NFM:
		doRX_LPF_IQ(AUDIO_RX1, FPGA_RX_IQ_BUFFER_HALF_SIZE);
		doRX_SMETER(AUDIO_RX1, APROC_Audio_Buffer_RX1_I, FPGA_RX_IQ_BUFFER_HALF_SIZE, true);
		DemodulateFM(APROC_Audio_Buffer_RX1_I, APROC_Audio_Buffer_RX1_Q, AUDIO_RX1, FPGA_RX_IQ_BUFFER_HALF_SIZE, false, TRX_RX1_dBm); // 48kHz iq
		doRX_NoiseBlanker(AUDIO_RX1, FPGA_RX_IQ_BUFFER_HALF_SIZE);
		doRX_HPF_I(AUDIO_RX1, FPGA_RX_IQ_BUFFER_HALF_SIZE);
		doRX_LPF2_I(AUDIO_RX1, FPGA_RX_IQ_BUFFER_HALF_SIZE);
		doRX_IFGain(AUDIO_RX1, FPGA_RX_IQ_BUFFER_HALF_SIZE);
		doRX_NOTCH(AUDIO_RX1, FPGA_RX_IQ_BUFFER_HALF_SIZE);
		doRX_DNR(AUDIO_RX1, FPGA_RX_IQ_BUFFER_HALF_SIZE, CurrentVFO->Mode, false);
		doRX_AGC(AUDIO_RX1, FPGA_RX_IQ_BUFFER_HALF_SIZE, CurrentVFO->Mode, false);
		doRX_COPYCHANNEL(AUDIO_RX1, FPGA_RX_IQ_BUFFER_HALF_SIZE);
		break;
	case TRX_MODE_WFM:
		doRX_LPF_IQ(AUDIO_RX1, FPGA_RX_IQ_BUFFER_HALF_SIZE);
		if (!TRX.FM_Stereo) {
			doRX_DNR(AUDIO_RX1, FPGA_RX_IQ_BUFFER_HALF_SIZE, CurrentVFO->Mode, TRX.FM_Stereo);
		}
		doRX_AGC(AUDIO_RX1, FPGA_RX_IQ_BUFFER_HALF_SIZE, CurrentVFO->Mode, TRX.FM_Stereo);
		if (!TRX.FM_Stereo) {
			doRX_COPYCHANNEL(AUDIO_RX1, FPGA_RX_IQ_BUFFER_HALF_SIZE);
		}
		break;
	case TRX_MODE_IQ:
	default:
		doRX_SMETER(AUDIO_RX1, APROC_Audio_Buffer_RX1_I, FPGA_RX_IQ_BUFFER_HALF_SIZE, false);
		break;
	}

#if HRDW_HAS_DUAL_RX
	if (TRX.Dual_RX) {
		if (SecondaryVFO->Mode != TRX_MODE_IQ) {
			doRX_IFGain(AUDIO_RX2, FPGA_RX_IQ_BUFFER_HALF_SIZE);
		}

		switch (SecondaryVFO->Mode) // second receiver
		{
		case TRX_MODE_CW:
			doRX_LPF_IQ(AUDIO_RX2, FPGA_RX_IQ_BUFFER_HALF_SIZE);
			doRX_CWFreqTransition(AUDIO_RX2, FPGA_RX_IQ_BUFFER_HALF_SIZE, TRX.CW_Pitch);
			// difference of I and Q - LSB
			arm_sub_f32(APROC_Audio_Buffer_RX2_I, APROC_Audio_Buffer_RX2_Q, APROC_Audio_Buffer_RX2_I, FPGA_RX_IQ_BUFFER_HALF_SIZE);
			doRX_NoiseBlanker(AUDIO_RX2, FPGA_RX_IQ_BUFFER_HALF_SIZE);
			if (TRX.NOISE_BLANKER1 || TRX.NOISE_BLANKER2) {
				doRX_LPF2_I(AUDIO_RX2, FPGA_RX_IQ_BUFFER_HALF_SIZE);
			}
			doRX_GAUSS_IQ(AUDIO_RX2, FPGA_RX_IQ_BUFFER_HALF_SIZE);
			doRX_NOTCH(AUDIO_RX2, FPGA_RX_IQ_BUFFER_HALF_SIZE);
			doRX_SMETER(AUDIO_RX2, APROC_Audio_Buffer_RX2_I, FPGA_RX_IQ_BUFFER_HALF_SIZE, true);
			doVAD(AUDIO_RX2, FPGA_RX_IQ_BUFFER_HALF_SIZE);
			doRX_DNR(AUDIO_RX2, FPGA_RX_IQ_BUFFER_HALF_SIZE, SecondaryVFO->Mode, false);
			doRX_AGC(AUDIO_RX2, FPGA_RX_IQ_BUFFER_HALF_SIZE, SecondaryVFO->Mode, false);
			break;
		case TRX_MODE_LSB:
			doRX_HILBERT(AUDIO_RX2, FPGA_RX_IQ_BUFFER_HALF_SIZE);
			// difference of I and Q - LSB
			arm_sub_f32(APROC_Audio_Buffer_RX2_I, APROC_Audio_Buffer_RX2_Q, APROC_Audio_Buffer_RX2_I, FPGA_RX_IQ_BUFFER_HALF_SIZE);
			doRX_HPF_I(AUDIO_RX2, FPGA_RX_IQ_BUFFER_HALF_SIZE);
			doRX_LPF_I(AUDIO_RX2, FPGA_RX_IQ_BUFFER_HALF_SIZE);
			doRX_NoiseBlanker(AUDIO_RX2, FPGA_RX_IQ_BUFFER_HALF_SIZE);
			if (TRX.NOISE_BLANKER1 || TRX.NOISE_BLANKER2) {
				doRX_LPF2_I(AUDIO_RX2, FPGA_RX_IQ_BUFFER_HALF_SIZE);
			}
			doRX_NOTCH(AUDIO_RX2, FPGA_RX_IQ_BUFFER_HALF_SIZE);
			doRX_SMETER(AUDIO_RX2, APROC_Audio_Buffer_RX2_I, FPGA_RX_IQ_BUFFER_HALF_SIZE, true);
			doVAD(AUDIO_RX2, FPGA_RX_IQ_BUFFER_HALF_SIZE);
			doRX_DNR(AUDIO_RX2, FPGA_RX_IQ_BUFFER_HALF_SIZE, SecondaryVFO->Mode, false);
			doRX_AGC(AUDIO_RX2, FPGA_RX_IQ_BUFFER_HALF_SIZE, SecondaryVFO->Mode, false);
			break;
		case TRX_MODE_DIGI_L:
			doRX_HILBERT(AUDIO_RX2, FPGA_RX_IQ_BUFFER_HALF_SIZE);
			arm_sub_f32(APROC_Audio_Buffer_RX2_I, APROC_Audio_Buffer_RX2_Q, APROC_Audio_Buffer_RX2_I, FPGA_RX_IQ_BUFFER_HALF_SIZE); // difference of I and Q - LSB
			doRX_HPF_I(AUDIO_RX2, FPGA_RX_IQ_BUFFER_HALF_SIZE);
			doRX_LPF_I(AUDIO_RX2, FPGA_RX_IQ_BUFFER_HALF_SIZE);
			doRX_SMETER(AUDIO_RX2, APROC_Audio_Buffer_RX2_I, FPGA_RX_IQ_BUFFER_HALF_SIZE, true);
			doRX_DNR(AUDIO_RX2, FPGA_RX_IQ_BUFFER_HALF_SIZE, SecondaryVFO->Mode, false);
			doRX_AGC(AUDIO_RX2, FPGA_RX_IQ_BUFFER_HALF_SIZE, SecondaryVFO->Mode, false);
			break;
		case TRX_MODE_USB:
			doRX_HILBERT(AUDIO_RX2, FPGA_RX_IQ_BUFFER_HALF_SIZE);
			arm_add_f32(APROC_Audio_Buffer_RX2_I, APROC_Audio_Buffer_RX2_Q, APROC_Audio_Buffer_RX2_I, FPGA_RX_IQ_BUFFER_HALF_SIZE); // sum of I and Q - USB
			doRX_HPF_I(AUDIO_RX2, FPGA_RX_IQ_BUFFER_HALF_SIZE);
			doRX_LPF_I(AUDIO_RX2, FPGA_RX_IQ_BUFFER_HALF_SIZE);
			doRX_NoiseBlanker(AUDIO_RX2, FPGA_RX_IQ_BUFFER_HALF_SIZE);
			if (TRX.NOISE_BLANKER1 || TRX.NOISE_BLANKER2) {
				doRX_LPF2_I(AUDIO_RX2, FPGA_RX_IQ_BUFFER_HALF_SIZE);
			}
			doRX_NOTCH(AUDIO_RX2, FPGA_RX_IQ_BUFFER_HALF_SIZE);
			doRX_SMETER(AUDIO_RX2, APROC_Audio_Buffer_RX2_I, FPGA_RX_IQ_BUFFER_HALF_SIZE, true);
			doVAD(AUDIO_RX2, FPGA_RX_IQ_BUFFER_HALF_SIZE);
			doRX_DNR(AUDIO_RX2, FPGA_RX_IQ_BUFFER_HALF_SIZE, SecondaryVFO->Mode, false);
			doRX_AGC(AUDIO_RX2, FPGA_RX_IQ_BUFFER_HALF_SIZE, SecondaryVFO->Mode, false);
			break;
		case TRX_MODE_RTTY:
		case TRX_MODE_DIGI_U:
			doRX_HILBERT(AUDIO_RX2, FPGA_RX_IQ_BUFFER_HALF_SIZE);
			arm_add_f32(APROC_Audio_Buffer_RX2_I, APROC_Audio_Buffer_RX2_Q, APROC_Audio_Buffer_RX2_I, FPGA_RX_IQ_BUFFER_HALF_SIZE); // sum of I and Q - USB
			doRX_HPF_I(AUDIO_RX2, FPGA_RX_IQ_BUFFER_HALF_SIZE);
			doRX_LPF_I(AUDIO_RX2, FPGA_RX_IQ_BUFFER_HALF_SIZE);
			doRX_SMETER(AUDIO_RX2, APROC_Audio_Buffer_RX2_I, FPGA_RX_IQ_BUFFER_HALF_SIZE, true);
			doRX_DNR(AUDIO_RX2, FPGA_RX_IQ_BUFFER_HALF_SIZE, SecondaryVFO->Mode, false);
			doRX_AGC(AUDIO_RX2, FPGA_RX_IQ_BUFFER_HALF_SIZE, SecondaryVFO->Mode, false);
			break;
		case TRX_MODE_AM:
			doRX_LPF_IQ(AUDIO_RX2, FPGA_RX_IQ_BUFFER_HALF_SIZE);
			arm_mult_f32(APROC_Audio_Buffer_RX2_I, APROC_Audio_Buffer_RX2_I, APROC_Audio_Buffer_RX2_I, FPGA_RX_IQ_BUFFER_HALF_SIZE);
			arm_mult_f32(APROC_Audio_Buffer_RX2_Q, APROC_Audio_Buffer_RX2_Q, APROC_Audio_Buffer_RX2_Q, FPGA_RX_IQ_BUFFER_HALF_SIZE);
			arm_add_f32(APROC_Audio_Buffer_RX2_I, APROC_Audio_Buffer_RX2_Q, APROC_Audio_Buffer_RX2_I, FPGA_RX_IQ_BUFFER_HALF_SIZE);
			for (uint_fast16_t i = 0; i < FPGA_RX_IQ_BUFFER_HALF_SIZE; i++) {
				arm_sqrt_f32(APROC_Audio_Buffer_RX2_I[i], &APROC_Audio_Buffer_RX2_I[i]);
			}
			arm_scale_f32(APROC_Audio_Buffer_RX2_I, 0.5f, APROC_Audio_Buffer_RX2_I, FPGA_RX_IQ_BUFFER_HALF_SIZE);
			doRX_NoiseBlanker(AUDIO_RX2, FPGA_RX_IQ_BUFFER_HALF_SIZE);
			dc_filter(APROC_Audio_Buffer_RX2_I, FPGA_RX_IQ_BUFFER_HALF_SIZE, DC_FILTER_RX2_I);
			doRX_LPF2_I(AUDIO_RX2, FPGA_RX_IQ_BUFFER_HALF_SIZE);
			doRX_NOTCH(AUDIO_RX2, FPGA_RX_IQ_BUFFER_HALF_SIZE);
			doRX_SMETER(AUDIO_RX2, APROC_Audio_Buffer_RX2_I, FPGA_RX_IQ_BUFFER_HALF_SIZE, true);
			doVAD(AUDIO_RX2, FPGA_RX_IQ_BUFFER_HALF_SIZE);
			doRX_DNR(AUDIO_RX2, FPGA_RX_IQ_BUFFER_HALF_SIZE, SecondaryVFO->Mode, false);
			doRX_AGC(AUDIO_RX2, FPGA_RX_IQ_BUFFER_HALF_SIZE, SecondaryVFO->Mode, false);
			break;
		case TRX_MODE_SAM_STEREO:
		case TRX_MODE_SAM_LSB:
		case TRX_MODE_SAM_USB:
			doRX_LPF_IQ(AUDIO_RX2, FPGA_RX_IQ_BUFFER_HALF_SIZE);
			doRX_DemodSAM(AUDIO_RX2, APROC_Audio_Buffer_RX2_I, APROC_Audio_Buffer_RX2_Q, APROC_Audio_Buffer_RX2_I, APROC_Audio_Buffer_RX2_Q, FPGA_RX_IQ_BUFFER_HALF_SIZE, SecondaryVFO->Mode);
			doRX_LPF2_IQ(AUDIO_RX2, FPGA_RX_IQ_BUFFER_HALF_SIZE);
			doRX_SMETER(AUDIO_RX2, APROC_Audio_Buffer_RX2_I, FPGA_RX_IQ_BUFFER_HALF_SIZE, true);
			doVAD(AUDIO_RX2, FPGA_RX_IQ_BUFFER_HALF_SIZE);
			doRX_DNR(AUDIO_RX2, FPGA_RX_IQ_BUFFER_HALF_SIZE, SecondaryVFO->Mode, true);
			doRX_AGC(AUDIO_RX2, FPGA_RX_IQ_BUFFER_HALF_SIZE, SecondaryVFO->Mode, true);
			break;
		case TRX_MODE_NFM:
			doRX_LPF_IQ(AUDIO_RX2, FPGA_RX_IQ_BUFFER_HALF_SIZE);
			doRX_SMETER(AUDIO_RX2, APROC_Audio_Buffer_RX2_I, FPGA_RX_IQ_BUFFER_HALF_SIZE, true);
			DemodulateFM(APROC_Audio_Buffer_RX2_I, APROC_Audio_Buffer_RX2_Q, AUDIO_RX2, FPGA_RX_IQ_BUFFER_HALF_SIZE, false, TRX_RX2_dBm);
			doRX_NoiseBlanker(AUDIO_RX2, FPGA_RX_IQ_BUFFER_HALF_SIZE);
			doRX_HPF_I(AUDIO_RX2, FPGA_RX_IQ_BUFFER_HALF_SIZE);
			doRX_LPF2_I(AUDIO_RX2, FPGA_RX_IQ_BUFFER_HALF_SIZE);
			doRX_IFGain(AUDIO_RX2, FPGA_RX_IQ_BUFFER_HALF_SIZE);
			doRX_NOTCH(AUDIO_RX2, FPGA_RX_IQ_BUFFER_HALF_SIZE);
			doRX_DNR(AUDIO_RX2, FPGA_RX_IQ_BUFFER_HALF_SIZE, SecondaryVFO->Mode, false);
			doRX_AGC(AUDIO_RX2, FPGA_RX_IQ_BUFFER_HALF_SIZE, SecondaryVFO->Mode, false);
			break;
		case TRX_MODE_WFM:
			doRX_LPF_IQ(AUDIO_RX2, FPGA_RX_IQ_BUFFER_HALF_SIZE);
			doRX_DNR(AUDIO_RX2, FPGA_RX_IQ_BUFFER_HALF_SIZE, SecondaryVFO->Mode, false);
			doRX_AGC(AUDIO_RX2, FPGA_RX_IQ_BUFFER_HALF_SIZE, SecondaryVFO->Mode, false);
			break;
		case TRX_MODE_IQ:
		default:
			doRX_SMETER(AUDIO_RX2, APROC_Audio_Buffer_RX2_I, FPGA_RX_IQ_BUFFER_HALF_SIZE, true);
			break;
		}
	}
#endif

	// Prepare Dual RX data to DMA
#if HRDW_HAS_DUAL_RX
	// addition of signals in double receive mode
	if (TRX.Dual_RX && TRX.Dual_RX_Type == VFO_A_PLUS_B) {
		float32_t balance = (((float32_t)TRX.Dual_RX_AB_Balance + 10.0f) / 20.0f);
		arm_scale_f32(APROC_Audio_Buffer_RX1_I, 1.0f - balance, APROC_Audio_Buffer_RX1_I, FPGA_RX_IQ_BUFFER_HALF_SIZE);
		arm_scale_f32(APROC_Audio_Buffer_RX2_I, balance, APROC_Audio_Buffer_RX2_I, FPGA_RX_IQ_BUFFER_HALF_SIZE);
		arm_add_f32(APROC_Audio_Buffer_RX1_I, APROC_Audio_Buffer_RX2_I, APROC_Audio_Buffer_RX1_I, FPGA_RX_IQ_BUFFER_HALF_SIZE);
	}
	if (TRX.Dual_RX && TRX.Dual_RX_Type == VFO_A_AND_B) {
		float32_t l_balance = TRX.Dual_RX_AB_Balance <= 0 ? 1.0f : 1.0f - ((float32_t)TRX.Dual_RX_AB_Balance / 10.0f);
		float32_t r_balance = TRX.Dual_RX_AB_Balance >= 0 ? 1.0f : 1.0f - ((float32_t)TRX.Dual_RX_AB_Balance / -10.0f);
		if (l_balance != 1.0f) {
			arm_scale_f32(APROC_Audio_Buffer_RX1_I, l_balance, APROC_Audio_Buffer_RX1_I, FPGA_RX_IQ_BUFFER_HALF_SIZE);
		}
		arm_scale_f32(APROC_Audio_Buffer_RX2_I, r_balance, APROC_Audio_Buffer_RX1_Q, FPGA_RX_IQ_BUFFER_HALF_SIZE);
	}
#endif

	// Recording to SD card
#if HRDW_HAS_SD
	if (SD_RecordInProcess) {
		for (uint_fast16_t i = 0; i < FPGA_RX_IQ_BUFFER_HALF_SIZE; i++) {
			arm_float_to_q15(&APROC_Audio_Buffer_RX1_I[i], &VOCODER_Buffer[VOCODER_Buffer_Index], 1); // left channel
			VOCODER_Buffer_Index++;
			if (VOCODER_Buffer_Index == SIZE_ADPCM_BLOCK) {
				VOCODER_Buffer_Index = 0;
				VOCODER_Process();
			}
		}
	}
#endif

	// receiver equalizer
	if (CurrentVFO->Mode != TRX_MODE_DIGI_L && CurrentVFO->Mode != TRX_MODE_DIGI_U && CurrentVFO->Mode != TRX_MODE_RTTY && CurrentVFO->Mode != TRX_MODE_IQ) {
		doRX_EQ(FPGA_RX_IQ_BUFFER_HALF_SIZE, CurrentVFO->Mode);
	}

	// muting
	if (TRX.Mute) {
		arm_scale_f32(APROC_Audio_Buffer_RX1_I, 0.0f, APROC_Audio_Buffer_RX1_I, FPGA_RX_IQ_BUFFER_HALF_SIZE);
		arm_scale_f32(APROC_Audio_Buffer_RX1_Q, 0.0f, APROC_Audio_Buffer_RX1_Q, FPGA_RX_IQ_BUFFER_HALF_SIZE);
	}

	// create buffers for transmission to the codec
	for (uint_fast16_t i = 0; i < FPGA_RX_IQ_BUFFER_HALF_SIZE; i++) {
#if HRDW_HAS_DUAL_RX
		if (!TRX.Dual_RX) {
			arm_float_to_q31(&APROC_Audio_Buffer_RX1_I[i], &APROC_AudioBuffer_out[i * 2], 1);     // left channel
			arm_float_to_q31(&APROC_Audio_Buffer_RX1_Q[i], &APROC_AudioBuffer_out[i * 2 + 1], 1); // right channel
#if FT8_SUPPORT
			arm_float_to_q15(&APROC_Audio_Buffer_RX1_Q[i], &APROC_AudioBuffer_FT8_out[i], 1); // FT8 Buffer - Tisho
#endif
		} else if (TRX.Dual_RX_Type == VFO_A_AND_B) {
			if (!TRX.selected_vfo) {
				arm_float_to_q31(&APROC_Audio_Buffer_RX1_I[i], &APROC_AudioBuffer_out[i * 2], 1);     // left channel
				arm_float_to_q31(&APROC_Audio_Buffer_RX1_Q[i], &APROC_AudioBuffer_out[i * 2 + 1], 1); // right channel
			} else {
				arm_float_to_q31(&APROC_Audio_Buffer_RX1_Q[i], &APROC_AudioBuffer_out[i * 2], 1);     // left channel
				arm_float_to_q31(&APROC_Audio_Buffer_RX1_I[i], &APROC_AudioBuffer_out[i * 2 + 1], 1); // right channel
			}
		} else if (TRX.Dual_RX_Type == VFO_A_PLUS_B) {
			arm_float_to_q31(&APROC_Audio_Buffer_RX1_I[i], &APROC_AudioBuffer_out[i * 2], 1); // left channel
			APROC_AudioBuffer_out[i * 2 + 1] = APROC_AudioBuffer_out[i * 2];                  // right channel
		}
#else
		arm_float_to_q31(&APROC_Audio_Buffer_RX1_I[i], &APROC_AudioBuffer_out[i * 2], 1);     // left channel
		arm_float_to_q31(&APROC_Audio_Buffer_RX1_Q[i], &APROC_AudioBuffer_out[i * 2 + 1], 1); // right channel
#if FT8_SUPPORT
		arm_float_to_q15(&APROC_Audio_Buffer_RX1_Q[i], &APROC_AudioBuffer_FT8_out[i], 1);     // FT8 Buffer - Tisho
#endif
#endif
	}

	// Send to USB Audio
	if (USB_AUDIO_need_rx_buffer && TRX_Inited) {
		uint8_t *USB_AUDIO_rx_buffer_current = USB_AUDIO_rx_buffer_b;
		if (!USB_AUDIO_current_rx_buffer) {
			USB_AUDIO_rx_buffer_current = USB_AUDIO_rx_buffer_a;
		}

		// drop LSB 32b->24/16b
		for (uint_fast16_t i = 0; i < (USB_AUDIO_RX_BUFFER_SIZE / BYTES_IN_SAMPLE_AUDIO_OUT_PACKET); i++) {
#if HRDW_USB_AUDIO_BITS == 16
			USB_AUDIO_rx_buffer_current[i * BYTES_IN_SAMPLE_AUDIO_OUT_PACKET + 0] = (APROC_AudioBuffer_out[i] >> 16) & 0xFF;
			USB_AUDIO_rx_buffer_current[i * BYTES_IN_SAMPLE_AUDIO_OUT_PACKET + 1] = (APROC_AudioBuffer_out[i] >> 24) & 0xFF;
#endif

#if HRDW_USB_AUDIO_BITS == 24
			USB_AUDIO_rx_buffer_current[i * BYTES_IN_SAMPLE_AUDIO_OUT_PACKET + 0] = (APROC_AudioBuffer_out[i] >> 8) & 0xFF;
			USB_AUDIO_rx_buffer_current[i * BYTES_IN_SAMPLE_AUDIO_OUT_PACKET + 1] = (APROC_AudioBuffer_out[i] >> 16) & 0xFF;
			USB_AUDIO_rx_buffer_current[i * BYTES_IN_SAMPLE_AUDIO_OUT_PACKET + 2] = (APROC_AudioBuffer_out[i] >> 24) & 0xFF;
#endif
		}
		USB_AUDIO_need_rx_buffer = false;
	}

	// Send to WIFI
	/*static uint32_t wifi_iq_buffer_index = 0;
	if(WIFI_maySendIQ)
	{
	  if(wifi_iq_buffer_index == 0) {
	    dma_memset(APROC_AudioBuffer_WIFI_out, 0x00, sizeof(APROC_AudioBuffer_WIFI_out));
	    strcpy((char *)APROC_AudioBuffer_WIFI_out, "IQ:");
	    wifi_iq_buffer_index += 3;
	  }

	  for (uint_fast16_t i = 0; i < (FPGA_RX_IQ_BUFFER_HALF_SIZE / 8); i++)  // 6kbps
	    APROC_AudioBuffer_WIFI_out[wifi_iq_buffer_index + i * 8] = (APROC_AudioBuffer_out[i] >> 24) & 0xFF; // 32->8 bit
	  wifi_iq_buffer_index += (FPGA_RX_IQ_BUFFER_HALF_SIZE / 8);

	  if(wifi_iq_buffer_index >= 1900)
	  {
	    WIFI_SendIQData(APROC_AudioBuffer_WIFI_out, wifi_iq_buffer_index);

	    wifi_iq_buffer_index = 0;
	  }
	}*/

	// Tisho
	/*FT-8 decoding (fill the FT8 Buffer)
	 *
	 * It is performed down sampling (take every 8-th sample from the main stream (192 size buffer)) - the APROC_AudioBuffer_FT8_out is filled with
	 * q15_t data (48kHz sample rate) the "input_gulp" it is filled with 6kHz (48kHz/8) - remining 24 samples from the initial 192 the "input_gulp"
	 * is complete every 160ms ! this is repeat 40 times, till all 40*24 => 960 samples are colected (the size of the "input_gulp")
	 */
#if FT8_SUPPORT
	if (FT8_DecodeActiveFlg) // if "true"
	{
		if (FT8_ColectDataFlg)         // if "true"
		{                              // FT8_DatBlockNum > num_que_blocks (40)
			if (FT8_DatBlockNum >= 40) { // extreme case (the bufer was not read - need to zero the index to avoid overflow)
				FT8_DatBlockNum = 0;
			}

			for (uint32_t pos = 0; pos < AUDIO_BUFFER_HALF_SIZE / 8; pos++) {
				input_gulp[pos + (FT8_DatBlockNum * AUDIO_BUFFER_HALF_SIZE / 8)] = APROC_AudioBuffer_FT8_out[pos * 8]; //
			}
			FT8_DatBlockNum++;
		}
	}
#endif

	// Volume Gain and SPI convert
	float32_t volume_gain_new = volume2rate((float32_t)TRX.Volume / MAX_VOLUME_VALUE);
	volume_gain = 0.9f * volume_gain + 0.1f * volume_gain_new;

	for (uint_fast16_t i = 0; i < (FPGA_RX_IQ_BUFFER_HALF_SIZE * 2); i++) {
		// Gain
		APROC_AudioBuffer_out[i] = (int32_t)((float32_t)APROC_AudioBuffer_out[i] * volume_gain);
		// Codec SPI
		APROC_AudioBuffer_out[i] = convertToSPIBigEndian(APROC_AudioBuffer_out[i]); // for 32bit audio
	}

	// Beep signal
	static float32_t beep_index = 0;
	static uint32_t beep_samples = 0;
	if (CODEC_Beeping) {
		float32_t old_signal = 0;
		int32_t out = 0;
		bool halted = false;
		float32_t amplitude = volume2rate((float32_t)TRX.Volume / MAX_VOLUME_VALUE) * 0.1f;
		for (uint32_t pos = 0; pos < AUDIO_BUFFER_HALF_SIZE; pos++) {
			float32_t signal = generateSin(amplitude, &beep_index, TRX_SAMPLERATE, 1500);
			arm_float_to_q31(&signal, &out, 1);
			int32_t sample = convertToSPIBigEndian(out);

			if (CODEC_Beeping_Left) {
				APROC_AudioBuffer_out[pos * 2] = sample; // left channel
			} else {
				APROC_AudioBuffer_out[pos * 2] = 0;
			}

			if (CODEC_Beeping_Right) {
				APROC_AudioBuffer_out[pos * 2 + 1] = sample; // right channel
			} else {
				APROC_AudioBuffer_out[pos * 2 + 1] = 0;
			}

			if (beep_samples >= 20 && old_signal < 0 && signal >= 0) {
				halted = true;
				break;
			}
			old_signal = signal;
		}
		beep_samples++;
		if (halted) {
			beep_index = 0;
			beep_samples = 0;
			CODEC_Beeping = false;
			CODEC_Beeping_Left = false;
			CODEC_Beeping_Right = false;
		}
	}

	// Mute codec if need
	APROC_ProcessCodecMuting();

	// Send to Codec DMA
	if (TRX_Inited) {
		Aligned_CleanDCache_by_Addr((uint32_t *)&APROC_AudioBuffer_out[0], sizeof(APROC_AudioBuffer_out));
		if (CODEC_DMA_state) // complete
		{
#if HRDW_HAS_MDMA
			HAL_MDMA_Start(&HRDW_AUDIO_COPY_MDMA, (uint32_t)&APROC_AudioBuffer_out[0], (uint32_t)&CODEC_Audio_Buffer_RX[AUDIO_BUFFER_SIZE], CODEC_AUDIO_BUFFER_HALF_SIZE * 4, 1); //*2 -> left_right
			SLEEPING_MDMA_PollForTransfer(&HRDW_AUDIO_COPY_MDMA);
#else
			HAL_DMA_Start(&HRDW_AUDIO_COPY_DMA, (uint32_t)&APROC_AudioBuffer_out[0], (uint32_t)&CODEC_Audio_Buffer_RX[AUDIO_BUFFER_SIZE],
			              CODEC_AUDIO_BUFFER_HALF_SIZE); //*2 -> left_right
			SLEEPING_DMA_PollForTransfer(&HRDW_AUDIO_COPY_DMA);
#endif
		} else // half
		{
#if HRDW_HAS_MDMA
			HAL_MDMA_Start(&HRDW_AUDIO_COPY2_MDMA, (uint32_t)&APROC_AudioBuffer_out[0], (uint32_t)&CODEC_Audio_Buffer_RX[0], CODEC_AUDIO_BUFFER_HALF_SIZE * 4, 1); //*2 -> left_right
			SLEEPING_MDMA_PollForTransfer(&HRDW_AUDIO_COPY2_MDMA);
#else
			HAL_DMA_Start(&HRDW_AUDIO_COPY2_DMA, (uint32_t)&APROC_AudioBuffer_out[0], (uint32_t)&CODEC_Audio_Buffer_RX[0],
			              CODEC_AUDIO_BUFFER_HALF_SIZE); //*2 -> left_right
			SLEEPING_DMA_PollForTransfer(&HRDW_AUDIO_COPY2_DMA);
#endif
		}
	}

	Processor_NeedRXBuffer = false;
}

// start audio processor for TX
void processTxAudio(void) {
	if (!Processor_NeedTXBuffer) {
		return;
	}

	// sync fpga to audio-codec
	static bool old_CODEC_DMA_state = false;
	bool start_CODEC_DMA_state = CODEC_DMA_state;

	if (start_CODEC_DMA_state == old_CODEC_DMA_state && getInputType() != TRX_INPUT_USB) {
		return;
	}

	uint32_t dma_index = HRDW_getAudioCodecTX_DMAIndex();
	if (!start_CODEC_DMA_state && dma_index > (CODEC_AUDIO_BUFFER_SIZE * 2 - 150)) {
		return;
	}
	if (start_CODEC_DMA_state && dma_index > (CODEC_AUDIO_BUFFER_SIZE - 150)) {
		return;
	}

	old_CODEC_DMA_state = start_CODEC_DMA_state;

	// stuff
	AUDIOPROC_samples++;
	TRX_MODE mode = CurrentVFO->Mode;

	if (getInputType() == TRX_INPUT_USB) // USB AUDIO
	{
		uint32_t buffer_index = USB_AUDIO_GetTXBufferIndex_FS() / BYTES_IN_SAMPLE_AUDIO_OUT_PACKET; // buffer 8bit, data 24 bit
		if (buffer_index >= (USB_AUDIO_TX_BUFFER_SIZE / BYTES_IN_SAMPLE_AUDIO_OUT_PACKET)) {
			buffer_index = 0;
		}
		if ((buffer_index % BYTES_IN_SAMPLE_AUDIO_OUT_PACKET) == 1) {
			buffer_index -= (buffer_index % BYTES_IN_SAMPLE_AUDIO_OUT_PACKET);
		}

#if HRDW_USB_AUDIO_BITS == 16
		readHalfFromCircleUSBBuffer16Bit(&USB_AUDIO_tx_buffer[0], &APROC_AudioBuffer_out[0], buffer_index, (USB_AUDIO_TX_BUFFER_SIZE / BYTES_IN_SAMPLE_AUDIO_OUT_PACKET));
#endif

#if HRDW_USB_AUDIO_BITS == 24
		readHalfFromCircleUSBBuffer24Bit(&USB_AUDIO_tx_buffer[0], &APROC_AudioBuffer_out[0], buffer_index, (USB_AUDIO_TX_BUFFER_SIZE / BYTES_IN_SAMPLE_AUDIO_OUT_PACKET));
#endif
	} else // AUDIO CODEC AUDIO
	{
		uint32_t dma_index_rx = HRDW_getAudioCodecRX_DMAIndex();
		if ((dma_index_rx % 2) == 1) {
			dma_index_rx--;
		}
		readFromCircleBuffer32((uint32_t *)&CODEC_Audio_Buffer_TX[0], (uint32_t *)&APROC_AudioBuffer_out[0], dma_index_rx, CODEC_AUDIO_BUFFER_SIZE, AUDIO_BUFFER_SIZE);
	}

#if HRDW_HAS_SD
	// Play CQ message
	if (SD_PlayCQMessageInProcess && SD_PlayInProcess) {
		while (!APROC_SD_PlayTX()) {
			; // false - data not ready, continue decoding
		}
	}
#endif

#if FT8_SUPPORT
	// Tisho - FT8
	// used in the transmit period to generate time interval when process_data(); is executed => and then set high the "DSP_Flag"
	if (FT8_DecodeActiveFlg) // if "true"
	{
		if (FT8_DatBlockNum >= 40) { // extreme case (the bufer was not read - need to zero the index to avoid overflow)
			FT8_DatBlockNum = 0;
		}

		if (FT8_ColectDataFlg) { // if "true"
			FT8_DatBlockNum++;
		}
	}
#endif
	// One-signal zero-tune generator
	if (TRX_Tune && !TRX.TWO_SIGNAL_TUNE) {
		for (uint_fast16_t i = 0; i < AUDIO_BUFFER_HALF_SIZE; i++) {
			APROC_Audio_Buffer_TX_I[i] = 1.0f;
			APROC_Audio_Buffer_TX_Q[i] = 0.0f;
		}
	}

	// FT8 signal generator
	if (TRX_Tune && !TRX.TWO_SIGNAL_TUNE && (CurrentVFO->Mode == TRX_MODE_DIGI_U || CurrentVFO->Mode == TRX_MODE_DIGI_L)) {
		if (APROC_TUNE_DigiTone_Freq == 0) { // default tune
			for (uint_fast16_t i = 0; i < AUDIO_BUFFER_HALF_SIZE; i++) {
				APROC_Audio_Buffer_TX_I[i] = 1.0f;
				APROC_Audio_Buffer_TX_Q[i] = 0.0f;
			}
		} else {
			static float32_t ft8_signal_gen_index = 0;
			static float32_t ft8_signal_gen_prev_freq = 1000.0f;
			for (uint_fast16_t i = 0; i < AUDIO_BUFFER_HALF_SIZE; i++) {

				float32_t point = generateSinWithZeroCrossing(1.0f, &ft8_signal_gen_index, TRX_SAMPLERATE, &ft8_signal_gen_prev_freq, APROC_TUNE_DigiTone_Freq);
				APROC_Audio_Buffer_TX_I[i] = point;
				APROC_Audio_Buffer_TX_Q[i] = point;
			}

			// hilbert fir
			if (mode == TRX_MODE_LSB || mode == TRX_MODE_DIGI_L) {
				doTX_HILBERT(false, AUDIO_BUFFER_HALF_SIZE);
			} else if (mode == TRX_MODE_DIGI_U) {
				doTX_HILBERT(true, AUDIO_BUFFER_HALF_SIZE);
			}
		}
	}

	// Two-signal tune generator
	if (TRX_Tune && TRX.TWO_SIGNAL_TUNE) {
		static float32_t two_signal_gen_index1 = 0;
		static float32_t two_signal_gen_index2 = 0;
		for (uint_fast16_t i = 0; i < AUDIO_BUFFER_HALF_SIZE; i++) {
			float32_t balance = (float32_t)CALIBRATE.TwoSignalTune_Balance / 100.0f;

			float32_t point = generateSin(balance, &two_signal_gen_index1, TRX_SAMPLERATE, TWO_TONE_GEN_FREQ1);
			point += generateSin((1.0f - balance), &two_signal_gen_index2, TRX_SAMPLERATE, TWO_TONE_GEN_FREQ2);
			APROC_Audio_Buffer_TX_I[i] = point;
			APROC_Audio_Buffer_TX_Q[i] = point;
		}

		// hilbert fir
		if (mode == TRX_MODE_LSB || mode == TRX_MODE_DIGI_L) {
			doTX_HILBERT(false, AUDIO_BUFFER_HALF_SIZE);
		} else if (mode == TRX_MODE_USB || mode == TRX_MODE_DIGI_U || mode == TRX_MODE_CW || mode == TRX_MODE_RTTY) {
			doTX_HILBERT(true, AUDIO_BUFFER_HALF_SIZE);
		} else if (mode == TRX_MODE_AM) {
			doTX_HILBERT(false, AUDIO_BUFFER_HALF_SIZE);
			for (size_t i = 0; i < AUDIO_BUFFER_HALF_SIZE; i++) {
				float32_t i_am = ((APROC_Audio_Buffer_TX_I[i] - APROC_Audio_Buffer_TX_Q[i]) + 1.0f);
				float32_t q_am = ((APROC_Audio_Buffer_TX_Q[i] - APROC_Audio_Buffer_TX_I[i]) - 1.0f);
				APROC_Audio_Buffer_TX_I[i] = i_am / 2.0f;
				APROC_Audio_Buffer_TX_Q[i] = q_am / 2.0f;
			}
		}
	}

	// FM tone generator
	if (TRX_Tune && (mode == TRX_MODE_NFM || mode == TRX_MODE_WFM)) {
		static uint32_t tone_counter = 100;
		tone_counter++;
		if (tone_counter >= 400) {
			tone_counter = 0;
		}
		for (uint_fast16_t i = 0; i < AUDIO_BUFFER_HALF_SIZE; i++) {
			static float32_t fm_signal_gen_index = 0;
			float32_t point = 0.0f;
			if (tone_counter > 300) {
				point = generateSin(1.0f, &fm_signal_gen_index, TRX_SAMPLERATE, 3500);
			} else if (tone_counter > 200) {
				point = generateSin(1.0f, &fm_signal_gen_index, TRX_SAMPLERATE, 2000);
			} else if (tone_counter > 100) {
				point = generateSin(1.0f, &fm_signal_gen_index, TRX_SAMPLERATE, 1000);
			}

			APROC_Audio_Buffer_TX_I[i] = point;
			APROC_Audio_Buffer_TX_Q[i] = point;
		}
		ModulateFM(AUDIO_BUFFER_HALF_SIZE, 1.0f);
	}

	if (!TRX_Tune) {
// Copy and convert buffer
#ifndef STM32F407xx
		for (uint_fast16_t i = 0; i < AUDIO_BUFFER_HALF_SIZE; i++) {
			APROC_Audio_Buffer_TX_I[i] = (float32_t)APROC_AudioBuffer_out[i * 2] / 2147483648.0f;
			APROC_Audio_Buffer_TX_Q[i] = (float32_t)APROC_AudioBuffer_out[i * 2 + 1] / 2147483648.0f;
		}
#else
		if (getInputType() == TRX_INPUT_USB) {
			for (uint_fast16_t i = 0; i < AUDIO_BUFFER_HALF_SIZE; i++) {
				APROC_Audio_Buffer_TX_I[i] = (float32_t)APROC_AudioBuffer_out[i * 2] / 2147483648.0f;
				APROC_Audio_Buffer_TX_Q[i] = (float32_t)APROC_AudioBuffer_out[i * 2 + 1] / 2147483648.0f;
			}
		} else {
			for (uint_fast16_t i = 0; i < AUDIO_BUFFER_HALF_SIZE; i++) {
				APROC_Audio_Buffer_TX_I[i] = (float32_t)convertToSPIBigEndian(APROC_AudioBuffer_out[i * 2]) / 2147483648.0f;
				APROC_Audio_Buffer_TX_Q[i] = (float32_t)convertToSPIBigEndian(APROC_AudioBuffer_out[i * 2 + 1]) / 2147483648.0f;
			}
		}
#endif

#if HRDW_HAS_SD
		if (!SD_PlayCQMessageInProcess && !SD_PlayInProcess)
#endif
		{
			if (getInputType() == TRX_INPUT_MIC) {
				// Mic Gain
				float32_t mic_gain = rate2dbP(TRX.MIC_Gain_SSB_DB);
				if (mode == TRX_MODE_AM || mode == TRX_MODE_SAM_STEREO || mode == TRX_MODE_SAM_LSB || mode == TRX_MODE_SAM_USB) {
					mic_gain = rate2dbP(TRX.MIC_Gain_AM_DB);
				}
				if (mode == TRX_MODE_NFM || mode == TRX_MODE_WFM) {
					mic_gain = rate2dbP(TRX.MIC_Gain_FM_DB);
				}
				arm_scale_f32(APROC_Audio_Buffer_TX_I, mic_gain, APROC_Audio_Buffer_TX_I, AUDIO_BUFFER_HALF_SIZE);
				arm_scale_f32(APROC_Audio_Buffer_TX_Q, mic_gain, APROC_Audio_Buffer_TX_Q, AUDIO_BUFFER_HALF_SIZE);
				// Mic Equalizer
				if (mode != TRX_MODE_DIGI_L && mode != TRX_MODE_DIGI_U && mode != TRX_MODE_RTTY && mode != TRX_MODE_IQ) {
					doMIC_EQ(AUDIO_BUFFER_HALF_SIZE, mode);
				}
			}

			// USB Gain (24bit)
			if (getInputType() == TRX_INPUT_USB) {
				arm_scale_f32(APROC_Audio_Buffer_TX_I, 1.1f, APROC_Audio_Buffer_TX_I, AUDIO_BUFFER_HALF_SIZE);
				arm_scale_f32(APROC_Audio_Buffer_TX_Q, 1.1f, APROC_Audio_Buffer_TX_Q, AUDIO_BUFFER_HALF_SIZE);
			}
		}

		// Process DC corrector filter
		dc_filter(APROC_Audio_Buffer_TX_I, AUDIO_BUFFER_HALF_SIZE, DC_FILTER_TX_I);
		dc_filter(APROC_Audio_Buffer_TX_Q, AUDIO_BUFFER_HALF_SIZE, DC_FILTER_TX_Q);
	}

	if (mode != TRX_MODE_IQ && !TRX_Tune) {
		// IIR HPF
		if (CurrentVFO->HPF_TX_Filter_Width > 0) {
			arm_biquad_cascade_df2T_f32_single(&IIR_TX_HPF_I, APROC_Audio_Buffer_TX_I, APROC_Audio_Buffer_TX_I, AUDIO_BUFFER_HALF_SIZE);
		}

		// IIR LPF
		if (CurrentVFO->LPF_TX_Filter_Width > 0) {
			arm_biquad_cascade_df2T_f32_single(&IIR_TX_LPF_I, APROC_Audio_Buffer_TX_I, APROC_Audio_Buffer_TX_I, AUDIO_BUFFER_HALF_SIZE);
		}

		// TX AGC (compressor)
		if (mode == TRX_MODE_AM || mode == TRX_MODE_SAM_STEREO || mode == TRX_MODE_SAM_LSB || mode == TRX_MODE_SAM_USB) {
			DoTxAGC(APROC_Audio_Buffer_TX_I, AUDIO_BUFFER_HALF_SIZE, 0.7f, mode);
			arm_scale_f32(APROC_Audio_Buffer_TX_I, ((float32_t)CALIBRATE.AM_MODULATION_INDEX / 200.0f) * APROC_TX_clip_gain, APROC_Audio_Buffer_TX_I, AUDIO_BUFFER_HALF_SIZE);
		} else if (mode != TRX_MODE_DIGI_L && mode != TRX_MODE_DIGI_U) { // disable AGC on DIGI
			DoTxAGC(APROC_Audio_Buffer_TX_I, AUDIO_BUFFER_HALF_SIZE, 1.00f * APROC_TX_clip_gain, mode);
		}

		// double left and right channel
		dma_memcpy(&APROC_Audio_Buffer_TX_Q[0], &APROC_Audio_Buffer_TX_I[0], sizeof(APROC_Audio_Buffer_TX_Q));

		switch (mode) {
		case TRX_MODE_CW:
			for (uint_fast16_t i = 0; i < AUDIO_BUFFER_HALF_SIZE; i++) {
				APROC_Audio_Buffer_TX_I[i] = CW_GenerateSignal(1.0f);
				APROC_Audio_Buffer_TX_Q[i] = 0.0f;
			}
			DECODER_PutSamples(APROC_Audio_Buffer_TX_I, AUDIO_BUFFER_HALF_SIZE); // отправляем данные в цифровой декодер
			break;
		case TRX_MODE_USB:
		case TRX_MODE_RTTY:
		case TRX_MODE_DIGI_U:
			doTX_CESSB(AUDIO_BUFFER_HALF_SIZE, mode);
			doTX_HILBERT(true, AUDIO_BUFFER_HALF_SIZE);
			break;
		case TRX_MODE_LSB:
		case TRX_MODE_DIGI_L:
			doTX_CESSB(AUDIO_BUFFER_HALF_SIZE, mode);
			doTX_HILBERT(false, AUDIO_BUFFER_HALF_SIZE);
			break;
		case TRX_MODE_AM:
		case TRX_MODE_SAM_STEREO:
		case TRX_MODE_SAM_LSB:
		case TRX_MODE_SAM_USB:
			doTX_HILBERT(false, AUDIO_BUFFER_HALF_SIZE);
			for (size_t i = 0; i < AUDIO_BUFFER_HALF_SIZE; i++) {
				float32_t i_am = ((APROC_Audio_Buffer_TX_I[i] - APROC_Audio_Buffer_TX_Q[i]) + 1.0f * APROC_TX_clip_gain);
				float32_t q_am = ((APROC_Audio_Buffer_TX_Q[i] - APROC_Audio_Buffer_TX_I[i]) - 1.0f * APROC_TX_clip_gain);
				APROC_Audio_Buffer_TX_I[i] = i_am;
				APROC_Audio_Buffer_TX_Q[i] = q_am;
			}
			break;
		case TRX_MODE_NFM:
		case TRX_MODE_WFM:
			ModulateFM(AUDIO_BUFFER_HALF_SIZE, 1.0f);
			break;
		case TRX_MODE_LOOPBACK:
			doTX_CESSB(AUDIO_BUFFER_HALF_SIZE, mode);
			DECODER_PutSamples(APROC_Audio_Buffer_TX_I, AUDIO_BUFFER_HALF_SIZE); // отправляем данные в цифровой декодер
			break;
		default:
			break;
		}
	}

	// Send TX data to FFT
	if (TRX_on_TX && !SHOW_RX_FFT_ON_TX) {
		float32_t *FFTInput_I_current_ = FFT_buff_current ? (float32_t *)&FFTInput_I_A : (float32_t *)&FFTInput_I_B;
		float32_t *FFTInput_Q_current_ = FFT_buff_current ? (float32_t *)&FFTInput_Q_A : (float32_t *)&FFTInput_Q_B;

		for (uint_fast16_t i = 0; i < AUDIO_BUFFER_HALF_SIZE; i++) {
			FFTInput_I_current_[FFT_buff_index] = APROC_Audio_Buffer_TX_I[i];
			FFTInput_Q_current_[FFT_buff_index] = APROC_Audio_Buffer_TX_Q[i];

			FFT_buff_index++;
			if (FFT_buff_index >= FFT_HALF_SIZE) {
				FFT_buff_index = 0;
				if (FFT_new_buffer_ready) {
					// sendToDebug_str("fft overrun");
				} else {
					FFT_new_buffer_ready = true;
					FFT_buff_current = !FFT_buff_current;
					FFTInput_I_current_ = FFT_buff_current ? (float32_t *)&FFTInput_I_A : (float32_t *)&FFTInput_I_B;
					FFTInput_Q_current_ = FFT_buff_current ? (float32_t *)&FFTInput_Q_A : (float32_t *)&FFTInput_Q_B;
				}
			}
		}
	}

	float32_t selfhear_amplitude = volume2rate((float32_t)TRX.SELFHEAR_Volume / 100.0f);

#if HRDW_HAS_SD
	// SD card send
	if (SD_RecordInProcess) {
		for (uint_fast16_t i = 0; i < AUDIO_BUFFER_HALF_SIZE; i++) {
			arm_float_to_q15(&APROC_Audio_Buffer_TX_I[i], &VOCODER_Buffer[VOCODER_Buffer_Index], 1); // left channel

			if (mode == TRX_MODE_CW) { // CW generator
				static float32_t sdrecord_cwgen_index = 0;
				float32_t point = generateSin(selfhear_amplitude * APROC_Audio_Buffer_TX_I[i], &sdrecord_cwgen_index, TRX_SAMPLERATE, TRX.CW_Pitch);
				arm_float_to_q15(&point, &VOCODER_Buffer[VOCODER_Buffer_Index], 1);
			}

			VOCODER_Buffer_Index++;
			if (VOCODER_Buffer_Index == SIZE_ADPCM_BLOCK) {
				VOCODER_Buffer_Index = 0;
				VOCODER_Process();
			}
		}
	}
#endif

	// Prepare codec out data
	float32_t volume_gain_tx = volume2rate((float32_t)TRX.Volume / MAX_VOLUME_VALUE);
#if HRDW_HAS_SD
	if (!SD_PlayCQMessageInProcess && !SD_PlayInProcess) {
		volume_gain_tx *= selfhear_amplitude;
	} else {
		// reduce power for SD play
		volume_gain_tx *= 0.3f;
		arm_scale_f32(APROC_Audio_Buffer_TX_I, 0.9f, APROC_Audio_Buffer_TX_I, AUDIO_BUFFER_HALF_SIZE);
		arm_scale_f32(APROC_Audio_Buffer_TX_Q, 0.9f, APROC_Audio_Buffer_TX_Q, AUDIO_BUFFER_HALF_SIZE);
	}
#else
	volume_gain_tx *= selfhear_amplitude;
#endif

	for (uint_fast16_t i = 0; i < AUDIO_BUFFER_HALF_SIZE; i++) {
		float32_t sample = APROC_Audio_Buffer_TX_I[i] * volume_gain_tx;
		arm_float_to_q31(&sample, &APROC_AudioBuffer_out[i * 2], 1);
		APROC_AudioBuffer_out[i * 2] = convertToSPIBigEndian(APROC_AudioBuffer_out[i * 2]); // left channel
		APROC_AudioBuffer_out[i * 2 + 1] = APROC_AudioBuffer_out[i * 2];                    // right channel
	}

	// Loopback/DIGI mode self-hearing
	bool has_self_hearing_data = false;
#if HRDW_HAS_SD
	if ((!SD_RecordInProcess && mode == TRX_MODE_LOOPBACK) || mode == TRX_MODE_DIGI_L || mode == TRX_MODE_DIGI_U || mode == TRX_MODE_RTTY || SD_PlayCQMessageInProcess || SD_PlayInProcess)
#else
	if (mode == TRX_MODE_LOOPBACK || mode == TRX_MODE_DIGI_L || mode == TRX_MODE_DIGI_U || mode == TRX_MODE_RTTY)
#endif
	{
		// Send to USB Audio
		if (USB_AUDIO_need_rx_buffer && TRX_Inited && !LISTEN_RX_AUDIO_ON_TX) {
			uint8_t *USB_AUDIO_rx_buffer_current = USB_AUDIO_rx_buffer_b;
			if (!USB_AUDIO_current_rx_buffer) {
				USB_AUDIO_rx_buffer_current = USB_AUDIO_rx_buffer_a;
			}

			// drop LSB 32b->24/16b
			for (uint_fast16_t i = 0; i < (USB_AUDIO_RX_BUFFER_SIZE / BYTES_IN_SAMPLE_AUDIO_OUT_PACKET); i++) {
#if HRDW_USB_AUDIO_BITS == 16
				USB_AUDIO_rx_buffer_current[i * BYTES_IN_SAMPLE_AUDIO_OUT_PACKET + 0] = (APROC_AudioBuffer_out[i] >> 16) & 0xFF;
				USB_AUDIO_rx_buffer_current[i * BYTES_IN_SAMPLE_AUDIO_OUT_PACKET + 1] = (APROC_AudioBuffer_out[i] >> 24) & 0xFF;
#endif

#if HRDW_USB_AUDIO_BITS == 24
				USB_AUDIO_rx_buffer_current[i * BYTES_IN_SAMPLE_AUDIO_OUT_PACKET + 0] = (APROC_AudioBuffer_out[i] >> 8) & 0xFF;
				USB_AUDIO_rx_buffer_current[i * BYTES_IN_SAMPLE_AUDIO_OUT_PACKET + 1] = (APROC_AudioBuffer_out[i] >> 16) & 0xFF;
				USB_AUDIO_rx_buffer_current[i * BYTES_IN_SAMPLE_AUDIO_OUT_PACKET + 2] = (APROC_AudioBuffer_out[i] >> 24) & 0xFF;
#endif
			}
			USB_AUDIO_need_rx_buffer = false;
		}

		// Mute codec if need
		APROC_ProcessCodecMuting();

		// Send to Codec
		if (!LISTEN_RX_AUDIO_ON_TX) {
			has_self_hearing_data = true;
			Aligned_CleanDCache_by_Addr((uint32_t *)&APROC_AudioBuffer_out[0], sizeof(APROC_AudioBuffer_out));
			if (start_CODEC_DMA_state) // compleate
			{
#if HRDW_HAS_MDMA
				HAL_MDMA_Start(&HRDW_AUDIO_COPY_MDMA, (uint32_t)&APROC_AudioBuffer_out[0], (uint32_t)&CODEC_Audio_Buffer_RX[AUDIO_BUFFER_SIZE], AUDIO_BUFFER_SIZE * 4, 1);
				SLEEPING_MDMA_PollForTransfer(&HRDW_AUDIO_COPY_MDMA);
#else
				HAL_DMA_Start(&HRDW_AUDIO_COPY_DMA, (uint32_t)&APROC_AudioBuffer_out[0], (uint32_t)&CODEC_Audio_Buffer_RX[AUDIO_BUFFER_SIZE], AUDIO_BUFFER_SIZE);
				SLEEPING_DMA_PollForTransfer(&HRDW_AUDIO_COPY_DMA);
#endif
			} else // half
			{
#if HRDW_HAS_MDMA
				HAL_MDMA_Start(&HRDW_AUDIO_COPY2_MDMA, (uint32_t)&APROC_AudioBuffer_out[0], (uint32_t)&CODEC_Audio_Buffer_RX[0], AUDIO_BUFFER_SIZE * 4, 1);
				SLEEPING_MDMA_PollForTransfer(&HRDW_AUDIO_COPY2_MDMA);
#else
				HAL_DMA_Start(&HRDW_AUDIO_COPY2_DMA, (uint32_t)&APROC_AudioBuffer_out[0], (uint32_t)&CODEC_Audio_Buffer_RX[0], AUDIO_BUFFER_SIZE);
				SLEEPING_DMA_PollForTransfer(&HRDW_AUDIO_COPY2_DMA);
#endif
			}
		}
	}

	// CW SelfHear
	if (!LISTEN_RX_AUDIO_ON_TX) {
		if (TRX.CW_SelfHear && mode == TRX_MODE_CW && !TRX_Tune) {
			static float32_t cwgen_index = 0;
			for (uint_fast16_t i = 0; i < AUDIO_BUFFER_HALF_SIZE; i++) {
				float32_t point = generateSin(selfhear_amplitude * APROC_Audio_Buffer_TX_I[i], &cwgen_index, TRX_SAMPLERATE, TRX.CW_Pitch);
				int32_t sample = 0;
				arm_float_to_q31(&point, &sample, 1);
				int32_t data = convertToSPIBigEndian(sample);

				if (TRX.RX_AUDIO_MODE == RX_AUDIO_MODE_STEREO) {
					if (start_CODEC_DMA_state) {
						CODEC_Audio_Buffer_RX[AUDIO_BUFFER_SIZE + i * 2] = data;
						CODEC_Audio_Buffer_RX[AUDIO_BUFFER_SIZE + i * 2 + 1] = data;
					} else {
						CODEC_Audio_Buffer_RX[i * 2] = data;
						CODEC_Audio_Buffer_RX[i * 2 + 1] = data;
					}
				}
				if (TRX.RX_AUDIO_MODE == RX_AUDIO_MODE_LEFT) {
					if (start_CODEC_DMA_state) {
						CODEC_Audio_Buffer_RX[AUDIO_BUFFER_SIZE + i * 2] = data;
						CODEC_Audio_Buffer_RX[AUDIO_BUFFER_SIZE + i * 2 + 1] = 0;
					} else {
						CODEC_Audio_Buffer_RX[i * 2] = data;
						CODEC_Audio_Buffer_RX[i * 2 + 1] = 0;
					}
				}
				if (TRX.RX_AUDIO_MODE == RX_AUDIO_MODE_RIGHT) {
					if (start_CODEC_DMA_state) {
						CODEC_Audio_Buffer_RX[AUDIO_BUFFER_SIZE + i * 2] = 0;
						CODEC_Audio_Buffer_RX[AUDIO_BUFFER_SIZE + i * 2 + 1] = data;
					} else {
						CODEC_Audio_Buffer_RX[i * 2] = 0;
						CODEC_Audio_Buffer_RX[i * 2 + 1] = data;
					}
				}
			}
			Aligned_CleanDCache_by_Addr((uint32_t *)&CODEC_Audio_Buffer_RX[0], sizeof(CODEC_Audio_Buffer_RX));
			has_self_hearing_data = true;
		}

		// clean RX codec buffer
		if (!has_self_hearing_data) {
			dma_memset(CODEC_Audio_Buffer_RX, 0x00, sizeof CODEC_Audio_Buffer_RX);
			Aligned_CleanDCache_by_Addr((uint32_t *)&CODEC_Audio_Buffer_RX[0], sizeof(CODEC_Audio_Buffer_RX));
		}
	}

	//// RF PowerControl (Audio Level Control)

	// amplitude for the selected power and range
	float32_t RF_Power_selected = getPowerFromALC(); // get from ALC
	if (RF_Power_selected == -1) {                   // ALC disabled
		RF_Power_selected = (float32_t)TRX.RF_Gain;
		if ((mode == TRX_MODE_LSB || mode == TRX_MODE_USB) && !TRX_Tune) {
			RF_Power_selected += CALIBRATE.SSB_POWER_ADDITION;
		}
	}

	if (TRX_SWR_PROTECTOR && RF_Power_selected > SWR_PROTECTOR_MAX_POWER) {
		RF_Power_selected = SWR_PROTECTOR_MAX_POWER;
	}

	float32_t RFpower_amplitude = 0.0f;
	if (CALIBRATE.LinearPowerControl) {
		RFpower_amplitude = (RF_Power_selected / 100.0f) * TRX_MAX_TX_Amplitude;
	} else {
		float32_t dbP = rate2dbP(RF_Power_selected / 100.0f);
		RFpower_amplitude = db2rateV(dbP) * TRX_MAX_TX_Amplitude;
	}

	if (RFpower_amplitude < 0.0f || TRX.RF_Gain == 0) {
		RFpower_amplitude = 0.0f;
	}
	if ((mode == TRX_MODE_AM || mode == TRX_MODE_SAM_STEREO || mode == TRX_MODE_SAM_LSB || mode == TRX_MODE_SAM_USB) && !TRX_Tune) {
		RFpower_amplitude = RFpower_amplitude * 0.7f;
	}
	if (RFpower_amplitude > 1.0f) {
		RFpower_amplitude = 1.0f;
	}

	// Tune power regulator
	if (TRX_Tune) {
#if FT8_SUPPORT
		if (FT8_DecodeActiveFlg) { // for FT8 set selected TX power
			APROC_TX_tune_power = RFpower_amplitude;
			ATU_TunePowerStabilized = true;
		}
#endif
		if (SYSMENU_auto_calibration_opened || TRX.TWO_SIGNAL_TUNE) { // do not clip power for auto calibration or two signal generator
			APROC_TX_tune_power = RFpower_amplitude;
			ATU_TunePowerStabilized = true;
		}

		if (!ATU_TunePowerStabilized) {
			float32_t full_power = TRX_PWR_Forward;

			if (fabsf(full_power - (float32_t)CALIBRATE.TUNE_MAX_POWER) > 0.1f) // histeresis
			{
				// println("Process Tune Stabilizer ", APROC_TX_tune_power);
				const float32_t coeff_a = 0.996f;
				const float32_t coeff_b = 1.0f - coeff_a;

				if (full_power < CALIBRATE.TUNE_MAX_POWER && APROC_TX_tune_power < RFpower_amplitude) {
					APROC_TX_tune_power = coeff_a * APROC_TX_tune_power + coeff_b * RFpower_amplitude;
				}
				if (TRX_PWR_Forward > CALIBRATE.TUNE_MAX_POWER && APROC_TX_tune_power < RFpower_amplitude) {
					APROC_TX_tune_power = coeff_a * APROC_TX_tune_power;
				}
			} else {
				ATU_TunePowerStabilized = true;
				println("Tune Power Stabilized");
			}

			if (APROC_TX_tune_power >= RFpower_amplitude * 0.99f) {
				APROC_TX_tune_power = RFpower_amplitude;
				ATU_TunePowerStabilized = true;
				println("Tune Power Stabilized");
			}
		}

		// println(RFpower_amplitude, " ", APROC_TX_tune_power);
		RFpower_amplitude = APROC_TX_tune_power;
	}

	// Apply gain
	arm_scale_f32(APROC_Audio_Buffer_TX_I, RFpower_amplitude, APROC_Audio_Buffer_TX_I, AUDIO_BUFFER_HALF_SIZE);
	arm_scale_f32(APROC_Audio_Buffer_TX_Q, RFpower_amplitude, APROC_Audio_Buffer_TX_Q, AUDIO_BUFFER_HALF_SIZE);

	// looking for a maximum in amplitude
	float32_t ampl_max_i = 0.0f;
	float32_t ampl_max_q = 0.0f;
	float32_t ampl_min_i = 0.0f;
	float32_t ampl_min_q = 0.0f;
	arm_max_no_idx_f32(APROC_Audio_Buffer_TX_I, AUDIO_BUFFER_HALF_SIZE, &ampl_max_i);
	arm_max_no_idx_f32(APROC_Audio_Buffer_TX_Q, AUDIO_BUFFER_HALF_SIZE, &ampl_max_q);
	arm_min_no_idx_f32(APROC_Audio_Buffer_TX_I, AUDIO_BUFFER_HALF_SIZE, &ampl_min_i);
	arm_min_no_idx_f32(APROC_Audio_Buffer_TX_Q, AUDIO_BUFFER_HALF_SIZE, &ampl_min_q);
	float32_t Processor_TX_MAX_amplitude_IN = ampl_max_i;
	if (ampl_max_q > Processor_TX_MAX_amplitude_IN) {
		Processor_TX_MAX_amplitude_IN = ampl_max_q;
	}
	if ((-ampl_min_i) > Processor_TX_MAX_amplitude_IN) {
		Processor_TX_MAX_amplitude_IN = -ampl_min_i;
	}
	if ((-ampl_min_q) > Processor_TX_MAX_amplitude_IN) {
		Processor_TX_MAX_amplitude_IN = -ampl_min_q;
	}

	// calculate the target gain
	Processor_TX_MAX_amplitude_OUT = Processor_TX_MAX_amplitude_IN;
	// println(Processor_TX_MAX_amplitude_IN, " ", RFpower_amplitude, " ", APROC_TX_clip_gain);

	if (Processor_TX_MAX_amplitude_IN > 0.0f) {
		// DAC overload (clipping), sharply reduce the gain
		if (Processor_TX_MAX_amplitude_IN > 1.0f) // dac range overload or alc input over 1 volt
		{
			// correct gain
			if (APROC_TX_clip_gain > 0.0f) {
				APROC_TX_clip_gain -= 0.001f;
			}
			// clip
			float32_t ALC_need_gain_target = (RFpower_amplitude * 0.99f) / Processor_TX_MAX_amplitude_IN;
			println("ALC_CLIP ", (double)(Processor_TX_MAX_amplitude_IN / RFpower_amplitude), " NEED ", (double)RFpower_amplitude, " CG ", (double)APROC_TX_clip_gain);
			TRX_DAC_OTR = true;
			// apply gain
			arm_scale_f32(APROC_Audio_Buffer_TX_I, ALC_need_gain_target, APROC_Audio_Buffer_TX_I, AUDIO_BUFFER_HALF_SIZE);
			arm_scale_f32(APROC_Audio_Buffer_TX_Q, ALC_need_gain_target, APROC_Audio_Buffer_TX_Q, AUDIO_BUFFER_HALF_SIZE);
			Processor_TX_MAX_amplitude_OUT = Processor_TX_MAX_amplitude_IN * ALC_need_gain_target;
		} else if (APROC_TX_clip_gain < 1.0f && Processor_TX_MAX_amplitude_IN < RFpower_amplitude) {
			APROC_TX_clip_gain += 0.0001f;
		} else if (APROC_TX_clip_gain > 0.0f && Processor_TX_MAX_amplitude_IN > RFpower_amplitude) {
			APROC_TX_clip_gain -= 0.0001f;
		}
	}

	if (RFpower_amplitude > 0.0f) {
		TRX_ALC_OUT = TRX_ALC_OUT * 0.9f + (Processor_TX_MAX_amplitude_OUT / RFpower_amplitude) * 0.1f; // smooth
	} else {
		TRX_ALC_OUT = 0.0f;
	}
	// RF PowerControl (Audio Level Control) Compressor END

	if (mode != TRX_MODE_LOOPBACK) {
		// Apply DAC bus limit
		arm_scale_f32(APROC_Audio_Buffer_TX_I, MAX_TX_AMPLITUDE_MULT, APROC_Audio_Buffer_TX_I, AUDIO_BUFFER_HALF_SIZE);
		arm_scale_f32(APROC_Audio_Buffer_TX_Q, MAX_TX_AMPLITUDE_MULT, APROC_Audio_Buffer_TX_Q, AUDIO_BUFFER_HALF_SIZE);

		// Apply Digital Pre-Distortion
		DPD_ProcessPredistortion(APROC_Audio_Buffer_TX_I, APROC_Audio_Buffer_TX_Q, AUDIO_BUFFER_HALF_SIZE);

		// Delay before the RF signal is applied, so that the relay has time to trigger
		if ((HAL_GetTick() - TRX_TX_StartTime) < CALIBRATE.TX_StartDelay) {
			dma_memset((void *)&APROC_Audio_Buffer_TX_I[0], 0x00, sizeof(APROC_Audio_Buffer_TX_I));
			dma_memset((void *)&APROC_Audio_Buffer_TX_Q[0], 0x00, sizeof(APROC_Audio_Buffer_TX_Q));
		}

		// Send to FPGA (DMA)
		Aligned_CleanDCache_by_Addr((uint32_t *)&APROC_Audio_Buffer_TX_I[0], sizeof(APROC_Audio_Buffer_TX_I));
		Aligned_CleanDCache_by_Addr((uint32_t *)&APROC_Audio_Buffer_TX_Q[0], sizeof(APROC_Audio_Buffer_TX_Q));
		Aligned_CleanDCache_by_Addr((uint32_t *)&FPGA_Audio_SendBuffer_I[0], sizeof(FPGA_Audio_SendBuffer_I));
		Aligned_CleanDCache_by_Addr((uint32_t *)&FPGA_Audio_SendBuffer_Q[0], sizeof(FPGA_Audio_SendBuffer_Q));
		if (FPGA_Audio_Buffer_State) {
#if HRDW_HAS_MDMA
			HAL_MDMA_Start(&HRDW_AUDIO_COPY_MDMA, (uint32_t)&APROC_Audio_Buffer_TX_I[0], (uint32_t)&FPGA_Audio_SendBuffer_I[AUDIO_BUFFER_HALF_SIZE], AUDIO_BUFFER_HALF_SIZE * 4, 1);
			SLEEPING_MDMA_PollForTransfer(&HRDW_AUDIO_COPY_MDMA);
			HAL_MDMA_Start(&HRDW_AUDIO_COPY_MDMA, (uint32_t)&APROC_Audio_Buffer_TX_Q[0], (uint32_t)&FPGA_Audio_SendBuffer_Q[AUDIO_BUFFER_HALF_SIZE], AUDIO_BUFFER_HALF_SIZE * 4, 1);
			SLEEPING_MDMA_PollForTransfer(&HRDW_AUDIO_COPY_MDMA);
#else
			HAL_DMA_Start(&HRDW_AUDIO_COPY_DMA, (uint32_t)&APROC_Audio_Buffer_TX_I[0], (uint32_t)&FPGA_Audio_SendBuffer_I[AUDIO_BUFFER_HALF_SIZE], AUDIO_BUFFER_HALF_SIZE);
			SLEEPING_DMA_PollForTransfer(&HRDW_AUDIO_COPY_DMA);
			HAL_DMA_Start(&HRDW_AUDIO_COPY_DMA, (uint32_t)&APROC_Audio_Buffer_TX_Q[0], (uint32_t)&FPGA_Audio_SendBuffer_Q[AUDIO_BUFFER_HALF_SIZE], AUDIO_BUFFER_HALF_SIZE);
			SLEEPING_DMA_PollForTransfer(&HRDW_AUDIO_COPY_DMA);
#endif
		} else {
#if HRDW_HAS_MDMA
			HAL_MDMA_Start(&HRDW_AUDIO_COPY2_MDMA, (uint32_t)&APROC_Audio_Buffer_TX_I[0], (uint32_t)&FPGA_Audio_SendBuffer_I[0], AUDIO_BUFFER_HALF_SIZE * 4, 1);
			SLEEPING_MDMA_PollForTransfer(&HRDW_AUDIO_COPY2_MDMA);
			HAL_MDMA_Start(&HRDW_AUDIO_COPY2_MDMA, (uint32_t)&APROC_Audio_Buffer_TX_Q[0], (uint32_t)&FPGA_Audio_SendBuffer_Q[0], AUDIO_BUFFER_HALF_SIZE * 4, 1);
			SLEEPING_MDMA_PollForTransfer(&HRDW_AUDIO_COPY2_MDMA);
#else
			HAL_DMA_Start(&HRDW_AUDIO_COPY2_DMA, (uint32_t)&APROC_Audio_Buffer_TX_I[0], (uint32_t)&FPGA_Audio_SendBuffer_I[0], AUDIO_BUFFER_HALF_SIZE);
			SLEEPING_DMA_PollForTransfer(&HRDW_AUDIO_COPY2_DMA);
			HAL_DMA_Start(&HRDW_AUDIO_COPY2_DMA, (uint32_t)&APROC_Audio_Buffer_TX_Q[0], (uint32_t)&FPGA_Audio_SendBuffer_Q[0], AUDIO_BUFFER_HALF_SIZE);
			SLEEPING_DMA_PollForTransfer(&HRDW_AUDIO_COPY2_DMA);
#endif
		}
		Aligned_CleanInvalidateDCache_by_Addr((uint32_t *)&FPGA_Audio_SendBuffer_I[0], sizeof(FPGA_Audio_SendBuffer_I));
		Aligned_CleanInvalidateDCache_by_Addr((uint32_t *)&FPGA_Audio_SendBuffer_Q[0], sizeof(FPGA_Audio_SendBuffer_Q));
	}

	Processor_NeedTXBuffer = false;
	if (!FULL_DUPLEX) {
		Processor_NeedRXBuffer = false;
	}
	USB_AUDIO_need_rx_buffer = false;
}

// Hilbert filter for phase shift of signals
static void doRX_HILBERT(AUDIO_PROC_RX_NUM rx_id, uint16_t size) {
	if (rx_id == AUDIO_RX1) {
#ifndef STM32F407xx
		arm_fir_f32(&FIR_RX1_Hilbert_I, APROC_Audio_Buffer_RX1_I, APROC_Audio_Buffer_RX1_I, size);
		arm_fir_f32(&FIR_RX1_Hilbert_Q, APROC_Audio_Buffer_RX1_Q, APROC_Audio_Buffer_RX1_Q, size);
#endif

#ifdef STM32F407xx
		// single transformer for slow CPU
		arm_fir_f32(&FIR_RX1_Hilbert_I, APROC_Audio_Buffer_RX1_I, APROC_Audio_Buffer_RX1_I, size);

#define HILBERT_DELAY (IQ_HILBERT_TAPS_RX / 2 + 1)
		static float32_t rx1_hilbert_delay_buffer[HILBERT_DELAY] = {0};
		static uint32_t rx1_hilbert_delay_buffer_head = 1;
		static uint32_t rx1_hilbert_delay_buffer_tail = 0;

		for (uint32_t i = 0; i < size; i++) {
			rx1_hilbert_delay_buffer[rx1_hilbert_delay_buffer_tail] = APROC_Audio_Buffer_RX1_Q[i];
			APROC_Audio_Buffer_RX1_Q[i] = rx1_hilbert_delay_buffer[rx1_hilbert_delay_buffer_head];

			rx1_hilbert_delay_buffer_head++;
			rx1_hilbert_delay_buffer_tail++;

			if (rx1_hilbert_delay_buffer_head == HILBERT_DELAY) {
				rx1_hilbert_delay_buffer_head = 0;
			}
			if (rx1_hilbert_delay_buffer_tail == HILBERT_DELAY) {
				rx1_hilbert_delay_buffer_tail = 0;
			}
		}
#endif
	}
#if HRDW_HAS_DUAL_RX
	else {
		arm_fir_f32(&FIR_RX2_Hilbert_I, APROC_Audio_Buffer_RX2_I, APROC_Audio_Buffer_RX2_I, size);
		arm_fir_f32(&FIR_RX2_Hilbert_Q, APROC_Audio_Buffer_RX2_Q, APROC_Audio_Buffer_RX2_Q, size);
	}
#endif
}

static void doTX_HILBERT(bool swap_iq, uint16_t size) {
	// single transformer for slow CPU
	if (!swap_iq) {
		arm_fir_f32(&FIR_TX_Hilbert_90, APROC_Audio_Buffer_TX_I, APROC_Audio_Buffer_TX_I, size);
	} else {
		arm_fir_f32(&FIR_TX_Hilbert_90, APROC_Audio_Buffer_TX_Q, APROC_Audio_Buffer_TX_Q, size);
	}

#define HILBERT_TX_DELAY (IQ_HILBERT_TAPS_TX / 2 + 1)
	static float32_t tx_hilbert_delay_buffer[HILBERT_TX_DELAY] = {0};
	static uint32_t tx_hilbert_delay_buffer_head = 1;
	static uint32_t tx_hilbert_delay_buffer_tail = 0;

	for (uint32_t i = 0; i < size; i++) {
		if (!swap_iq) {
			tx_hilbert_delay_buffer[tx_hilbert_delay_buffer_tail] = APROC_Audio_Buffer_TX_Q[i];
			APROC_Audio_Buffer_TX_Q[i] = tx_hilbert_delay_buffer[tx_hilbert_delay_buffer_head];
		} else {
			tx_hilbert_delay_buffer[tx_hilbert_delay_buffer_tail] = APROC_Audio_Buffer_TX_I[i];
			APROC_Audio_Buffer_TX_I[i] = tx_hilbert_delay_buffer[tx_hilbert_delay_buffer_head];
		}

		tx_hilbert_delay_buffer_head++;
		tx_hilbert_delay_buffer_tail++;

		if (tx_hilbert_delay_buffer_head == HILBERT_TX_DELAY) {
			tx_hilbert_delay_buffer_head = 0;
		}
		if (tx_hilbert_delay_buffer_tail == HILBERT_TX_DELAY) {
			tx_hilbert_delay_buffer_tail = 0;
		}
	}
}

static void doTX_CESSB(uint16_t size, TRX_MODE mode) {
	if (!TRX.TX_CESSB) {
		return;
	}
	if (mode != TRX_MODE_LSB && mode != TRX_MODE_USB) { //  && mode != TRX_MODE_LOOPBACK
		return;
	}

	// additional gain
	arm_scale_f32(APROC_Audio_Buffer_TX_I, db2rateP(TRX.TX_CESSB_COMPRESS_DB), APROC_Audio_Buffer_TX_I, size);
	arm_scale_f32(APROC_Audio_Buffer_TX_Q, db2rateP(TRX.TX_CESSB_COMPRESS_DB), APROC_Audio_Buffer_TX_Q, size);

	// clipping
	for (uint32_t sample = 0; sample < size; sample++) {
		float32_t i = APROC_Audio_Buffer_TX_I[sample];
		float32_t q = APROC_Audio_Buffer_TX_Q[sample];
		float32_t mag;
		arm_sqrt_f32(i * i + q * q, &mag);

		if (mag > 1.0f) {
			float32_t divider = 1.0f + (mag - 1.0f) * 2.0f;
			APROC_Audio_Buffer_TX_I[sample] /= divider;
			APROC_Audio_Buffer_TX_Q[sample] /= divider;
		}
	}

	// and filtering
	arm_biquad_cascade_df2T_f32_IQ(&IIR_TX_LPF_CESSB_I, &IIR_TX_LPF_CESSB_Q, APROC_Audio_Buffer_TX_I, APROC_Audio_Buffer_TX_Q, APROC_Audio_Buffer_TX_I, APROC_Audio_Buffer_TX_Q, size);
}

static void doRX_DecimateInput(AUDIO_PROC_RX_NUM rx_id, float32_t *in_i, float32_t *in_q, float32_t *out_i, float32_t *out_q, uint16_t size, uint8_t factor) {
	if (factor == 1) {
		dma_memcpy(out_i, in_i, size * 4);
		dma_memcpy(out_q, in_q, size * 4);
	} else {
		if (rx_id == AUDIO_RX1) {
			arm_biquad_cascade_df2T_f32_IQ(&DECIMATE_IIR_RX1_AUDIO_I, &DECIMATE_IIR_RX1_AUDIO_Q, in_i, in_q, in_i, in_q, size);
			arm_fir_decimate_f32(&DECIMATE_FIR_RX1_AUDIO_I, in_i, out_i, size);
			arm_fir_decimate_f32(&DECIMATE_FIR_RX1_AUDIO_Q, in_q, out_q, size);
		}
#if HRDW_HAS_DUAL_RX
		else {
			arm_biquad_cascade_df2T_f32_IQ(&DECIMATE_IIR_RX2_AUDIO_I, &DECIMATE_IIR_RX2_AUDIO_Q, in_i, in_q, in_i, in_q, size);
			arm_fir_decimate_f32(&DECIMATE_FIR_RX2_AUDIO_I, in_i, out_i, size);
			arm_fir_decimate_f32(&DECIMATE_FIR_RX2_AUDIO_Q, in_q, out_q, size);
		}
#endif
	}
}

// Low-pass filter for I and Q
static void doRX_LPF_IQ(AUDIO_PROC_RX_NUM rx_id, uint16_t size) {
	if (rx_id == AUDIO_RX1) {
		if (CurrentVFO->LPF_RX_Filter_Width > 0) {
			arm_biquad_cascade_df2T_f32_IQ(&IIR_RX1_LPF_I, &IIR_RX1_LPF_Q, APROC_Audio_Buffer_RX1_I, APROC_Audio_Buffer_RX1_Q, APROC_Audio_Buffer_RX1_I, APROC_Audio_Buffer_RX1_Q, size);
		}
	}
#if HRDW_HAS_DUAL_RX
	else {
		if (SecondaryVFO->LPF_RX_Filter_Width > 0) {
			arm_biquad_cascade_df2T_f32_IQ(&IIR_RX2_LPF_I, &IIR_RX2_LPF_Q, APROC_Audio_Buffer_RX2_I, APROC_Audio_Buffer_RX2_Q, APROC_Audio_Buffer_RX2_I, APROC_Audio_Buffer_RX2_Q, size);
		}
	}
#endif
}

// Low-pass filter for I and Q (second stage)
static void doRX_LPF2_IQ(AUDIO_PROC_RX_NUM rx_id, uint16_t size) {
	if (rx_id == AUDIO_RX1) {
		if (CurrentVFO->LPF_RX_Filter_Width > 0) {
			arm_biquad_cascade_df2T_f32_IQ(&IIR_RX1_LPF2_I, &IIR_RX1_LPF2_Q, APROC_Audio_Buffer_RX1_I, APROC_Audio_Buffer_RX1_Q, APROC_Audio_Buffer_RX1_I, APROC_Audio_Buffer_RX1_Q, size);
		}
	}
#if HRDW_HAS_DUAL_RX
	else {
		if (SecondaryVFO->LPF_RX_Filter_Width > 0) {
			arm_biquad_cascade_df2T_f32_IQ(&IIR_RX2_LPF2_I, &IIR_RX2_LPF2_Q, APROC_Audio_Buffer_RX2_I, APROC_Audio_Buffer_RX2_Q, APROC_Audio_Buffer_RX2_I, APROC_Audio_Buffer_RX2_Q, size);
		}
	}
#endif
}

// LPF filter for I
static void doRX_LPF_I(AUDIO_PROC_RX_NUM rx_id, uint16_t size) {
	if (rx_id == AUDIO_RX1) {
		if (CurrentVFO->LPF_RX_Filter_Width > 0) {
			arm_biquad_cascade_df2T_f32_single(&IIR_RX1_LPF_I, APROC_Audio_Buffer_RX1_I, APROC_Audio_Buffer_RX1_I, size);
		}
	}
#if HRDW_HAS_DUAL_RX
	else {
		if (SecondaryVFO->LPF_RX_Filter_Width > 0) {
			arm_biquad_cascade_df2T_f32_single(&IIR_RX2_LPF_I, APROC_Audio_Buffer_RX2_I, APROC_Audio_Buffer_RX2_I, size);
		}
	}
#endif
}

// LPF filter for I (second stage)
static void doRX_LPF2_I(AUDIO_PROC_RX_NUM rx_id, uint16_t size) {
	if (rx_id == AUDIO_RX1) {
		if (CurrentVFO->LPF_RX_Filter_Width > 0) {
			arm_biquad_cascade_df2T_f32_single(&IIR_RX1_LPF2_I, APROC_Audio_Buffer_RX1_I, APROC_Audio_Buffer_RX1_I, size);
		}
	}
#if HRDW_HAS_DUAL_RX
	else {
		if (SecondaryVFO->LPF_RX_Filter_Width > 0) {
			arm_biquad_cascade_df2T_f32_single(&IIR_RX2_LPF2_I, APROC_Audio_Buffer_RX2_I, APROC_Audio_Buffer_RX2_I, size);
		}
	}
#endif
}

// Gauss filter for I
static void doRX_GAUSS_IQ(AUDIO_PROC_RX_NUM rx_id, uint16_t size) {
	if (!TRX.CW_GaussFilter) {
		return;
	}
	if (rx_id == AUDIO_RX1) {
		if (CurrentVFO->Mode == TRX_MODE_CW) {
			arm_biquad_cascade_df2T_f32_IQ(&IIR_RX1_GAUSS_I, &IIR_RX1_GAUSS_Q, APROC_Audio_Buffer_RX1_I, APROC_Audio_Buffer_RX1_Q, APROC_Audio_Buffer_RX1_I, APROC_Audio_Buffer_RX1_Q, size);
		}
	}
#if HRDW_HAS_DUAL_RX
	else {
		if (SecondaryVFO->Mode == TRX_MODE_CW) {
			arm_biquad_cascade_df2T_f32_IQ(&IIR_RX2_GAUSS_I, &IIR_RX2_GAUSS_Q, APROC_Audio_Buffer_RX2_I, APROC_Audio_Buffer_RX2_Q, APROC_Audio_Buffer_RX2_I, APROC_Audio_Buffer_RX2_Q, size);
		}
	}
#endif
}

// HPF filter for I
static void doRX_HPF_I(AUDIO_PROC_RX_NUM rx_id, uint16_t size) {
	if (rx_id == AUDIO_RX1) {
		if (CurrentVFO->HPF_RX_Filter_Width > 0) {
			arm_biquad_cascade_df2T_f32_single(&IIR_RX1_HPF_I, APROC_Audio_Buffer_RX1_I, APROC_Audio_Buffer_RX1_I, size);
		}
	}
#if HRDW_HAS_DUAL_RX
	else {
		if (SecondaryVFO->HPF_RX_Filter_Width > 0) {
			arm_biquad_cascade_df2T_f32_single(&IIR_RX2_HPF_I, APROC_Audio_Buffer_RX2_I, APROC_Audio_Buffer_RX2_I, size);
		}
	}
#endif
}

// HPF filter for I and Q
static void doRX_HPF_IQ(AUDIO_PROC_RX_NUM rx_id, uint16_t size) {
	if (rx_id == AUDIO_RX1) {
		if (CurrentVFO->HPF_RX_Filter_Width > 0) {
			arm_biquad_cascade_df2T_f32_IQ(&IIR_RX1_HPF_I, &IIR_RX1_HPF_Q, APROC_Audio_Buffer_RX1_I, APROC_Audio_Buffer_RX1_Q, APROC_Audio_Buffer_RX1_I, APROC_Audio_Buffer_RX1_Q, size);
		}
	}
#if HRDW_HAS_DUAL_RX
	else {
		if (SecondaryVFO->HPF_RX_Filter_Width > 0) {
			arm_biquad_cascade_df2T_f32_IQ(&IIR_RX2_HPF_I, &IIR_RX2_HPF_Q, APROC_Audio_Buffer_RX2_I, APROC_Audio_Buffer_RX2_Q, APROC_Audio_Buffer_RX2_I, APROC_Audio_Buffer_RX2_Q, size);
		}
	}
#endif
}

// notch filter
static void doRX_NOTCH(AUDIO_PROC_RX_NUM rx_id, uint16_t size) {
	if (rx_id == AUDIO_RX1) {
		if (CurrentVFO->ManualNotchFilter) { // manual filter
			arm_biquad_cascade_df2T_f32_single(&NOTCH_RX1_FILTER, APROC_Audio_Buffer_RX1_I, APROC_Audio_Buffer_RX1_I, size);
		} else if (CurrentVFO->AutoNotchFilter) // automatic filter
		{
			for (uint32_t block = 0; block < (size / AUTO_NOTCH_BLOCK_SIZE); block++) {
				processAutoNotchReduction(APROC_Audio_Buffer_RX1_I + (block * AUTO_NOTCH_BLOCK_SIZE), rx_id);
			}
		}
	}
#if HRDW_HAS_DUAL_RX
	else {
		if (SecondaryVFO->ManualNotchFilter) {
			arm_biquad_cascade_df2T_f32_single(&NOTCH_RX2_FILTER, APROC_Audio_Buffer_RX2_I, APROC_Audio_Buffer_RX2_I, size);
		} else if (SecondaryVFO->AutoNotchFilter) {
			for (uint32_t block = 0; block < (size / AUTO_NOTCH_BLOCK_SIZE); block++) {
				processAutoNotchReduction(APROC_Audio_Buffer_RX2_I + (block * AUTO_NOTCH_BLOCK_SIZE), rx_id);
			}
		}
	}
#endif
}

// RX Equalizer
static void doRX_EQ(uint16_t size, uint8_t mode) {
	arm_biquad_cascade_df2T_f32_IQ(&EQ_RX_I_P1_FILTER, &EQ_RX_Q_P1_FILTER, APROC_Audio_Buffer_RX1_I, APROC_Audio_Buffer_RX1_Q, APROC_Audio_Buffer_RX1_I, APROC_Audio_Buffer_RX1_Q, size);
	arm_biquad_cascade_df2T_f32_IQ(&EQ_RX_I_P2_FILTER, &EQ_RX_Q_P2_FILTER, APROC_Audio_Buffer_RX1_I, APROC_Audio_Buffer_RX1_Q, APROC_Audio_Buffer_RX1_I, APROC_Audio_Buffer_RX1_Q, size);
	arm_biquad_cascade_df2T_f32_IQ(&EQ_RX_I_P3_FILTER, &EQ_RX_Q_P3_FILTER, APROC_Audio_Buffer_RX1_I, APROC_Audio_Buffer_RX1_Q, APROC_Audio_Buffer_RX1_I, APROC_Audio_Buffer_RX1_Q, size);
	arm_biquad_cascade_df2T_f32_IQ(&EQ_RX_I_P4_FILTER, &EQ_RX_Q_P4_FILTER, APROC_Audio_Buffer_RX1_I, APROC_Audio_Buffer_RX1_Q, APROC_Audio_Buffer_RX1_I, APROC_Audio_Buffer_RX1_Q, size);
	arm_biquad_cascade_df2T_f32_IQ(&EQ_RX_I_P5_FILTER, &EQ_RX_Q_P5_FILTER, APROC_Audio_Buffer_RX1_I, APROC_Audio_Buffer_RX1_Q, APROC_Audio_Buffer_RX1_I, APROC_Audio_Buffer_RX1_Q, size);
	arm_biquad_cascade_df2T_f32_IQ(&EQ_RX_I_P6_FILTER, &EQ_RX_Q_P6_FILTER, APROC_Audio_Buffer_RX1_I, APROC_Audio_Buffer_RX1_Q, APROC_Audio_Buffer_RX1_I, APROC_Audio_Buffer_RX1_Q, size);
}

// Equalizer microphone
static void doMIC_EQ(uint16_t size, uint8_t mode) {
	switch (mode) {
	case TRX_MODE_LSB:
	case TRX_MODE_USB:
	case TRX_MODE_LOOPBACK:
	default:
		if (TRX.MIC_EQ_P1_SSB != 0) {
			arm_biquad_cascade_df2T_f32_single(&EQ_MIC_P1_FILTER_SSB, APROC_Audio_Buffer_TX_I, APROC_Audio_Buffer_TX_I, size);
		}
		if (TRX.MIC_EQ_P2_SSB != 0) {
			arm_biquad_cascade_df2T_f32_single(&EQ_MIC_P2_FILTER_SSB, APROC_Audio_Buffer_TX_I, APROC_Audio_Buffer_TX_I, size);
		}
		if (TRX.MIC_EQ_P3_SSB != 0) {
			arm_biquad_cascade_df2T_f32_single(&EQ_MIC_P3_FILTER_SSB, APROC_Audio_Buffer_TX_I, APROC_Audio_Buffer_TX_I, size);
		}
		if (TRX.MIC_EQ_P4_SSB != 0) {
			arm_biquad_cascade_df2T_f32_single(&EQ_MIC_P4_FILTER_SSB, APROC_Audio_Buffer_TX_I, APROC_Audio_Buffer_TX_I, size);
		}
		if (TRX.MIC_EQ_P5_SSB != 0) {
			arm_biquad_cascade_df2T_f32_single(&EQ_MIC_P5_FILTER_SSB, APROC_Audio_Buffer_TX_I, APROC_Audio_Buffer_TX_I, size);
		}
		if (TRX.MIC_EQ_P6_SSB != 0) {
			arm_biquad_cascade_df2T_f32_single(&EQ_MIC_P6_FILTER_SSB, APROC_Audio_Buffer_TX_I, APROC_Audio_Buffer_TX_I, size);
		}
		break;

	case TRX_MODE_NFM:
	case TRX_MODE_WFM:
	case TRX_MODE_AM:
	case TRX_MODE_SAM_STEREO:
	case TRX_MODE_SAM_LSB:
	case TRX_MODE_SAM_USB:
		if (TRX.MIC_EQ_P1_AMFM != 0) {
			arm_biquad_cascade_df2T_f32_single(&EQ_MIC_P1_FILTER_AMFM, APROC_Audio_Buffer_TX_I, APROC_Audio_Buffer_TX_I, size);
		}
		if (TRX.MIC_EQ_P2_AMFM != 0) {
			arm_biquad_cascade_df2T_f32_single(&EQ_MIC_P2_FILTER_AMFM, APROC_Audio_Buffer_TX_I, APROC_Audio_Buffer_TX_I, size);
		}
		if (TRX.MIC_EQ_P3_AMFM != 0) {
			arm_biquad_cascade_df2T_f32_single(&EQ_MIC_P3_FILTER_AMFM, APROC_Audio_Buffer_TX_I, APROC_Audio_Buffer_TX_I, size);
		}
		if (TRX.MIC_EQ_P4_AMFM != 0) {
			arm_biquad_cascade_df2T_f32_single(&EQ_MIC_P4_FILTER_AMFM, APROC_Audio_Buffer_TX_I, APROC_Audio_Buffer_TX_I, size);
		}
		if (TRX.MIC_EQ_P5_AMFM != 0) {
			arm_biquad_cascade_df2T_f32_single(&EQ_MIC_P5_FILTER_AMFM, APROC_Audio_Buffer_TX_I, APROC_Audio_Buffer_TX_I, size);
		}
		if (TRX.MIC_EQ_P6_AMFM != 0) {
			arm_biquad_cascade_df2T_f32_single(&EQ_MIC_P6_FILTER_AMFM, APROC_Audio_Buffer_TX_I, APROC_Audio_Buffer_TX_I, size);
		}
		break;
	}

#ifndef STM32F407xx
	// Reverber
	if (TRX.MIC_REVERBER > 0) {
		// reset
		static uint32_t reverber_position = 0;
		if (NeedReinitReverber) {
			reverber_position = 0;
			dma_memset(Processor_Reverber_Buffer, 0x00, sizeof(Processor_Reverber_Buffer));
			NeedReinitReverber = false;
		}

		// save
		dma_memcpy(&Processor_Reverber_Buffer[reverber_position * size], APROC_Audio_Buffer_TX_I, sizeof(float32_t) * size);

		// move
		reverber_position++;
		if (reverber_position > TRX.MIC_REVERBER) {
			reverber_position = 0;
		}

		// apply
		arm_add_f32(&Processor_Reverber_Buffer[reverber_position * size], APROC_Audio_Buffer_TX_I, APROC_Audio_Buffer_TX_I, size);
		arm_scale_f32(APROC_Audio_Buffer_TX_I, 0.5f, APROC_Audio_Buffer_TX_I, size);
	}
#endif
}

// Digital Noise Reduction
static void doRX_DNR(AUDIO_PROC_RX_NUM rx_id, uint16_t size, uint_fast8_t mode, bool stereo) {
	if (rx_id == AUDIO_RX1) {
		bool do_agc = CurrentVFO->AGC && TRX.AGC_Spectral;
		if (CurrentVFO->DNR_Type > 0 || do_agc) {
			for (uint32_t block = 0; block < (size / NOISE_REDUCTION_BLOCK_SIZE); block++) {
				processNoiseReduction(APROC_Audio_Buffer_RX1_I + (block * NOISE_REDUCTION_BLOCK_SIZE), rx_id, CurrentVFO->DNR_Type, mode, do_agc);
#if HRDW_HAS_DUAL_RX
				if (stereo && !TRX.Dual_RX) {
					processNoiseReduction(APROC_Audio_Buffer_RX1_Q + (block * NOISE_REDUCTION_BLOCK_SIZE), AUDIO_RX2, CurrentVFO->DNR_Type, mode,
					                      do_agc); // process second channel in rx2
				}
#endif
			}
		}
	}
#if HRDW_HAS_DUAL_RX
	else {
		bool do_agc = SecondaryVFO->AGC && TRX.AGC_Spectral;
		if (SecondaryVFO->DNR_Type > 0 || do_agc) {
			for (uint32_t block = 0; block < (size / NOISE_REDUCTION_BLOCK_SIZE); block++) {
				processNoiseReduction(APROC_Audio_Buffer_RX2_I + (block * NOISE_REDUCTION_BLOCK_SIZE), rx_id, SecondaryVFO->DNR_Type, mode, do_agc);
			}
		}
	}
#endif
}

// automatic gain control
static void doRX_AGC(AUDIO_PROC_RX_NUM rx_id, uint16_t size, uint_fast8_t mode, bool stereo) {
	if (!TRX.AGC_Spectral) { // else do agc in NR
		if (rx_id == AUDIO_RX1) {
			DoRxAGC(APROC_Audio_Buffer_RX1_I, APROC_Audio_Buffer_RX1_Q, size, rx_id, CurrentVFO->DNR_Type, mode, stereo);
		}
#if HRDW_HAS_DUAL_RX
		else {
			DoRxAGC(APROC_Audio_Buffer_RX2_I, APROC_Audio_Buffer_RX2_Q, size, rx_id, SecondaryVFO->DNR_Type, mode, stereo);
		}
#endif
	}
}

// impulse noise suppressor
static void doRX_NoiseBlanker(AUDIO_PROC_RX_NUM rx_id, uint16_t size) {
	if (!TRX.NOISE_BLANKER1 && !TRX.NOISE_BLANKER2) {
		return;
	}

	if (rx_id == AUDIO_RX1) {
		for (uint32_t block = 0; block < (size / NB_BLOCK_SIZE); block++) {
			processNoiseBlanking(APROC_Audio_Buffer_RX1_I + (block * NB_BLOCK_SIZE), rx_id);
		}
	}
#if HRDW_HAS_DUAL_RX
	else {
		for (uint32_t block = 0; block < (size / NB_BLOCK_SIZE); block++) {
			processNoiseBlanking(APROC_Audio_Buffer_RX2_I + (block * NB_BLOCK_SIZE), rx_id);
		}
	}
#endif
}

// s-meter
static void doRX_SMETER(AUDIO_PROC_RX_NUM rx_id, float32_t *buff, uint16_t size, bool if_gained) {
	if (rx_id == AUDIO_RX1) {
		if (Processor_RX1_Power_value != 0) {
			return;
		}
		// Prepare data to calculate s-meter
		static float32_t i = 0;
		arm_rms_f32(buff, size, &i);
		if (if_gained && current_if_gain != 0.0f) {
			i *= 1.0f / current_if_gain;
		}
		Processor_RX1_Power_value = i;

		// Calc
		if (Processor_RX1_Power_value == 0) {
			TRX_RX1_dBm = -150.0f;
		} else {
			float32_t adc_volts = Processor_RX1_Power_value * (TRX.ADC_PGA ? (ADC_RANGE_PGA / 2.0f) : (ADC_RANGE / 2.0f));
			if (TRX.ADC_Driver) {
				adc_volts *= db2rateV(-ADC_DRIVER_GAIN_DB);
			}
			TRX_RX1_dBm = 10.0f * log10f_fast((adc_volts * adc_volts / ADC_INPUT_IMPEDANCE) / 0.001f);
			if (CurrentVFO->Freq < 70000000) {
				TRX_RX1_dBm += CALIBRATE.smeter_calibration_hf;
			} else {
				TRX_RX1_dBm += CALIBRATE.smeter_calibration_vhf;
			}

			if (TRX.LNA) {
				TRX_RX1_dBm += CALIBRATE.LNA_compensation;
			}

			if (CALIBRATE.ATT_compensation && TRX.ATT) {
				TRX_RX1_dBm += TRX.ATT_DB;
			}

			if (TRX_RX1_dBm < -150.0f) {
				TRX_RX1_dBm = -150.0f;
			}

			Processor_RX1_Power_value = 0;

			TRX_RX1_dBm_measurement = TRX_RX1_dBm_measurement * 0.99f + TRX_RX1_dBm * 0.01f;
		}
	}

#if HRDW_HAS_DUAL_RX
	if (rx_id == AUDIO_RX2) {
		if (Processor_RX2_Power_value != 0) {
			return;
		}
		// Prepare data to calculate s-meter
		static float32_t i = 0;
		arm_rms_f32(buff, size, &i);
		if (if_gained && current_if_gain != 0.0f) {
			i *= 1.0f / current_if_gain;
		}
		Processor_RX2_Power_value = i;

		// Calc
		if (Processor_RX2_Power_value == 0) {
			TRX_RX2_dBm = -150.0f;
		} else {
			float32_t adc_volts = Processor_RX2_Power_value * (TRX.ADC_PGA ? (ADC_RANGE_PGA / 2.0f) : (ADC_RANGE / 2.0f));
			if (TRX.ADC_Driver) {
				adc_volts *= db2rateV(-ADC_DRIVER_GAIN_DB);
			}
			TRX_RX2_dBm = 10.0f * log10f_fast((adc_volts * adc_volts / ADC_INPUT_IMPEDANCE) / 0.001f);
			if (SecondaryVFO->Freq < 70000000) {
				TRX_RX2_dBm += CALIBRATE.smeter_calibration_hf;
			} else {
				TRX_RX2_dBm += CALIBRATE.smeter_calibration_vhf;
			}

			if (TRX.LNA) {
				TRX_RX2_dBm += CALIBRATE.LNA_compensation;
			}

			if (CALIBRATE.ATT_compensation && TRX.ATT) {
				TRX_RX2_dBm += TRX.ATT_DB;
			}

			if (TRX_RX2_dBm < -150.0f) {
				TRX_RX2_dBm = -150.0f;
			}
			Processor_RX2_Power_value = 0;
		}
	}
#endif
}

// copy I to Q channel
static void doRX_COPYCHANNEL(AUDIO_PROC_RX_NUM rx_id, uint16_t size) {
	// Double channel I-> Q
	if (rx_id == AUDIO_RX1) {
		dma_memcpy32((uint32_t *)&APROC_Audio_Buffer_RX1_Q[0], (uint32_t *)&APROC_Audio_Buffer_RX1_I[0], size);
	}
#if HRDW_HAS_DUAL_RX
	else {
		dma_memcpy32((uint32_t *)&APROC_Audio_Buffer_RX2_Q[0], (uint32_t *)&APROC_Audio_Buffer_RX2_I[0], size);
	}
#endif
}

// FM demodulator
static void DemodulateFM(float32_t *data_i, float32_t *data_q, AUDIO_PROC_RX_NUM rx_id, uint16_t size, bool wfm, float32_t dBm) {
	demod_fm_instance *DFM = &DFM_RX1;
	bool sql_enabled = CurrentVFO->SQL;
	int16_t FM_SQL_threshold_dBm = CurrentVFO->FM_SQL_threshold_dBm;
	const arm_biquad_cascade_df2T_instance_f32 *SFM_Pilot_Filter = &SFM_RX1_Pilot_Filter;
	const arm_biquad_cascade_df2T_instance_f32 *SFM_Audio_Filter = &SFM_RX1_Audio_Filter;

	float32_t angle;

#if HRDW_HAS_DUAL_RX
	if (rx_id == AUDIO_RX2) {
		DFM = &DFM_RX2;
		FM_SQL_threshold_dBm = SecondaryVFO->FM_SQL_threshold_dBm;
		sql_enabled = SecondaryVFO->SQL;
		SFM_Pilot_Filter = &SFM_RX2_Pilot_Filter;
		SFM_Audio_Filter = &SFM_RX2_Audio_Filter;
	}
#endif

	// *** Squelch Processing ***
	if (!DFM->squelchSuggested && FM_SQL_threshold_dBm > dBm) {

		DFM->squelchSuggested = true; // yes, close the squelch
		DFM->squelchSuggested_starttime = HAL_GetTick();
	} else if (DFM->squelchSuggested && FM_SQL_threshold_dBm <= dBm) {
		DFM->squelchSuggested = false; //  yes, open the squelch
		DFM->squelchSuggested_starttime = HAL_GetTick();
	}

	if (DFM->squelched != DFM->squelchSuggested && DFM->squelchSuggested_starttime < HAL_GetTick() - FM_RX_SQL_TIMEOUT_MS) {
		DFM->squelched = DFM->squelchSuggested;
		if (DFM->squelched) {
			DFM->squelchRate = 1.0f;
		} else {
			DFM->squelchRate = 0.01f;
		}
	}

	// do IQ demod
	for (uint_fast16_t i = 0; i < size; i++) {
		// first, calculate "x" and "y" for the arctan2, comparing the vectors of present data with previous data
		float32_t x = (data_q[i] * DFM->i_prev) - (data_i[i] * DFM->q_prev);
		float32_t y = (data_i[i] * DFM->i_prev) + (data_q[i] * DFM->q_prev);

		// save "previous" value of each channel to allow detection of the change of angle in next go-around
		DFM->q_prev = data_q[i];
		DFM->i_prev = data_i[i];

		// demod
		arm_atan2_f32(x, y, &angle);
		if (isnanf(angle)) {
			angle = 0.0f;
		}
		data_i[i] = (float32_t)(angle / F_PI) * 0.001f; // + if gain correction

		// smooth SQL edges
		if (!DFM->squelched || !sql_enabled) {
			if (DFM->squelchRate < 1.00f) {
				data_i[i] *= DFM->squelchRate;
				DFM->squelchRate = 1.01f * DFM->squelchRate;
			}
		} else if (DFM->squelched) // were we squelched or tone NOT detected?
		{
			if (DFM->squelchRate > 0.01f) {
				data_i[i] *= DFM->squelchRate;
				DFM->squelchRate = 0.99f * DFM->squelchRate;
			} else {
				data_i[i] = 0;
			}
		}
	}

	// RDS Decoder
	if (rx_id == AUDIO_RX1 && wfm) {
		DECODER_PutSamples(data_i, size);
	}

	// Stereo FM
	if (TRX.FM_Stereo && !DFM->squelched && wfm) {
		arm_biquad_cascade_df2T_f32_single(SFM_Pilot_Filter, data_i, DFM->stereo_fm_pilot_out, size);
		arm_biquad_cascade_df2T_f32_single(SFM_Audio_Filter, data_i, DFM->stereo_fm_audio_out, size);

		// float32_t stereo_rms = 0.0f;

		// move signal to low freq
		for (uint_fast16_t i = 0; i < size; i++) {
			static float32_t prev_sfm_pilot_sample = 0.0f;
			arm_atan2_f32(DFM->stereo_fm_pilot_out[i], prev_sfm_pilot_sample, &angle); // double freq
			angle *= 2.0f;
			prev_sfm_pilot_sample = DFM->stereo_fm_pilot_out[i];

			// get stereo sample from decoded wfm
			float32_t stereo_sample = DFM->stereo_fm_audio_out[i] * fast_sin(angle) * (100.0f / (float32_t)TRX.FM_Stereo_Modulation);
			if (isnanf(stereo_sample) || isinff(stereo_sample)) {
				continue;
			}

			// get channels
			float32_t audio_sample = data_i[i];
			data_q[i] = (audio_sample - stereo_sample); // Mono (L+R) - Stereo (L-R) = 2R
			data_i[i] = (audio_sample + stereo_sample); // Mono (L+R) + Stereo (L-R) = 2L

			// calculate RMS
			// stereo_rms += (stereo_sample * 1000.0f) * (stereo_sample * 1000.0f);
		}

		// stereo_rms /= size;
		// stereo_rms = sqrtf(stereo_rms);
		// println("Stereo RMS: ", (double)rate2dbP(stereo_rms));
	}
}

// FM modulator
static void ModulateFM(uint16_t size, float32_t amplitude) {
	static float32_t hpf_prev_a = 0;
	static float32_t hpf_prev_b = 0;
	static float32_t fm_mod_accum = 0;
	static float32_t modulation_index = 0;
	if (CurrentVFO->LPF_TX_Filter_Width > 0) {
		modulation_index = CurrentVFO->LPF_TX_Filter_Width / (float32_t)TRX_SAMPLERATE / (float32_t)TRX_TX_Harmonic * (float32_t)CALIBRATE.FM_DEVIATION_SCALE;
	} else {
		modulation_index = (float32_t)CALIBRATE.FM_DEVIATION_SCALE;
	}

	// CTCSS
	if (TRX.CTCSS_Freq > 0.0f) {
		static float32_t CTCSS_gen_index = 0;
		for (uint_fast16_t i = 0; i < AUDIO_BUFFER_HALF_SIZE; i++) {
			float32_t point = generateSin(0.25f, &CTCSS_gen_index, TRX_SAMPLERATE, TRX.CTCSS_Freq);
			APROC_Audio_Buffer_TX_I[i] += point;
		}
	}

	for (uint_fast16_t i = 0; i < size; i++) {
		hpf_prev_b = FM_TX_HPF_ALPHA * (hpf_prev_b + APROC_Audio_Buffer_TX_I[i] - hpf_prev_a); // do differentiation
		hpf_prev_a = APROC_Audio_Buffer_TX_I[i];                                               // save "[n-1] samples for next iteration
		fm_mod_accum += hpf_prev_b * modulation_index;                                         // save differentiated data in audio buffer
		while (fm_mod_accum > (2.0f * PI)) {
			fm_mod_accum -= (2.0f * PI); // limit range
		}
		while (fm_mod_accum < -(2.0f * PI)) {
			fm_mod_accum += (2.0f * PI); // limit range
		}
		float32_t sin_result;
		float32_t cos_result;
		fast_sin_cos(fm_mod_accum, &sin_result, &cos_result);
		APROC_Audio_Buffer_TX_I[i] = amplitude * sin_result;
		APROC_Audio_Buffer_TX_Q[i] = amplitude * cos_result;
	}
}

// voice activity detector
static void doVAD(AUDIO_PROC_RX_NUM rx_id, uint16_t size) {
	if (rx_id == AUDIO_RX1) {
		for (uint32_t block = 0; block < (size / VAD_BLOCK_SIZE); block++) {
			processVAD(rx_id, APROC_Audio_Buffer_RX1_I + (block * VAD_BLOCK_SIZE));
		}
	}

#if HRDW_HAS_DUAL_RX
	if (rx_id == AUDIO_RX2) {
		for (uint32_t block = 0; block < (size / VAD_BLOCK_SIZE); block++) {
			processVAD(rx_id, APROC_Audio_Buffer_RX2_I + (block * VAD_BLOCK_SIZE));
		}
	}
#endif
}

// Apply IF Gain IF Gain
static void doRX_IFGain(AUDIO_PROC_RX_NUM rx_id, uint16_t size) {
	float32_t if_gain_dB = TRX.IF_Gain;
	if (rx_id == AUDIO_RX1 && CurrentVFO->Mode == TRX_MODE_CW) {
		if_gain_dB += CW_ADD_GAIN_IF;
	}
#if HRDW_HAS_DUAL_RX
	if (rx_id == AUDIO_RX2 && SecondaryVFO->Mode == TRX_MODE_CW) {
		if_gain_dB += CW_ADD_GAIN_IF;
	}
#endif

	float32_t if_gain = db2rateP(if_gain_dB);

	float32_t *I_buff = APROC_Audio_Buffer_RX1_I;
	float32_t *Q_buff = APROC_Audio_Buffer_RX1_Q;
#if HRDW_HAS_DUAL_RX
	if (rx_id == AUDIO_RX2) {
		I_buff = APROC_Audio_Buffer_RX2_I;
		Q_buff = APROC_Audio_Buffer_RX2_Q;
	}
#endif

	// overflow protect
	if (!CurrentVFO->AGC) {
		float32_t minVal = 0;
		float32_t maxVal = 0;

		arm_min_no_idx_f32(I_buff, size, &minVal);
		arm_max_no_idx_f32(I_buff, size, &maxVal);
		if ((minVal * if_gain) < -1.0f) {
			APROC_IFGain_Overflow = true;
		}
		if ((maxVal * if_gain) > 1.0f) {
			APROC_IFGain_Overflow = true;
		}
		arm_min_no_idx_f32(Q_buff, size, &minVal);
		arm_max_no_idx_f32(Q_buff, size, &maxVal);
		if ((minVal * if_gain) < -1.0f) {
			APROC_IFGain_Overflow = true;
		}
		if ((maxVal * if_gain) > 1.0f) {
			APROC_IFGain_Overflow = true;
		}
	}

	// apply gain
	arm_scale_f32(I_buff, if_gain, I_buff, size);
	arm_scale_f32(Q_buff, if_gain, Q_buff, size);
	current_if_gain = if_gain;
}

#if HRDW_HAS_SD
static void APROC_SD_Play(void) {
	static uint32_t vocoder_index = SIZE_ADPCM_BLOCK;
	static uint32_t outbuff_index = 0;

	if (vocoder_index == SIZE_ADPCM_BLOCK) {
		vocoder_index = 0;
		VODECODER_Process();
	}

	if (vocoder_index < SIZE_ADPCM_BLOCK) {
		while (vocoder_index < SIZE_ADPCM_BLOCK && outbuff_index < FPGA_RX_IQ_BUFFER_HALF_SIZE) {
			APROC_AudioBuffer_out[outbuff_index * 2] = VOCODER_Buffer[vocoder_index] << 16;
			APROC_AudioBuffer_out[outbuff_index * 2 + 1] = APROC_AudioBuffer_out[outbuff_index * 2];
			vocoder_index++;
			outbuff_index++;
		}

		if (outbuff_index == FPGA_RX_IQ_BUFFER_HALF_SIZE) {
			outbuff_index = 0;

			// OUT Volume
			float32_t volume_gain_new = volume2rate((float32_t)TRX.Volume / MAX_VOLUME_VALUE);
			volume_gain = 0.9f * volume_gain + 0.1f * volume_gain_new;

			// Volume Gain and SPI convert
			for (uint_fast16_t i = 0; i < (FPGA_RX_IQ_BUFFER_HALF_SIZE * 2); i++) {
				// Gain
				APROC_AudioBuffer_out[i] = (int32_t)((float32_t)APROC_AudioBuffer_out[i] * volume_gain);
				// Codec SPI
				APROC_AudioBuffer_out[i] = convertToSPIBigEndian(APROC_AudioBuffer_out[i]); // for 32bit audio
			}

			// Mute codec if need
			APROC_ProcessCodecMuting();

			// Send to Codec DMA
			if (TRX_Inited) {
				Aligned_CleanDCache_by_Addr((uint32_t *)&APROC_AudioBuffer_out[0], sizeof(APROC_AudioBuffer_out));
				if (CODEC_DMA_state) // complete
				{
#if HRDW_HAS_MDMA
					HAL_MDMA_Start(&HRDW_AUDIO_COPY_MDMA, (uint32_t)&APROC_AudioBuffer_out[0], (uint32_t)&CODEC_Audio_Buffer_RX[AUDIO_BUFFER_SIZE], CODEC_AUDIO_BUFFER_HALF_SIZE * 4,
					               1); //*2 -> left_right
					SLEEPING_MDMA_PollForTransfer(&HRDW_AUDIO_COPY_MDMA);
#else
					HAL_DMA_Start(&HRDW_AUDIO_COPY_DMA, (uint32_t)&APROC_AudioBuffer_out[0], (uint32_t)&CODEC_Audio_Buffer_RX[AUDIO_BUFFER_SIZE],
					              CODEC_AUDIO_BUFFER_HALF_SIZE); //*2 -> left_right
					SLEEPING_DMA_PollForTransfer(&HRDW_AUDIO_COPY_DMA);
#endif
				} else // half
				{
#if HRDW_HAS_MDMA
					HAL_MDMA_Start(&HRDW_AUDIO_COPY2_MDMA, (uint32_t)&APROC_AudioBuffer_out[0], (uint32_t)&CODEC_Audio_Buffer_RX[0], CODEC_AUDIO_BUFFER_HALF_SIZE * 4, 1); //*2 -> left_right
					SLEEPING_MDMA_PollForTransfer(&HRDW_AUDIO_COPY2_MDMA);
#else
					HAL_DMA_Start(&HRDW_AUDIO_COPY2_DMA, (uint32_t)&APROC_AudioBuffer_out[0], (uint32_t)&CODEC_Audio_Buffer_RX[0],
					              CODEC_AUDIO_BUFFER_HALF_SIZE); //*2 -> left_right
					SLEEPING_DMA_PollForTransfer(&HRDW_AUDIO_COPY2_DMA);
#endif
				}
			}
			//
			Processor_NeedTXBuffer = false;
			Processor_NeedRXBuffer = false;
			USB_AUDIO_need_rx_buffer = false;
		}
	}
}

static bool APROC_SD_PlayTX(void) {
	static uint32_t vocoder_index = SIZE_ADPCM_BLOCK;
	static uint32_t outbuff_index = 0;

	if (vocoder_index == SIZE_ADPCM_BLOCK) {
		vocoder_index = 0;
		VODECODER_Process();
	}

	if (vocoder_index < SIZE_ADPCM_BLOCK) {
		while (vocoder_index < SIZE_ADPCM_BLOCK && outbuff_index < AUDIO_BUFFER_HALF_SIZE) {
			APROC_AudioBuffer_out[outbuff_index * 2] = VOCODER_Buffer[vocoder_index] << 16;
			APROC_AudioBuffer_out[outbuff_index * 2 + 1] = APROC_AudioBuffer_out[outbuff_index * 2];
			vocoder_index++;
			outbuff_index++;
		}

		if (outbuff_index == AUDIO_BUFFER_HALF_SIZE) {
			outbuff_index = 0;

			// data ready
			return true;
		}
	}

	// data not ready
	return false;
}
#endif

static void doRX_RXFreqTransition(float32_t *in_i, float32_t *in_q, uint16_t size, int32_t freq_diff) {
	static float32_t gen_position_fft = 0.0;
	float32_t step = (float32_t)freq_diff / (float32_t)TRX_GetRXSampleRate;
	float32_t sin_result;
	float32_t cos_result;

	for (uint16_t i = 0; i < size; i++) {
		float32_t position = gen_position_fft * F_2PI;

		fast_sin_cos(position, &sin_result, &cos_result);

		float32_t sample_i = in_i[i];
		float32_t sample_q = in_q[i];

		in_i[i] = (sample_i * cos_result - sample_q * sin_result);
		in_q[i] = (sample_i * sin_result + sample_q * cos_result);

		gen_position_fft += step;
		if (gen_position_fft >= 1.0f) {
			gen_position_fft -= 1.0f;
		}
		if (gen_position_fft <= -1.0f) {
			gen_position_fft += 1.0f;
		}
	}
}

static void doRX_CWFreqTransition(AUDIO_PROC_RX_NUM rx_id, uint16_t size, float32_t freq_diff) {
	static float32_t gen_position_rx1 = 0.0f;
	static float32_t gen_position_rx2 = 0.0f;
	const float32_t compensation_coeff = 2.0f;

	if (rx_id == AUDIO_RX1) {
		for (uint16_t i = 0; i < size; i++) {
			float32_t sin_result;
			float32_t cos_result;
			fast_sin_cos((gen_position_rx1 * F_2PI), &sin_result, &cos_result);
			APROC_Audio_Buffer_RX1_I[i] *= sin_result * compensation_coeff;
			APROC_Audio_Buffer_RX1_Q[i] *= cos_result * compensation_coeff;

			gen_position_rx1 += freq_diff / (float32_t)TRX_SAMPLERATE;
			while (gen_position_rx1 >= 1.0f) {
				gen_position_rx1 -= 1.0f;
			}
		}
	}
#if HRDW_HAS_DUAL_RX
	else {
		for (uint16_t i = 0; i < size; i++) {
			float32_t sin_result;
			float32_t cos_result;
			fast_sin_cos((gen_position_rx2 * F_2PI), &sin_result, &cos_result);
			APROC_Audio_Buffer_RX2_I[i] *= sin_result * compensation_coeff;
			APROC_Audio_Buffer_RX2_Q[i] *= cos_result * compensation_coeff;

			gen_position_rx2 += freq_diff / (float32_t)TRX_SAMPLERATE;
			while (gen_position_rx2 >= 1.0f) {
				gen_position_rx2 -= 1.0f;
			}
		}
	}
#endif
}

static void doRX_DemodSAM(AUDIO_PROC_RX_NUM rx_id, float32_t *i_buffer, float32_t *q_buffer, float32_t *out_buffer_l, float32_t *out_buffer_r, int16_t blockSize, TRX_MODE mode) {
	// part of UHSDR project https://github.com/df8oe/UHSDR/blob/active-devel/mchf-eclipse/drivers/audio/audio_driver.c
	demod_sam_data_t *sam_data = &sam_data_rx1;
#if HRDW_HAS_DUAL_RX
	if (rx_id == AUDIO_RX2) {
		sam_data = &sam_data_rx2;
	}
#endif

	// sideband separation, these values never change
	static const demod_sam_const_t demod_sam_const = {
	    .c0 =
	        {
	            -0.328201924180698,
	            -0.744171491539427,
	            -0.923022915444215,
	            -0.978490468768238,
	            -0.994128272402075,
	            -0.998458978159551,
	            -0.999790306259206,
	        },

	    .c1 =
	        {
	            -0.0991227952747244,
	            -0.565619728761389,
	            -0.857467122550052,
	            -0.959123933111275,
	            -0.988739372718090,
	            -0.996959189310611,
	            -0.999282492800792,
	        },
	};

	// definitions and intializations for synchronous AM demodulation = SAM
	if (!sam_data->inited) {
		sam_data->inited = true;
		// pll
		sam_data->adb_sam_omega_min = -(2.0f * F_PI * SAM_omegaN / TRX_SAMPLERATE);
		sam_data->adb_sam_omega_max = (2.0f * F_PI * SAM_omegaN / TRX_SAMPLERATE);
		sam_data->adb_sam_g1 = (1.0f - expf(-2.0f * SAM_omegaN * SAM_zeta / TRX_SAMPLERATE));
		sam_data->adb_sam_g2 = (-sam_data->adb_sam_g1 + 2.0f * (1 - expf(-SAM_omegaN * SAM_zeta / TRX_SAMPLERATE) * cosf(SAM_omegaN / TRX_SAMPLERATE * sqrtf(1.0f - SAM_zeta * SAM_zeta))));
		// fade leveler
		float32_t tauR = 0.02f; // value emperically determined
		float32_t tauI = 1.4f;  // value emperically determined
		sam_data->adb_sam_mtauR = (expf(-1.0f / ((float32_t)TRX_SAMPLERATE * tauR)));
		sam_data->adb_sam_onem_mtauR = (1.0f - sam_data->adb_sam_mtauR);
		sam_data->adb_sam_mtauI = (expf(-1.0f / ((float32_t)TRX_SAMPLERATE * tauI)));
		sam_data->adb_sam_onem_mtauI = (1.0f - sam_data->adb_sam_mtauI);
	}
	// Wheatley 2011 cuteSDR & Warren Pratts WDSP, 2016
	for (int i = 0; i < blockSize; i++) {
		// NCO
		float32_t ai, bi, aq, bq;
		float32_t Sin, Cos;

		fast_sin_cos(sam_data->phs, &Sin, &Cos);

		ai = Cos * i_buffer[i];
		bi = Sin * i_buffer[i];
		aq = Cos * q_buffer[i];
		bq = Sin * q_buffer[i];

		float32_t corr[2] = {ai + bq, -bi + aq};

		sam_data->a[0] = sam_data->dsI;
		sam_data->b[0] = bi;
		sam_data->c[0] = sam_data->dsQ;
		sam_data->d[0] = aq;
		sam_data->dsI = ai;
		sam_data->dsQ = bq;

		for (int j = 0; j < SAM_PLL_HILBERT_STAGES; j++) {
			int k = 3 * j;
			sam_data->a[k + 3] = demod_sam_const.c0[j] * (sam_data->a[k] - sam_data->a[k + 5]) + sam_data->a[k + 2];
			sam_data->b[k + 3] = demod_sam_const.c1[j] * (sam_data->b[k] - sam_data->b[k + 5]) + sam_data->b[k + 2];
			sam_data->c[k + 3] = demod_sam_const.c0[j] * (sam_data->c[k] - sam_data->c[k + 5]) + sam_data->c[k + 2];
			sam_data->d[k + 3] = demod_sam_const.c1[j] * (sam_data->d[k] - sam_data->d[k + 5]) + sam_data->d[k + 2];
		}

		float32_t ai_ps = sam_data->a[SAM_OUT_IDX];
		float32_t bi_ps = sam_data->b[SAM_OUT_IDX];
		float32_t bq_ps = sam_data->c[SAM_OUT_IDX];
		float32_t aq_ps = sam_data->d[SAM_OUT_IDX];

		// make room for next sample
		for (int j = SAM_OUT_IDX + 2; j > 0; j--) {
			sam_data->a[j] = sam_data->a[j - 1];
			sam_data->b[j] = sam_data->b[j - 1];
			sam_data->c[j] = sam_data->c[j - 1];
			sam_data->d[j] = sam_data->d[j - 1];
		}

		// out
		out_buffer_l[i] = (ai_ps + bi_ps) - (aq_ps - bq_ps);
		out_buffer_r[i] = (ai_ps - bi_ps) + (aq_ps + bq_ps);

		if (mode == TRX_MODE_SAM_LSB) {
			out_buffer_r[i] = out_buffer_l[i];
		}
		if (mode == TRX_MODE_SAM_USB) {
			out_buffer_l[i] = out_buffer_r[i];
		}

		// fade leveler
		static float32_t dc27_l = 0;
		static float32_t dc27_r = 0;
		static float32_t dc_insert_l = {0};
		static float32_t dc_insert_r = {0};

		dc27_l = sam_data->adb_sam_mtauR * dc27_l + sam_data->adb_sam_onem_mtauR * out_buffer_l[i];
		dc27_r = sam_data->adb_sam_mtauR * dc27_r + sam_data->adb_sam_onem_mtauR * out_buffer_r[i];
		dc_insert_l = sam_data->adb_sam_mtauI * dc_insert_l + sam_data->adb_sam_onem_mtauI * corr[0];
		dc_insert_r = sam_data->adb_sam_mtauI * dc_insert_r + sam_data->adb_sam_onem_mtauI * corr[0];
		out_buffer_l[i] = out_buffer_l[i] + dc_insert_l - dc27_l;
		out_buffer_r[i] = out_buffer_r[i] + dc_insert_r - dc27_r;

		// determine phase error
		float32_t phzerror;
		arm_atan2_f32(corr[1], corr[0], &phzerror);

		float32_t del_out = sam_data->fil_out;
		// correct frequency 1st step
		sam_data->omega2 = sam_data->omega2 + sam_data->adb_sam_g2 * phzerror;
		if (sam_data->omega2 < sam_data->adb_sam_omega_min) {
			sam_data->omega2 = sam_data->adb_sam_omega_min;
		} else if (sam_data->omega2 > sam_data->adb_sam_omega_max) {
			sam_data->omega2 = sam_data->adb_sam_omega_max;
		}
		// correct frequency 2nd step
		sam_data->fil_out = sam_data->adb_sam_g1 * phzerror + sam_data->omega2;
		sam_data->phs = sam_data->phs + del_out;

		// wrap round 2PI, modulus
		while (sam_data->phs >= 2.0f * F_PI) {
			sam_data->phs -= (2.0f * F_PI);
		}
		while (sam_data->phs < 0.0f) {
			sam_data->phs += (2.0f * F_PI);
		}
	}

	sam_data->count++;
	if (sam_data->count > 100) // to display the exact carrier frequency that the PLL is tuned to
	{
		float32_t carrier = 0.1f * (sam_data->omega2 * (float32_t)TRX_SAMPLERATE) / (2.0f * F_PI);
		carrier = carrier + 0.9f * sam_data->lowpass;
		SAM_Carrier_offset = carrier;
		println("SAM_Carrier_offset ", (double)SAM_Carrier_offset);
		sam_data->count = 0;
		sam_data->lowpass = carrier;
	}
}

void APROC_doVOX(void) {
	static bool VOX_applied = false;

	if (!TRX.VOX && VOX_applied) {
		TRX_ptt_soft = false;
		VOX_applied = false;
	}

	if (!TRX.VOX || !TRX_Inited || SYSMENU_FT8_DECODER_opened) {
		return;
	}

	uint32_t current_tick = HAL_GetTick();
	if (current_tick <= TRX.VOX_TIMEOUT) {
		return;
	}

	static uint32_t VOX_LastSignalTime = 0;

#ifndef STM32F407xx
	q31_t rms = 0;
	arm_rms_q31(CODEC_Audio_Buffer_TX, CODEC_AUDIO_BUFFER_HALF_SIZE, &rms);
#else
	float32_t rms = 0;
	for (uint32_t i = 0; i < CODEC_AUDIO_BUFFER_HALF_SIZE; i++) {
		float32_t sample = convertToSPIBigEndian(CODEC_Audio_Buffer_TX[i]);
		rms += sample * sample;
	}
	rms = sqrtf(rms / (float32_t)CODEC_AUDIO_BUFFER_HALF_SIZE);
#endif

	float32_t full_scale_rate = (float32_t)rms / CODEC_BITS_FULL_SCALE;
	float32_t VOX_dbFS = rate2dbV(full_scale_rate);
	// println("VOX dbFS: ", VOX_dbFS);

	if (VOX_dbFS > TRX.VOX_THRESHOLD) {
		VOX_LastSignalTime = current_tick;
	}

	uint32_t vox_timeout_now = current_tick - VOX_LastSignalTime;

	if (!VOX_applied && (vox_timeout_now < TRX.VOX_TIMEOUT)) {
		TRX_ptt_soft = true;
		VOX_applied = true;
	}

	if (VOX_applied && (vox_timeout_now >= TRX.VOX_TIMEOUT)) {
		TRX_ptt_soft = false;
		VOX_applied = false;
	}
}

static void APROC_ProcessCodecMuting(void) {
	if (CODEC_Muting) {
		for (uint32_t pos = 0; pos < AUDIO_BUFFER_HALF_SIZE; pos++) {
			APROC_AudioBuffer_out[pos * 2] = 0;     // left channel
			APROC_AudioBuffer_out[pos * 2 + 1] = 0; // right channel
		}
	}
	if (TRX.RX_AUDIO_MODE == RX_AUDIO_MODE_LEFT) {
		for (uint32_t pos = 0; pos < AUDIO_BUFFER_HALF_SIZE; pos++) {
			APROC_AudioBuffer_out[pos * 2 + 1] = 0; // right channel
		}
	}
	if (TRX.RX_AUDIO_MODE == RX_AUDIO_MODE_RIGHT) {
		for (uint32_t pos = 0; pos < AUDIO_BUFFER_HALF_SIZE; pos++) {
			APROC_AudioBuffer_out[pos * 2] = 0; // left channel
		}
	}
}
