donatukas/Volf-TRX/STM32/Src/filemanager.c

#include "hardware.h"
#if HRDW_HAS_SD

#include "filemanager.h"
#include "lcd.h"
#include "lcd_driver.h"
#include "sd.h"
#include "system_menu.h"
#include "vocoder.h"
#include "wifi.h"

static bool first_start = true;
static uint16_t current_index = 0;
static FILEMANAGER_ACTION current_dialog_action = FILMAN_ACT_CANCEL;

SRAM char FILEMANAGER_CurrentPath[128] = "";
SRAM char FILEMANAGER_LISTING[FILEMANAGER_LISTING_MAX_FILES][FILEMANAGER_LISTING_MAX_FILELEN + 1] = {""};
uint16_t FILEMANAGER_files_startindex = 0;
uint16_t FILEMANAGER_files_count = 0;
bool FILEMANAGER_dialog_opened = false;
uint16_t FILEMANAGER_dialog_button_index = 0;

static bool downloaded_fpga_fw = false;
static bool downloaded_fpga_crc = false;
static bool downloaded_stm_fw = false;
static bool downloaded_stm_crc = false;
static bool start_rec_cqmessage = false;

static void FILEMANAGER_Refresh(void);
static void FILEMANAGER_OpenDialog(void);
static void FILEMANAGER_DialogAction(void);
static unsigned char *FILEMANAGER_createBitmapFileHeader(int height, int stride);
static unsigned char *FILEMANAGER_createBitmapInfoHeader(int height, int width);

#ifdef LCD_SMALL_INTERFACE
#define margin_bottom 10
#define font_size 1
#else
#define margin_bottom 24
#define font_size 2
#endif

void FILEMANAGER_Draw(bool redraw) {
	if (first_start) {
		first_start = false;
		FILEMANAGER_files_startindex = 0;
		current_index = 0;
		strcpy(FILEMANAGER_CurrentPath, "");
		FILEMANAGER_Refresh();
		return;
	}
	if (redraw) {
		LCDDriver_Fill(BG_COLOR);
		uint16_t cur_y = 5;

		LCDDriver_printText("SD CARD FILE MANAGER", 5, cur_y, COLOR_GREEN, BG_COLOR, font_size);
		cur_y += margin_bottom;
		if (strlen(FILEMANAGER_CurrentPath) == 0) {
			LCDDriver_printText("/", 5, cur_y, FG_COLOR, BG_COLOR, font_size);
		} else {
			LCDDriver_printText(FILEMANAGER_CurrentPath, 5, cur_y, FG_COLOR, BG_COLOR, font_size);
		}
		cur_y += margin_bottom;
		if (FILEMANAGER_files_startindex == 0) {
			LCDDriver_printText("..", 5, cur_y, FG_COLOR, BG_COLOR, font_size);
		}
		cur_y += LAYOUT->SYSMENU_ITEM_HEIGHT;

		for (uint16_t file_id = 0; file_id < FILEMANAGER_LISTING_ITEMS_ON_PAGE; file_id++) {
			LCDDriver_printText(FILEMANAGER_LISTING[file_id], 5, cur_y, FG_COLOR, BG_COLOR, font_size);
			cur_y += LAYOUT->SYSMENU_ITEM_HEIGHT;

			// CQ recorder
			if (start_rec_cqmessage && strcmp(FILEMANAGER_LISTING[file_id], SD_CQ_MESSAGE_FILE) == 0) {
				current_index = file_id + 1;
				FILEMANAGER_dialog_opened = true;
				start_rec_cqmessage = false;
			}
		}

		LCD_UpdateQuery.SystemMenuRedraw = false;
	}

	LCDDriver_drawFastHLine(0, 5 + margin_bottom + margin_bottom + LAYOUT->SYSMENU_ITEM_HEIGHT + (current_index * LAYOUT->SYSMENU_ITEM_HEIGHT) - 1, LAYOUT->SYSMENU_W, FG_COLOR);

	if (FILEMANAGER_dialog_opened) {
		FILEMANAGER_OpenDialog();
	}

	LCD_UpdateQuery.SystemMenu = false;
}

void FILEMANAGER_EventRotate(int8_t direction) {
	if (FILEMANAGER_dialog_opened) {
		FILEMANAGER_DialogAction();
		return;
	}

	if (current_index == 0) // go up
	{
		if (strcmp(FILEMANAGER_CurrentPath, "") == 0) // root
		{
			SYSMENU_eventCloseSystemMenu();
		} else // inner folder
		{
			char *istr = strrchr(FILEMANAGER_CurrentPath, '/');
			*istr = 0;
			FILEMANAGER_files_startindex = 0;
			current_index = 0;
			FILEMANAGER_Refresh();
		}
	} else {
		char *istr = strstr(FILEMANAGER_LISTING[current_index - 1], " [DIR] ");
		if (istr != NULL && ((strlen(istr + 7) + 1) < sizeof(FILEMANAGER_CurrentPath))) // is directory
		{
			strcat(FILEMANAGER_CurrentPath, "/");
			strcat(FILEMANAGER_CurrentPath, istr + 7);
			FILEMANAGER_files_startindex = 0;
			current_index = 0;
			FILEMANAGER_Refresh();
		} else // is file
		{
			FILEMANAGER_dialog_button_index = 0;
			FILEMANAGER_OpenDialog();
		}
	}
}

void FILEMANAGER_EventSecondaryRotate(int8_t direction) {
	if (FILEMANAGER_dialog_opened) {
		if (FILEMANAGER_dialog_button_index > 0 || direction > 0) {
			FILEMANAGER_dialog_button_index += direction;
		}
		FILEMANAGER_OpenDialog();
		return;
	}

	LCDDriver_drawFastHLine(0, 5 + margin_bottom + margin_bottom + LAYOUT->SYSMENU_ITEM_HEIGHT + (current_index * LAYOUT->SYSMENU_ITEM_HEIGHT) - 1, LAYOUT->SYSMENU_W, BG_COLOR);
	if (direction > 0 || current_index > 0) {
		current_index += direction;
	}

	int16_t real_file_index = FILEMANAGER_files_startindex + current_index - 1;

	// limit
	if (real_file_index >= FILEMANAGER_files_count) {
		current_index--;
	}

	// list down
	if (current_index > FILEMANAGER_LISTING_ITEMS_ON_PAGE && real_file_index < FILEMANAGER_files_count) {
		FILEMANAGER_files_startindex += FILEMANAGER_LISTING_ITEMS_ON_PAGE;
		current_index = 1;
		FILEMANAGER_Refresh();
	}

	// list up
	if (FILEMANAGER_files_startindex > 0 && current_index == 0) {
		FILEMANAGER_files_startindex -= FILEMANAGER_LISTING_ITEMS_ON_PAGE;
		current_index = FILEMANAGER_LISTING_ITEMS_ON_PAGE;
		FILEMANAGER_Refresh();
	}

	LCD_UpdateQuery.SystemMenu = true;
}

void FILEMANAGER_Closing(void) {
	first_start = true;
	current_index = 0;
	FILEMANAGER_dialog_opened = false;
	FILEMANAGER_dialog_button_index = 0;
}

static void FILEMANAGER_Refresh(void) {
	if (!SD_doCommand(SDCOMM_LIST_DIRECTORY, false)) {
		SYSMENU_eventCloseSystemMenu();
	}

	LCD_UpdateQuery.SystemMenuRedraw = true;
}

void FILEMANAGER_StartRecCQWav(void) {
	if (!SD_doCommand(SDCOMM_CREATE_CQ_MESSAGE_FILE, false)) {
		SYSMENU_eventCloseSystemMenu();
	}

	start_rec_cqmessage = true;
	first_start = true;
}

static void FILEMANAGER_OpenDialog(void) {
	FILEMANAGER_dialog_opened = true;
	bool allow_play_wav = false;
	bool allow_cq_rec = false;
	bool allow_flash_bin = false;
	bool allow_flash_jic = false;
	uint8_t max_buttons_index = 1; // cancel+delete
	char ctmp[64] = {0};

	// check play wav
	char *istr = strstr(FILEMANAGER_LISTING[current_index - 1], ".wav");
	if (istr != NULL) {
		max_buttons_index += 2;
		allow_play_wav = true;
	}
	// check cq message rec wav
	istr = strstr(FILEMANAGER_LISTING[current_index - 1], SD_CQ_MESSAGE_FILE);
	if (istr != NULL) {
		max_buttons_index++;
		allow_cq_rec = true;
	}
	// check flash stm32 bin
	istr = strstr(FILEMANAGER_LISTING[current_index - 1], ".bin");
	if (istr != NULL) {
		max_buttons_index++;
		allow_flash_bin = true;
	}
	// check flash fpga jic
	istr = strstr(FILEMANAGER_LISTING[current_index - 1], ".jic");
	if (istr != NULL) {
		max_buttons_index++;
		allow_flash_jic = true;
	}

	if (FILEMANAGER_dialog_button_index > max_buttons_index) {
		FILEMANAGER_dialog_button_index = max_buttons_index;
	}

#ifdef LCD_SMALL_INTERFACE
#define margin 10
#else
#define margin 30
#endif

	// frame
	LCDDriver_Fill_RectXY(margin, margin, LCD_WIDTH - margin, LCD_HEIGHT - margin, BG_COLOR);
	LCDDriver_drawRectXY(margin, margin, LCD_WIDTH - margin, LCD_HEIGHT - margin, FG_COLOR);
	// buttons
	uint16_t button_y = margin * 2;
	uint16_t button_x = margin * 2;
	uint16_t button_w = LCD_WIDTH - margin * 2 - button_x;
	uint16_t button_h = margin;
	uint16_t bounds_x, bounds_y, bounds_w, bounds_h;
	uint8_t print_index = 0;
	bool button_active = false;
	// back
	button_active = (FILEMANAGER_dialog_button_index == print_index);
	LCDDriver_Fill_RectXY(button_x, button_y, LCD_WIDTH - margin * 2, button_y + button_h, button_active ? FG_COLOR : BG_COLOR);
	LCDDriver_drawRectXY(button_x, button_y, LCD_WIDTH - margin * 2, button_y + button_h, button_active ? BG_COLOR : FG_COLOR);
#ifdef LCD_SMALL_INTERFACE
	LCDDriver_getTextBounds("Cancel", button_x, button_y, &bounds_x, &bounds_y, &bounds_w, &bounds_h, 1);
	LCDDriver_printText("Cancel", button_x + button_w / 2 - bounds_w / 2, button_y + 1, button_active ? BG_COLOR : FG_COLOR, button_active ? FG_COLOR : BG_COLOR, 1);
#else
	LCDDriver_getTextBoundsFont("Cancel", button_x, button_y, &bounds_x, &bounds_y, &bounds_w, &bounds_h, &FreeSans9pt7b);
	LCDDriver_printTextFont("Cancel", button_x + button_w / 2 - bounds_w / 2, button_y + button_h / 2 + bounds_h / 2, button_active ? BG_COLOR : FG_COLOR, button_active ? FG_COLOR : BG_COLOR,
	                        &FreeSans9pt7b);
#endif
	button_y += button_h + margin;
	if (button_active) {
		current_dialog_action = FILMAN_ACT_CANCEL;
	}
	print_index++;
	// play wav
	if (allow_play_wav) {
		// Play Localy
		button_active = (FILEMANAGER_dialog_button_index == print_index);
		LCDDriver_Fill_RectXY(button_x, button_y, LCD_WIDTH - margin * 2, button_y + button_h, button_active ? FG_COLOR : BG_COLOR);
		LCDDriver_drawRectXY(button_x, button_y, LCD_WIDTH - margin * 2, button_y + button_h, button_active ? BG_COLOR : FG_COLOR);
		if (!SD_PlayInProcess || SD_PlayCQMessageInProcess) {
#ifdef LCD_SMALL_INTERFACE
			LCDDriver_getTextBounds("Play WAV", button_x, button_y, &bounds_x, &bounds_y, &bounds_w, &bounds_h, 1);
			LCDDriver_printText("Play WAV", button_x + button_w / 2 - bounds_w / 2, button_y + 1, button_active ? BG_COLOR : FG_COLOR, button_active ? FG_COLOR : BG_COLOR, 1);
#else
			LCDDriver_getTextBoundsFont("Play WAV", button_x, button_y, &bounds_x, &bounds_y, &bounds_w, &bounds_h, &FreeSans9pt7b);
			LCDDriver_printTextFont("Play WAV", button_x + button_w / 2 - bounds_w / 2, button_y + button_h / 2 + bounds_h / 2, button_active ? BG_COLOR : FG_COLOR,
			                        button_active ? FG_COLOR : BG_COLOR, &FreeSans9pt7b);
#endif
		} else {
#ifdef LCD_SMALL_INTERFACE
			sprintf(ctmp, "P %u/%u sec", VOCODER_SecondsElapsed, VOCODER_SecondsTotal);
			LCDDriver_getTextBounds(ctmp, button_x, button_y, &bounds_x, &bounds_y, &bounds_w, &bounds_h, 1);
			LCDDriver_printText(ctmp, button_x + button_w / 2 - bounds_w / 2, button_y + 1, button_active ? BG_COLOR : FG_COLOR, button_active ? FG_COLOR : BG_COLOR, 1);
#else
			sprintf(ctmp, "Playing %u/%u sec", VOCODER_SecondsElapsed, VOCODER_SecondsTotal);
			LCDDriver_getTextBoundsFont(ctmp, button_x, button_y, &bounds_x, &bounds_y, &bounds_w, &bounds_h, &FreeSans9pt7b);
			LCDDriver_printTextFont(ctmp, button_x + button_w / 2 - bounds_w / 2, button_y + button_h / 2 + bounds_h / 2, button_active ? BG_COLOR : FG_COLOR, button_active ? FG_COLOR : BG_COLOR,
			                        &FreeSans9pt7b);
#endif
		}
		button_y += button_h + margin;
		if (button_active) {
			current_dialog_action = FILMAN_ACT_PLAY_WAV;
		}
		print_index++;

		// Tansmit WAV
		button_active = (FILEMANAGER_dialog_button_index == print_index);
		LCDDriver_Fill_RectXY(button_x, button_y, LCD_WIDTH - margin * 2, button_y + button_h, button_active ? FG_COLOR : BG_COLOR);
		LCDDriver_drawRectXY(button_x, button_y, LCD_WIDTH - margin * 2, button_y + button_h, button_active ? BG_COLOR : FG_COLOR);
		if (!SD_PlayCQMessageInProcess) {
#ifdef LCD_SMALL_INTERFACE
			LCDDriver_getTextBounds("Transmit WAV", button_x, button_y, &bounds_x, &bounds_y, &bounds_w, &bounds_h, 1);
			LCDDriver_printText("Transmit WAV", button_x + button_w / 2 - bounds_w / 2, button_y + 1, button_active ? BG_COLOR : FG_COLOR, button_active ? FG_COLOR : BG_COLOR, 1);
#else
			LCDDriver_getTextBoundsFont("Transmit WAV", button_x, button_y, &bounds_x, &bounds_y, &bounds_w, &bounds_h, &FreeSans9pt7b);
			LCDDriver_printTextFont("Transmit WAV", button_x + button_w / 2 - bounds_w / 2, button_y + button_h / 2 + bounds_h / 2, button_active ? BG_COLOR : FG_COLOR,
			                        button_active ? FG_COLOR : BG_COLOR, &FreeSans9pt7b);
#endif
		} else {
#ifdef LCD_SMALL_INTERFACE
			sprintf(ctmp, "T %u/%u sec", VOCODER_SecondsElapsed, VOCODER_SecondsTotal);
			LCDDriver_getTextBounds(ctmp, button_x, button_y, &bounds_x, &bounds_y, &bounds_w, &bounds_h, 1);
			LCDDriver_printText(ctmp, button_x + button_w / 2 - bounds_w / 2, button_y + 1, button_active ? BG_COLOR : FG_COLOR, button_active ? FG_COLOR : BG_COLOR, 1);
#else
			sprintf(ctmp, "TXing %u/%u sec", VOCODER_SecondsElapsed, VOCODER_SecondsTotal);
			LCDDriver_getTextBoundsFont(ctmp, button_x, button_y, &bounds_x, &bounds_y, &bounds_w, &bounds_h, &FreeSans9pt7b);
			LCDDriver_printTextFont(ctmp, button_x + button_w / 2 - bounds_w / 2, button_y + button_h / 2 + bounds_h / 2, button_active ? BG_COLOR : FG_COLOR, button_active ? FG_COLOR : BG_COLOR,
			                        &FreeSans9pt7b);
#endif
		}
		button_y += button_h + margin;
		if (button_active) {
			current_dialog_action = FILMAN_ACT_TRANSMIT_WAV;
		}
		print_index++;
	}
	// rec cq message
	if (allow_cq_rec) {
		button_active = (FILEMANAGER_dialog_button_index == print_index);
		LCDDriver_Fill_RectXY(button_x, button_y, LCD_WIDTH - margin * 2, button_y + button_h, button_active ? FG_COLOR : BG_COLOR);
		LCDDriver_drawRectXY(button_x, button_y, LCD_WIDTH - margin * 2, button_y + button_h, button_active ? BG_COLOR : FG_COLOR);
		if (!SD_RecordInProcess) {
#ifdef LCD_SMALL_INTERFACE
			LCDDriver_getTextBounds("Record CQ message", button_x, button_y, &bounds_x, &bounds_y, &bounds_w, &bounds_h, 1);
			LCDDriver_printText("Record CQ message", button_x + button_w / 2 - bounds_w / 2, button_y + 1, button_active ? BG_COLOR : FG_COLOR, button_active ? FG_COLOR : BG_COLOR, 1);
#else
			LCDDriver_getTextBoundsFont("Record CQ message", button_x, button_y, &bounds_x, &bounds_y, &bounds_w, &bounds_h, &FreeSans9pt7b);
			LCDDriver_printTextFont("Record CQ message", button_x + button_w / 2 - bounds_w / 2, button_y + button_h / 2 + bounds_h / 2, button_active ? BG_COLOR : FG_COLOR,
			                        button_active ? FG_COLOR : BG_COLOR, &FreeSans9pt7b);
#endif
		} else {
#ifdef LCD_SMALL_INTERFACE
			sprintf(ctmp, "REC %u sec", VOCODER_SecondsElapsed);
			LCDDriver_getTextBounds(ctmp, button_x, button_y, &bounds_x, &bounds_y, &bounds_w, &bounds_h, 1);
			LCDDriver_printText(ctmp, button_x + button_w / 2 - bounds_w / 2, button_y + 1, button_active ? BG_COLOR : FG_COLOR, button_active ? FG_COLOR : BG_COLOR, 1);
#else
			sprintf(ctmp, "Recording %u sec", VOCODER_SecondsElapsed);
			LCDDriver_getTextBoundsFont(ctmp, button_x, button_y, &bounds_x, &bounds_y, &bounds_w, &bounds_h, &FreeSans9pt7b);
			LCDDriver_printTextFont(ctmp, button_x + button_w / 2 - bounds_w / 2, button_y + button_h / 2 + bounds_h / 2, button_active ? BG_COLOR : FG_COLOR, button_active ? FG_COLOR : BG_COLOR,
			                        &FreeSans9pt7b);
#endif
		}
		button_y += button_h + margin;
		if (button_active) {
			current_dialog_action = FILMAN_ACT_REC_CQ_WAV;
		}
		print_index++;
	}
	// flash bin
	if (allow_flash_bin) {
		button_active = (FILEMANAGER_dialog_button_index == print_index);
		LCDDriver_Fill_RectXY(button_x, button_y, LCD_WIDTH - margin * 2, button_y + button_h, button_active ? FG_COLOR : BG_COLOR);
		LCDDriver_drawRectXY(button_x, button_y, LCD_WIDTH - margin * 2, button_y + button_h, button_active ? BG_COLOR : FG_COLOR);
#ifdef LCD_SMALL_INTERFACE
		LCDDriver_getTextBounds("Flash STM32 firmware", button_x, button_y, &bounds_x, &bounds_y, &bounds_w, &bounds_h, 1);
		LCDDriver_printText("Flash STM32 firmware", button_x + button_w / 2 - bounds_w / 2, button_y + 1, button_active ? BG_COLOR : FG_COLOR, button_active ? FG_COLOR : BG_COLOR, 1);
#else
		LCDDriver_getTextBoundsFont("Flash STM32 firmware", button_x, button_y, &bounds_x, &bounds_y, &bounds_w, &bounds_h, &FreeSans9pt7b);
		LCDDriver_printTextFont("Flash STM32 firmware", button_x + button_w / 2 - bounds_w / 2, button_y + button_h / 2 + bounds_h / 2, button_active ? BG_COLOR : FG_COLOR,
		                        button_active ? FG_COLOR : BG_COLOR, &FreeSans9pt7b);
#endif

		button_y += button_h + margin;
		if (button_active) {
			current_dialog_action = FILMAN_ACT_FLASHBIN;
		}
		print_index++;
	}
	// flash jic
	if (allow_flash_jic) {
		button_active = (FILEMANAGER_dialog_button_index == print_index);
		LCDDriver_Fill_RectXY(button_x, button_y, LCD_WIDTH - margin * 2, button_y + button_h, button_active ? FG_COLOR : BG_COLOR);
		LCDDriver_drawRectXY(button_x, button_y, LCD_WIDTH - margin * 2, button_y + button_h, button_active ? BG_COLOR : FG_COLOR);
#ifdef LCD_SMALL_INTERFACE
		LCDDriver_getTextBounds("Flash FPGA firmware", button_x, button_y, &bounds_x, &bounds_y, &bounds_w, &bounds_h, 1);
		LCDDriver_printText("Flash FPGA firmware", button_x + button_w / 2 - bounds_w / 2, button_y + 1, button_active ? BG_COLOR : FG_COLOR, button_active ? FG_COLOR : BG_COLOR, 1);
#else
		LCDDriver_getTextBoundsFont("Flash FPGA firmware", button_x, button_y, &bounds_x, &bounds_y, &bounds_w, &bounds_h, &FreeSans9pt7b);
		LCDDriver_printTextFont("Flash FPGA firmware", button_x + button_w / 2 - bounds_w / 2, button_y + button_h / 2 + bounds_h / 2, button_active ? BG_COLOR : FG_COLOR,
		                        button_active ? FG_COLOR : BG_COLOR, &FreeSans9pt7b);
#endif

		button_y += button_h + margin;
		if (button_active) {
			current_dialog_action = FILMAN_ACT_FLASHJIC;
		}
		print_index++;
	}
	// delete
	button_active = (FILEMANAGER_dialog_button_index == print_index);
	LCDDriver_Fill_RectXY(button_x, button_y, LCD_WIDTH - margin * 2, button_y + button_h, button_active ? FG_COLOR : BG_COLOR);
	LCDDriver_drawRectXY(button_x, button_y, LCD_WIDTH - margin * 2, button_y + button_h, button_active ? BG_COLOR : FG_COLOR);
#ifdef LCD_SMALL_INTERFACE
	LCDDriver_getTextBounds("Delete", button_x, button_y, &bounds_x, &bounds_y, &bounds_w, &bounds_h, 1);
	LCDDriver_printText("Delete", button_x + button_w / 2 - bounds_w / 2, button_y + 1, button_active ? BG_COLOR : FG_COLOR, button_active ? FG_COLOR : BG_COLOR, 1);
#else
	LCDDriver_getTextBoundsFont("Delete", button_x, button_y, &bounds_x, &bounds_y, &bounds_w, &bounds_h, &FreeSans9pt7b);
	LCDDriver_printTextFont("Delete", button_x + button_w / 2 - bounds_w / 2, button_y + button_h / 2 + bounds_h / 2, button_active ? BG_COLOR : FG_COLOR, button_active ? FG_COLOR : BG_COLOR,
	                        &FreeSans9pt7b);
#endif

	button_y += button_h + margin;
	if (button_active) {
		current_dialog_action = FILMAN_ACT_DELETE;
	}
	print_index++;
}

static void FILEMANAGER_DialogAction(void) {
	if (SD_PlayInProcess) {
		SD_NeedStopPlay = true;
	}

	if (current_dialog_action == FILMAN_ACT_CANCEL) // back
	{
		FILEMANAGER_dialog_opened = false;
		FILEMANAGER_Refresh();
		return;
	}
	if (current_dialog_action == FILMAN_ACT_DELETE) // delete
	{
		if (!SD_CommandInProcess) {
			dma_memset(SD_workbuffer_A, 0, sizeof(SD_workbuffer_A));
			if (strlen(FILEMANAGER_CurrentPath) > 0) {
				strcat((char *)SD_workbuffer_A, FILEMANAGER_CurrentPath);
				strcat((char *)SD_workbuffer_A, "/");
			}
			strcat((char *)SD_workbuffer_A, FILEMANAGER_LISTING[current_index - 1]);
			FILEMANAGER_dialog_opened = false;
			current_index--;
			SD_doCommand(SDCOMM_DELETE_FILE, false);
		}
		return;
	}
	if (current_dialog_action == FILMAN_ACT_PLAY_WAV) // play WAV Localy
	{
		if (SD_PlayInProcess) {
			SD_NeedStopPlay = true;
			return;
		}
		if (SD_RecordInProcess) {
			SD_NeedStopRecord = true;
			return;
		}

		println("Play WAV started");
		dma_memset(SD_workbuffer_A, 0, sizeof(SD_workbuffer_A));
		if (strlen(FILEMANAGER_CurrentPath) > 0) {
			strcat((char *)SD_workbuffer_A, FILEMANAGER_CurrentPath);
			strcat((char *)SD_workbuffer_A, "/");
		}
		strcat((char *)SD_workbuffer_A, FILEMANAGER_LISTING[current_index - 1]);
		SD_doCommand(SDCOMM_START_PLAY, false);
		return;
	}
	if (current_dialog_action == FILMAN_ACT_TRANSMIT_WAV) // Transmit WAV
	{
		if (SD_PlayInProcess) {
			SD_NeedStopPlay = true;
			return;
		}
		if (SD_RecordInProcess) {
			SD_NeedStopRecord = true;
			return;
		}
		if (SD_PlayCQMessageInProcess) {
			SD_NeedStopPlay = true;
			return;
		}

		println("Transmit WAV started");

		// go tx
		TRX_ptt_soft = true;
		TRX_ptt_change();

		// start play cq message
		SD_PlayCQMessageInProcess = true;

		dma_memset(SD_workbuffer_A, 0, sizeof(SD_workbuffer_A));
		if (strlen(FILEMANAGER_CurrentPath) > 0) {
			strcat((char *)SD_workbuffer_A, FILEMANAGER_CurrentPath);
			strcat((char *)SD_workbuffer_A, "/");
		}
		strcat((char *)SD_workbuffer_A, FILEMANAGER_LISTING[current_index - 1]);
		SD_doCommand(SDCOMM_START_PLAY, false);
		return;
	}
	if (current_dialog_action == FILMAN_ACT_REC_CQ_WAV) // record CQ message
	{

		if (SD_RecordInProcess) {
			SD_NeedStopRecord = true;
			return;
		}

		println("CQ message recorder started");
		dma_memset(SD_workbuffer_A, 0, sizeof(SD_workbuffer_A));
		if (strlen(FILEMANAGER_CurrentPath) > 0) {
			strcat((char *)SD_workbuffer_A, FILEMANAGER_CurrentPath);
			strcat((char *)SD_workbuffer_A, "/");
		}
		strcat((char *)SD_workbuffer_A, FILEMANAGER_LISTING[current_index - 1]);
		SD_RecordingCQmessage = true;
		rec_cqmessage_old_mode = CurrentVFO->Mode;
		TRX_setMode(TRX_MODE_LOOPBACK, CurrentVFO);
		SD_RecordInProcess = true;
		LCD_UpdateQuery.SystemMenuRedraw = true;
		return;
	}
	if (current_dialog_action == FILMAN_ACT_FLASHBIN) // flash stm32 bin firmware
	{
		println("[FLASH] BIN flashing started");
		TRX.Mute = true;
		dma_memset(SD_workbuffer_A, 0, sizeof(SD_workbuffer_A));
		if (strlen(FILEMANAGER_CurrentPath) > 0) {
			strcat((char *)SD_workbuffer_A, FILEMANAGER_CurrentPath);
			strcat((char *)SD_workbuffer_A, "/");
		}
		strcat((char *)SD_workbuffer_A, FILEMANAGER_LISTING[current_index - 1]);
		SD_doCommand(SDCOMM_FLASH_BIN, false);
		return;
	}
	if (current_dialog_action == FILMAN_ACT_FLASHJIC) // flash fpga jic firmware
	{
		println("[FLASH] JIC flashing started");
		TRX.Mute = true;
		dma_memset(SD_workbuffer_A, 0, sizeof(SD_workbuffer_A));
		if (strlen(FILEMANAGER_CurrentPath) > 0) {
			strcat((char *)SD_workbuffer_A, FILEMANAGER_CurrentPath);
			strcat((char *)SD_workbuffer_A, "/");
		}
		strcat((char *)SD_workbuffer_A, FILEMANAGER_LISTING[current_index - 1]);
		SD_doCommand(SDCOMM_FLASH_JIC, false);
		return;
	}
}

void FILEMANAGER_OTAUpdate_reset(void) {
	sysmenu_ota_opened_state = 0;
	sysmenu_ota_opened = false;
	WIFI_NewFW_checked = false;
	downloaded_fpga_fw = false;
	downloaded_fpga_crc = false;
	downloaded_stm_fw = false;
	downloaded_stm_crc = false;
}
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
