donatukas/Volf-TRX/STM32/Src/sd.c

#include "hardware.h"
#if HRDW_HAS_SD

#include "INA226_PWR_monitor.h"
#include "audio_filters.h"
#include "fatfs.h"
#include "filemanager.h"
#include "fpga.h"
#include "functions.h"
#include "lcd.h"
#include "main.h"
#include "satellite.h"
#include "sd.h"
#include "system_menu.h"
#include "user_diskio.h"
#include "vocoder.h"

SRAM FATFS SDFatFs = {0};
sd_info_ptr sdinfo = {
    .type = 0,
    .SECTOR_COUNT = 0,
    .BLOCK_SIZE = 512,
    .CAPACITY = 0,
};
bool SD_RecordInProcess = false;
bool SD_RecordingCQmessage = false;
TRX_MODE rec_cqmessage_old_mode;
bool SD_PlayInProcess = false;
bool SD_PlayCQMessageInProcess = false;
bool SD_CommandInProcess = false;
bool SD_underrun = false;
bool SD_NeedStopRecord = false;
bool SD_NeedStopPlay = false;
bool SD_Play_Buffer_Ready = false;
uint32_t SD_Play_Buffer_Size = false;
uint32_t SD_RecordBufferIndex = 0;
bool SD_Present = false;
bool SD_BusyByUSB = false;
bool SD_USBCardReader = false;
uint32_t SD_Present_tryTime = 0;
bool SD_Mounted = false;
static SD_COMMAND SD_currentCommand = SDCOMM_IDLE;
uint32_t SDCOMM_WRITE_TO_FILE_partsize = 0;
void (*SDCOMM_WRITE_TO_FILE_callback)(void);
void (*SDCOMM_GET_LINES_COUNT_callback)(uint32_t count);

SRAM FIL File = {0};
SRAM static FILINFO fileInfo = {0};
SRAM static DIR dir = {0};
SRAM BYTE SD_workbuffer_A[FF_MAX_SS] = {0};
SRAM BYTE SD_workbuffer_B[FF_MAX_SS] = {0};
SRAM static WAV_header wav_hdr = {0};
BYTE SD_workbuffer_current = false; // false - fill A save B, true - fill B save A

static void SDCOMM_CHECKSD_handler(void);
static void SDCOMM_LISTROOT_handler(void);
static void SDCOMM_MKFS_handler(void);
static void SDCOMM_EXPORT_SETTINGS_handler(void);
static void SDCOMM_EXPORT_CALIBRATIONS_handler(void);
static void SDCOMM_IMPORT_SETTINGS_handler(void);
static bool SD_WRITE_SETT_LINE(char *name, uint64_t *value, SystemMenuType type);
static bool SD_WRITE_SETT_STRING(char *name, char *value);
static void SDCOMM_PARSE_SETT_LINE(char *line);
static bool SDCOMM_CREATE_RECORD_FILE_handler(void);
static bool SDCOMM_OPEN_PLAY_FILE_handler(void);
static bool SDCOMM_WRITE_PACKET_RECORD_FILE_handler(void);
static void SDCOMM_LIST_DIRECTORY_handler(void);
static void SDCOMM_DELETE_FILE_handler(void);
static void SDCOMM_READ_PLAY_FILE_handler(void);
static void SDCOMM_WRITE_TO_FILE_handler(void);
static void SDCOMM_GET_LINES_COUNT_handler(void);
static bool SDCOMM_CREATE_RECORD_FILE_main(char *filename, bool audio_rec);
static bool SDCOMM_CREATE_CQ_MESSAGE_FILE_handler(void);
static void SDCOMM_IMPORT_TLE_SATNAMES_handler(void);
static void SDCOMM_IMPORT_TLE_INFO_handler(void);

bool SD_isIdle(void) {
	if (SD_currentCommand == SDCOMM_IDLE) {
		return true;
	} else {
		return false;
	}
}

bool SD_doCommand(SD_COMMAND command, bool force) {
	if (SD_Mounted) {
		if (SD_CommandInProcess && !force) {
			println("SD command ovverrun: ", SD_currentCommand);
			SD_underrun = true;
		} else {
			SD_CommandInProcess = true;
			SD_currentCommand = command;
			return true;
		}
		return false;
	} else {
		TRX_ptt_soft = false;
		TRX_ptt_change();

		if (LCD_systemMenuOpened) {
			LCD_showInfo("SD card not found", true);
		} else {
			LCD_showTooltip("SD card not found");
		}
		return false;
	}
}

void SD_Process(void) {
	if (SD_BusyByUSB) {
		return;
	}

	// Init card
	if (!SD_Present && (HAL_GetTick() - SD_Present_tryTime) > SD_CARD_SCAN_INTERVAL) {
		SD_Present_tryTime = HAL_GetTick();
		SD_Mounted = false;
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
