donatukas/Volf-TRX/STM32/Src/system_menu.c

#include "system_menu.h"
#include "FT8/FT8_main.h"
#include "INA226_PWR_monitor.h"
#include "agc.h"
#include "atu.h"
#include "audio_filters.h"
#include "auto_calibration.h"
#include "bands.h"
#include "bootloader.h"
#include "callsign.h"
#include "cw.h"
#include "filemanager.h"
#include "fonts.h"
#include "front_unit.h"
#include "functions.h"
#include "hardware.h"
#include "lcd.h"
#include "locator.h"
#include "noise_blanker.h"
#include "rf_unit.h"
#include "rtty_decoder.h"
#include "satellite.h"
#include "screen_layout.h"
#include "sd.h"
#include "self_test.h"
#include "settings.h"
#include "spec_analyzer.h"
#include "swr_analyzer.h"
#include "usbd_ua3reo.h"
#include "wifi.h"
#include "wspr.h"

static void SYSMENU_HANDL_TRX_BandMap(int8_t direction);
static void SYSMENU_HANDL_TRX_Beeper(int8_t direction);
static void SYSMENU_HANDL_TRX_ChannelMode(int8_t direction);
static void SYSMENU_HANDL_TRX_DEBUG_TYPE(int8_t direction);
static void SYSMENU_HANDL_TRX_ENC_ACCELERATE(int8_t direction);
static void SYSMENU_HANDL_TRX_FAST_STEP_Multiplier(int8_t direction);
static void SYSMENU_HANDL_TRX_ENC2_STEP_Multiplier(int8_t direction);
static void SYSMENU_HANDL_TRX_FRQ_STEP_CW_Hz(int8_t direction);
static void SYSMENU_HANDL_TRX_FRQ_STEP_SSB_Hz(int8_t direction);
static void SYSMENU_HANDL_TRX_FRQ_STEP_DIGI_Hz(int8_t direction);
static void SYSMENU_HANDL_TRX_FRQ_STEP_AM_Hz(int8_t direction);
static void SYSMENU_HANDL_TRX_FRQ_STEP_FM_Hz(int8_t direction);
static void SYSMENU_HANDL_TRX_FRQ_STEP_WFM_Hz(int8_t direction);
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
